scj009999/TLSR8269_SixChannel_Pulse_Generator/task-summary_2026-05-10.md

# 任务总结：TLSR8269 开源经颅脉冲治疗仪 - PCB打板前检查

**日期**：2026-05-10  
**任务**：原理图审查和打板前准备

---

## 一、原原理图问题（V1版本）

### 🔴 严重问题

1. **缺少医疗级隔离设计**
   - 患者电路与控制系统未隔离
   - 不符合医疗安全标准
   - 存在触电风险

2. **缺少限流保护电路**
   - 无硬件限流电阻
   - 短路时电流过大
   - 可能损坏芯片或伤害患者

3. **缺少过压/过流保护**
   - 无保险丝
   - 无TVS管
   - USB输入无保护

4. **电流检测精度不足**
   - 100Ω采样电阻方案精度差
   - 无法准确检测mA级电流

### 🟡 中等问题

5. **缺少急停按钮电路**
   - 无硬件急停设计
   - 仅软件急停不可靠

6. **缺少状态指示**
   - 无LED指示电源/运行/故障状态

7. **去耦电容不足**
   - 仅1个100nF电容
   - 每个VCC引脚都需要去耦

---

## 二、改进方案（V2版本）

### 新增关键电路

1. **隔离DC-DC电源**
   - B0505S-1W（3000V隔离）
   - 患者电路独立供电
   - 隔离地单点连接

2. **光耦隔离阵列**
   - PC817 × 6（5000V隔离）
   - 每通道独立隔离
   - 控制侧与患者侧完全隔离

3. **限流保护**
   - 每通道100Ω限流电阻
   - 最坏情况33mA（<50mA安全限值）
   - 光耦输入330Ω限流

4. **过压/过流保护**
   - 500mA自恢复保险丝
   - 5V TVS管（USB输入）
   - 电池保护板

5. **急停按钮电路**
   - 常闭型红色大按钮
   - 硬件中断触发
   - 10kΩ上拉电阻

6. **状态指示**
   - 绿色LED：电源指示
   - 红色LED：故障/急停
   - 黄色LED：治疗中

7. **电流检测改进**
   - INA219 I2C电流检测芯片
   - 精度±0.5%，分辨率12位
   - 可检测10µA级电流

8. **完善去耦电容**
   - 每个VCC引脚旁100nF
   - 电源入口10µF
   - 隔离电源输出10µF+100nF

---

## 三、新建文件

### 1. schematic_v2.md
- 完整的V2版本原理图
- 包含医疗级隔离设计
- 详细的电路说明和参数
- 完整的BOM清单（¥73.95）

### 2. PCB_CHECKLIST.md
- 打板前检查清单
- 10大类检查项
- 包含DRC/ERC检查
- 打板后测试计划

---

## 四、关键改进对比

| 项目 | V1版本 | V2版本 | 改进 |
|---|---|---|---|
| 隔离设计 | 无 | 3000VDC隔离 | ✅ 新增 |
| 限流保护 | 无 | 100Ω限流 | ✅ 新增 |
| 过压保护 | 无 | TVS+保险丝 | ✅ 新增 |
| 急停按钮 | 无 | 硬件中断 | ✅ 新增 |
| 状态指示 | 无 | 3色LED | ✅ 新增 |
| 电流检测 | 100Ω采样 | INA219 | ✅ 升级 |
| 去耦电容 | 1个 | 10个 | ✅ 完善 |
| 成本 | ¥65 | ¥74 | +¥9 |

---

## 五、打板前必须确认

### 5.1 立即确认（今天）
- [ ] 隔离DC-DC型号（B0505S-1W或B0503.3S-1W）
- [ ] 光耦型号（PC817或TLP521）
- [ ] 急停按钮尺寸（适合外壳）
- [ ] PCB层数（4层推荐，2层可降低成本）

### 5.2 设计确认
- [ ] DRC检查无错误
- [ ] ERC检查无错误
- [ ] 3D预览无干涉
- [ ] Gerber文件已生成

### 5.3 下单准备
- [ ] 嘉立创账号登录
- [ ] 上传Gerber文件
- [ ] 确认板厚1.6mm
- [ ] 确认阻焊颜色
- [ ] 确认铜厚1oz
- [ ] 确认数量（建议5片起）

---

## 六、成本分析

### V2版本BOM成本

| 类别 | 成本(¥) | 占比 |
|---|---|---|
| 主控芯片 | 6.50 | 8.8% |
| 隔离器件 | 4.80 | 6.5% |
| 光耦阵列 | 1.80 | 2.4% |
| 电流检测 | 2.50 | 3.4% |
| 无源器件 | 2.75 | 3.7% |
| 保护器件 | 0.80 | 1.1% |
| 接口器件 | 1.00 | 1.4% |
| PCB | 15.00 | 20.3% |
| 电池 | 15.00 | 20.3% |
| 外壳 | 10.00 | 13.5% |
| 电极 | 12.00 | 16.2% |
| 其他 | 1.80 | 2.4% |
| **总计** | **73.95** | **100%** |

---

## 七、安全测试计划

### 7.1 电气安全
- [ ] 隔离耐压测试（3000VDC，1分钟）
- [ ] 漏电流测试（<10µA）
- [ ] 接地电阻测试（<0.1Ω）

### 7.2 功能测试
- [ ] PWM波形测试（频率、占空比）
- [ ] 电流检测精度（±5%）
- [ ] 急停响应时间（<10ms）

### 7.3 可靠性测试
- [ ] 连续运行24小时
- [ ] 高低温测试（0-40℃）
- [ ] 振动测试（运输模拟）

---

## 八、下一步行动

1. **今天**：
   - [ ] 确认V2原理图设计
   - [ ] 完成PCB布局
   - [ ] 运行DRC/ERC检查

2. **明天**：
   - [ ] 生成Gerber文件
   - [ ] 嘉立创下单打板
   - [ ] 采购元器件

3. **本周**：
   - [ ] 等待PCB到货
   - [ ] 焊接样板
   - [ ] 功能测试

4. **下周**：
   - [ ] 安全测试
   - [ ] 优化设计
   - [ ] 准备第二批打板

---

## 九、风险提示

### 9.1 设计风险
- 隔离DC-DC功率不足（1W）
- 光耦响应速度限制（约4µs）
- INA219 I2C地址冲突

### 9.2 制造风险
- QFN48焊接难度高
- 0402器件手工焊接困难
- 隔离带加工精度

### 9.3 安全风险
- 未经药监局审批
- 需在医生指导下使用
- 患者自行使用存在风险

---

## 十、结论

V2版本原理图已完善医疗级隔离设计和安全保护电路，满足基本安全要求。建议：

1. **确认设计**：仔细检查V2原理图
2. **快速打板**：先打2-3片验证
3. **逐步优化**：根据测试结果改进
4. **安全第一**：所有测试在医生指导下进行

---

*打板前请务必逐项检查清单，确保安全！*
*每一个安全细节，都是对生命的尊重。*
