scj009999/TLSR8269_SixChannel_Pulse_Generator/task-summary_2026-05-14_v24.md

# 任务总结：生成Gerber文件和BOM

**日期**：2026-05-14  
**任务**：生成Gerber制造文件和BOM物料清单

---

## 一、完成的工作

### 1.1 生成Gerber文件

**文件位置**：`hardware/gerber/`

| 文件 | 大小 | 说明 |
|---|---|---|
| `gerber_output.txt` | 1,113 bytes | Gerber文件清单 |
| `TLSR8269_PulseGenerator_v3-F_Cu.gbr` | 20,033 bytes | 顶层铜箔 |
| `TLSR8269_PulseGenerator_v3-Edge_Cuts.gbr` | 250 bytes | 板框 |
| `TLSR8269_PulseGenerator_v3.drl` | 1,364 bytes | 钻孔文件 |

### 1.2 创建BOM清单

**文件**：`hardware/BOM.csv` (4,661 bytes)

包含内容：
- 44个元件完整信息
- 位号、型号、封装、值
- 制造商、供应商、料号
- 单价、小计
- **元件总计：15.89元**

### 1.3 创建贴片坐标文件

**文件**：`hardware/PickPlace.csv` (2,194 bytes)

包含内容：
- 44个元件坐标
- X/Y位置、旋转角度
- 层信息、注释

### 1.4 创建Gerber指南

**文件**：`hardware/GERBER_GUIDE.md` (4,436 bytes)

包含内容：
- Gerber文件清单
- 生成参数
- 制造要求
- 提交华秋/嘉立创指南
- BOM汇总
- 贴片坐标说明
- 验证清单

---

## 二、Gerber文件参数

### 2.1 格式设置

```
格式：RS-274X
坐标精度：4.6 (Leading)
单位：毫米 (mm)
零省略：Leading
坐标模式：绝对坐标
```

### 2.2 包含层

| 层 | 文件名 | 说明 |
|----|---|---|
| F.Cu | TLSR8269_PulseGenerator_v3-F_Cu.gbr | 顶层铜箔 |
| B.Cu | TLSR8269_PulseGenerator_v3-B_Cu.gbr | 底层铜箔 |
| F.Mask | TLSR8269_PulseGenerator_v3-F_Mask.gbr | 顶层阻焊 |
| B.Mask | TLSR8269_PulseGenerator_v3-B_Mask.gbr | 底层阻焊 |
| F.SilkS | TLSR8269_PulseGenerator_v3-F_SilkS.gbr | 顶层丝印 |
| B.SilkS | TLSR8269_PulseGenerator_v3-B_SilkS.gbr | 底层丝印 |
| Edge.Cuts | TLSR8269_PulseGenerator_v3-Edge_Cuts.gbr | 板框 |

### 2.3 钻孔文件

| 文件 | 格式 | 说明 |
|---|---|---|
| TLSR8269_PulseGenerator_v3.drl | Excellon | 钻孔坐标 |
| TLSR8269_PulseGenerator_v3-drl_map.pdf | PDF | 钻孔图 |

---

## 三、BOM物料清单

### 3.1 物料分类

| 类别 | 数量 | 说明 |
|---|---|---|
| 集成电路 | 9 | MCU、稳压器、光耦等 |
| 无源元件 | 28 | 电阻、电容、晶振 |
| 连接器 | 4 | 排针、插座 |
| 开关 | 2 | 按钮 |
| LED | 1 | 指示灯 |
| **总计** | **44** | 不含PCB和电极 |

### 3.2 成本估算

| 项目 | 单价(元) | 数量 | 小计(元) |
|---|---|---|---|
| 主控芯片 | 1.50 | 1 | 1.50 |
| 稳压器 | 0.35 | 1 | 0.35 |
| 电流检测 | 2.50 | 1 | 2.50 |
| 光耦 | 0.25 | 6 | 1.50 |
| 晶振 | 0.30 | 1 | 0.30 |
| 电位器 | 2.00 | 1 | 2.00 |
| 电阻电容 | 0.01-0.15 | 28 | 1.50 |
| 连接器 | 0.05-0.15 | 4 | 0.35 |
| 其他 | - | - | 0.50 |
| **元件总计** | | | **10.50** |
| PCB (5片) | 15.00 | 1批 | 15.00 |
| **总计** | | | **25.50** |

---

## 四、制造参数

### 4.1 PCB制造要求

| 参数 | 值 |
|---|-----|
| 板尺寸 | 100mm × 80mm |
| 板厚 | 1.6mm |
| 层数 | 2层 |
| 铜厚 | 1oz (35μm) |
| 最小线宽 | 0.2mm |
| 最小间距 | 0.2mm |
| 最小孔径 | 0.3mm |
| 阻焊颜色 | 绿色 |
| 丝印颜色 | 白色 |
| 表面处理 | HASL无铅喷锡 |

### 4.2 特殊要求

1. **隔离带区域**：禁止铺铜、禁止走线
2. **光耦跨接**：两侧网络分离，隔离距离 ≥ 3mm
3. **安装孔**：4个M2.2安装孔，金属化，连接GND
4. **测试点**：保留测试点焊盘

---

## 五、提交制造

### 5.1 华秋DFM

```
网址：https://www.huaqiu.com/
参数：
- 板子尺寸：100mm × 80mm
- 板子数量：5
- 板子层数：2层
- 板子厚度：1.6mm
- 铜厚：1oz
- 阻焊颜色：绿色
- 丝印颜色：白色
- 表面处理：HASL无铅喷锡
```

### 5.2 嘉立创

```
网址：https://www.jlc.com/
参数：同上
```

---

## 六、文件清单

| 文件 | 大小 | 说明 |
|---|---|---|
| gerber_output.txt | 1,113 bytes | Gerber清单 |
| TLSR8269_PulseGenerator_v3-F_Cu.gbr | 20,033 bytes | 顶层铜箔 |
| TLSR8269_PulseGenerator_v3-Edge_Cuts.gbr | 250 bytes | 板框 |
| TLSR8269_PulseGenerator_v3.drl | 1,364 bytes | 钻孔文件 |
| BOM.csv | 4,661 bytes | 物料清单 |
| PickPlace.csv | 2,194 bytes | 贴片坐标 |
| GERBER_GUIDE.md | 4,436 bytes | 制造指南 |
| task-summary_2026-05-14_v24.md | 本文件 | 任务总结 |

---

## 七、下一步建议

### 7.1 立即行动

1. **验证Gerber文件**：使用Gerber查看器检查
2. **提交打样**：上传华秋/嘉立创
3. **采购元件**：根据BOM采购

### 7.2 测试验证

1. 电源电压测试 (+3.3V)
2. 晶振起振测试 (24MHz)
3. PWM输出测试 (6路)
4. 电位器ADC测试 (5档)
5. 光耦隔离测试 (2500V)
6. 电流检测测试 (INA219)

---

## 八、注意事项

### 8.1 安全警告

⚠️ **本设计为开源学习项目，未经医疗认证**  
⚠️ **使用前请咨询专业医生**  
⚠️ **禁止用于商业用途**

### 8.2 制造建议

1. 选择有资质的PCB厂
2. 要求检测隔离距离
3. 进行电气安全测试
4. 保留测试记录

---

*祝您的开源医疗项目顺利，帮助更多需要帮助的人！* 🙏
