scj009999/TLSR8269_SixChannel_Pulse_Generator/task-summary_2026-05-23_v28.md

# 任务总结：创建LCD显示和按键驱动模块

**日期**：2026-05-23  
**任务**：创建LCD显示屏驱动、按键驱动、UI管理器，以及驱动开发指南

---

## 一、完成的工作

### 1.1 LCD显示驱动 (`lcd_driver.h/c`)

**文件大小**：3,603 + 12,349 = 15,952 bytes

**功能特性**：
- 支持SSD1306 OLED控制器，128x64分辨率
- I2C接口（400kHz），使用PB0/PB3
- 1KB显存，支持局部刷新
- 6x8和8x16 ASCII字库
- 基础绘图：点、线、矩形、圆形
- 文字显示：字符串、整数、浮点数
- 界面元素：标题栏、菜单项、进度条、通道状态

**API函数**：
| 函数 | 说明 |
|---|---|
| `lcd_init()` | 初始化LCD |
| `lcd_clear()` | 清屏 |
| `lcd_refresh()` | 刷新显示 |
| `lcd_draw_pixel()` | 画点 |
| `lcd_draw_line()` | 画线（Bresenham算法） |
| `lcd_draw_rect()` | 画矩形 |
| `lcd_fill_rect()` | 填充矩形 |
| `lcd_draw_circle()` | 画圆 |
| `lcd_draw_char()` | 显示字符 |
| `lcd_draw_string()` | 显示字符串 |
| `lcd_draw_number()` | 显示整数 |
| `lcd_draw_float()` | 显示浮点数 |
| `lcd_draw_title()` | 绘制标题栏 |
| `lcd_draw_menu_item()` | 绘制菜单项 |
| `lcd_draw_progress_bar()` | 绘制进度条 |
| `lcd_draw_channel_status()` | 绘制通道状态 |

### 1.2 按键驱动 (`button_driver.h/c`)

**文件大小**：3,488 + 11,059 = 14,547 bytes

**功能特性**：
- 支持最多8个按键
- 20ms消抖时间（可配置）
- 1秒长按检测（可配置）
- 300ms双击检测（可配置）
- 10ms扫描周期
- 状态机实现（空闲/消抖/按下/长按/释放）

**按键布局**：
| 按键 | 引脚 | 功能 |
|---|---|---|
| UP | PC0 (Pin 16) | 上 |
| DOWN | PC1 (Pin 17) | 下 |
| LEFT | PC2 (Pin 18) | 左 |
| RIGHT | PC3 (Pin 19) | 右 |
| OK | PC4 (Pin 20) | 确认 |
| CANCEL | PC5 (Pin 21) | 取消 |
| START | PD0 (Pin 24) | 启动 |
| STOP | PD1 (Pin 25) | 停止/急停 |

**事件类型**：
| 事件 | 触发条件 |
|---|---|
| `PRESS` | 消抖确认 |
| `RELEASE` | 按键松开 |
| `SHORT_PRESS` | 按下 < 1秒 |
| `LONG_PRESS` | 按下 > 1秒 |
| `DOUBLE_CLICK` | 300ms内两次按下 |
| `HOLD` | 持续按住，每500ms触发 |

### 1.3 UI管理器 (`ui_manager.h/c`)

**文件大小**：2,630 + 14,261 = 16,891 bytes

**功能特性**：
- 7种界面模式：主界面、菜单、通道编辑、方案选择、运行中、故障、设置
- 自动刷新（10fps限制）
- 按键事件自动分发
- 数据绑定（通道状态自动更新）
- 消息弹窗和警告显示

**界面模式**：
```
UI_MODE_MAIN         - 主界面，显示6通道概览
UI_MODE_MENU         - 主菜单（5个选项）
UI_MODE_CHANNEL_EDIT - 通道参数编辑
UI_MODE_SCHEME_SELECT- 方案选择（6个预设）
UI_MODE_RUNNING      - 治疗中，显示进度和时间
UI_MODE_FAULT        - 故障显示，错误码和提示
UI_MODE_SETTINGS     - 设置界面
```

**界面截图示例**：
```
+--------------------------+
|     Pulse Therapy        |  <- 标题栏
+--------------------------+
| Channels:                |
| CH0:10.0Hz  50% ████     |  <- 通道状态
| CH1:10.0Hz  50% ████     |
| CH2: OFF                 |
| CH3: OFF                 |
| CH4: OFF                 |
| CH5: OFF                 |
| [OK]Menu [Start]Run      |  <- 操作提示
+--------------------------+
```

### 1.4 驱动开发指南 (`DRIVER_GUIDE.md`)

**文件大小**：6,696 bytes

**内容**：
- 驱动模块清单（9个模块，3个已完成）
- LCD驱动详细说明和使用示例
- 按键驱动详细说明和使用示例
- UI管理器详细说明和界面截图
- 待实现驱动接口定义（I2C、PWM、ADC、UART、BLE、定时器）
- 驱动依赖关系图
- 下一步开发计划

---

## 二、文件清单

| 文件 | 大小 | 说明 |
|---|---|---|
| `firmware/lcd_driver.h` | 3,603 bytes | LCD驱动头文件 |
| `firmware/lcd_driver.c` | 12,349 bytes | LCD驱动实现 |
| `firmware/button_driver.h` | 3,488 bytes | 按键驱动头文件 |
| `firmware/button_driver.c` | 11,059 bytes | 按键驱动实现 |
| `firmware/ui_manager.h` | 2,630 bytes | UI管理器头文件 |
| `firmware/ui_manager.c` | 14,261 bytes | UI管理器实现 |
| `firmware/DRIVER_GUIDE.md` | 6,696 bytes | 驱动开发指南 |
| `task-summary_2026-05-23_v28.md` | 4,800 bytes | 本文件 |

---

## 三、待实现驱动模块

### 优先级1（必须）
| 模块 | 说明 | 依赖 |
|---|---|---|
| `i2c_driver` | I2C通信 | LCD、INA219 |
| `pwm_driver` | PWM输出 | 核心治疗功能 |
| `adc_driver` | ADC采样 | 阻抗/电流检测 |

### 优先级2（重要）
| 模块 | 说明 | 依赖 |
|---|---|---|
| `uart_driver` | UART通信 | 调试日志 |
| `timer_driver` | 定时器 | 系统时钟 |

### 优先级3（可选）
| 模块 | 说明 | 依赖 |
|---|---|---|
| `ble_driver` | BLE蓝牙 | 无线通信 |
| `flash_driver` | Flash存储 | 参数保存 |

---

## 四、驱动依赖关系

```
ui_manager.c
    ├── lcd_driver.c
    │       └── i2c_driver.c (待实现)
    ├── button_driver.c
    │       └── timer_driver.c (待实现)
    └── main_master.c
            ├── ble_driver.c (待实现)
            ├── pwm_driver.c (待实现)
            ├── adc_driver.c (待实现)
            └── uart_driver.c (待实现)
```

---

## 五、下一步建议

### 立即行动
1. **实现I2C驱动** — LCD和INA219都需要
2. **实现PWM驱动** — 核心治疗功能
3. **实现ADC驱动** — 安全检测必须

### 测试验证
1. LCD显示测试
2. 按键响应测试
3. UI界面切换测试
4. 菜单导航测试

### 硬件准备
1. SSD1306 OLED模块（128x64，I2C接口）
2. 8个轻触开关（按键）
3. 上拉电阻（10kΩ × 8）

---

*驱动开发需参考TLSR8269官方SDK和Datasheet*
