scj009999/TLSR8269_SixChannel_Pulse_Generator/task-summary_2026-05-24_v31.md

# 任务总结：执行待办列表 - timer/uart/flash驱动 + 编译环境

**日期**：2026-05-24  
**任务**：完成timer_driver、uart_driver、flash_driver，搭建编译环境

---

## 一、完成的工作

### 1.1 timer_driver（定时器驱动）

**文件**：`timer_driver.h` (3,096 bytes) + `timer_driver.c` (11,122 bytes) = **14,218 bytes**

**功能**：
- 系统Tick定时器（1ms中断）
- 微秒/毫秒延时（阻塞和非阻塞）
- 看门狗定时器（可配置超时）
- 通用定时器（Timer1/Timer2）
- 超时检查函数

**关键API**：
```c
timer_init()                    // 初始化
timer_start_tick(callback)      // 启动1ms Tick
timer_get_tick_ms()             // 获取毫秒计数
timer_delay_ms(ms)              // 毫秒延时
timer_watchdog_init(timeout)    // 初始化看门狗
timer_watchdog_feed()           // 喂狗
```

### 1.2 uart_driver（串口驱动）

**文件**：`uart_driver.h` (6,047 bytes) + `uart_driver.c` (20,000 bytes) = **26,047 bytes**

**功能**：
- UART0/UART1双通道
- 可配置波特率（默认115200）
- 发送/接收缓冲区
- printf格式化输出
- 日志系统（5级日志）
- 调试命令系统（help/status/pwm/adc/therapy）

**关键API**：
```c
uart_init_default(UART_0)       // 初始化
uart_send_string(UART_0, "msg") // 发送字符串
uart_printf(UART_0, "fmt", ...) // 格式化输出
log_init(LOG_LEVEL_DEBUG)       // 初始化日志
LOG_I("TAG", "message")         // 信息日志
```

**调试命令**：
```
help              - 显示帮助
status            - 系统状态
pwm 0 10.0 5000   - 设置PWM
adc 2             - 读取ADC
therapy start     - 开始治疗
```

### 1.3 flash_driver（Flash存储驱动）

**文件**：`flash_driver.h` (4,871 bytes) + `flash_driver.c` (11,563 bytes) = **16,434 bytes**

**功能**：
- Flash读写（基于页）
- 扇区擦除
- 配置参数持久化（魔数+CRC校验）
- 治疗日志记录
- 默认配置恢复

**配置结构体**：
```c
typedef struct {
    uint32_t magic;             // 'TPHY'
    float default_freq_hz;      // 默认频率
    uint16_t default_duty;      // 默认占空比
    uint16_t current_limit_ma;  // 电流限制
    uint32_t total_sessions;    // 总治疗次数
    uint16_t crc16;             // CRC校验
} Flash_ConfigTypeDef;
```

### 1.4 编译环境

**文件**：`BUILD_GUIDE.md` (6,480 bytes) + `Makefile` (3,749 bytes)

**内容**：
- Telink SDK安装指南
- 工具链配置
- 编译步骤（make/make clean/make flash）
- 烧录方法（BDT工具）
- 调试方法（UART日志）
- 故障排除

---

## 二、项目状态更新

### 2.1 驱动完成度

| 驱动 | 状态 | 大小 |
|---|---|---|
| timer_driver | ✅ 完成 | 14,218 bytes |
| uart_driver | ✅ 完成 | 26,047 bytes |
| flash_driver | ✅ 完成 | 16,434 bytes |
| i2c_driver | ✅ 完成 | 17,921 bytes |
| pwm_driver | ✅ 完成 | 24,393 bytes |
| adc_driver | ✅ 完成 | 24,451 bytes |
| lcd_driver | ✅ 完成 | ~15,000 bytes |
| button_driver | ✅ 完成 | ~12,000 bytes |
| ui_manager | ✅ 完成 | ~14,000 bytes |
| self_check | ✅ 完成 | ~16,000 bytes |
| **合计** | **10个驱动** | **~180,000 bytes** |

### 2.2 待办列表状态

**高优先级**：
- [x] timer_driver实现
- [x] uart_driver实现
- [x] flash_driver实现
- [x] 看门狗实现
- [ ] 编译验证（需实际环境）
- [ ] PCB打样

**中优先级**：
- [ ] 3D外壳设计
- [ ] 电源保险丝

**低优先级**：
- [ ] BLE通信
- [ ] 手机APP

---

## 三、关键文件清单

### 新增文件

| 文件 | 大小 | 说明 |
|---|---|---|
| `timer_driver.h` | 3,096 bytes | 定时器头文件 |
| `timer_driver.c` | 11,122 bytes | 定时器实现 |
| `uart_driver.h` | 6,047 bytes | UART头文件 |
| `uart_driver.c` | 20,000 bytes | UART实现 |
| `flash_driver.h` | 4,871 bytes | Flash头文件 |
| `flash_driver.c` | 11,563 bytes | Flash实现 |
| `BUILD_GUIDE.md` | 6,480 bytes | 编译指南 |
| `Makefile` | 3,749 bytes | 编译脚本 |

### 更新文件

| 文件 | 修改内容 |
|---|---|
| `INTEGRATION_GUIDE.md` | 更新驱动状态为已完成 |

---

## 四、下一步行动

### 立即行动
1. **搭建编译环境**
   - 下载Telink SDK
   - 安装tc32工具链
   - 验证编译

2. **硬件准备**
   - 采购元器件（OLED、INA219、电位器）
   - PCB打样（嘉立创/华秋）
   - 焊接样板

### 本周目标
3. **基础测试**
   - 上电测试
   - 自检测试
   - PWM/ADC验证

4. **安全测试**
   - 急停响应
   - 过流保护
   - 阻抗检测

---

*所有核心驱动已完成*
*项目进入编译验证和硬件制作阶段*
