scj009999/TLSR8269_SixChannel_Pulse_Generator/task-summary_2026-05-07.md

# 任务总结：TLSR8269 六路脉冲发生器

## 任务目标
为 Mixly 项目设计一个基于 TLSR8269 芯片的六路脉冲发生器，使用6个模拟数字信号端口作为脉冲输出。

## 完成内容

### 1. 核心代码 (main.c)
- 基于 Telink TLSR8269 SDK 的六路PWM脉冲发生器
- 使用 PA0-PA5 作为六路PWM输出通道 (PWM0-PWM5)
- 支持独立配置每路通道的频率、占空比和相位
- 提供使能/禁止控制接口
- 包含演示代码（不同频率、不同占空比、呼吸灯效果）

### 2. 配置文件 (app_config.h)
- 系统时钟配置 (16MHz)
- 禁用BLE和低功耗模式（与PWM冲突）
- PWM默认参数配置
- GPIO引脚复用说明表

### 3. 硬件原理图 (hardware/schematic.md)
- 系统框图
- 芯片引脚定义和连接图
- 电源电路（LDO 3.3V）
- 晶振电路（24MHz）
- 复位电路
- 烧录接口（SWS单线调试）
- 脉冲输出接口定义
- PCB布局建议
- BOM物料清单

### 4. 串口控制示例 (examples/uart_control.c)
- 通过串口命令动态控制六路脉冲
- 支持命令：FREQ, DUTY, PHASE, ENABLE, DISABLE, CONFIG, DEMO1, DEMO2, STOP, START, STATUS
- 波特率：115200
- 实时参数查询功能

### 5. 构建文件 (Makefile)
- 基于 Telink SDK 的编译配置
- 支持 TC32 工具链
- 编译、链接、生成二进制文件规则

### 6. 项目文档 (README.md)
- 项目概述和功能特性
- 引脚定义图
- 软件架构说明
- 使用示例代码
- 编译烧录步骤
- 频率精度对照表

## 技术要点

### TLSR8269 芯片特性
- 32位MCU，最高48MHz主频
- 6通道硬件PWM (PWM0-PWM5)
- 512KB Flash，32KB SRAM
- 丰富的GPIO接口 (PA, PB, PC, PD, PE, PF)
- 支持BLE 5.0 / Zigbee / 2.4G多协议

### PWM配置
- PWM时钟：16MHz（系统时钟）
- 频率范围：1Hz ~ 8MHz
- 占空比精度：0.01%（10000级）
- Cycle值范围：1 ~ 65535（16位）

### 引脚映射
| 通道 | GPIO | PWM功能 |
|---|---|---|
| CH0  | PA0  | PWM0 |
| CH1  | PA1  | PWM1 |
| CH2  | PA2  | PWM2 |
| CH3  | PA3  | PWM3 |
| CH4  | PA4  | PWM4 |
| CH5  | PA5  | PWM5 |

## 使用场景
- 电机控制（多路PWM驱动）
- LED调光（多路独立控制）
- 信号发生器（多路不同频率波形）
- 传感器激励信号
- 教学实验（Mixly图形化编程）

## 注意事项
1. PWM与低功耗模式冲突，使用时必须禁用PM
2. 同一PWM通道不能同时在多个引脚输出
3. 输出驱动能力约8mA/引脚，大功率负载需外接驱动
4. 首次烧录需要Telink专用烧录器（SWS接口）

## 文件清单
```
TLSR8269_SixChannel_Pulse_Generator/
├── main.c                    # 主程序
├── app_config.h              # 应用配置
├── Makefile                  # 构建脚本
├── README.md                 # 项目文档
├── hardware/
│   └── schematic.md          # 硬件原理图
└── examples/
    └── uart_control.c        # 串口控制示例
```

## 后续扩展建议
- 添加ADC采样实现闭环控制
- 实现脉冲计数和触发功能
- 添加蓝牙/WiFi远程控制
- 支持Mixly图形化积木块
