scj009999/TLSR8269_SixChannel_Pulse_Generator/task-summary_2026-05-07_final.md

# 任务总结：TLSR8269 开源经颅脉冲治疗仪

## 项目背景

为帕金森叠加综合症患者设计低成本开源治疗设备。患者自39岁确诊，今年3月北京昌平实验室刘河生教授发表重要论文后，发现市场上出现大量仿制设备（售价1-3万元，医院年费15万+），决定发起开源项目，目标让普通百姓负担得起。

## 完成内容

### 1. 核心硬件代码
- `main.c` - 六路PWM脉冲发生器，基于TLSR8269
- `app_config.h` - 芯片配置和安全参数
- `Makefile` - 编译脚本

### 2. 硬件设计文档
- `hardware/schematic.md` - 完整原理图、BOM、PCB布局建议
- 成本优化至 **¥65元** 物料成本

### 3. 软件生态
- `mixly_blocks/blocks.js` - Mixly图形化积木块定义
- `mixly_blocks/generator.js` - 积木块到C代码的生成器
- 支持非专业人士编程

### 4. 医疗安全设计
- `docs/MEDICAL_SAFETY.md` - 完整安全规范
  - 电气隔离（光耦PC817）
  - 电流限制（最大5mA）
  - 硬件急停
  - 看门狗保护
  - 自检程序

### 5. 开源合规文档
- `docs/OPEN_SOURCE_LETTER.md` - 给国家药监局的信
- `docs/COST_ANALYSIS.md` - 成本分析（开源¥99 vs 商用¥30000）
- `LICENSE` - GPL v3 + CERN OHL v2

### 6. 串口控制示例
- `examples/uart_control.c` - 命令行控制接口

## 关键技术参数

| 参数 | 数值 | 说明 |
|---|---|---|
| 主控芯片 | TLSR8269F512 | 国产，¥6.5 |
| PWM通道 | 6路 | PA0-PA5 |
| 频率范围 | 1Hz-8MHz | 16MHz时钟 |
| 占空比精度 | 0.01% | 10000级 |
| 输出隔离 | 5000V | PC817光耦 |
| 电流限制 | 5mA | 硬件保护 |
| 物料成本 | ¥65 | 全套BOM |
| 目标售价 | ¥99 | 含合理利润 |

## 与商用设备对比

| 项目 | 商用设备 | 开源方案 | 节省 |
|---|---|---|---|
| 设备价格 | ¥15,000-30,000 | ¥99 | **99.7%** |
| 医院年费 | ¥150,000 | ¥0 | **100%** |
| 3年总费用 | ¥450,000+ | ¥250 | **99.94%** |
| 透明度 | 黑盒 | 完全开源 | - |
| 可定制 | 否 | 是 | - |

## 后续行动

1. **技术完善**
   - [ ] PCB Layout设计
   - [ ] 原型机制作测试
   - [ ] 电气安全认证测试

2. **监管合规**
   - [ ] 向药监局提交申请
   - [ ] 准备临床试验数据
   - [ ] 申请创新医疗器械审批

3. **社区建设**
   - [ ] 建立GitHub仓库
   - [ ] 编写完整文档
   - [ ] 组建患者互助群

4. **生产准备**
   - [ ] 寻找代工厂
   - [ ] 建立供应链
   - [ ] 制定质量标准

## 项目意义

这不是一个商业项目，而是一场**医疗公平的革命**。

- 让15万/年的治疗变成99元/台
- 让黑盒设备变成完全透明
- 让患者从被动接受变成主动参与
- 让垄断暴利变成开源共享

**每一个帕金森患者，无论贫富，都应该有权利获得有效的治疗。**

---

*项目完全开源，不收取任何形式的费用*
*采用 GPL v3 + CERN OHL v2 许可证*
