scj009999/TLSR8269_SixChannel_Pulse_Generator/docs/使用手册.md

# 使用手册

**版本：** v1.0  
**日期：** 2026年5月26日  
**注意：** 非医疗设备，仅供研究学习

---

## 一、使用前必读

### ⚠️ 重要警告

1. **本项目不是医疗设备**
   - 未经药监局审批
   - 不能替代正规治疗
   - 不能替代药物使用

2. **使用风险自负**
   - 自行制作设备有风险
   - 自行使用设备有风险
   - 所有后果自行承担

3. **必须就医**
   - 任何健康问题咨询医生
   - 不要自行诊断
   - 不要自行治疗

### 🚨 禁忌症

**以下人群禁止使用：**
- ❌ 心脏起搏器患者
- ❌ 癫痫患者
- ❌ 头部有伤口或感染
- ❌ 孕妇
- ❌ 12岁以下儿童
- ❌ 对电流敏感者

**以下情况禁止使用：**
- ❌ 饮酒后
- ❌ 疲劳时
- ❌ 独自一人在家时
- ❌ 驾驶或操作机械时

---

## 二、设备介绍

### 2.1 设备组成

| 部件 | 说明 |
|---|---|
| 主机 | 包含电路板、电池、蓝牙 |
| 电极 | 连接头皮的导电贴片 |
| 充电线 | USB Type-C充电 |
| APP | 手机控制软件 |

### 2.2 技术参数

| 参数 | 数值 |
|---|---|
| 通道数 | 6路 |
| 频率范围 | 1-200 Hz |
| 电流范围 | 0-2 mA |
| 波形 | 方波/正弦波 |
| 持续时间 | 1-30 分钟 |
| 电池 | 3.7V锂电池 |
| 充电 | USB 5V |

### 2.3 安全保护

| 保护 | 说明 |
|---|---|
| 硬件限流 | 最大输出 < 5mA |
| 光耦隔离 | 5000V电气隔离 |
| 急停按钮 | 立即切断输出 |
| 看门狗 | 异常自动复位 |
| ADC监测 | 实时安全检查 |

---

## 三、使用前准备

### 3.1 环境准备

- [ ] 安静舒适的环境
- [ ] 舒适的座椅或躺椅
- [ ] 手机安装APP
- [ ] 有人陪同（首次使用）

### 3.2 个人准备

- [ ] 清洁头皮（无油脂）
- [ ] 取下金属饰品
- [ ] 穿着舒适
- [ ] 排空膀胱

### 3.3 设备准备

- [ ] 检查电量（>50%）
- [ ] 检查电极完好
- [ ] 检查连接线
- [ ] 测试急停按钮

---

## 四、操作步骤

### 4.1 连接设备

```
1. 打开设备电源
2. 打开手机蓝牙
3. 打开APP
4. 搜索并连接设备
5. 等待连接成功提示
```

### 4.2 放置电极

**根据治疗模式选择位置：**

| 模式 | 位置 | 说明 |
|---|---|---|
| 运动改善 | 运动皮层 | 头顶偏后 |
| 睡眠改善 | 前额叶 | 额头两侧 |
| 认知改善 | 顶叶 | 头顶两侧 |

**放置步骤：**
```
1. 清洁皮肤
2. 撕开电极贴片
3. 贴在指定位置
4. 连接电极线
5. 确认连接牢固
```

### 4.3 设置参数

**首次使用建议参数：**

| 参数 | 建议值 |
|---|---|
| 频率 | 10 Hz |
| 电流 | 0.5 mA |
| 持续时间 | 10 分钟 |
| 波形 | 方波 |

**设置步骤：**
```
1. 选择治疗模式
2. 设置频率
3. 设置电流（从低开始）
4. 设置时间
5. 确认设置
```

### 4.4 开始治疗

```
1. 确认所有设置
2. 点击开始按钮
3. 感受电流刺激（轻微刺痛感）
4. 如不适，立即按急停
5. 治疗结束后，设备自动停止
```

### 4.5 结束治疗

```
1. 等待设备自动停止
2. 断开电极连接
3. 取下电极贴片
4. 清洁皮肤
5. 关闭设备电源
6. 记录使用日志
```

---

## 五、参数调整

### 5.1 频率选择

| 频率 | 效果 | 适用 |
|---|---|---|
| 1-5 Hz | 放松 | 睡眠 |
| 10-20 Hz | 运动改善 | 震颤 |
| 40-60 Hz | 认知改善 | 记忆力 |
| 100-200 Hz | 镇痛 | 疼痛 |

### 5.2 电流调整

**原则：**
- 从低开始（0.5mA）
- 逐步增加
- 感到明显刺激即可
- 不要超过2mA

### 5.3 时间控制

| 情况 | 时间 |
|---|---|
| 首次使用 | 5-10分钟 |
| 适应后 | 15-20分钟 |
| 最大时间 | 30分钟 |
| 每日次数 | 1-2次 |

---

## 六、使用日志

### 6.1 记录内容

| 项目 | 记录 |
|---|---|
| 日期时间 | 每次使用记录 |
| 使用参数 | 频率、电流、时间 |
| 身体感受 | 刺激感、舒适度 |
| 效果评估 | 症状改善情况 |
| 不良反应 | 任何不适 |

### 6.2 记录方式

**APP自动记录：**
- 使用时间
- 使用参数
- 设备状态

**手动记录：**
- 身体感受
- 效果评估
- 不良反应

### 6.3 记录示例

```
日期：2026-05-26
时间：上午10:00
参数：10Hz, 1.0mA, 20分钟
感受：轻微刺痛，可接受
效果：震颤略有减轻
不良反应：无
备注：下次尝试1.5mA
```

---

## 七、注意事项

### 7.1 使用中

- ✅ 保持放松
- ✅ 可以听音乐
- ✅ 可以闭目休息
- ❌ 不要操作机械
- ❌ 不要离开座位
- ❌ 不要调节参数（医生指导除外）

### 7.2 使用后

- ✅ 清洁皮肤
- ✅ 记录日志
- ✅ 观察身体反应
- ❌ 立即剧烈运动
- ❌ 立即洗澡
- ❌ 立即饮酒

### 7.3 长期注意

- ✅ 定期咨询医生
- ✅ 不要停用正规药物
- ✅ 不要替代正规治疗
- ❌ 不要过度使用
- ❌ 不要分享设备
- ❌ 不要自行改装

---

## 八、不良反应

### 8.1 常见反应（正常）

| 反应 | 说明 | 处理 |
|---|---|---|
| 轻微刺痛 | 电流刺激 | 正常，可接受 |
| 皮肤发红 | 电流作用 | 通常自行消退 |
| 轻微头晕 | 电流影响 | 降低电流或停止 |

### 8.2 不良反应（需停止）

| 反应 | 处理 |
|---|---|
| 头痛 | 立即停止，休息 |
| 恶心 | 立即停止，就医 |
| 皮肤过敏 | 停止，清洁皮肤 |
| 心悸 | 立即停止，就医 |
| 视力模糊 | 立即停止，就医 |
| 癫痫发作 | 立即停止，紧急就医 |

### 8.3 紧急情况

**立即停止使用并就医：**
- 严重头痛
- 胸闷气短
- 意识模糊
- 持续不适

---

## 九、维护保养

### 9.1 日常维护

- 清洁设备表面
- 检查电极完好
- 检查连接线
- 保持干燥

### 9.2 定期维护

- 每月检查电池
- 每季度检查电路
- 每年专业检测

### 9.3 存放要求

- 干燥环境
- 避免高温
- 避免潮湿
- 避免挤压

---

## 十、故障排除

### 10.1 设备问题

| 问题 | 可能原因 | 解决 |
|---|---|---|
| 无法开机 | 电池耗尽 | 充电 |
| 无法连接 | 蓝牙问题 | 重启设备 |
| 无输出 | 电极脱落 | 检查连接 |
| 电流不稳 | 接触不良 | 清洁电极 |

### 10.2 APP问题

| 问题 | 可能原因 | 解决 |
|---|---|---|
| 闪退 | 内存不足 | 重启手机 |
| 无法连接 | 蓝牙权限 | 检查权限 |
| 数据丢失 | 未同步 | 手动同步 |

### 10.3 无法解决

- 停止使用
- 联系技术支持
- 不要自行拆解

---

## 十一、法律责任

### 11.1 用户责任

使用本设备，表示您同意：
- 自行承担所有风险
- 不追究项目责任
- 不用于商业目的
- 遵守法律法规

### 11.2 项目声明

本项目：
- 不提供医疗建议
- 不保证任何效果
- 不承担任何责任
- 不收取任何费用

---

## 十二、获取帮助

### 12.1 技术问题

- GitHub Issues
- 技术论坛
- 社区讨论

### 12.2 医疗问题

- 咨询医生
- 不要依赖设备
- 正规治疗优先

### 12.3 紧急情况

- 立即就医
- 拨打急救电话
- 不要延误

---

> **最后提醒：**
> 
> 本手册仅供学习参考。
> 
> 使用设备风险自负。
> 
> 任何健康问题请咨询医生。

---

**版本：** v1.0  
**日期：** 2026年5月26日  
**维护：** 匿名技术志愿者团队
