scj009999/TLSR8269_SixChannel_Pulse_Generator/docs/制作指南.md

# 设备制作指南

**版本：** v1.0  
**日期：** 2026年5月26日  
**难度：** 中级（需基础电子技能）

---

## 一、制作前准备

### 1.1 技能要求

- [ ] 基础电子知识
- [ ] 焊接技能（SMD元件）
- [ ] 使用万用表
- [ ] 基本编程能力（烧录固件）

### 1.2 工具清单

| 工具 | 规格 | 用途 |
|---|---|---|
| 电烙铁 | 可调温，尖头 | 焊接 |
| 焊锡丝 | 0.5mm，无铅 | 焊接 |
| 助焊剂 | 膏状 | 辅助焊接 |
| 万用表 | 数字式 | 测试 |
| 编程器 | Telink专用 | 烧录固件 |
| 镊子 | 防静电 | 夹取元件 |
| 放大镜 | 5-10倍 | 检查焊点 |
| 热风枪 | 可选 | 拆焊 |

### 1.3 安全装备

| 装备 | 用途 |
|---|---|
| 防静电手环 | 防止静电损坏芯片 |
| 防护眼镜 | 保护眼睛 |
| 通风设备 | 排除焊锡烟雾 |
| 绝缘垫 | 防止短路 |

---

## 二、元器件采购

### 2.1 主控芯片

**TLSR8269F512**
- 供应商：Telink官网或授权代理商
- 价格：约15-20元
- 注意：确保正品

### 2.2 电源部分

| 元件 | 型号 | 数量 | 价格(约) |
|---|---|---|---|
| USB接口 | Type-C | 1 | 1元 |
| 稳压芯片 | AMS1117-3.3 | 1 | 0.5元 |
| 电容 | 10uF/16V | 2 | 0.2元 |
| 电容 | 100nF | 5 | 0.5元 |

### 2.3 输出部分（6路）

每路需要：

| 元件 | 型号 | 数量 | 价格(约) |
|---|---|---|---|
| 限流电阻 | 100Ω/0.25W | 1 | 0.1元 |
| 光耦 | PC817 | 1 | 0.5元 |
| 输出电容 | 1uF | 1 | 0.2元 |
| 电极接口 | 2.54mm插座 | 1 | 0.3元 |

6路总计：约15元

### 2.4 其他元件

| 元件 | 型号 | 数量 | 价格(约) |
|---|---|---|---|
| LED指示灯 | 3mm | 3 | 0.3元 |
| 按键 | 轻触开关 | 2 | 0.4元 |
| 晶振 | 24MHz | 1 | 1元 |
| 蓝牙天线 | 陶瓷天线 | 1 | 2元 |

### 2.5 总成本

| 项目 | 成本(约) |
|---|---|
| PCB制板 | 20-50元（5片） |
| 元器件 | 50-80元 |
| 外壳 | 10-20元 |
| **总计** | **80-150元/台** |

---

## 三、PCB制作

### 3.1 获取PCB文件

从项目仓库下载：
- `hardware/pcb_design.zip`
- 包含Gerber文件

### 3.2 制板方式

**方式1：嘉立创（推荐）**
- 网址：www.jlc.com
- 价格：5元/5片（10×10cm以内）
- 周期：3-5天

**方式2：其他厂家**
- 华秋电路
- 捷多邦
- 猎板网

### 3.3 制板参数

| 参数 | 设置 |
|---|---|
| 层数 | 2层 |
| 板厚 | 1.6mm |
| 铜厚 | 1oz |
| 最小线宽 | 6mil |
| 最小孔径 | 0.3mm |
| 表面处理 | 喷锡 |
| 阻焊颜色 | 绿色 |

---

## 四、焊接步骤

### 4.1 焊接顺序

```
1. 电源部分
2. 主控芯片
3. 晶振和复位电路
4. 光耦和输出电路
5. 蓝牙天线
6. 按键和LED
7. 电极接口
```

### 4.2 关键步骤

**步骤1：焊接主控芯片**

```
注意：
- 对齐引脚
- 先焊对角固定
- 逐个引脚焊接
- 检查短路
```

**步骤2：焊接光耦**

```
注意：
- 注意方向（有标记）
- 确保隔离距离
- 检查导通
```

**步骤3：焊接限流电阻**

```
注意：
- 阻值100Ω
- 功率0.25W以上
- 确保可靠连接
```

### 4.3 检查要点

| 检查项 | 方法 | 标准 |
|---|---|---|
| 短路 | 万用表蜂鸣档 | 无短路 |
| 开路 | 万用表电阻档 | 连接正常 |
| 极性 | 目视检查 | 方向正确 |
| 焊点 | 放大镜 | 饱满光亮 |

---

## 五、固件烧录

### 5.1 开发环境

**下载Telink SDK：**
- 网址：http://telink-semi.cn/
- 版本：TLSR8x5x

### 5.2 编译代码

```bash
# 克隆代码
git clone https://github.com/scj009999/TLSR8269_SixChannel_Pulse_Generator.git

# 进入目录
cd firmware

# 编译
make
```

### 5.3 烧录固件

**使用Telink烧录器：**

```
1. 连接烧录器到电脑
2. 连接烧录器到设备（SWD接口）
3. 打开烧录软件
4. 选择编译好的bin文件
5. 点击烧录
6. 等待完成
```

### 5.4 验证

```
1. 上电测试
2. 检查LED指示灯
3. 测试按键功能
4. 连接手机APP
5. 测试输出波形
```

---

## 六、测试步骤

### 6.1 安全测试

| 测试项 | 方法 | 标准 |
|---|---|---|
| 限流功能 | 示波器测量 | ≤5mA |
| 隔离电阻 | 万用表测量 | ≥500MΩ |
| 急停功能 | 按键测试 | 立即切断 |
| 过流保护 | 模拟短路 | 自动保护 |

### 6.2 功能测试

| 测试项 | 方法 | 标准 |
|---|---|---|
| PWM输出 | 示波器测量 | 频率准确 |
| 电流调节 | 万用表测量 | 线性可调 |
| 蓝牙连接 | 手机APP测试 | 稳定连接 |
| 参数保存 | 断电重启测试 | 保存正常 |

### 6.3 老化测试

```
连续运行72小时：
- 监测温度
- 监测电流
- 监测稳定性
- 记录异常情况
```

---

## 七、组装外壳

### 7.1 外壳选择

| 类型 | 优点 | 缺点 |
|---|---|---|
| 3D打印 | 定制化 | 强度一般 |
| 亚克力 | 透明美观 | 易碎 |
| 塑料盒 | 便宜易得 | 不够专业 |
| 金属盒 | 屏蔽性好 | 成本高 |

### 7.2 组装步骤

```
1. 固定PCB
2. 安装电极接口
3. 安装按键和LED
4. 安装电池（如使用）
5. 合上外壳
6. 贴标签
```

### 7.3 标签内容

```
开源经颅脉冲治疗仪
版本：v1.0
注意：非医疗设备，仅供研究
警告：使用风险自负
```

---

## 八、常见问题

### 8.1 焊接问题

| 问题 | 原因 | 解决 |
|---|---|---|
| 虚焊 | 温度不够 | 提高温度，加助焊剂 |
| 短路 | 焊锡过多 | 吸锡带清理 |
| 芯片损坏 | 静电/过热 | 防静电，控制温度 |

### 8.2 烧录问题

| 问题 | 原因 | 解决 |
|---|---|---|
| 无法连接 | 接线错误 | 检查SWD接口 |
| 烧录失败 | 芯片锁定 | 解锁后重试 |
| 程序不跑 | 晶振问题 | 检查晶振焊接 |

### 8.3 功能问题

| 问题 | 原因 | 解决 |
|---|---|---|
| 无输出 | 限流电阻开路 | 检查电阻 |
| 电流不准 | ADC校准问题 | 重新校准 |
| 蓝牙断开 | 天线问题 | 检查天线焊接 |

---

## 九、安全提醒

### ⚠️ 制作安全

```
- 使用防静电设备
- 注意烙铁温度
- 保持通风
- 避免烫伤
```

### ⚠️ 使用安全

```
- 必须在医生指导下使用
- 严格按照参数设置
- 注意皮肤清洁
- 观察身体反应
```

### ⚠️ 法律提醒

```
- 自制的设备不能销售
- 不能提供给他人使用
- 不能声称医疗效果
- 风险自负
```

---

## 十、进阶优化

### 10.1 硬件优化

- 增加显示屏
- 增加存储功能
- 增加多种波形
- 增加无线充电

### 10.2 软件优化

- 优化算法
- 增加模式
- 改善UI
- 增加数据分析

### 10.3 结构优化

- 设计专业外壳
- 优化散热
- 增加便携性
- 提高可靠性

---

## 十一、获取帮助

### 11.1 技术问题

- GitHub Issues
- 技术论坛
- 社区讨论

### 11.2 安全问题

- 立即停止使用
- 咨询专业人士
- 不要自行解决

### 11.3 医疗问题

- 咨询医生
- 不要依赖设备
- 正规治疗优先

---

> **重要提醒：**
> 
> 本指南仅供技术学习参考。
> 
> 制作和使用设备风险自负。
> 
> 任何健康问题请咨询医生。

---

**版本：** v1.0  
**日期：** 2026年5月26日  
**维护：** 匿名技术志愿者团队
