scj009999/TLSR8269_SixChannel_Pulse_Generator/docs/开源说明.md

# 开源经颅脉冲治疗仪 - 项目说明

**项目名称：** Open-Source Transcranial Pulse Stimulator (OS-TPS)  
**版本：** v1.0  
**日期：** 2026年5月26日  
**许可证：** GPL-3.0

---

## 一、项目简介

本项目是一个**纯粹的开源技术项目**，旨在分享经颅脉冲治疗的相关技术知识和设计文档。

**项目目标：**
- 促进医疗知识共享
- 降低技术门槛
- 推动研究交流
- 帮助患者了解治疗原理

**项目性质：**
- ✅ 技术开源
- ✅ 知识分享
- ✅ 研究交流
- ❌ 非商业销售
- ❌ 非医疗服务
- ❌ 非医疗建议

---

## 二、技术背景

本项目基于以下研究成果：

### 2.1 核心论文

**刘河生教授团队研究成果**  
发表于《自然》(Nature)，2026年2月5日

**主要发现：**
- 揭示帕金森病"躯体认知环路"机制
- 针对该网络进行干预，有效率55.5%
- 已获批3项国家医疗器械注册证
- 在全国60余家医院应用

### 2.2 技术原理

**经颅脉冲刺激 (TPS)：**
- 通过头皮电极施加微弱电流
- 调节大脑神经元活动
- 改善帕金森症状

**刺激参数：**
- 频率：1-200 Hz
- 电流：≤ 2 mA
- 波形：方波/正弦波
- 持续时间：1-30 分钟

---

## 三、硬件设计

### 3.1 主控芯片

**Telink TLSR8269F512**
- 32位RISC-V内核
- 512KB Flash
- 48KB SRAM
- 6路PWM输出
- BLE 4.2

### 3.2 电源设计

**输入：** USB 5V 或 锂电池 3.7V  
**输出：** 6路独立刺激通道

### 3.3 安全保护

| 保护措施 | 说明 | 参数 |
|---|---|---|
| 硬件限流 | 100Ω电阻 | 最大输出 < 5mA |
| 光耦隔离 | PC817 | 5000V隔离 |
| 急停按钮 | 硬件中断 | 立即切断输出 |
| 看门狗 | 定时器 | 1秒超时复位 |
| ADC监测 | 实时检测 | 每秒安全检查 |

---

## 四、软件设计

### 4.1 嵌入式软件

**功能：**
- PWM波形生成
- 参数实时监测
- 安全保护逻辑
- 蓝牙通信

**代码：**
- 语言：C
- 框架：Telink SDK
- 开源：完整代码已发布

### 4.2 移动端APP

**功能：**
- 设备连接
- 参数设置
- 状态监测
- 治疗记录

**技术：**
- React Native
- BLE通信
- 本地存储

### 4.3 后端服务

**功能：**
- 数据同步
- 用户管理
- 设备管理
- 日志记录

**技术：**
- Node.js
- PostgreSQL
- REST API

---

## 五、使用指南

### 5.1 制作设备

**所需技能：**
- 基础电子知识
- 焊接技能
- 软件烧录

**所需工具：**
- 电烙铁
- 万用表
- 编程器
- 电脑

**制作步骤：**
1. 采购元器件（见BOM清单）
2. 焊接PCB
3. 烧录固件
4. 测试功能
5. 安全检查

### 5.2 使用设备

**注意事项：**
- 必须在医生指导下使用
- 严格按照参数设置
- 注意皮肤清洁
- 观察身体反应

**禁忌症：**
- 心脏起搏器患者
- 癫痫患者
- 头部伤口
- 孕妇

---

## 六、安全警告

### ⚠️ 重要提醒

1. **本项目不是医疗设备**
   - 未经药监局审批
   - 不能替代正规治疗
   - 不能替代药物使用

2. **使用风险自负**
   - 自行制作设备有风险
   - 自行使用设备有风险
   - 所有后果自行承担

3. **必须就医**
   - 任何健康问题咨询医生
   - 不要自行诊断
   - 不要自行治疗

### 🚨 紧急情况

如出现以下情况，**立即停止使用并就医**：
- 头痛、头晕
- 恶心、呕吐
- 皮肤过敏
- 心悸、胸闷
- 任何不适

---

## 七、文件清单

### 7.1 硬件文档

| 文件 | 说明 |
|---|---|
| schematic.pdf | 原理图 |
| pcb_layout.pdf | PCB布局 |
| bom.xlsx | 元器件清单 |
| assembly_guide.md | 组装指南 |

### 7.2 软件文档

| 文件 | 说明 |
|---|---|
| firmware/ | 嵌入式代码 |
| app/ | 移动端APP |
| backend/ | 后端服务 |
| api_doc.md | API文档 |

### 7.3 技术文档

| 文件 | 说明 |
|---|---|
| safety_design.md | 安全设计 |
| risk_analysis.md | 风险分析 |
| test_report.md | 测试报告 |
| user_manual.md | 用户手册 |

---

## 八、社区交流

### 8.1 交流平台

- **GitHub Issues：** 技术讨论
- **知乎专栏：** 科普文章
- **患者论坛：** 经验交流

### 8.2 交流规则

- 尊重他人
- 保护隐私
- 理性讨论
- 禁止商业推广

### 8.3 贡献指南

欢迎贡献：
- 代码改进
- 文档完善
- 问题反馈
- 经验分享

---

## 九、许可证

本项目采用 **GPL-3.0** 开源许可证。

**您可以：**
- 自由使用
- 自由修改
- 自由分享
- 自由研究

**您必须：**
- 遵守GPL-3.0条款
- 注明来源
- 共享修改
- 不用于商业目的

**完整许可证文本：** 见 LICENSE 文件

---

## 十、联系方式

- **项目主页：** https://github.com/scj009999/TLSR8269_SixChannel_Pulse_Generator
- **技术交流：** GitHub Issues

**注意：**
- 不提供医疗咨询
- 不提供私人联系方式
- 不回应商业合作

---

## 十一、更新日志

### v1.0 (2026-05-26)
- 初始版本发布
- 完整硬件设计
- 完整软件代码
- 完整技术文档

---

## 十二、致谢

感谢以下贡献者：
- 刘河生教授团队（核心研究成果）
- 所有技术志愿者
- 所有患者测试者
- 所有社区贡献者

---

> **最后提醒：**
> 
> 本项目纯粹为技术开源，不构成任何医疗建议。
> 
> 任何健康问题，请务必咨询专业医生。
> 
> 自行使用本项目资料，风险自负。

---

**项目维护者：** 匿名技术志愿者团队  
**最后更新：** 2026年5月26日  
**版本：** v1.0
