scj009999/TLSR8269_SixChannel_Pulse_Generator/docs/TCM_NEURODEGENERATIVE_DISEASES.md

# 中医视角下的神经退行性疾病——理法方药与气功导引

> **作者**：cj（中医世家，开源医疗项目发起人）
> 
> **使命**：能帮一些人就帮一些人
> 
> **日期**：2026年5月

---

## 目录

1. [总论：脑为髓海，神机之主](#一总论)
2. [帕金森病（颤证）](#二帕金森病)
3. [老年痴呆（痴呆证）](#三老年痴呆)
4. [重症肌无力（痿证）](#四重症肌无力)
5. [渐冻人症（肌痿）](#五渐冻人症)
6. [气功导引法](#六气功导引法)
7. [经颅脉冲刺激的中医应用](#七经颅脉冲刺激)
8. [开源设备方案](#八开源设备方案)

---

## 一、总论

### 1.1 中医对脑的认识

《黄帝内经》云：
> **"脑为髓之海"**
> 
> **"头者，精明之府"**

**髓的生成**：
```
肾精 → 骨髓 → 脊髓 → 脑髓
         ↑
    脾胃运化水谷精微
```

**核心观点**：
- 脑髓由肾精所化
- 依赖脾胃运化的水谷精微充养
- 脑主神明，统帅全身

### 1.2 神经退行性疾病的共同病机

```
┌─────────────────────────────────────────┐
│         神经退行性疾病共同病机            │
├─────────────────────────────────────────┤
│                                         │
│   本虚（根本）                           │
│   ├─ 肾精亏虚 → 髓海不足                │
│   ├─ 气血不足 → 脑失所养                │
│   └─ 肝肾阴虚 → 筋脉失濡                │
│                                         │
│   标实（表象）                           │
│   ├─ 肝风内动 → 震颤、抽搐              │
│   ├─ 痰浊阻窍 → 神昏、痴呆              │
│   ├─ 瘀血阻络 → 肢体不用                │
│   └─ 湿热浸淫 → 肌肉痿软                │
│                                         │
│   病位：脑、肾、肝、脾                   │
│   病性：本虚标实，虚实夹杂               │
│                                         │
└─────────────────────────────────────────┘
```

### 1.3 治疗总则

> **"补肾填精、益气养血、化痰通络、平肝熄风"**

---

## 二、帕金森病（颤证）

### 2.1 病机

**《黄帝内经》**：
> **"诸风掉眩，皆属于肝"**
> 
> **"诸寒收引，皆属于肾"**

**《证治准绳》**：
> **"筋脉约束不住而莫能任持，风之象也"**

**病机层次**：
```
肾精亏虚 → 水不涵木 → 肝阳上亢 → 肝风内动 → 震颤
    ↑                                              ↓
脾胃虚损 → 气血不足 → 筋脉失养 ←──────────────────┘
```

### 2.2 辨证分型

| 证型 | 主症 | 治法 | 代表方 |
|---|---|---|---|
| **风阳内动** | 震颤剧烈，头晕耳鸣 | 镇肝熄风 | 镇肝熄风汤 |
| **痰热风动** | 震颤伴胸闷痰多 | 清热化痰 | 黄连温胆汤 |
| **气血亏虚** | 震颤无力，面色萎黄 | 大补气血 | 八珍汤 |
| **髓海不足** | 震颤伴健忘痴呆 | 补肾填精 | 地黄饮子 |
| **阳气虚衰** | 震颤伴畏寒肢冷 | 补肾温阳 | 右归丸 |

### 2.3 经颅脉冲刺激方案

| 频率 | 功效 | 穴位 | 对应症状 |
|---|---|---|---|
| 1-5Hz | 镇静安神 | 百会、神庭 | 焦虑失眠 |
| 10-20Hz | 平肝熄风 | 太阳、率谷 | 震颤 |
| 40-50Hz | 活血通络 | 风池、风府 | 僵直 |

---

## 三、老年痴呆（痴呆证）

### 3.1 病机

**《灵枢》**：
> **"髓海不足，则脑转耳鸣，胫酸眩冒，目无所见，懈怠安卧"**

**病机层次**：
```
肾精亏虚 → 髓海不足 → 脑失所养 → 神机失用 → 痴呆
    ↑                                              ↓
痰浊内生 → 阻蔽清窍 → 神明不清 ←──────────────────┘
```

### 3.2 辨证分型

| 证型 | 主症 | 治法 | 代表方 |
|---|---|---|---|
| **髓海不足** | 健忘痴呆，腰膝酸软 | 补肾填精 | 七福饮 |
| **气血不足** | 痴呆伴面色萎黄 | 益气养血 | 归脾汤 |
| **痰浊阻窍** | 痴呆伴胸闷痰多 | 化痰开窍 | 洗心汤 |
| **瘀血内阻** | 痴呆伴头痛固定 | 活血化瘀 | 通窍活血汤 |
| **肝阳上亢** | 痴呆伴头晕易怒 | 平肝潜阳 | 天麻钩藤饮 |

### 3.3 经颅脉冲刺激方案

| 频率 | 功效 | 穴位 | 对应症状 |
|---|---|---|---|
| 1-5Hz | 镇静安神 | 百会、四神聪 | 躁动不安 |
| 10-20Hz | 醒脑开窍 | 印堂、神庭 | 意识模糊 |
| 40-50Hz | 活血通络 | 风池、完骨 | 记忆力差 |

---

## 四、重症肌无力（痿证）

### 4.1 病机

**《素问》**：
> **"治痿者，独取阳明"**
> 
> **"阳明者，五脏六腑之海，主润宗筋"**

**病机层次**：
```
脾胃虚弱 → 气血生化乏源 → 筋脉失养 → 肌肉痿软
    ↑                                              ↓
肝肾亏虚 → 精血不足 → 筋骨失濡 ←──────────────────┘
```

### 4.2 辨证分型

| 证型 | 主症 | 治法 | 代表方 |
|---|---|---|---|
| **脾胃虚弱** | 眼睑下垂，四肢无力 | 健脾益气 | 补中益气汤 |
| **肝肾阴虚** | 痿软伴腰膝酸软 | 滋补肝肾 | 虎潜丸 |
| **气血两虚** | 痿软伴面色苍白 | 气血双补 | 八珍汤 |
| **湿热浸淫** | 痿软伴肢体困重 | 清热利湿 | 加味二妙散 |

### 4.3 经颅脉冲刺激方案

| 频率 | 功效 | 穴位 | 对应症状 |
|---|---|---|---|
| 10-20Hz | 健脾益气 | 足三里、阳陵泉 | 四肢无力 |
| 40-50Hz | 活血通络 | 合谷、曲池 | 肌肉萎缩 |

---

## 五、渐冻人症（肌痿）

### 5.1 病机

**病机特点**：
- 本病属于"痿证"范畴
- 病位在脑、脊髓、肌肉
- 病机为**脾肾亏虚，精血不足，筋脉失养**

**病机层次**：
```
先天不足 → 肾精亏虚 → 髓海不足 → 神机失用
    ↑                                              ↓
后天失养 → 脾胃虚弱 → 气血乏源 → 肌肉痿缩 ←─────┘
```

### 5.2 辨证分型

| 证型 | 主症 | 治法 | 代表方 |
|---|---|---|---|
| **脾肾两虚** | 肌肉萎缩，吞咽困难 | 健脾补肾 | 还少丹 |
| **肝肾阴虚** | 肌痿伴震颤 | 滋补肝肾 | 左归丸 |
| **气血两虚** | 肌痿伴呼吸困难 | 大补气血 | 十全大补汤 |
| **瘀血阻络** | 肌痿伴疼痛 | 活血化瘀 | 补阳还五汤 |

### 5.3 经颅脉冲刺激方案

| 频率 | 功效 | 穴位 | 对应症状 |
|---|---|---|---|
| 1-5Hz | 镇静安神 | 百会、神庭 | 焦虑抑郁 |
| 10-20Hz | 健脾益气 | 足三里、阳陵泉 | 肌肉无力 |
| 40-50Hz | 活血通络 | 合谷、曲池 | 肌肉萎缩 |

---

## 六、气功导引法

### 6.1 通用功法

#### 6.1.1 八段锦

**推荐动作**：

| 动作 | 功效 | 适用病症 |
|---|---|---|
| **两手托天理三焦** | 调理气机 | 所有脑病 |
| **左右开弓似射雕** | 舒展筋脉 | 帕金森、渐冻人 |
| **调理脾胃须单举** | 健脾益气 | 重症肌无力 |
| **五劳七伤往后瞧** | 舒缓颈肩 | 老年痴呆 |
| **摇头摆尾去心火** | 平肝熄风 | 帕金森 |
| **两手攀足固肾腰** | 补肾填精 | 所有脑病 |
| **攒拳怒目增气力** | 养肝明目 | 重症肌无力 |
| **背后七颠百病消** | 醒脑开窍 | 老年痴呆 |

#### 6.1.2 六字诀

**发音与脏腑对应**：

| 发音 | 脏腑 | 功效 | 适用病症 |
|---|---|---|---|
| **嘘** | 肝 | 平肝熄风 | 帕金森 |
| **呵** | 心 | 清心安神 | 老年痴呆 |
| **呼** | 脾 | 健脾益气 | 重症肌无力 |
| **呬** | 肺 | 补肺益气 | 渐冻人（呼吸肌） |
| **吹** | 肾 | 补肾填精 | 所有脑病 |
| **嘻** | 三焦 | 疏通气机 | 所有脑病 |

#### 6.1.3 太极拳

**功效**：
- 缓慢柔和，适合运动障碍患者
- 意念引导，调神醒脑
- 整体运动，疏通经络
- 呼吸配合，调理气机

### 6.2 专用功法

#### 6.2.1 帕金森病导引法

**步骤**：
1. **站桩**：双脚与肩同宽，膝盖微屈，意守丹田（5分钟）
2. **震颤放松**：自然站立，全身放松，让震颤自然发生（3分钟）
3. **缓慢运动**：缓慢抬手、抬腿，配合呼吸（10分钟）
4. **收功**：双手叠放于丹田，静养（2分钟）

**要点**：
- 动作越慢越好
- 意念跟随动作
- 呼吸自然深长

#### 6.2.2 老年痴呆健脑法

**步骤**：
1. **梳头**：十指梳头，从前额到后脑，36次
2. **鸣天鼓**：双手掩耳，食指弹击后脑，36次
3. **搓耳**：搓揉双耳，从上到下，36次
4. **叩齿**：上下牙齿轻叩，36次
5. **吞津**：舌抵上颚，待唾液满口后吞下，9次

**功效**：
- 醒脑开窍
- 补肾填精
- 延缓痴呆

#### 6.2.3 重症肌无力补气法

**步骤**：
1. **仰卧**：平躺，全身放松
2. **腹式呼吸**：吸气腹部隆起，呼气腹部凹陷（10分钟）
3. **意念引导**：吸气时意想清气入脾，呼气时意想浊气排出
4. **收功**：双手叠放于肚脐，静养（5分钟）

**功效**：
- 健脾益气
- 补益中气
- 增强肌力

#### 6.2.4 渐冻人症养护法

**步骤**：
1. **被动运动**：家属帮助活动四肢关节（10分钟）
2. **按摩**：按揉足三里、阳陵泉、合谷等穴位（10分钟）
3. **呼吸训练**：腹式呼吸，延长呼气时间（10分钟）
4. **心理调适**：静坐冥想，保持心态平和（10分钟）

**功效**：
- 延缓肌肉萎缩
- 改善呼吸功能
- 调节心理状态

---

## 七、经颅脉冲刺激的中医应用

### 7.1 理论基础

**中医外治法的现代延伸**：

| 中医外治法 | 作用 | 经颅脉冲刺激 |
|---|---|---|
| 针灸 | 疏通经络 | 脉冲电流刺激穴位 |
| 艾灸 | 温通经络 | 低频脉冲温热效应 |
| 推拿 | 舒筋活络 | 脉冲振动放松肌肉 |
| 导引 | 调神醒脑 | 调节脑电活动 |

### 7.2 穴位选择

#### 头部穴位

| 穴位 | 定位 | 功效 | 适用病症 |
|---|---|---|---|
| **百会** | 头顶正中 | 醒脑开窍 | 所有脑病 |
| **四神聪** | 百会前后左右各1寸 | 安神定志 | 老年痴呆 |
| **神庭** | 前额正中 | 清心安神 | 焦虑失眠 |
| **印堂** | 两眉中间 | 醒脑明目 | 老年痴呆 |
| **太阳** | 眉梢与外眼角之间 | 平肝熄风 | 帕金森 |
| **风池** | 枕骨下凹陷处 | 祛风散寒 | 所有脑病 |
| **风府** | 后发际正中直上1寸 | 祛风通络 | 帕金森 |
| **完骨** | 耳后乳突后下方 | 醒脑开窍 | 老年痴呆 |

#### 四肢穴位

| 穴位 | 定位 | 功效 | 适用病症 |
|---|---|---|---|
| **合谷** | 手背第1、2掌骨间 | 疏通经络 | 所有脑病 |
| **曲池** | 肘横纹外侧端 | 活血通络 | 渐冻人 |
| **足三里** | 膝下3寸 | 健脾益气 | 重症肌无力 |
| **阳陵泉** | 腓骨小头前下方 | 舒筋活络 | 帕金森 |
| **三阴交** | 内踝尖上3寸 | 滋补肝肾 | 所有脑病 |
| **太冲** | 足背第1、2跖骨间 | 平肝潜阳 | 帕金森 |

### 7.3 频率选择

| 频率 | 中医功效 | 现代机制 | 适用病症 |
|---|---|---|---|
| **1-5Hz** | 镇静安神 | 抑制神经元兴奋性 | 焦虑、失眠、躁动 |
| **10-20Hz** | 平肝熄风 | 调节神经递质平衡 | 震颤、抽搐 |
| **40-50Hz** | 活血通络 | 促进脑部血液循环 | 僵直、迟缓、痴呆 |

### 7.4 治疗方案

#### 帕金森病方案

```
刺激部位：头顶（百会、四神聪）+ 颞部（太阳、率谷）
频率：20Hz（平肝熄风）
时长：20分钟/次
疗程：每日1-2次，4周为一疗程
配合：针刺太冲、合谷 + 中药镇肝熄风汤
```

#### 老年痴呆方案

```
刺激部位：头顶（百会、四神聪）+ 额部（印堂、神庭）
频率：40Hz（活血通络）
时长：30分钟/次
疗程：每日1次，8周为一疗程
配合：针刺足三里、三阴交 + 中药七福饮
```

#### 重症肌无力方案

```
刺激部位：头部（百会）+ 四肢（足三里、阳陵泉）
频率：10Hz（健脾益气）
时长：20分钟/次
疗程：每日1次，12周为一疗程
配合：艾灸足三里 + 中药补中益气汤
```

#### 渐冻人症方案

```
刺激部位：头部（百会、风池）+ 四肢（合谷、曲池）
频率：10Hz（健脾益气）+ 40Hz（活血通络）交替
时长：30分钟/次
疗程：每日1次，长期治疗
配合：按摩 + 被动运动 + 中药还少丹
```

---

## 八、开源设备方案

### 8.1 硬件设计

基于TLSR8269的六路脉冲发生器：

| 参数 | 数值 |
|---|---|
| 主控芯片 | TLSR8269F512 |
| 输出通道 | 6路 |
| 频率范围 | 1Hz - 200Hz |
| 电流强度 | ≤2mA（安全） |
| 供电方式 | 锂电池 |
| 控制方式 | 蓝牙APP |

### 8.2 软件功能

- **预设方案**：帕金森、痴呆、肌无力、渐冻人
- **自定义**：频率、强度、时长可调
- **记录功能**：治疗日志、效果评估
- **安全保护**：过流、超时、脱落检测

### 8.3 成本

| 项目 | 费用 |
|---|---|
| 电子元器件 | ¥59 |
| 电极材料 | ¥116 |
| 外壳 | ¥95 |
| **总计** | **¥270** |
| **批量优化** | **<¥200** |

---

## 九、结语

> **"脑为髓海，神机之主"**
> 
> **"补肾填精、益气养血、化痰通络、平肝熄风"**

神经退行性疾病虽属难治，但中医有其独特优势：
- **整体观念**：调理全身，改善体质
- **辨证论治**：因人而异，精准治疗
- **多种手段**：中药、针灸、导引、脉冲刺激
- **治未病**：预防为主，延缓进展

**开源医疗设备 + 中医理论 + 气功导引 = 低成本、高效益的治疗方案**

---

## 十、参考文献

1. 黄帝内经·素问[M]. 北京：人民卫生出版社，2012.
2. 巢元方. 诸病源候论[M]. 北京：人民卫生出版社，2006.
3. 王肯堂. 证治准绳[M]. 北京：人民卫生出版社，2006.
4. 孙一奎. 赤水玄珠[M]. 北京：中国中医药出版社，2015.
5. 张伯礼，吴勉华. 中医内科学[M]. 第4版. 北京：中国中医药出版社，2017.
6. 王永炎. 中医脑病学[M]. 北京：人民卫生出版社，2007.

---

*本文完全开源，欢迎引用、转载、改进。*
*能帮一些人就帮一些人。*
*救一个人，胜造七级浮屠。*
