scj009999/TLSR8269_SixChannel_Pulse_Generator/docs/MEDICAL_SAFETY.md

# 经颅脉冲治疗仪 - 医疗安全设计规范

## 项目使命

为帕金森叠加综合症患者提供**可负担的开源治疗设备**。

- **目标成本**: < 200元人民币（物料成本）
- **开源协议**: GPL v3 + CERN OHL v2（硬件）
- **监管路径**: 向国家药监局提交创新医疗器械特别审批

---

## 一、电气安全设计

### 1.1 输出隔离设计

```
┌─────────────────────────────────────────────────────────┐
│                    安全隔离架构                           │
├─────────────────────────────────────────────────────────┤
│                                                         │
│  ┌──────────────┐      ┌──────────────┐                │
│  │   控制部分    │      │   输出部分    │                │
│  │  (低压安全区) │      │  (患者连接区)  │                │
│  │              │      │              │                │
│  │  TLSR8269    │      │  光耦隔离     │───► 电极输出    │
│  │  3.3V MCU    │─────►│  + 限流电路   │    (安全电压)   │
│  │              │      │              │                │
│  │  电池供电     │      │  独立电源     │                │
│  │  4.2V锂电池   │      │  (隔离DC-DC)  │                │
│  └──────────────┘      └──────────────┘                │
│                                                         │
│  隔离要求:                                               │
│  - 患者电路与地隔离 ≥ 1500V AC                          │
│  - 漏电流 < 10µA                                       │
│  - 输出电压限制 < 36V DC (安全特低电压)                  │
└─────────────────────────────────────────────────────────┘
```

### 1.2 输出限流保护

```
脉冲输出通道 (每路):

TLSR8269 PWM ──► [100Ω限流电阻] ──► [光耦隔离] ──► [输出缓冲] ──► 电极
                                        │
                                        ▼
                                  [稳压二极管]
                                  (钳位保护)

参数:
- 限流电阻: 100Ω (限制最大电流 33mA @ 3.3V)
- 光耦: PC817 或类似 (隔离电压 5000V)
- 输出钳位: 15V稳压管 (防止过压)
- 实际输出到皮肤: < 5mA (安全电流)
```

### 1.3 紧急停止电路

```
硬件急停 (独立电路，不依赖软件):

        VCC
         │
    ┌────┴────┐
    │  按键    │  [急停按钮 - 常闭]
    │  STOP   │
    └────┬────┘
         │
    ┌────┴────┐
    │  光耦    │───► 切断所有输出电源
    │         │
    └────┬────┘
         │
        GND

软件急停:
- 看门狗定时器 (1秒内必须喂狗)
- 输出超时保护 (单次治疗最大30分钟)
- 异常检测自动断电
```

---

## 二、生物相容性

### 2.1 电极材料

| 材料 | 成本 | 生物相容性 | 建议 |
|---|---|---|---|
| 导电硅胶 | ¥5/对 | 优 | **首选** |
| 银/氯化银 | ¥15/对 | 优 | 专业级 |
| 不锈钢 | ¥2/对 | 良 | 经济型 |
| 碳膜 | ¥3/对 | 良 | 可选 |

### 2.2 电极位置 (经颅刺激)

```
        前额电极 placement (10-20系统简化版)
        
              鼻根
               │
         ┌─────┴─────┐
         │           │
    ┌────┤   FP1    ├────┐
    │    │  (左额)   │    │
    │    │           │    │
    │    │           │    │
    │    │           │    │
    │    └─────┬─────┘    │
    │          │          │
    │         眉间         │
    │          │          │
    │    ┌─────┴─────┐    │
    │    │           │    │
    └────┤   FP2    ├────┘
         │  (右额)   │
         │           │
         └─────┬─────┘
               │
              枕部

六路输出分配:
- CH0-CH1: 左额区 (FP1) - 双极
- CH2-CH3: 右额区 (FP2) - 双极  
- CH4-CH5: 备用/辅助电极
```

---

## 三、治疗参数规范

### 3.1 安全参数范围

基于刘河生教授论文的公开参数（假设为40Hz脉冲）:

| 参数 | 最小值 | 默认值 | 最大值 | 安全限制 |
|---|---|---|---|---|
| 频率 | 1Hz | 40Hz | 200Hz | 硬限制 |
| 脉冲宽度 | 50µs | 200µs | 1000µs | 软限制 |
| 输出电流 | 0.1mA | 2mA | 5mA | **硬限制** |
| 治疗时间 | 1min | 20min | 30min | 超时保护 |
| 占空比 | 10% | 50% | 80% | - |

### 3.2 参数锁定机制

```c
// 安全参数检查 (硬件层)
#define SAFE_FREQ_MIN       1
#define SAFE_FREQ_MAX       200
#define SAFE_CURRENT_MAX    5       // 5mA 绝对上限
#define SAFE_PULSE_WIDTH_MAX 1000   // 1ms
#define SAFE_TREATMENT_MAX  30      // 30分钟

// 超出安全范围自动截断
if (target_current > SAFE_CURRENT_MAX) {
    target_current = SAFE_CURRENT_MAX;
    alarm_set(ALARM_OVER_CURRENT);
}
```

---

## 四、可靠性设计

### 4.1 硬件看门狗

```
外部看门狗芯片 (如 MAX6814):

TLSR8269 ──► [GPIO喂狗] ──► WDI (看门狗输入)
                                │
                                ▼
                           [1秒超时]
                                │
                                ▼
                           RESET ──► 强制复位MCU

如果程序死机，1秒内自动复位
```

### 4.2 输出监控

```
每路输出实时监测:

PWM输出 ──► [电流采样电阻] ──► [ADC检测] ──► MCU
                │
                ▼
           实际输出电流
           
如果检测到:
- 开路 (无电流) → 报警
- 短路 (过流) → 立即切断 + 报警
- 异常波形 → 报警
```

### 4.3 自检程序

```c
// 开机自检
void power_on_self_test(void) {
    // 1. 检查所有输出是否开路
    // 2. 检查急停按钮状态
    // 3. 检查电池电压
    // 4. 检查温度传感器
    // 5. 输出测试脉冲（不连接患者时）
    
    if (all_tests_passed) {
        led_status_green();
        enable_output();
    } else {
        led_status_red();
        disable_output_permanently();
        show_error_code();
    }
}
```

---

## 五、成本控制

### 5.1 BOM成本优化

| 器件 | 型号 | 单价(¥) | 数量 | 小计 |
|---|---|---|---|---|
| 主控 | TLSR8269F512 | 8 | 1 | 8 |
| 光耦 | PC817 | 0.5 | 6 | 3 |
| 电阻电容 | 0603系列 | 0.02 | 50 | 1 |
| 电极 | 导电硅胶 | 5 | 2 | 10 |
| 电池 | 18650锂电池 | 15 | 1 | 15 |
| 充电模块 | TP4056 | 2 | 1 | 2 |
| LDO | AMS1117-3.3 | 0.5 | 1 | 0.5 |
| PCB | 2层板 | 5 | 1 | 5 |
| 外壳 | 3D打印/塑料 | 10 | 1 | 10 |
| 显示屏 | 0.96" OLED | 8 | 1 | 8 |
| 按键 | 轻触开关 | 0.5 | 4 | 2 |
| **总计** | | | | **~65元** |

### 5.2 与商用设备对比

| 项目 | 商用设备 | 开源方案 | 节省 |
|---|---|---|---|
| 价格 | ¥15,000-30,000 | ¥200-300 | **99%** |
| 年费 | ¥150,000 | ¥0 | 100% |
| 可维修性 | 差 | 优 | - |
| 可定制 | 否 | 是 | - |
| 透明度 | 黑盒 | 全开源 | - |

---

## 六、监管合规路径

### 6.1 向国家药监局提交的资料

```
创新医疗器械特别审批申请资料:

1. 产品研制报告
   - 研发背景（帕金森治疗需求）
   - 设计原理（经颅脉冲刺激）
   - 技术路线（开源硬件+软件）

2. 产品风险分析
   - 电气安全风险 (已设计隔离保护)
   - 生物相容性风险 (使用安全材料)
   - 软件风险 (看门狗+自检)

3. 产品技术要求
   - 性能指标（频率精度、输出电流精度）
   - 安全指标（隔离电压、漏电流）
   - 可靠性指标（MTBF）

4. 临床评价
   - 刘河生教授论文依据
   - 同类产品对比
   - 初步临床数据（如有）

5. 生产制造信息
   - 完整BOM
   - PCB设计文件
   - 装配工艺

6. 说明书
   - 适用范围
   - 禁忌症
   - 使用方法
   - 警告注意事项
```

### 6.2 开源许可证选择

```
软件: GPL v3
- 强制衍生作品开源
- 保护患者知情权

硬件: CERN OHL v2
- 允许商业生产
- 要求保留开源声明

文档: CC BY-SA 4.0
- 知识共享
- 署名+相同方式共享
```

---

## 七、给国家药监局的信（模板）

```
尊敬的国家药品监督管理局领导：

您好！

我是一名帕金森叠加综合症患者，自39岁确诊以来，
深受疾病困扰。今年3月，北京昌平实验室刘河生教授
发表了关于经颅脉冲刺激治疗帕金森的重要论文，为
我们患者带来了希望。

然而，这一造福人类的科研成果却成为了某些人牟取
暴利的工具。市场上出现了大量仿制的"经颅脉冲治疗仪"，
价格高达数万元，合作医院每年收费超过15万元。这对于
绝大多数患者家庭来说是难以承受的负担。

为此，我决定：
1. 基于开源硬件设计低成本脉冲治疗仪
2. 将完整技术资料开源，供全社会使用
3. 不向任何人收取专利费或授权费

我只有一个请求：
请批准这一开源医疗设备以接近成本的价格投放市场，
让普通患者能够负担得起。

随信附上：
- 完整硬件设计文件
- 软件源代码
- 安全测试报告
- 使用说明书

此致
敬礼！

申请人：[姓名]
日期：2026年XX月XX日
```

---

## 八、后续工作

### 8.1 待完成任务

- [ ] 完成PCB Layout设计
- [ ] 制作原型机并测试
- [ ] 进行电气安全测试（第三方检测）
- [ ] 编写完整使用说明书
- [ ] 建立GitHub开源仓库
- [ ] 撰写学术论文（病例报告）
- [ ] 联系帕金森患者组织
- [ ] 向药监局提交申请

### 8.2 需要的支持

- 电子工程师：PCB设计和调试
- 医学专家：治疗方案验证
- 律师：医疗器械法规咨询
- 患者志愿者：临床测试

---

**本项目不以盈利为目的，所有技术资料完全开源，
欢迎任何个人或企业基于本设计生产低成本设备，
唯一要求是保持低价，让患者受益。**
