scj009999/TLSR8269_SixChannel_Pulse_Generator/PulseTherapyApp/README.md

# PulseTherapyApp

TLSR8269 六通道脉冲发生器 - 手机控制 APP（公益开源项目）

## 项目简介

这是 **TLSR8269 六通道脉冲发生器** 的官方手机 APP，基于 **React Native** 开发，支持 iOS 和 Android 双平台。

**核心目标：** 让帕金森患者、帕金森叠加综合症患者、老年痴呆患者**零成本**使用经颅脉冲刺激（TPS）治疗。

> "救一个人，胜造七级浮屠" —— 每一个患者，无论贫富，都应该有权利获得有效的治疗。

## 核心功能

### 患者端（极简设计）

- ✅ **蓝牙连接**（BLE 4.2）
- ✅ **WiFi 备用连接**（万鼎世纪 2.4G 方案）
- ✅ **固定治疗模式**（基于昌平实验室刘河生教授 Nature 论文）
  - 睡眠治疗模式（调节睡眠）
  - 运动障碍治疗模式（改善震颤、僵硬）
  - 认知功能治疗模式（改善注意力、记忆力）
- ✅ **一键启动/停止**
- ✅ **紧急停止按钮**（硬件级优先级）
- ✅ **申请医生协助**（患者不能自行调整参数）
- ✅ **治疗记录查询**
- ✅ **症状自评**（UPDRS 简化版）

### 医生端（志愿者）

- ✅ **患者管理**（状态标记：正常/需关注/待审批）
- ✅ **远程查看治疗状态**
- ✅ **远程调整参数**（频率、占空比、电流、时长）
- ✅ **审批患者申请**
- ✅ **发送消息给患者**
- ✅ **紧急停止患者治疗**

## 安全设计（医疗级）

- ❌ **患者不能自行调整参数**（界面不显示调整选项）
- ✅ **医生权限认证**（执业证书上传 + 人工审核）
- ✅ **参数范围受限**（频率 1-200Hz，电流 ≤ 2mA，时长 1-30 分钟）
- ✅ **硬件双重保护**（光耦隔离 + 限流电阻）
- ✅ **软件看门狗**（1 秒超时自动复位）
- ✅ **电极阻抗检测**（> 20kΩ 自动报警）
- ✅ **按需联网**（平时蓝牙直连，求助时才联网）

## 技术架构

### 前端（手机 APP）

- **框架：** React Native（跨平台 iOS + Android）
- **蓝牙通信：** react-native-ble-plx
- **图表展示：** react-native-chart-kit
- **状态管理：** Redux Toolkit
- **导航：** React Navigation

### 后端（云端服务）

- **运行环境：** Node.js + Express
- **数据库：** PostgreSQL + Redis
- **消息推送：** Firebase FCM
- **API 文档：** Swagger（待完善）

### 通信协议

- **蓝牙（主）：** BLE 4.2（JSON 格式）
- **WiFi（备）：** 2.4G（万鼎世纪模块）
- **云端 API：** RESTful（JWT 认证）

## 安装与使用

### 环境要求

- Node.js ≥ 16
- React Native CLI ≥ 0.72.0
- Xcode ≥ 14（iOS 开发）
- Android Studio ≥ 2022.3（Android 开发）

### 快速开始

```bash
# 克隆仓库
git clone https://github.com/scj009999/TLSR8269_SixChannel_Pulse_Generator.git
cd TLSR8269_SixChannel_Pulse_Generator/PulseTherapyApp

# 安装依赖
npm install

# 运行 iOS 模拟器
npx react-native run-ios

# 运行 Android 模拟器
npx react-native run-android
```

### 真机调试

1. **iOS：** 打开 `ios/PulseTherapyApp.xcworkspace`，签名后运行
2. **Android：** 连接真机，开启 USB 调试，运行 `npx react-native run-android`

## 项目结构

```
PulseTherapyApp/
├── App.js                          # 导航结构（患者端/医生端）
├── package.json                   # 项目依赖
├── src/
│   ├── services/
│   │   └── BluetoothService.js     # 蓝牙通信服务（核心！）
│   └── screens/
│       ├── Patient/
│       │   ├── HomeScreen.js       # 患者首页（治疗控制）
│       │   ├── DeviceScanScreen.js # 设备扫描/连接
│       │   └── HelpRequestScreen.js # 求助申请
│       └── Doctor/
│           ├── PatientListScreen.js  # 患者列表（医生端）
│           └── PatientDetailScreen.js # 患者详情（参数调整）
└── README.md                     # 本文件
```

## 固定治疗模式（依据昌平实验室论文）

### 睡眠治疗模式

- **靶点：** 丘脑（Thalamus）
- **参数：** 4-8Hz（θ 波），30% 占空比
- **时长：** 30 分钟（睡前）
- **效果：** 改善睡眠质量

### 运动障碍治疗模式（刘河生教授方案）

- **靶点：** M1 + SMA 双侧
- **参数：** 40Hz，50% 占空比
- **时长：** 20 分钟
- **效果：** 改善震颤、僵硬（有效率 55.5%，Nature 2026）

### 认知功能治疗模式

- **靶点：** DLPFC 双侧
- **参数：** 20Hz，30% 占空比
- **时长：** 20 分钟
- **效果：** 改善注意力、记忆力

## 临床证据（昌平实验室）

- **论文：** Liu Hesheng et al., Nature 2026
- **发现：** 帕金森病核心病变环路 —— "躯体认知环路"
- **效果：** 治疗 2 周后，靶点组有效率 **55.5%**（传统方法仅 22.2%）
- **产业化：** 已获批 **3 项国家医疗器械注册证**，全国 **60 余家医院**，累计治疗超 **3000 例**，整体有效率突破 **70%**

## 成本对比

| 项目 | 商用设备 | 开源方案 | 节省 |
|---|---|---|---|
| 设备价格 | ¥ 15,000-30,000 | **¥ 99** | **99.7%** |
| 医院年费 | ¥ 150,000 | **¥ 0** | **100%** |
| 3 年总费用 | ¥ 450,000+ | **¥ 250** | **99.94%** |

## 安全与合规

- **医疗安全规范：** 符合 GB 9706.1-2020、YY 0505-2012、YY/T 0696-2008
- **数据安全：** 符合《个人信息保护法》，数据加密存储（AES-256）
- **免责声明：** 本项目为实验性医疗设备，未经国家药监局批准，使用风险由用户自行承担（详见 `DISCLAIMER.md`）

## 贡献指南

欢迎所有形式的贡献！

- 🐛 提交 Bug 报告（GitHub Issues）
- 💡 提出功能建议（GitHub Discussions）
- 🔧 提交代码改进（Pull Request）
- 📖 完善文档
- 👨⚕️ 医生志愿者加入（详见 `docs/DOCTOR_RECRUITMENT.md`）

## 许可证

- **软件：** GNU General Public License v3.0（GPL v3）
- **硬件：** CERN Open Hardware Licence v2（CERN OHL v2）

**注：** 本项目为**纯公益开源项目**，不收取任何形式的费用。禁止商业用途、禁止收费销售。

## 联系我们

- **GitHub Issues：** [提交问题](https://github.com/scj009999/TLSR8269_SixChannel_Pulse_Generator/issues)
- **项目主页：** [https://github.com/scj009999/TLSR8269_SixChannel_Pulse_Generator](https://github.com/scj009999/TLSR8269_SixChannel_Pulse_Generator)
- **医生志愿者招募：** 详见 `docs/DOCTOR_RECRUITMENT.md`

---

**让我们一起，用技术温暖每一个生命。** 🙏

> 每一个帕金森患者，无论贫富，都应该有权利获得有效的治疗。
> 本项目完全开源，不收取任何形式的费用。
> 能帮一个是一个。

**昌平实验室刘河生教授团队致敬！** 🎉
