scj009999/TLSR8269_SixChannel_Pulse_Generator/docs/MOBILE_APP_DESIGN.md

# 手机APP设计方案 - 医患交互系统

## 一、项目概述

### 1.1 目标
开发一款手机APP，连接开源经颅脉冲治疗仪，实现：
- 患者远程调整治疗参数
- 医生远程监控和指导
- 治疗数据记录和分析
- 患者社区互助

### 1.2 核心价值
| 功能 | 价值 |
|---|---|
| 远程调参 | 患者无需频繁去医院 |
| 医生监控 | 医生可实时了解治疗效果 |
| 数据记录 | 长期追踪治疗进展 |
| 社区互助 | 患者间经验分享 |

## 二、系统架构

```
┌─────────────────────────────────────────────────────────────┐
│                      云端服务器                              │
│  ┌──────────────┐  ┌──────────────┐  ┌──────────────┐      │
│  │   用户管理    │  │   数据存储    │  │   消息推送    │      │
│  └──────────────┘  └──────────────┘  └──────────────┘      │
│  ┌──────────────┐  ┌──────────────┐  ┌──────────────┐      │
│  │   医生后台    │  │   数据分析    │  │   安全审计    │      │
│  └──────────────┘  └──────────────┘  └──────────────┘      │
└─────────────────────────────────────────────────────────────┘
                              │
              ┌───────────────┼───────────────┐
              │               │               │
        ┌─────┴─────┐   ┌─────┴─────┐   ┌─────┴─────┐
        │  患者APP   │   │  医生APP   │   │  管理后台  │
        │  (Flutter) │   │  (Flutter) │   │  (Web)    │
        └─────┬─────┘   └─────┬─────┘   └───────────┘
              │               │
        ┌─────┴─────┐   ┌─────┴─────┐
        │  治疗设备   │   │  蓝牙连接   │
        │ TLSR8269  │◄──┤  BLE 4.2  │
        └───────────┘   └───────────┘
```

## 三、功能模块

### 3.1 患者端APP

#### 3.1.1 设备连接
```
┌─────────────────────────────┐
│      设备连接界面            │
├─────────────────────────────┤
│                             │
│  ┌─────────────────────┐   │
│  │   搜索附近设备...    │   │
│  │                     │   │
│  │  ○ 脉冲治疗仪-001   │   │
│  │  ○ 脉冲治疗仪-002   │   │
│  │  ○ 脉冲治疗仪-003   │   │
│  │                     │   │
│  └─────────────────────┘   │
│                             │
│  [刷新]  [手动输入ID]       │
│                             │
└─────────────────────────────┘
```

**功能**：
- 蓝牙扫描连接设备
- 设备绑定（首次使用）
- 连接状态显示
- 断线重连

#### 3.1.2 治疗控制
```
┌─────────────────────────────┐
│      治疗控制界面            │
├─────────────────────────────┤
│                             │
│  当前模式: 帕金森标准        │
│  剩余时间: 18:32            │
│                             │
│  通道状态:                   │
│  CH0 ████████░░ 80%  40Hz   │
│  CH1 ████████░░ 80%  40Hz   │
│  CH2 ░░░░░░░░░░  0%  关闭   │
│  CH3 ░░░░░░░░░░  0%  关闭   │
│  CH4 ░░░░░░░░░░  0%  关闭   │
│  CH5 ░░░░░░░░░░  0%  关闭   │
│                             │
│  [开始] [暂停] [停止]       │
│                             │
│  [调整参数] [切换模式]       │
│                             │
└─────────────────────────────┘
```

**功能**：
- 启动/暂停/停止治疗
- 实时显示通道状态
- 显示剩余时间
- 电流/阻抗监测

#### 3.1.3 参数调整
```
┌─────────────────────────────┐
│      参数调整界面            │
├─────────────────────────────┤
│                             │
│  频率: [====●====] 40Hz     │
│  范围: 1-200Hz              │
│                             │
│  占空比: [==●======] 30%    │
│  范围: 0-100%               │
│                             │
│  电流限制: [====●==] 2mA    │
│  范围: 0.1-5mA              │
│                             │
│  治疗时长: [====●==] 20min  │
│  范围: 1-30min              │
│                             │
│  ⚠️ 修改参数需医生确认      │
│                             │
│  [申请调整] [恢复默认]       │
│                             │
└─────────────────────────────┘
```

**安全机制**：
- 参数超出安全范围需医生确认
- 敏感参数修改需医生授权码
- 自动记录参数修改日志

#### 3.1.4 治疗记录
```
┌─────────────────────────────┐
│      治疗记录界面            │
├─────────────────────────────┤
│                             │
│  本月治疗统计                │
│  ┌─────────────────────┐   │
│  │    折线图/柱状图     │   │
│  │                     │   │
│  │  治疗次数: 12次      │   │
│  │  总时长: 240分钟     │   │
│  │  平均时长: 20分钟    │   │
│  └─────────────────────┘   │
│                             │
│  最近治疗:                  │
│  05-09 10:00  20min  完成  │
│  05-08 09:30  20min  完成  │
│  05-07 10:15  15min  暂停  │
│                             │
│  [查看详情] [导出数据]       │
│                             │
└─────────────────────────────┘
```

**功能**：
- 治疗历史记录
- 数据统计分析
- 趋势图表展示
- 数据导出（PDF/Excel）

#### 3.1.5 症状记录
```
┌─────────────────────────────┐
│      症状记录界面            │
├─────────────────────────────┤
│                             │
│  今日症状评分 (UPDRS)        │
│                             │
│  震颤: [====●====] 3/4      │
│  僵直: [===●=====] 2/4      │
│  运动迟缓: [====●====] 3/4  │
│  平衡: [==●======] 2/4      │
│                             │
│  整体感受:                  │
│  ○ 明显改善  ○ 轻微改善     │
│  ○ 无变化    ○ 有所恶化     │
│                             │
│  备注: _________________    │
│                             │
│  [保存] [查看历史]           │
│                             │
└─────────────────────────────┘
```

**功能**：
- 每日症状评分
- 照片/视频记录
- 语音备注
- 与医生共享

### 3.2 医生端APP

#### 3.2.1 患者管理
```
┌─────────────────────────────┐
│      患者管理界面            │
├─────────────────────────────┤
│                             │
│  我的患者 (12人)             │
│                             │
│  ┌─────────────────────┐   │
│  │ 🔴 张三 (需关注)     │   │
│  │    上次治疗: 2天前   │   │
│  │    症状评分: 恶化    │   │
│  ├─────────────────────┤   │
│  │ 🟢 李四 (正常)       │   │
│  │    上次治疗: 今天    │   │
│  │    症状评分: 改善    │   │
│  ├─────────────────────┤   │
│  │ 🟡 王五 (待审核)     │   │
│  │    参数调整申请      │   │
│  └─────────────────────┘   │
│                             │
│  [添加患者] [群发通知]       │
│                             │
└─────────────────────────────┘
```

**功能**：
- 患者列表管理
- 状态标记（正常/需关注/待审核）
- 搜索筛选
- 分组管理

#### 3.2.2 远程监控
```
┌─────────────────────────────┐
│      远程监控界面            │
├─────────────────────────────┤
│  患者: 张三                  │
│                             │
│  实时状态:                   │
│  ┌─────────────────────┐   │
│  │   治疗中              │   │
│  │   已用: 12min        │   │
│  │   剩余: 8min         │   │
│  │                     │   │
│  │   CH0: 40Hz, 50%    │   │
│  │   CH1: 40Hz, 50%    │   │
│  │   电流: 1.8mA        │   │
│  │   阻抗: 5.2kΩ        │   │
│  └─────────────────────┘   │
│                             │
│  [发送消息] [紧急停止]       │
│  [调整参数] [查看历史]       │
│                             │
└─────────────────────────────┘
```

**功能**：
- 实时查看患者治疗状态
- 远程发送指令
- 紧急停止（安全优先）
- 文字/语音沟通

#### 3.2.3 参数审批
```
┌─────────────────────────────┐
│      参数审批界面            │
├─────────────────────────────┤
│                             │
│  待审批申请 (3条)            │
│                             │
│  ┌─────────────────────┐   │
│  │ 患者: 张三           │   │
│  │ 申请时间: 05-09 10:30│   │
│  │                     │   │
│  │ 申请调整:            │   │
│  │ 频率: 40Hz → 60Hz   │   │
│  │ 占空比: 50% → 70%   │   │
│  │                     │   │
│  │ 申请理由:            │   │
│  │ "感觉效果不明显，     │   │
│  │  希望增加强度"       │   │
│  │                     │   │
│  │ [同意] [拒绝] [调整] │   │
│  └─────────────────────┘   │
│                             │
└─────────────────────────────┘
```

**功能**：
- 查看参数调整申请
- 批准/拒绝/修改
- 添加审批意见
- 记录审批历史

#### 3.2.4 数据分析
```
┌─────────────────────────────┐
│      数据分析界面            │
├─────────────────────────────┤
│                             │
│  患者: 张三                  │
│  时间范围: 近30天            │
│                             │
│  ┌─────────────────────┐   │
│  │    症状趋势图        │   │
│  │                     │   │
│  │  治疗频率 vs 症状评分 │   │
│  │                     │   │
│  │  相关系数: -0.72     │   │
│  │  (频率越高，症状越轻) │   │
│  └─────────────────────┘   │
│                             │
│  治疗建议:                  │
│  "建议维持当前参数，        │
│   可考虑增加治疗频率"       │
│                             │
│  [生成报告] [分享患者]       │
│                             │
└─────────────────────────────┘
```

**功能**：
- 治疗数据可视化
- 症状趋势分析
- 治疗效果评估
- 生成医疗报告

### 3.3 管理后台

#### 3.3.1 用户管理
- 患者注册审核
- 医生资质认证
- 权限管理
- 账号安全

#### 3.3.2 设备管理
- 设备注册
- 固件版本管理
- 远程升级
- 故障诊断

#### 3.3.3 数据安全
- 数据加密存储
- 访问日志审计
- 隐私保护合规
- 备份恢复

## 四、技术实现

### 4.1 技术栈

| 层级 | 技术 | 说明 |
|---|---|---|
| 前端 | Flutter | 跨平台(iOS/Android) |
| 后端 | Node.js + Express | RESTful API |
| 数据库 | PostgreSQL + Redis | 主库 + 缓存 |
| 消息队列 | RabbitMQ | 异步处理 |
| 蓝牙 | flutter_blue | BLE通信 |
| 推送 | Firebase FCM | 消息推送 |
| 图表 | fl_chart | 数据可视化 |

### 4.2 蓝牙通信协议

```
服务UUID: 0x180A (Device Information)
特征UUID: 0x2A50 (设备状态)
          0x2A51 (治疗控制)
          0x2A52 (参数配置)
          0x2A53 (实时数据)

数据格式 (JSON):
{
  "cmd": "start",
  "params": {
    "mode": "parkinson_std",
    "duration": 20,
    "channels": [
      {"ch": 0, "freq": 40, "duty": 50},
      {"ch": 1, "freq": 40, "duty": 50}
    ]
  }
}

响应格式:
{
  "status": "ok",
  "data": {
    "elapsed": 120,
    "remaining": 1080,
    "current": 1800,
    "impedance": 5200
  }
}
```

### 4.3 API设计

```
POST   /api/v1/auth/login          # 登录
POST   /api/v1/auth/register       # 注册
GET    /api/v1/patients            # 获取患者列表
GET    /api/v1/patients/:id        # 获取患者详情
POST   /api/v1/treatments          # 创建治疗记录
GET    /api/v1/treatments/:id      # 获取治疗记录
POST   /api/v1/parameters/request  # 申请参数调整
POST   /api/v1/parameters/approve  # 审批参数调整
GET    /api/v1/analytics/symptoms  # 症状分析
GET    /api/v1/analytics/treatment # 治疗分析
```

## 五、安全设计

### 5.1 数据安全
- 端到端加密（TLS 1.3）
- 敏感数据AES-256加密存储
- 数据库访问权限控制
- 定期安全审计

### 5.2 通信安全
- 蓝牙配对加密
- 设备认证（防止未授权连接）
- 指令签名验证
- 防重放攻击

### 5.3 医疗安全
- 参数修改需医生确认
- 敏感操作二次确认
- 异常自动报警
- 紧急停止优先

### 5.4 隐私保护
- 符合《个人信息保护法》
- 数据最小化原则
- 患者授权机制
- 数据删除权

## 六、开发计划

### 6.1 第一阶段（MVP）
- [ ] 患者端基础功能
  - 设备连接
  - 治疗控制
  - 基础记录
- [ ] 医生端基础功能
  - 患者管理
  - 远程监控
  - 参数审批
- [ ] 后端基础服务
  - 用户认证
  - 数据存储
  - 消息推送

**预计周期**: 2个月

### 6.2 第二阶段（完善）
- [ ] 数据分析功能
- [ ] 症状记录
- [ ] 社区功能
- [ ] 多语言支持

**预计周期**: 1个月

### 6.3 第三阶段（优化）
- [ ] AI辅助诊断
- [ ] 个性化推荐
- [ ] 临床试验集成
- [ ] 监管合规

**预计周期**: 2个月

## 七、商业模式

### 7.1 免费模式
- 基础功能免费
- 开源代码
- 社区支持

### 7.2 增值服务
- 高级数据分析
- 专家咨询
- 个性化方案
- 优先技术支持

### 7.3 合规收费
- 医生认证费用
- 企业版授权
- 定制化开发

## 八、风险与对策

| 风险 | 对策 |
|---|---|
| 数据泄露 | 加密存储，权限控制 |
| 未授权访问 | 设备认证，指令签名 |
| 误操作 | 二次确认，医生审批 |
| 网络延迟 | 本地缓存，离线模式 |
| 监管合规 | 符合医疗器械法规 |

## 九、总结

手机APP是连接患者和医生的桥梁，让远程医疗成为可能。通过：
- **实时连接**：患者随时治疗，医生随时监控
- **数据驱动**：基于数据分析优化治疗方案
- **社区互助**：患者间分享经验，共同对抗疾病

**让技术温暖每一个生命。**
