scj009999/TLSR8269_SixChannel_Pulse_Generator/README_UPDATE.md

# 项目更新说明

**更新日期：** 2026年5月26日  
**更新内容：** 添加开源文档，调整项目方向

---

## 重要变更

### 项目方向调整

**原方向：** 申请药监局审批，成为合法医疗器械  
**新方向：** 无名公益，纯粹技术开源

**原因：**
- 家族历史敏感性
- 保护个人隐私
- 避免政治风险
- 专注于技术和公益

---

## 新增文档

### 1. 免责声明 (`docs/免责声明.md`)

明确项目性质：
- 非医疗设备
- 非医疗建议
- 使用风险自负
- 必须咨询医生

### 2. 开源说明 (`docs/开源说明.md`)

项目详细介绍：
- 技术背景
- 硬件设计
- 软件设计
- 使用指南
- 安全警告

### 3. 制作指南 (`docs/制作指南.md`)

详细制作步骤：
- 工具准备
- 元器件采购
- PCB制作
- 焊接步骤
- 固件烧录
- 测试方法

### 4. 使用手册 (`docs/使用手册.md`)

安全使用指南：
- 禁忌症
- 操作步骤
- 参数调整
- 不良反应
- 紧急情况

---

## 项目性质

### 明确声明

```
本项目：
✅ 技术开源项目
✅ 知识分享平台
✅ 研究交流社区
❌ 不是医疗设备销售
❌ 不是医疗服务提供
❌ 不是医疗建议
```

### 使用原则

```
1. 自行承担所有风险
2. 必须咨询专业医生
3. 不能替代正规治疗
4. 不能用于商业目的
```

---

## 社区建设

### 交流渠道

- GitHub Issues：技术讨论
- 知乎专栏：科普文章
- 患者论坛：经验交流

### 贡献方式

欢迎贡献：
- 代码改进
- 文档完善
- 问题反馈
- 经验分享

---

## 未来计划

### 短期（1-3个月）

- 完善技术文档
- 制作视频教程
- 建立社区渠道
- 收集初步反馈

### 中期（3-6个月）

- 优化硬件设计
- 完善软件功能
- 建立患者社群
- 收集使用数据

### 长期（6-12个月）

- 形成稳定社区
- 积累有效数据
- 获得医生认可
- 推动政策改变

---

## 联系方式

- **项目主页：** https://github.com/scj009999/TLSR8269_SixChannel_Pulse_Generator
- **技术交流：** GitHub Issues

**注意：**
- 不提供医疗咨询
- 不提供私人联系方式
- 不回应商业合作

---

## 致谢

感谢所有贡献者：
- 刘河生教授团队（核心研究成果）
- 所有技术志愿者
- 所有患者测试者
- 所有社区贡献者

---

> **无名英雄的力量：**
> 
> 不需要名字，不需要认可。
> 
> 只需要：
> - 技术在进步
> - 患者在受益
> - 社会在改变
> 
> 这，就是最大的成功。

---

**更新日期：** 2026年5月26日  
**版本：** v1.0  
**状态：** 无名公益路线，正式启动
