scj009999/TLSR8269_SixChannel_Pulse_Generator/DISCLAIMER.md

# 重要声明与免责声明

## ⚠️ 必读

**使用本项目前，请务必仔细阅读本声明。**

---

## 一、项目性质声明

### 1.1 纯公益项目

**本项目为完全开源、纯公益项目，不收取任何形式的费用。**

- ✅ **允许**：个人学习、研究、自制使用
- ✅ **允许**：在医生指导下为患者免费治疗
- ✅ **允许**：生产免费发放给贫困患者
- ✅ **允许**：非营利组织使用
- ❌ **禁止**：任何形式的商业盈利
- ❌ **禁止**：向患者收费
- ❌ **禁止**：闭源修改后销售

### 1.2 非医疗机构

**本项目不是医疗机构，不提供医疗服务。**

- 我们不诊断疾病
- 我们不提供治疗方案
- 我们不建立医患关系
- 我们仅提供开源技术

---

## 二、医疗免责声明

### 2.1 未经审批

**本项目为实验性医疗设备，未经国家药监局（NMPA）或任何其他监管机构批准。**

### 2.2 使用风险

**使用本设备的风险由用户自行承担。**

可能的风险包括但不限于：
- 皮肤刺激或灼伤
- 头痛、头晕
- 癫痫发作（罕见但严重）
- 其他未知副作用

### 2.3 必须遵守

1. **首次使用必须在专业医生指导下进行**
2. **有癫痫病史者绝对禁用**
3. **装有心脏起搏器或其他植入式电子设备者禁用**
4. **颅内金属植入物者禁用**
5. **孕妇、儿童需在医生指导下使用**
6. **治疗中出现任何不适，立即停止使用并就医**
7. **禁止刺激眼眶、太阳穴、颈部等危险区域**

### 2.4 责任限制

**项目贡献者不对任何使用后果负责。**

- 不对治疗效果作任何保证
- 不对安全性作任何保证
- 不对任何直接或间接损失负责
- 不对任何法律纠纷负责

---

## 三、医生参与声明

### 3.1 纯属自愿

**医生参与本项目纯属自愿，以志愿者形式。**

### 3.2 无报酬

**本项目不支付任何形式的报酬。**

- 无顾问费
- 无咨询费
- 无劳务费
- 无其他任何形式的补偿

### 3.3 无雇佣关系

**医生与项目之间不存在任何雇佣关系。**

- 医生以个人身份参与
- 不代表其所在医院或机构
- 项目不对医生的行为负责
- 医生自行承担相关责任

### 3.4 医疗责任

**医生对患者的治疗决策负完全责任。**

- 项目仅提供技术平台
- 医疗决策由医生独立做出
- 项目不参与医疗过程
- 项目不提供医疗建议

---

## 四、知识产权声明

### 4.1 开源许可

本项目采用双重许可证：
- **软件**：GNU GPL v3
- **硬件**：CERN OHL v2

### 4.2 使用限制

根据许可证和本声明：
- ✅ 可以自由使用、修改、分发
- ✅ 必须保持开源
- ❌ 禁止商业盈利
- ❌ 禁止申请限制他人使用的专利

### 4.3 专利授权

项目贡献者授予全球范围内、免版税、不可撤销的专利许可，允许任何人使用、制造、销售和分发本技术用于医疗目的。

---

## 五、隐私与数据

### 5.1 数据收集

本项目可能收集以下数据：
- 匿名化的治疗参数
- 匿名化的症状评分
- 设备使用日志

### 5.2 数据使用

收集的数据将用于：
- 改进设备设计
- 学术研究
- 公开发表（去标识化）

### 5.3 数据保护

- 不收集个人身份信息
- 数据加密存储
- 符合《个人信息保护法》

---

## 六、争议解决

### 6.1 适用法律

本声明适用中华人民共和国法律。

### 6.2 争议解决

如发生争议，应首先通过友好协商解决；协商不成的，提交项目所在地人民法院诉讼解决。

---

## 七、声明更新

本项目保留随时更新本声明的权利。更新后的声明将在项目主页公布。

**最后更新日期：2026-05-09**

---

## 八、确认

**使用本项目即表示您已阅读、理解并同意本声明的所有条款。**

如果您不同意本声明的任何条款，请立即停止使用本项目。

---

## 九、联系方式

如有疑问，请联系：

- GitHub Issues: https://github.com/scj009999/TLSR8269_SixChannel_Pulse_Generator/issues
- 项目主页: https://github.com/scj009999/TLSR8269_SixChannel_Pulse_Generator

---

**再次强调：本项目为纯公益项目，不收取任何费用。医生参与纯属自愿。使用风险自行承担。**

**每一个生命都值得尊重，但安全永远是第一位的。**
