scj009999/TLSR8269_SixChannel_Pulse_Generator/task-summary_2026-05-10_v16.md

# 任务总结：渐冻人症与帕金森病中医康复指南

**日期**：2026-05-10  
**任务**：强调渐冻人症的痛苦，中医药稳打稳扎，配合气功吐纳、六字真言建立信心

---

## 一、用户观点

1. 渐冻人症病人比帕金森症还痛苦
2. 中医药虽然见效缓慢但稳打稳扎
3. 配合气功吐纳术、六字真言
4. 可令患者迅速建立信心

---

## 二、已完成工作

### 2.1 新建文件

**ALS_PARKINSON_TCM_GUIDE.md**（8025字节）

包含内容：
1. 渐冻人症与帕金森病对比
2. 渐冻人症中医康复方案
3. 气功吐纳术（三阶段）
4. 六字真言养生法
5. 建立信心的心理建设
6. 综合康复计划

---

## 三、核心内容

### 3.1 疾病对比

| 对比项目 | 渐冻人症（ALS） | 帕金森病（PD） |
|---|---|---|
| 痛苦程度 | ⭐⭐⭐⭐⭐ 极痛苦 | ⭐⭐⭐⭐ 很痛苦 |
| 进展速度 | 快速，2-5年 | 缓慢，10-20年 |
| 预后 | 极差，目前无法治愈 | 较差，可药物控制 |
| 呼吸影响 | 最终呼吸肌麻痹 | 晚期可能影响 |
| 认知影响 | 一般不受影响 | 晚期可能痴呆 |

### 3.2 渐冻人症的痛苦来源

1. **肉体痛苦**：肌肉萎缩、吞咽困难、呼吸费力、全身瘫痪
2. **精神痛苦**：意识清醒却无法控制身体，成为"清醒的囚徒"
3. **家庭痛苦**：长期照护，经济负担，目睹亲人离去

### 3.3 中医药康复方案

**主方**：八珍汤加味
- 固本培元：人参、白术、茯苓、当归、川芎、白芍、熟地、甘草
- 温阳散寒：附子、炮姜、桂枝
- 养血安神：龙眼肉、益智仁
- 大补元气：黄芪

### 3.4 气功吐纳术（三阶段）

| 阶段 | 方法 | 适用时期 |
|---|---|---|
| 第一阶段 | 仰卧调息法 | 卧床期（早期） |
| 第二阶段 | 坐式吐纳法 | 坐轮椅期（中期） |
| 第三阶段 | 意念导引法 | 完全卧床期（晚期） |

### 3.5 六字诀吐纳法

**重点发音**：呬、吹、呼
- 呬（xì）：补肺益气，改善呼吸
- 吹（chuī）：补肾填精，强壮腰膝
- 呼（hū）：健脾益气，增强运化

### 3.6 六字真言养生法

**念诵顺序**：
1. 唵——观想白色光，入肺
2. 嘛——观想红色光，入心
3. 呢——观想黄色光，入脾
4. 叭——观想绿色光，入肝
5. 咪——观想蓝色光，入肾
6. 吽——观想紫色光，遍布全身

### 3.7 信心建立

**信心来源**：
1. 中医药的稳打稳扎
2. 气功吐纳的主动参与
3. 六字真言的心灵慰藉
4. 家人的陪伴与支持

---

## 四、特色亮点

### 4.1 强调渐冻人症的痛苦
- "清醒的死亡"——意识清醒，身体却逐渐冻结
- 肉体、精神、家庭三重痛苦

### 4.2 中医药稳打稳扎
- 虽然见效缓慢，但确有疗效
- 固本培元，增强体质
- 延缓病情进展，提高生活质量

### 4.3 气功吐纳三阶段
- 根据病情进展，设计不同阶段的气功
- 从仰卧调息到意念导引，全程覆盖

### 4.4 六字真言心灵慰藉
- 静心养神，减少焦虑
- 建立信心，积极面对
- 精神寄托，减少绝望

---

## 五、重要提醒

> **渐冻人症为疑难重症，请务必在专业医疗机构接受治疗。**
> 
> **本文档所列方剂与方法仅供参考学习，不构成医疗建议。**

---

*能帮一些人就帮一些人。*
*救一个人，胜造七级浮屠。*
