scj009999/TLSR8269_SixChannel_Pulse_Generator/task-summary_2026-05-13_v20.md

# 任务总结：多平台文章撰写

**日期**：2026-05-13  
**任务**：为知乎、FCA、eBook、小红书、WhatsApp等平台撰写文章

---

## 一、已完成工作

### 1.1 新建文件

| 文件 | 大小 | 平台 | 特点 |
|---|---|---|---|
| **ZHihu_ARTICLE.md** | 8,598字节 | 知乎 | 深度长文，理性分析 |
| **XIAOHONGSHU_POST.md** | 3,371字节 | 小红书 | 图文并茂，情感共鸣 |
| **FCA_EBOOK.md** | 24,191字节 | FCA/eBook | 完整手册，系统全面 |
| **WHATSAPP_MESSAGE.md** | 7,857字节 | WhatsApp/微信 | 多版本，适合转发 |

---

## 二、各平台文章特点

### 2.1 知乎文章

**风格**：深度、理性、专业

**结构**：
1. 引人入胜的开头（真实案例）
2. 四种治疗方案对比表
3. 每种方案详细分析
4. 患者常见问题解答
5. 开源项目介绍
6. 给家属的建议

**亮点**：
- 客观陈述，不攻击
- 数据对比清晰
- 引用研究证据
- 强调知情选择

### 2.2 小红书文章

**风格**：轻松、直观、情感化

**结构**：
1. 情感故事引入
2. 简洁对比表
3. 什么是经颅电刺激
4. 手术不是唯一选择
5. 决定前要问的问题
6. 项目介绍

**亮点**：
- 表情符号丰富
- 表格简洁明了
- 语言亲切
- 适合女性用户

### 2.3 FCA/eBook手册

**风格**：系统、全面、专业

**结构**：
1. 13个章节，完整覆盖
2. 从疾病介绍到治疗选择
3. 患者故事和家属指南
4. 资源推荐和附录

**亮点**：
- 系统全面
- 可作为电子书发布
- 包含决策工具
- 适合深度阅读

### 2.4 WhatsApp/微信消息

**风格**：简洁、直接、易转发

**版本**：
1. 简短版（快速分享）
2. 详细版（转发）
3. 情感版（朋友圈）
4. 问答版（群聊）
5. 极简版（短信）

**亮点**：
- 多版本适配不同场景
- 易复制粘贴
- 适合移动端阅读
- 便于传播

---

## 三、核心信息一致性

所有平台文章均包含：

### 3.1 核心事实

- 帕金森病目前无法治愈
- 多种治疗方案各有优缺点
- DBS手术有效但有风险
- 患者有权了解全部信息

### 3.2 关键数据

| 方案 | 侵入性 | 费用 | 可逆性 |
|---|---|---|---|
| 药物 | 无 | 中等 | 可逆 |
| DBS | 有 | 20-40万 | 部分 |
| 经颅电刺激 | 无 | 较低 | 完全 |
| 中医 | 无 | 低 | 可逆 |

### 3.3 重要提示

> "手术决策需充分评估，选择有经验的医疗团队。"

### 3.4 项目介绍

- 开源、非商业、公益
- 非侵入性、低成本
- 6路输出、安全可靠

---

## 四、非攻击性原则

所有文章遵循：

✅ 客观陈述事实
✅ 不点名批评
✅ 不煽动情绪
✅ 理性分析利弊
✅ 尊重患者选择
✅ 强调知情同意

---

## 五、使用建议

### 5.1 发布策略

| 平台 | 文章 | 发布方式 |
|---|---|---|
| 知乎 | ZHIHU_ARTICLE.md | 专栏文章 |
| 小红书 | XIAOHONGSHU_POST.md | 图文笔记 |
| 公众号 | FCA_EBOOK.md | 连载或电子书 |
| 微信群 | WHATSAPP_MESSAGE.md | 转发分享 |
| 朋友圈 | WHATSAPP_MESSAGE.md | 情感版 |

### 5.2 传播策略

1. **先发知乎**：建立专业形象
2. **再发小红书**：扩大受众
3. **公众号连载**：深度用户
4. **微信群转发**：精准触达
5. **朋友圈扩散**：社交传播

---

## 六、重要提醒

### 6.1 法律合规

- 所有文档含免责声明
- 不构成医疗建议
- 强调咨询专业医生
- 遵循CC BY-SA 4.0协议

### 6.2 伦理原则

- 尊重逝者，不消费悲剧
- 帮助生者，提供有用信息
- 推动改变，改善医疗环境

---

## 七、文件清单

| 文件 | 大小 | 说明 |
|---|---|---|
| ZHIHU_ARTICLE.md | 8,598字节 | 知乎文章 |
| XIAOHONGSHU_POST.md | 3,371字节 | 小红书文章 |
| FCA_EBOOK.md | 24,191字节 | 电子书手册 |
| WHATSAPP_MESSAGE.md | 7,857字节 | 微信/WhatsApp消息 |
| task-summary_2026-05-13_v20.md | 本文件 | 任务总结 |

---

## 八、下一步建议

1. **制作配图**：为小红书制作对比图表
2. **发布文章**：按平台特点发布
3. **收集反馈**：根据反馈优化
4. **持续更新**：根据新研究更新内容
5. **建立社区**：按照SAFE_COMMUNITY_GUIDE.md建立安全社区

---

> **"知情选择是患者的权利，信息透明是医疗的底线。"**

> **"能帮一些人就帮一些人。"**
> 
> **"救一个人，胜造七级浮屠。"**

---

*本文遵循开放、透明、非商业原则。*
*欢迎转载，请注明出处。*
