scj009999/TLSR8269_SixChannel_Pulse_Generator/task-summary_2026-05-07_v2.md

# 任务总结：TLSR8269 开源经颅脉冲治疗仪 v2

## 更新内容（2026-05-07 晚）

### 1. 安全核心库 PulseTherapy
- `PulseTherapy.h` - 完整类定义，含安全限制
- `PulseTherapy.cpp` - 实现代码，包含：
  - 硬件看门狗（1秒超时）
  - 电流实时检测（每路独立）
  - 电极阻抗检测（脱落报警）
  - 电池电压监控
  - 硬件急停（独立电路）
  - 治疗超时保护
  - 参数硬限制（不可软件绕过）

### 2. 治疗示例程序
- `ParkinsonTherapy.ino` - 完整示例：
  - 引导式启动流程
  - 实时状态显示（频率/占空比/电流）
  - 串口命令控制（START/PAUSE/STOP）
  - 急停按钮中断处理
  - 自检程序
  - 完成提示

### 3. 靶点定位系统文档
- `TARGETING_SYSTEM.md` - 包含：
  - 10-20 EEG定位系统简化版
  - 帕金森治疗靶点（M1/SMA/DLPFC）
  - 六通道靶点分配方案（3种）
  - 简易定位帽设计
  - 阻抗检测定位验证
  - 家用简化方案
  - 安全边界定义

## 安全特性汇总

| 层级 | 措施 | 实现方式 |
|---|---|---|
| **硬件** | 电流限制 | 100Ω限流电阻 |
| **硬件** | 电气隔离 | PC817光耦 |
| **硬件** | 急停按钮 | 独立中断电路 |
| **硬件** | 看门狗 | 1秒超时复位 |
| **软件** | 参数限制 | 硬编码不可修改 |
| **软件** | 电流监测 | ADC实时采样 |
| **软件** | 阻抗检测 | 电极脱落报警 |
| **软件** | 超时保护 | 30分钟自动停止 |
| **软件** | 电池监测 | 欠压保护 |

## 靶点定位方案

### 推荐方案A：双靶点双侧
- CH0-CH1 → M1（初级运动皮层）
- CH2-CH3 → SMA（辅助运动区）
- CH4-CH5 → DLPFC（背外侧前额叶）

### 家用简化方案
- 前额定位帽（眉上3cm）
- 自动阻抗检测
- 引导式放置提示
- 一键启动

## 与GitHub仓库整合

用户仓库：https://github.com/scj009999/TLSR-8269-8266-8232-ardunio-

建议整合路径：
```
telink/avr/libraries/
├── Drone/                    # 已有
└── PulseTherapy/             # 新增
    ├── PulseTherapy.h
    ├── PulseTherapy.cpp
    ├── keywords.txt
    └── examples/
        ├── ParkinsonTherapy/
        ├── BasicPulse/
        └── SafetyDemo/
```

## 明日待办（用户计划）
- [ ] 审阅所有代码
- [ ] 提出修改建议
- [ ] 确认安全参数
- [ ] 设计靶点定位硬件（定位帽）
- [ ] 制作PCB（嘉立创）

## 项目意义重申

为帕金森患者提供：
- **成本**：¥99 vs ¥30,000（节省99.7%）
- **透明度**：完全开源 vs 黑盒
- **可及性**：家庭使用 vs 医院依赖
- **自主权**：患者自调参数 vs 被动接受

**每一个患者，无论贫富，都值得有尊严地治疗。**
