scj009999/TLSR8269_SixChannel_Pulse_Generator/docs/抖音发布指南.md

# 抖音发布指南

**日期：** 2026年5月26日  
**目的：** 安全、合规地进行技术分享宣传  
**核心原则：** 保护隐私，不承诺疗效，强调医生指导

---

## 一、账号设置

### 1.1 账号信息

| 项目 | 建议 | 说明 |
|---|---|---|
| 昵称 | 帕金森技术分享 | 中性，不个人化 |
| 头像 | 技术相关图标 | 避免真人照片 |
| 简介 | 开源技术分享，非医疗建议 | 明确性质 |
| 背景 | 简洁技术风 | 专业感 |

### 1.2 隐私设置

- ❌ 不绑定个人手机号（可用备用号）
- ❌ 不开启位置显示
- ❌ 不展示个人联系方式
- ✅ 允许评论和私信（用于技术交流）

---

## 二、内容规范

### 2.1 必须包含的内容

**每个视频必须：**

1. **口播免责声明**
   ```
   "本项目仅供技术交流，不构成医疗建议。
   请在专业医生指导下进行任何治疗。"
   ```

2. **字幕免责声明**
   ```
   画面底部固定显示：
   "技术分享 | 非医疗建议 | 请咨询医生"
   ```

3. **结尾信息**
   ```
   - 项目主页：GitHub链接
   - 许可证：GPL-3.0
   - 声明：使用风险自负
   ```

### 2.2 禁止内容

| 类型 | 示例 | 后果 |
|---|---|---|
| 疗效承诺 | "治愈帕金森" | 违规，可能封号 |
| 医疗建议 | "你应该这样做" | 非法行医嫌疑 |
| 商业推广 | "购买我的设备" | 违规，封号 |
| 攻击他人 | "医院都是骗人的" | 违规，封号 |
| 暴露隐私 | 展示患者面部 | 侵犯隐私 |
| 诱导捐赠 | "请捐款支持" | 违规 |

### 2.3 敏感词规避

**避免使用：**
- ❌ "治愈"
- ❌ "根治"
- ❌ "特效"
- ❌ "神医"
- ❌ "秘方"
- ❌ "包治"
- ❌ "100%有效"

**建议使用：**
- ✅ "辅助改善"
- ✅ "缓解症状"
- ✅ "技术分享"
- ✅ "个人经验"
- ✅ "仅供参考"
- ✅ "因人而异"

---

## 三、视频制作规范

### 3.1 画面要求

| 项目 | 要求 |
|---|---|
| 分辨率 | 1080×1920（竖屏） |
| 时长 | 15-60秒 |
| 帧率 | 30fps |
| 光线 | 明亮清晰 |

### 3.2 声音要求

| 项目 | 要求 |
|---|---|
| 音质 | 清晰无杂音 |
| 音量 | 适中，不刺耳 |
| 背景音乐 | 轻柔，不喧宾夺主 |

### 3.3 字幕要求

| 项目 | 要求 |
|---|---|
| 字体 | 清晰易读 |
| 颜色 | 白色+黑色描边 |
| 位置 | 底部，不遮挡画面 |
| 大小 | 适中，手机可看清 |

---

## 四、发布流程

### 4.1 发布前检查清单

- [ ] 视频包含免责声明（口播+字幕）
- [ ] 没有疗效承诺
- [ ] 没有医疗建议
- [ ] 没有商业推广
- [ ] 没有暴露隐私
- [ ] 标签合适
- [ ] 封面吸引人

### 4.2 发布设置

| 设置 | 建议 |
|---|---|
| 公开范围 | 公开 |
| 允许下载 | 关闭（保护内容） |
| 允许合拍 | 关闭 |
| 位置信息 | 不显示 |
| 谁可以评论 | 所有人 |

### 4.3 发布时间

| 日期 | 时间 | 视频 |
|---|---|---|
| 第1天 | 20:00 | 视频1：开篇 |
| 第3天 | 12:00 | 视频2：科普 |
| 第5天 | 20:00 | 视频3：制作 |
| 第7天 | 12:00 | 视频4：安全 |
| 第10天 | 20:00 | 视频5：效果 |
| 第12天 | 12:00 | 视频6：社区 |
| 第15天 | 20:00 | 视频7：结尾 |

---

## 五、评论管理

### 5.1 积极回复

**技术问题：**
```
问：这个芯片哪里买？
答：可以在Telink官网或淘宝购买，
    注意选择正品。详细清单在项目主页。
```

**使用问题：**
```
问：电流设置多少合适？
答：建议从0.5mA开始，逐步增加。
    但请务必在医生指导下调整参数。
```

**鼓励支持：**
```
评论：加油！
回复：谢谢！希望技术能帮助更多人。
    但请记住，医生才是治疗的主体。
```

### 5.2 谨慎回复

**疗效询问：**
```
问：用了有效果吗？
答：个体差异很大，效果因人而异。
    本项目仅分享技术，不承诺疗效。
    请咨询您的医生。
```

**购买询问：**
```
问：哪里可以买到？
答：本项目不销售设备，只分享技术资料。
    您可以自行制作，但需具备电子制作能力。
    制作和使用风险自负。
```

**医疗建议：**
```
问：我应该怎么治疗？
答：抱歉，我们无法提供医疗建议。
    请咨询您的主治医生，
    或前往正规医院就诊。
```

### 5.3 删除评论

**以下评论应删除：**
- 广告推销
- 医疗骗局
- 人身攻击
- 泄露隐私
- 违法信息

---

## 六、风险应对

### 6.1 被质疑时的应对

**质疑1："你这是非法行医！"**

应对：
```
我们明确声明：
1. 本项目不是医疗服务
2. 不提供医疗建议
3. 不销售医疗设备
4. 仅分享技术资料

所有内容都包含免责声明，
强调必须在医生指导下使用。
```

**质疑2："你这是在骗钱！"**

应对：
```
本项目：
- 完全免费开源
- 不收取任何费用
- 不销售任何产品
- 不接受任何捐赠

所有资料在GitHub免费下载，
遵循GPL-3.0开源许可证。
```

**质疑3："出事了谁负责？"**

应对：
```
我们明确声明：
1. 使用风险自负
2. 必须在医生指导下使用
3. 项目不承担任何责任
4. 所有资料包含完整免责声明

请仔细阅读免责声明后再决定是否使用。
```

### 6.2 被举报时的应对

**步骤1：自查**
- 检查视频内容是否违规
- 检查是否包含疗效承诺
- 检查是否包含医疗建议

**步骤2：申诉**
- 如果内容合规，提交申诉
- 说明项目性质（技术分享）
- 提供免责声明证据

**步骤3：调整**
- 如果确实违规，立即删除
- 调整内容后重新发布
- 加强免责声明

---

## 七、数据监控

### 7.1 关注指标

| 指标 | 说明 |
|---|---|
| 播放量 | 视频曝光度 |
| 点赞量 | 内容认可度 |
| 评论量 | 互动程度 |
| 分享量 | 传播效果 |
| 粉丝增长 | 社区规模 |

### 7.2 风险指标

| 指标 | 说明 | 应对 |
|---|---|---|
| 负面评论增多 | 可能内容有问题 | 自查，调整 |
| 被举报次数 | 可能违规 | 立即处理 |
| 官方警告 | 严重违规 | 停止发布，整改 |
| 账号限流 | 内容问题 | 优化内容 |

---

## 八、长期维护

### 8.1 内容更新

- 定期发布新内容（每周1-2个）
- 回复评论和私信
- 更新项目进展
- 分享用户经验（经授权）

### 8.2 社区建设

- 引导用户到GitHub交流
- 建立技术讨论群
- 组织线上分享会
- 收集用户反馈

### 8.3 风险监控

- 定期检查评论
- 监控负面信息
- 及时应对危机
- 记录处理过程

---

## 九、紧急情况处理

### 9.1 账号被封

**立即行动：**
1. 检查违规原因
2. 提交申诉
3. 准备备用账号
4. 通知社区

### 9.2 负面舆情

**应对步骤：**
1. 评估影响范围
2. 准备回应声明
3. 联系平台处理
4. 必要时暂停发布

### 9.3 法律风险

**应对措施：**
1. 立即停止相关活动
2. 咨询法律专业人士
3. 保留所有证据
4. 配合调查

---

## 十、成功标准

### 10.1 短期（1个月）

- [ ] 发布7个视频
- [ ] 获得1000粉丝
- [ ] 视频总播放10万
- [ ] 0违规记录

### 10.2 中期（3个月）

- [ ] 粉丝5000
- [ ] 建立稳定社区
- [ ] 获得医生关注
- [ ] 收集有效反馈

### 10.3 长期（1年）

- [ ] 粉丝1万+
- [ ] 形成技术生态
- [ ] 推动政策关注
- [ ] 帮助100+患者

---

> **最后提醒：**
> 
> 我们分享的是技术和希望，不是医疗方案。
> 
> 保护隐私，遵守规则，帮助他人。
> 
> 技术属于每一个人，但安全永远是第一位的。

---

**制定日期：** 2026年5月26日  
**版本：** v1.0  
**状态：** 待执行
