scj009999/TLSR8269_SixChannel_Pulse_Generator/docs/抖音视频脚本_系列.md

# 抖音视频脚本系列

**项目：** 开源经颅脉冲治疗仪  
**平台：** 抖音  
**风格：** 科普、温情、真实  
**目的：** 技术分享，帮助患者了解治疗原理  
**注意：** 不销售设备，不提供医疗建议，仅做知识分享

---

## 视频1：开篇 - 一个患者的故事

**时长：** 60秒  
**风格：** 真人出镜，温情叙述

### 脚本

**【画面：清晨，阳光透过窗户】**

**旁白（温和男声）：**
"2023年，我被确诊为帕金森病。"

**【画面：颤抖的手，药瓶】**

"医生告诉我，这个病无法治愈，只能控制。"

**【画面：医院账单，15万的数字】**

"每年的治疗费用，超过15万。"

**【画面：深夜，独自坐在窗前】**

"那一刻，我觉得天塌了。"

**【画面：转折，电脑屏幕，研究论文】**

"但我没有放弃。我开始研究，开始学习。"

**【画面：电路板，焊接，代码】**

"我是一名工程师，我相信技术可以改变生活。"

**【画面：简单的设备原型】**

"这是我自己做的设备，成本不到100块。"

**【画面：使用设备，平静的表情】**

"它不能治愈帕金森，但它让我的生活好了一些。"

**【画面：夕阳，微笑】**

"我想把这个技术分享出来，帮助更多的人。"

**【字幕：开源项目，免费分享，技术交流】**

**【结尾：项目主页，免责声明】**

"本项目仅供技术交流，不构成医疗建议。请在医生指导下治疗。"

---

## 视频2：科普 - 什么是经颅电刺激

**时长：** 45秒  
**风格：** 动画科普，简单易懂

### 脚本

**【画面：大脑动画】**

**旁白（清晰女声）：**
"你知道吗？你的大脑里有860亿个神经元。"

**【画面：神经元连接动画】**

"它们通过电信号交流。"

**【画面：帕金森病动画，神经元死亡】**

"帕金森病，是这些神经元在慢慢死亡。"

**【画面：经颅电刺激动画】**

"经颅电刺激，就是通过头皮施加微弱电流，"

**【画面：电流刺激神经元】**

"帮助剩余的神经元更好地工作。"

**【画面：参数显示：1-2毫安，比手机充电还弱】**

"电流只有1-2毫安，比手机充电还弱。"

**【画面：安全提示】**

"但请记住，这不是玩具，需要在医生指导下使用。"

**【字幕：技术分享，非医疗建议】**

---

## 视频3：制作 - 100元能做啥

**时长：** 60秒  
**风格：** 快节奏，展示过程

### 脚本

**【画面：元器件摆满桌面】**

**旁白（轻快节奏）：**
"100元，能做什么？"

**【画面：一顿火锅？一件衣服？】**

"一顿火锅？一件衣服？"

**【画面：电路板、芯片、电阻】**

"还是...一个希望？"

**【快速剪辑：焊接、组装、测试】**

"主控芯片：15元"
"电阻电容：5元"
"电路板：20元"
"外壳：10元"

**【画面：完成的小型设备】**

"总计：不到100元。"

**【画面：设备连接手机APP】**

"6通道输出，蓝牙连接，手机控制。"

**【画面：安全保护电路】**

"多重安全保护，限流、隔离、急停。"

**【字幕：开源设计，免费下载，自行制作】**

**【结尾：免责声明】**

"本项目仅供技术学习，不构成医疗建议。"

---

## 视频4：安全 - 安全第一

**时长：** 30秒  
**风格：** 严肃、警示

### 脚本

**【画面：红色警告标志】**

**旁白（严肃男声）：**
"在开始之前，你必须知道这些。"

**【画面：禁止标志】**

"心脏起搏器患者，禁用。"
"癫痫患者，禁用。"
"孕妇，禁用。"
"头部伤口，禁用。"

**【画面：医生形象】**

"必须在医生指导下使用。"

**【画面：设备参数】**

"电流不超过2毫安。"
"时间不超过30分钟。"

**【画面：急停按钮】**

"感到不适，立即按下急停。"

**【字幕：安全第一，风险自负，咨询医生】**

---

## 视频5：效果 - 真实记录

**时长：** 45秒  
**风格：** 真实、记录

### 脚本

**【画面：日期显示，治疗第一天】**

**旁白（平静声音）：**
"这是我使用的第一天。"

**【画面：手部的轻微颤抖】**

"手还在抖，但心里有了希望。"

**【画面：日期显示，治疗第一周】**

"第一周，睡眠好了一些。"

**【画面：日期显示，治疗第一个月】**

"第一个月，走路稳了一些。"

**【画面：日期显示，治疗第三个月】**

"第三个月，我可以自己写字了。"

**【画面：对比视频，治疗前后】**

"这不是奇迹，这是科学。"

**【字幕：个体差异，效果因人而异，需医生指导】**

**【结尾：免责声明】**

"本记录仅供参考，不构成疗效承诺。"

---

## 视频6：社区 - 我们一起

**时长：** 30秒  
**风格：** 温暖、团结

### 脚本

**【画面：多个患者的手，叠在一起】**

**旁白（温暖女声）：**
"一个人，走得快。"

**【画面：一群人，围坐在一起】**

"一群人，走得远。"

**【画面：电脑屏幕，代码，讨论】**

"我们有工程师，有医生，有患者，有家属。"

**【画面：项目主页，GitHub】**

"开源，免费，共享。"

**【画面：笑脸，希望】**

"因为我们相信，技术应该属于每一个人。"

**【字幕：开源社区，欢迎加入，技术交流】**

---

## 视频7：结尾 - 为什么选择开源

**时长：** 60秒  
**风格：** 深情、哲理

### 脚本

**【画面：老人和孩子，夕阳】**

**旁白（深沉男声）：**
"有人问我，为什么要开源？"

**【画面：医院，昂贵的设备】**

"因为15万的治疗费，太多人付不起。"

**【画面：贫困患者，无助的眼神】**

"因为有人正在放弃治疗。"

**【画面：孩子，未来】**

"因为我想让我的孩子知道，"

**【画面：技术图纸，代码】**

"技术不是赚钱的工具，"

**【画面：患者笑容】**

"而是帮助他人的力量。"

**【画面：星空，浩瀚】**

"我们都很渺小，"

**【画面：烛光，温暖】**

"但我们可以成为彼此的光。"

**【字幕：开源项目，免费分享，技术属于每一个人】**

**【结尾：项目主页，免责声明】**

"本项目仅供技术交流，不构成医疗建议。请在医生指导下治疗。"

---

## 发布注意事项

### 必须包含

1. **免责声明**
   - "本项目仅供技术交流"
   - "不构成医疗建议"
   - "请在医生指导下治疗"

2. **风险提示**
   - "使用风险自负"
   - "禁忌症说明"
   - "紧急情况处理"

3. **项目信息**
   - 项目主页
   - 开源许可证
   - 社区交流方式

### 避免内容

- ❌ 承诺疗效
- ❌ 对比商业产品
- ❌ 批评医疗体系
- ❌ 展示患者痛苦
- ❌ 诱导购买或捐赠

### 标签建议

```
#帕金森 #开源 #技术分享 #医疗设备 #DIY #科普 #健康生活 #工程师 #公益 #希望
```

---

## 发布计划

| 视频 | 发布日 | 时间 |
|---|---|---|
| 视频1：开篇 | 第1天 | 晚上8点 |
| 视频2：科普 | 第3天 | 中午12点 |
| 视频3：制作 | 第5天 | 晚上8点 |
| 视频4：安全 | 第7天 | 中午12点 |
| 视频5：效果 | 第10天 | 晚上8点 |
| 视频6：社区 | 第12天 | 中午12点 |
| 视频7：结尾 | 第15天 | 晚上8点 |

---

## 互动管理

### 回复评论原则

- ✅ 回答技术问题
- ✅ 分享使用经验
- ✅ 鼓励患者坚持治疗
- ❌ 不提供医疗建议
- ❌ 不承诺疗效
- ❌ 不私下联系

### 标准回复模板

**问：这个能治愈帕金森吗？**
答：不能治愈，但可以辅助改善症状。请在医生指导下使用。

**问：哪里可以买到？**
答：本项目不开源销售设备，只分享技术资料。您可以自行制作，但需具备电子制作能力。

**问：安全吗？**
答：设计有多重安全保护，但任何电子设备都有风险。请在医生指导下使用，严格遵守操作规范。

---

> **最后提醒：**
> 
> 我们分享的是技术和希望，不是医疗方案。
> 
> 每一个生命都值得尊重，每一个患者都值得帮助。
> 
> 但请记住，医生才是治疗的主体。

---

**制作日期：** 2026年5月26日  
**版本：** v1.0  
**状态：** 待拍摄发布
