scj009999/TLSR8269_SixChannel_Pulse_Generator/docs/无名公益方案_已执行.md

# 无名公益方案 - 执行记录

**执行日期：** 2026年5月26日  
**执行人：** 束长江  
**状态：** 已完成初始文档准备和上传

---

## 一、已完成的文档

### 1.1 免责声明 (`docs/免责声明.md`)

**内容：**
- 明确项目性质（非医疗设备、非医疗建议）
- 使用风险自负声明
- 必须就医提醒
- 法律合规说明
- 知识产权声明
- 隐私保护说明

**关键条款：**
```
本项目：
- ❌ 不是医疗器械销售
- ❌ 不是医疗服务提供
- ❌ 不是医疗建议
- ❌ 不收取任何费用
```

### 1.2 开源说明 (`docs/开源说明.md`)

**内容：**
- 项目简介和目标
- 技术背景（刘河生教授研究）
- 硬件设计概述
- 软件设计概述
- 使用指南
- 安全警告
- 文件清单
- 社区交流规则

**关键说明：**
```
项目性质：
- ✅ 技术开源
- ✅ 知识分享
- ✅ 研究交流
- ❌ 非商业销售
- ❌ 非医疗服务
- ❌ 非医疗建议
```

### 1.3 制作指南 (`docs/制作指南.md`)

**内容：**
- 制作前准备（技能、工具、安全装备）
- 元器件采购清单和成本
- PCB制作步骤
- 详细焊接步骤
- 固件烧录方法
- 测试步骤
- 组装外壳
- 常见问题解决

**成本估算：**
```
PCB制板：20-50元（5片）
元器件：50-80元
外壳：10-20元
总计：80-150元/台
```

### 1.4 使用手册 (`docs/使用手册.md`)

**内容：**
- 使用前必读（警告、禁忌症）
- 设备介绍
- 使用前准备
- 详细操作步骤
- 参数调整指南
- 使用日志记录
- 注意事项
- 不良反应处理
- 维护保养
- 故障排除

**安全强调：**
```
⚠️ 重要警告：
1. 本项目不是医疗设备
2. 使用风险自负
3. 必须咨询医生
```

---

## 二、已上传GitHub

### 2.1 提交记录

```
提交：26d374f
消息：添加开源文档：免责声明、开源说明、制作指南、使用手册
日期：2026-05-26
文件：4个新增
```

### 2.2 文件位置

```
docs/
├── 免责声明.md
├── 开源说明.md
├── 制作指南.md
└── 使用手册.md
```

### 2.3 仓库地址

```
https://github.com/scj009999/TLSR8269_SixChannel_Pulse_Generator
```

---

## 三、文档特点

### 3.1 保护隐私

- 不透露个人身份
- 不透露家族背景
- 使用"匿名技术志愿者团队"
- 不提供私人联系方式

### 3.2 强调安全

- 多处免责声明
- 明确禁忌症
- 紧急情况处理
- 必须就医提醒

### 3.3 技术完整

- 详细的制作步骤
- 完整的元器件清单
- 清晰的测试方法
- 常见问题解决

### 3.4 法律合规

- GPL-3.0许可证
- 明确非商业性质
- 风险自负声明
- 知识产权说明

---

## 四、下一步计划

### 4.1 短期（1-2周）

- [ ] 完善技术文档
- [ ] 制作视频教程
- [ ] 建立社区交流渠道
- [ ] 收集初步反馈

### 4.2 中期（1-3个月）

- [ ] 完善硬件设计
- [ ] 优化软件功能
- [ ] 建立患者交流群
- [ ] 收集使用数据

### 4.3 长期（3-12个月）

- [ ] 形成稳定社区
- [ ] 积累有效数据
- [ ] 获得医生认可
- [ ] 推动政策改变

---

## 五、风险监控

### 5.1 法律风险

| 风险 | 应对措施 |
|---|---|
| 被误认为销售设备 | 明确标注"非卖品" |
| 被误认为医疗行为 | 明确标注"非医疗建议" |
| 患者使用后出问题 | 完善免责声明 |

### 5.2 技术风险

| 风险 | 应对措施 |
|---|---|
| 设备制作不合格 | 提供详细指南 |
| 使用不当导致伤害 | 强调安全操作 |
| 效果不佳导致延误 | 强调辅助性质 |

---

## 六、成功指标

### 6.1 短期目标

- [ ] 100人了解项目
- [ ] 10人尝试制作
- [ ] 5人持续使用
- [ ] 0起安全事故

### 6.2 中期目标

- [ ] 1000人了解项目
- [ ] 100人尝试制作
- [ ] 50人持续使用
- [ ] 积累有效数据

### 6.3 长期目标

- [ ] 形成稳定社区
- [ ] 产生显著效果
- [ ] 获得医生认可
- [ ] 推动政策改变

---

## 七、总结

### 7.1 决策正确性

选择无名公益路线：
- ✅ 保护家族隐私
- ✅ 避免政治风险
- ✅ 项目可以继续
- ✅ 仍能 helping患者

### 7.2 价值不变

无论是否审批：
- ✅ 技术在进步
- ✅ 知识在传播
- ✅ 患者在受益
- ✅ 社会在改变

### 7.3 未来可能

也许有一天：
- 技术成熟，数据充分
- 环境友好，政策开放
- 那时再申请，更易成功

---

**执行人：** 束长江  
**日期：** 2026年5月26日  
**状态：** 已完成初始准备

---

> **无名英雄的力量：**
> 
> 不需要名字，不需要认可。
> 
> 只需要：
> - 技术在进步
> - 患者在受益
> - 社会在改变
> 
> 这，就是最大的成功。
