scj009999/TLSR8269_SixChannel_Pulse_Generator/docs/免责声明.md

# 免责声明

**最后更新：** 2026年5月26日  
**版本：** v1.0

---

## 一、重要声明

本项目为**纯粹的技术开源项目**，旨在促进医疗知识共享和技术交流。

**本项目：**
- ❌ 不是医疗器械销售
- ❌ 不是医疗服务提供
- ❌ 不是医疗建议
- ❌ 不收取任何费用

---

## 二、使用风险

### 2.1 自行承担风险

任何基于本项目资料的行为，包括但不限于：
- 自行制作或使用设备
- 调整治疗方案
- 改变用药习惯
- 停止正规治疗

**均由行为人自行承担全部责任和风险。**

### 2.2 无质量保证

本项目提供的：
- 设计图纸
- 软件代码
- 技术文档
- 使用说明

**均按"原样"提供，不提供任何明示或暗示的保证。**

包括但不限于：
- 适销性保证
- 特定用途适用性保证
- 不侵权保证
- 安全性保证

---

## 三、医疗建议

### 3.1 必须就医

**任何健康问题，请务必咨询专业医生。**

本项目：
- 不能替代医生诊断
- 不能替代正规治疗
- 不能替代药物使用
- 不能替代专业护理

### 3.2 紧急情况

如出现以下情况，请**立即停止使用并就医**：
- 头痛、头晕、恶心
- 皮肤过敏、红肿、烧伤
- 心悸、胸闷、呼吸困难
- 癫痫发作
- 任何不适症状

---

## 四、法律合规

### 4.1 遵守法规

使用本项目资料时，请确保：
- 遵守当地法律法规
- 遵守医疗器械管理规定
- 不用于商业目的
- 不提供给第三方用于商业目的

### 4.2 责任限制

在法律允许的最大范围内：
- 项目贡献者不承担任何责任
- 不对任何损失负责
- 不对任何伤害负责
- 不对任何后果负责

---

## 五、知识产权

### 5.1 开源许可

本项目采用 **GPL-3.0 开源许可证**。

您可以：
- ✅ 自由使用
- ✅ 自由修改
- ✅ 自由分享
- ✅ 自由研究

但必须：
- 📌 遵守GPL-3.0条款
- 📌 注明来源
- 📌 共享修改
- 📌 不用于商业目的

### 5.2 引用来源

本项目基于：
- 刘河生教授团队研究成果（Nature, 2026）
- 公开医学文献
- 开源技术文档

引用时请尊重原作者权益。

---

## 六、隐私保护

### 6.1 不收集信息

本项目：
- 不收集个人信息
- 不追踪用户行为
- 不存储使用数据
- 不共享任何信息

### 6.2 社区交流

在社区交流中：
- 请保护个人隐私
- 不要透露真实身份
- 不要分享敏感信息
- 谨慎对待陌生人

---

## 七、更新与通知

### 7.1 文档更新

本免责声明可能随时更新，请定期查看最新版本。

### 7.2 重大变更

如有重大变更，将在项目主页公告。

---

## 八、联系方式

如有疑问，请通过以下方式联系：

- 项目主页：https://github.com/scj009999/TLSR8269_SixChannel_Pulse_Generator
- 技术交流：请在GitHub Issues中讨论

**注意：不提供医疗咨询，不提供私人联系方式。**

---

## 九、最终确认

### 使用本项目前，请确认：

- [ ] 我已阅读并理解本免责声明
- [ ] 我知道本项目不是医疗设备销售
- [ ] 我知道本项目不提供医疗建议
- [ ] 我会咨询医生后再做任何决定
- [ ] 我会自行承担所有风险
- [ ] 我不会将本项目用于商业目的

---

## 十、附则

### 10.1 适用法律

本免责声明适用中华人民共和国法律。

### 10.2 争议解决

如有争议，应友好协商解决；协商不成，提交项目所在地法院诉讼解决。

### 10.3 完整性

本免责声明构成完整协议，取代之前所有口头或书面协议。

---

**最后更新：** 2026年5月26日  
**版本：** v1.0  
**状态：** 生效中

---

> **再次提醒：**
> 
> 本项目纯粹为技术开源，不构成任何医疗建议。
> 
> 任何健康问题，请务必咨询专业医生。
> 
> 自行使用本项目资料，风险自负。
