scj009999/TLSR8269_SixChannel_Pulse_Generator/docs/DOCTOR_RECRUITMENT.md

# 医生招募令 - 开源经颅脉冲治疗仪项目

> ⚠️ **重要声明：本项目为纯公益项目，不收取任何费用。医生参与纯属自愿，以志愿者形式，无任何报酬要求。**

## 我们是谁

我们是一群帕金森患者、家属和技术开发者，正在发起一个**完全开源、纯公益**的经颅脉冲治疗仪项目。目标是打破医疗暴利，让治疗成本从15万/年降至99元/台。

**项目主页**：https://github.com/scj009999/TLSR8269_SixChannel_Pulse_Generator

**本项目性质**：
- ✅ 完全开源，代码和设计免费公开
- ✅ 纯公益，不收取任何形式的费用
- ❌ 禁止商业用途
- ❌ 禁止向患者收费
- ❌ 不是医疗机构，不提供医疗服务

---

## 为什么需要您

### 患者的困境
- 商用设备售价1-3万元，医院治疗年费15万+
- 普通百姓难以承受，只能放弃治疗
- 设备黑盒设计，患者无法了解原理
- 参数固定，无法个性化调整

### 您的价值
- **医学指导**：确保治疗方案安全有效
- **临床验证**：开展临床试验，收集数据
- **患者教育**：指导患者正确使用
- **学术贡献**：发表论文，推动领域发展

---

## 项目优势

| 对比项 | 商用设备 | 开源方案 |
|---|---|---|
| 设备价格 | ¥15,000-30,000 | **¥99** |
| 治疗年费 | ¥150,000 | **¥0** |
| 透明度 | 黑盒 | **完全开源** |
| 可定制 | 否 | **是** |
| 数据归属 | 厂商 | **患者** |

---

## 我们需要这样的您

### 专业要求
- **神经内科医生**：帕金森病诊疗经验
- **康复科医生**：神经康复专业背景
- **精神科医生**：认知功能评估经验
- **研究人员**：临床试验设计经验

### 时间承诺
- **顾问角色**：每月2-4小时，远程参与
- **临床研究者**：根据试验安排，可协商
- **技术评审**：按需参与，灵活安排

### 工作地点
- 远程为主，线上会议
- 临床试验在合作医院进行
- 年度线下交流（自愿参加）

---

## 您将获得

### 学术回报
- **论文署名**：临床试验论文共同作者
- **学术声誉**：开源医疗领域的先驱
- **数据共享**：获取去标识化治疗数据
- **合作网络**：连接患者、开发者、研究者

### 社会价值
- **帮助患者**：让治疗触手可及
- **推动公平**：消除经济门槛
- **医疗创新**：探索开源医疗模式
- **历史意义**：参与改变医疗格局

### 实际收益
- **设备赠送**：免费获得治疗仪原型（用于研究）
- **培训支持**：技术培训、学术会议（自费或项目赞助）
- **荣誉认证**：项目贡献者证书
- **社会价值**：帮助千万患者，推动医疗公平

> ⚠️ **注意：本项目为纯公益项目，不支付任何形式的报酬。医生参与纯属自愿，以志愿者形式。**

---

## 参与方式

### 第一步：了解项目
- 访问GitHub仓库，阅读项目文档
- 查看硬件设计、软件代码、安全规范
- 了解项目背景、目标、进展

### 第二步：填写申请
发送邮件至：[项目邮箱]

邮件内容：
```
主题：【医生招募】姓名-医院-科室

1. 基本信息
   - 姓名：
   - 医院：
   - 科室：
   - 职称：
   - 从业年限：

2. 专业背景
   - 帕金森病诊疗经验（年）：
   - 经颅刺激治疗经验：
   - 临床试验经验：
   - 发表相关论文（篇）：

3. 参与意向
   - 希望参与的角色：
     □ 医学顾问
     □ 临床研究者
     □ 技术评审
     □ 患者教育
   - 可投入时间（小时/月）：
   - 希望获得的回报：

4. 意见建议
   - 对项目的建议：
   - 对安全性的看法：
   - 其他想法：
```

### 第三步：面试沟通
- 线上视频会议（30分钟）
- 项目团队介绍
- 解答疑问
- 确定合作方式

### 第四步：正式加入
- 签署保密协议（保护患者隐私）
- 签署贡献者协议（明确知识产权）
- 加入项目群组
- 开始参与工作

---

## 当前进展

### 已完成
- ✅ 硬件设计（TLSR8269六路脉冲发生器）
- ✅ 软件代码（含安全机制）
- ✅ 靶点定位系统
- ✅ 成本分析（¥99目标）
- ✅ 开源许可证（GPL v3 + CERN OHL v2）

### 进行中
- 🔄 药监局审批申请
- 🔄 PCB原型制作
- 🔄 手机APP开发
- 🔄 医生招募（就是现在！）

### 待启动
- ⏳ 临床试验设计
- ⏳ 伦理审查申请
- ⏳ 患者招募
- ⏳ 数据分析

---

## 常见问题

### Q1：项目是否合法？
A：我们正在申请国家药监局创新医疗器械审批。在获批前，项目处于研究阶段，所有使用需签署知情同意书。

### Q2：安全性如何保障？
A：多重安全机制：硬件限流（<5mA）、光耦隔离（5000V）、急停按钮、看门狗、实时监测。参数硬编码限制，不可软件绕过。

### Q3：我的时间投入会得到回报吗？
A：我们承诺：论文署名、数据共享、顾问费（象征性）、设备赠送。更重要的是，您将帮助千万患者。

### Q4：如果项目失败怎么办？
A：即使项目未能商业化，开源代码和设计仍将保留，供后人参考改进。您的贡献不会被浪费。

### Q5：如何保护我的声誉？
A：项目完全透明，所有决策公开。您可以随时退出，我们会尊重您的选择并删除相关信息。

---

## 联系我们

- **GitHub**：https://github.com/scj009999/TLSR8269_SixChannel_Pulse_Generator
- **Issues**：提交问题或建议
- **Discussions**：参与讨论
- **邮件**：[项目邮箱]

---

## 致敬

**每一位参与这个项目的医生，都是在用专业知识守护生命尊严。**

您不仅是在参与一个开源项目，更是在参与一场医疗公平的革命。

**让我们携手，让治疗触手可及。**

---

*本项目完全开源，不收取任何形式的费用*
*采用 GPL v3 + CERN OHL v2 许可证*
