scj009999/TLSR8269_SixChannel_Pulse_Generator/docs/FCA_EBOOK.md

# 帕金森病治疗知情选择手册

## 一本给患者和家属的实用指南

---

**作者**：开源医疗项目团队  
**版本**：V1.0  
**日期**：2026-05-13  
**协议**：CC BY-SA 4.0（知识共享署名-相同方式共享）

---

## 目录

1. 写在前面
2. 了解帕金森病
3. 治疗方案概览
4. 药物治疗详解
5. 手术治疗（DBS）详解
6. 非侵入性刺激治疗
7. 中医综合调理
8. 开源设备介绍
9. 如何做出知情选择
10. 患者故事
11. 家属支持指南
12. 资源推荐
13. 结语

---

## 第一章：写在前面

### 1.1 为什么写这本书

前几天，一位帕友告诉我一个令人心痛的消息：

一位37岁的年轻病友，在接受脑深部电刺激手术（DBS）不到两年后，离开了我们。

更让人心寒的是，当有人在患者群里提醒大家关注手术风险时，被管理员踢出了群。

这让我意识到：**信息透明，有时候比治疗本身更重要。**

这本书的目的，就是帮助患者和家属：
- 了解全部治疗选择
- 做出知情决策
- 不再被信息封锁所害

### 1.2 我们的理念

> **"能帮一些人就帮一些人。"**
> 
> **"救一个人，胜造七级浮屠。"**

我们坚信：
- 患者有权了解全部真相
- 信息应该自由流动
- 医疗应该透明开放

### 1.3 免责声明

本书仅供信息参考，不构成医疗建议。

任何治疗决策请咨询专业医生。

使用任何设备需自行承担风险。

---

## 第二章：了解帕金森病

### 2.1 什么是帕金森病

帕金森病是一种常见的神经退行性疾病，主要影响运动系统。

**主要症状**：
- 静止性震颤
- 肌肉僵直
- 运动迟缓
- 姿势平衡障碍

**非运动症状**：
- 抑郁、焦虑
- 睡眠障碍
- 认知功能下降
- 自主神经功能障碍

### 2.2 疾病进展

| 阶段 | 特点 |
|---|---|
| **早期** | 单侧症状，轻微影响生活 |
| **中期** | 双侧症状，药物效果波动 |
| **晚期** | 严重残疾，药物效果减退 |

### 2.3 目前无法治愈

重要的事实：
- 目前没有治愈帕金森病的方法
- 各种治疗的目标是改善症状
- 提高生活质量是核心目标

---

## 第三章：治疗方案概览

### 3.1 四种主要方案

| 方案 | 原理 | 侵入性 | 费用 | 可逆性 |
|---|---|---|---|---|
| **药物治疗** | 补充多巴胺 | 无 | 中等 | 可逆 |
| **DBS手术** | 植入电极刺激脑核团 | 有 | 20-40万 | 部分 |
| **经颅电刺激** | 头皮电极微弱电流 | 无 | 较低 | 完全 |
| **中医调理** | 整体调理 | 无 | 低 | 可逆 |

### 3.2 选择原则

1. **知情同意**：了解全部信息
2. **个体化**：根据具体情况
3. **阶梯治疗**：从低风险开始
4. **联合应用**：多种方法结合
5. **专业指导**：在医生指导下进行

---

## 第四章：药物治疗详解

### 4.1 常用药物

| 药物类型 | 代表药物 | 作用 |
|---|---|---|
| 左旋多巴 | 美多芭、息宁 | 补充多巴胺 |
| 多巴胺受体激动剂 | 普拉克索、罗匹尼罗 | 模拟多巴胺 |
| MAO-B抑制剂 | 司来吉兰、雷沙吉兰 | 减少多巴胺分解 |
| COMT抑制剂 | 恩他卡朋 | 延长左旋多巴作用 |

### 4.2 药物治疗的优缺点

**优点**：
- 历史悠久，方案成熟
- 起效较快
- 便于调整剂量

**局限**：
- 长期使用可能出现运动并发症
- 不能阻止病情进展
- 部分患者效果逐渐减退

### 4.3 运动并发症

长期使用左旋多巴可能出现：
- 剂末现象
- 开关现象
- 异动症

---

## 第五章：手术治疗（DBS）详解

### 5.1 什么是DBS

脑深部电刺激（Deep Brain Stimulation）：
- 通过手术在大脑特定核团植入电极
- 电极连接植入胸部的脉冲发生器
- 通过电刺激调节异常神经活动

### 5.2 手术过程

1. **术前评估**：确定是否适合手术
2. **安装头架**：固定头部
3. **定位靶点**：通过影像确定电极位置
4. **植入电极**：测试效果
5. **植入脉冲发生器**：连接电极
6. **术后调试**：调整参数

### 5.3 需要考虑的因素

**优点**：
- 对部分患者效果显著
- 可减少药物剂量
- 技术不断进步

**需要考虑的因素**：
- 需要开颅手术
- 存在手术风险
- 术后需长期随访调试
- 费用较高
- 并非适合所有患者

### 5.4 手术风险

| 风险 | 发生率 | 说明 |
|---|---|---|
| 感染 | 1-5% | 可能需要取出设备 |
| 出血 | 1-3% | 可能危及生命 |
| 硬件故障 | 5-10% | 需更换设备 |
| 效果不佳 | 10-20% | 需调整或放弃 |

> **重要提示**：手术决策需充分评估，选择有经验的医疗团队。

### 5.5 适合人群

- 药物效果减退
- 出现严重运动并发症
- 年龄一般不超过75岁
- 无严重认知障碍
- 身体状况可耐受手术

### 5.6 不适合人群

- 有严重认知障碍
- 有严重抑郁或精神症状
- 有出血倾向
- 有严重心肺疾病
- 无法配合术后随访

---

## 第六章：非侵入性刺激治疗

### 6.1 什么是经颅电刺激

**经颅直流电刺激（tDCS）**：
- 通过头皮电极施加微弱直流电
- 调节大脑皮层兴奋性

**经颅交流电刺激（tACS）**：
- 通过头皮电极施加交流电
- 调节大脑振荡活动

### 6.2 治疗原理

- 微弱电流改变神经元膜电位
- 调节神经可塑性
- 改善神经网络功能

### 6.3 优缺点

**优点**：
- 非侵入性，安全性高
- 可居家使用
- 费用相对较低
- 可与其他治疗联合
- 完全可逆

**局限**：
- 效果个体差异大
- 需长期坚持
- 最佳参数仍在研究中

### 6.4 安全性

多项研究显示：
- 安全性良好
- 副作用轻微（皮肤刺痛、发红）
- 无严重不良事件报告

### 6.5 研究进展

- 多项研究显示对运动症状有改善
- 居家使用方案逐渐成熟
- 最佳刺激参数仍在探索

---

## 第七章：中医综合调理

### 7.1 中医理论

帕金森病在中医属于"颤证"、"痉证"范畴：
- 肝肾阴虚，筋脉失养
- 气血不足，脑髓失充
- 痰瘀阻络，筋脉拘急

### 7.2 治疗方法

**中药治疗**：
- 滋补肝肾
- 益气养血
- 化痰通络
- 活血化瘀

**针灸治疗**：
- 百会、四神聪
- 风池、曲池
- 合谷、太冲
- 阳陵泉、足三里

**推拿按摩**：
- 放松肌肉
- 改善循环
- 缓解僵直

**气功导引**：
- 太极拳
- 八段锦
- 五禽戏

### 7.3 优缺点

**优点**：
- 整体调理
- 副作用较少
- 可改善整体状态
- 可与其他治疗联合

**局限**：
- 效果较慢
- 需找到有经验的中医师
- 个体化程度高

---

## 第八章：开源设备介绍

### 8.1 项目背景

我们是一个开源医疗项目团队，正在开发一种低成本、非侵入性的神经调控设备。

### 8.2 设计目标

| 目标 | 说明 |
|---|---|
| **可及性** | 让低收入患者也能获得治疗 |
| **透明性** | 硬件软件完全开源 |
| **安全性** | 多重保护机制 |
| **教育性** | 帮助患者了解治疗 |

### 8.3 技术参数

| 参数 | 规格 |
|---|---|
| 输出通道 | 6路 |
| 频率范围 | 1Hz - 8MHz |
| 占空比精度 | 0.01% |
| 电流限制 | ≤2mA |
| 电压限制 | ≤24V |
| 通信接口 | UART/I2C |
| 供电 | 3.3V |

### 8.4 安全设计

| 保护机制 | 说明 |
|---|---|
| 电流限制 | 硬件+软件双重限制 |
| 阻抗检测 | 自动检测接触阻抗 |
| 急停按钮 | 一键切断输出 |
| 超时保护 | 自动关闭 |
| 隔离设计 | 医疗级光耦隔离 |

### 8.5 使用前提

1. 已确诊帕金森病
2. 已与医生讨论
3. 了解设备局限性
4. 愿意承担使用风险
5. 能正确使用设备

### 8.6 项目定位

- 是**研究性**的辅助工具
- 是**补充性**的治疗选择
- **不替代**正规医疗
- 需要**专业指导**下使用

---

## 第九章：如何做出知情选择

### 9.1 决策前需了解的问题

#### 关于疾病
- [ ] 我的病情处于哪个阶段？
- [ ] 主要症状是什么？
- [ ] 预期病程如何？

#### 关于治疗方案
- [ ] 有哪些可选方案？
- [ ] 每种方案的原理是什么？
- [ ] 预期效果如何？
- [ ] 可能的风险和副作用？
- [ ] 费用多少？医保覆盖吗？
- [ ] 需要多长时间？
- [ ] 是否可逆？

#### 关于自身情况
- [ ] 我的年龄和整体健康状况？
- [ ] 我的经济状况？
- [ ] 我的家庭支持系统？
- [ ] 我对风险的接受程度？
- [ ] 我的治疗目标是什么？

### 9.2 需要问医生的问题

#### 关于手术
1. 我是否适合手术？
2. 手术团队的经验如何？
3. 可能的并发症有哪些？发生率多少？
4. 术后需要多少次调试？
5. 硬件寿命多长？更换费用？
6. 如果效果不佳怎么办？

#### 关于非侵入性治疗
1. 这种治疗适合我的病情吗？
2. 在哪里可以接受正规治疗？
3. 居家使用的安全性如何？
4. 需要多长时间看到效果？

### 9.3 决策矩阵

| 考虑因素 | 权重 | 方案A | 方案B | 方案C |
|---|---|---|---|---|
| 安全性 | 高 | ⭐⭐⭐ | ⭐⭐ | ⭐⭐⭐⭐ |
| 有效性 | 高 | ⭐⭐⭐ | ⭐⭐⭐⭐ | ⭐⭐ |
| 费用 | 中 | ⭐⭐⭐⭐ | ⭐⭐ | ⭐⭐⭐⭐⭐ |
| 便利性 | 中 | ⭐⭐⭐ | ⭐⭐ | ⭐⭐⭐⭐ |
| 可逆性 | 高 | ⭐⭐⭐⭐⭐ | ⭐⭐ | ⭐⭐⭐⭐⭐ |
| **综合评分** | | | | |

---

## 第十章：患者故事

### 10.1 案例一：早期选择

> **背景**：52岁确诊，早期症状轻微
> 
> **选择**：药物 + 生活方式调整 + 非侵入性刺激
> 
> **理由**：
> - 希望延缓进展
> - 避免过早侵入性治疗
> - 经济负担可控
> 
> **结果**：症状稳定，生活质量良好

### 10.2 案例二：中期调整

> **背景**：65岁，药物效果减退
> 
> **选择**：优化药物 + 考虑手术评估
> 
> **过程**：
> - 咨询多位专家
> - 充分了解手术风险
> - 评估自身条件
> 
> **结果**：选择继续药物调整，暂缓手术

### 10.3 案例三：综合方案

> **背景**：70岁，多种症状
> 
> **选择**：药物 + 中医调理 + 康复训练
> 
> **理由**：
> - 整体调理
> - 减少药物剂量
> - 改善整体状态
> 
> **结果**：症状改善，精神状态好转

---

## 第十一章：家属支持指南

### 11.1 如何帮助患者决策

1. **收集信息**：帮助整理各种方案资料
2. **陪同就诊**：记录医生建议
3. **情感支持**：尊重患者选择
4. **经济规划**：评估长期费用
5. **日常照护**：协助治疗执行

### 11.2 需要注意的误区

| 误区 | 正确做法 |
|---|---|
| 替患者做决定 | 帮助患者了解信息，尊重选择 |
| 盲目追求最新技术 | 选择适合患者的方案 |
| 忽视心理因素 | 关注患者的情绪和意愿 |
| 过度保护 | 鼓励患者参与决策 |

### 11.3 自我照顾

照顾患者的同时，家属也要注意：
- 保持自己的身心健康
- 寻求社会支持
- 适当休息放松
- 不要独自承担所有压力

---

## 第十二章：资源推荐

### 12.1 权威组织

- 国际帕金森与运动障碍协会（MDS）
- 中国帕金森病联盟
- 各地三甲医院神经内科

### 12.2 信息平台

- 国家卫健委官网
- 中华医学会神经病学分会
- 正规医学期刊

### 12.3 患者社区

- 寻找开放、包容的讨论环境
- 关注信息共享而非商业推广
- 保护个人隐私

### 12.4 本项目

- GitHub: https://github.com/scj009999/TLSR8269_SixChannel_Pulse_Generator
- 特点：开源、非商业、公益

---

## 第十三章：结语

> **"知情选择是患者的权利，信息透明是医疗的底线。"**

每一位患者都值得：
- 了解全部真相
- 获得平等信息
- 做出自主决策
- 得到尊重和支持

无论选择哪种方案，希望每一位患者都能找到适合自己的道路。

---

## 附录

### 附录A：术语表

| 术语 | 解释 |
|---|---|
| DBS | 脑深部电刺激 |
| tDCS | 经颅直流电刺激 |
| tACS | 经颅交流电刺激 |
| 异动症 | 不自主运动 |
| 剂末现象 | 药效消退前症状加重 |

### 附录B：参考资料

- 国际帕金森与运动障碍协会指南
- 中国帕金森病治疗指南
- 经颅电刺激安全性研究

### 附录C：决策工作表

（见第九章9.1和9.2）

---

**免责声明**：本书仅供信息参考，不构成医疗建议。任何治疗决策请咨询专业医生。使用任何设备需自行承担风险。

---

*本书遵循开放、透明、非商业原则。*
*欢迎转载，请注明出处。*
