scj009999/TLSR8269_SixChannel_Pulse_Generator/docs/NMPA_EMAIL_DRAFT.md

# 致国家药品监督管理局邮件草稿

## 邮件信息

**收件人**：nmpa@nmpa.gov.cn（请以官网最新邮箱为准）
**抄送**：
- 各省药监局邮箱
- 卫健委相关邮箱
- 中国帕金森联盟

**主题**：【创新医疗器械申请】开源经颅脉冲治疗仪项目 - 为帕金森患者提供可负担的治疗方案

---

## 邮件正文

尊敬的国家药品监督管理局领导：

您好！

我是一名帕金森病患者，自[患病年份]年确诊以来，经历了从震惊、绝望到接受、抗争的心路历程。在求医过程中，我深刻体会到了治疗费用的沉重负担——商用经颅脉冲治疗设备售价1-3万元，医院治疗年费超过15万元，这对于普通工薪家庭来说是难以承受之重。

更让我痛心的是，近期市场上出现了大量仿制设备，利用患者的绝望心理谋取暴利。这些设备往往缺乏有效的安全监管，给患者带来了巨大的健康风险。

### 为什么发起这个项目？

2026年2月5日，昌平实验室刘河生教授团队的突破性研究成果发表于全球顶级期刊《自然》(Nature)，世界首次揭示了帕金森病的底层功能网络机制——"躯体认知环路"，并针对这一网络进行直接干预，在临床研究中取得良好成效（治疗2周后有效率55.5%，而传统方法仅22.2%）。

该成果已获批3项国家医疗器械注册证，在全国60余家医院规模化应用，累计治疗患者超3000例，整体有效率突破70%，被新华社、央视等多家央媒报道。

这一研究成果给了我希望，也让我意识到：如果能把这项技术开源，让每一个患者都能以可负担的成本获得治疗，将是一件多么有意义的事情。

于是，我发起了**开源经颅脉冲治疗仪项目**，目标是将治疗成本从15万/年降至99元/台。

### 项目技术方案

**硬件设计**：
- 主控芯片：Telink TLSR8269F512（国产，成本¥6.5）
- 6路独立PWM输出，频率1-200Hz，电流≤2mA
- 多重安全保护：硬件限流、光耦隔离、急停按钮、看门狗

**软件设计**：
- 完整开源代码，GPL v3许可证
- 实时安全监测：电流、阻抗、温度
- 参数硬编码限制，不可软件绕过

**安全机制**：
- 100Ω限流电阻，最大输出<5mA
- PC817光耦，5000V电气隔离
- 独立急停按钮，硬件中断
- 看门狗定时器，1秒超时复位
- ADC实时监测，每秒安全检查

### 项目现状

**已完成**：
- ✅ 硬件原理图和PCB设计
- ✅ 嵌入式软件代码
- ✅ 安全设计文档
- ✅ 靶点定位系统
- ✅ 成本分析（物料成本¥65）
- ✅ 开源许可证（GPL v3 + CERN OHL v2）

**进行中**：
- 🔄 药监局审批申请（就是这封邮件）
- 🔄 PCB原型制作
- 🔄 医生团队组建
- 🔄 临床试验方案设计

**项目主页**：https://github.com/scj009999/TLSR8269_SixChannel_Pulse_Generator

### 我们的请求

1. **审批指导**：希望药监局能指导我们完成创新医疗器械审批流程
2. **临床试验**：协调医院资源，支持我们开展临床试验
3. **标准制定**：参与制定经颅电刺激设备行业标准
4. **政策支持**：考虑将本项目纳入创新医疗器械特别审批程序

### 我们的承诺

1. **安全第一**：所有设计以安全为最高优先级
2. **完全开源**：硬件设计、软件代码、测试数据全部公开
3. **非营利性**：不以营利为目的，优先服务贫困患者
4. **透明运营**：所有决策公开，接受社会监督

### 附件

1. 项目详细技术文档
2. 硬件原理图和BOM清单
3. 安全设计规范
4. 刘河生教授Nature论文摘要及新闻报道
5. tACS/tDCS安全性临床研究摘要
6. 成本分析报告
7. 证据收集汇总（EVIDENCE_COLLECTION.md）

### 结语

**我们不是在申请一个产品的上市许可，而是在申请一个希望的通行证。**

每一个帕金森患者，无论贫富，都应该有权利获得有效的治疗。当前的天价治疗费用，让无数患者望而却步，让无数家庭陷入困境。

开源，是打破垄断的利器；
透明，是建立信任的基石；
共享，是技术普惠的桥梁。

恳请药监局支持这一创新尝试，让99元的开源治疗方案，能够合法、安全地服务于千万患者。

**这不仅是一个医疗器械的审批，更是一场医疗公平的实践。**

此致

敬礼！

开源经颅脉冲治疗仪项目发起人
束长江
[您的手机号]
scj009999@qq.com
2026年5月9日

---

## 发送建议

### 发送时间
- 工作日上午9:00-11:00
- 避开节假日

### 跟进方式
- 1周后未回复，可电话跟进
- 准备补充材料，随时响应要求

### 注意事项
- 保持礼貌，表达诚意
- 突出社会价值，而非技术细节
- 强调安全性和开源优势
- 准备好回答质疑

---

## 附件清单

发送邮件时，请将以下文件转为PDF作为附件：

1. `docs/OPEN_SOURCE_LETTER.md` → PDF
2. `hardware/schematic.md` → PDF
3. `docs/MEDICAL_SAFETY.md` → PDF
4. `docs/COST_ANALYSIS.md` → PDF
5. 刘河生教授论文（如有）

---

*祝您早日康复，项目顺利！*
