scj009999/TLSR8269_SixChannel_Pulse_Generator/docs/TCM_CHRONIC_DISEASE_PRESCRIPTIONS.md

# 慢性病固本培元方剂汇编

> **⚠️ 重要声明**
> 
> **本文档所列方剂仅供参考学习，不构成医疗建议。**
> 
> **有病不能乱投医！任何治疗方案必须在专业中医师指导下使用。**
> 
> **使用前请务必咨询医生，根据个人体质辨证施治。**
> 
> **孕妇、儿童、老年人及有特殊疾病者，更需谨慎。**

---

## 目录

1. [固本培元总则](#一固本培元总则)
2. [八珍汤系列](#二八珍汤系列)
3. [慢性病加减法](#三慢性病加减法)
4. [具体病症应用](#四具体病症应用)
5. [食疗与养生](#五食疗与养生)
6. [外治法](#六外治法)

---

## 一、固本培元总则

### 1.1 慢性病特点

慢性病患者长期身体消耗，常见：
- **气血亏虚**：面色萎黄，神疲乏力
- **阴阳失调**：畏寒肢冷或五心烦热
- **脏腑虚弱**：脾肾亏虚，精血不足
- **痰瘀互结**：久病入络，瘀血阻络

### 1.2 治疗原则

> **"急则治其标，缓则治其本"**
> 
> **"久病必虚，虚则补之"**

**固本培元四步法**：
```
第一步：补气养血 → 恢复元气
    ↓
第二步：健脾益肾 → 培补后天
    ↓
第三步：温阳散寒 → 祛除阴邪
    ↓
第四步：活血通络 → 防止瘀滞
```

### 1.3 首选方剂

**八珍汤**为固本培元首选：
- 气血双补，平和无偏
- 脾胃虚弱者亦可服用
- 加减灵活，适应面广

---

## 二、八珍汤系列

### 2.1 基础方：八珍汤

**来源**：《正体类要》

**组成**：
| 药物 | 剂量 | 功效 |
|---|---|---|
| 人参 | 6g | 大补元气 |
| 白术 | 9g | 健脾益气 |
| 白茯苓 | 9g | 健脾利湿 |
| 当归 | 9g | 补血活血 |
| 川芎 | 6g | 活血行气 |
| 白芍药 | 9g | 养血柔肝 |
| 熟地黄 | 12g | 滋阴补血 |
| 炙甘草 | 3g | 调和诸药 |
| 生姜 | 3片 | 温中散寒 |
| 大枣 | 3枚 | 补中益气 |

**功效**：益气补血

**主治**：气血两虚。症见面色苍白，气短懒言，四肢倦怠，心悸怔忡。

**用法**：水煎服，每日1剂，分2次温服。

---

### 2.2 八珍汤变化方

#### 变化一：十全大补汤

**组成**：八珍汤 + 黄芪12g + 肉桂3g

**功效**：温补气血

**主治**：气血不足，虚劳咳嗽，畏寒肢冷。

**变化要点**：
- + 黄芪：增强补气升阳
- + 肉桂：温阳散寒，鼓舞气血

---

#### 变化二：人参养荣汤

**组成**：八珍汤去川芎 + 黄芪12g + 肉桂3g + 五味子6g + 远志6g + 陈皮6g

**功效**：益气补血，养心安神

**主治**：心脾气血两虚，惊悸健忘，失眠多梦。

**变化要点**：
- - 川芎：去其辛散，防耗气
- + 黄芪、肉桂：温补气血
- + 五味子：收敛心气
- + 远志：安神益智
- + 陈皮：理气化痰

---

#### 变化三：泰山磐石散

**组成**：八珍汤去茯苓 + 黄芪15g + 续断9g + 黄芩6g + 砂仁3g + 糯米9g

**功效**：益气健脾，养血安胎

**主治**：气血虚弱，胎动不安。

**变化要点**：
- - 茯苓：去其渗利
- + 黄芪：补气安胎
- + 续断：补肾安胎
- + 黄芩：清热安胎
- + 砂仁：理气安胎
- + 糯米：补脾养胃

---

#### 变化四：八珍益母丸

**组成**：八珍汤 + 益母草15g

**功效**：益气养血，活血调经

**主治**：气血两虚，月经不调，痛经。

**变化要点**：
- + 益母草：活血调经，祛瘀生新

---

## 三、慢性病加减法

### 3.1 通用加减

#### 气虚明显

| 加法 | 剂量 | 功效 |
|---|---|---|
| 黄芪 | 15-30g | 补气升阳 |
| 党参 | 15g | 补中益气 |
| 山药 | 15g | 健脾益肾 |

#### 血虚明显

| 加法 | 剂量 | 功效 |
|---|---|---|
| 阿胶 | 9g（烊化） | 滋阴补血 |
| 枸杞 | 12g | 滋补肝肾 |
| 龙眼肉 | 12g | 补益心脾 |

#### 阴虚明显

| 加法 | 剂量 | 功效 |
|---|---|---|
| 麦冬 | 12g | 养阴润燥 |
| 生地 | 12g | 滋阴凉血 |
| 玉竹 | 12g | 养阴润燥 |

#### 阳虚明显

| 加法 | 剂量 | 功效 |
|---|---|---|
| 附子 | 6g（先煎） | 回阳救逆 |
| 肉桂 | 3g | 温阳散寒 |
| 干姜 | 6g | 温中散寒 |

#### 痰湿明显

| 加法 | 剂量 | 功效 |
|---|---|---|
| 陈皮 | 9g | 理气化痰 |
| 半夏 | 9g | 燥湿化痰 |
| 茯苓 | 加至15g | 健脾利湿 |

#### 瘀血明显

| 加法 | 剂量 | 功效 |
|---|---|---|
| 桃仁 | 9g | 活血祛瘀 |
| 红花 | 6g | 活血通经 |
| 丹参 | 15g | 活血祛瘀 |

---

### 3.2 特殊加减

#### 脑梗塞加味

**用户经验**：八珍汤 + 冰片0.1g

**分析**：
- 冰片：开窍醒神，芳香走窜
- 0.1g：微量使用，防耗气

**完整加味**：
| 加法 | 剂量 | 功效 |
|---|---|---|
| 冰片 | 0.1g（冲服） | 开窍醒神 |
| 杭菊花 | 9g | 平肝明目 |
| 龙骨 | 15g（先煎） | 平肝潜阳 |
| 牡蛎 | 15g（先煎） | 软坚散结 |
| 天麻 | 9g | 平肝熄风 |
| 钩藤 | 12g（后下） | 清热平肝 |

**功效**：益气养血，平肝熄风，开窍醒神

**主治**：气血两虚，肝阳上亢，脑梗塞恢复期。

---

#### 渐冻人症加味

**用户经验**：加附子、炮姜、桂枝、龙眼肉、益智仁

**分析**：
- 附子、炮姜、桂枝：温阳散寒，回阳救逆
- 龙眼肉：补益心脾，养血安神
- 益智仁：温肾固精，缩尿止遗

**完整加味**：
| 加法 | 剂量 | 功效 |
|---|---|---|
| 附子 | 6g（先煎） | 回阳救逆 |
| 炮姜 | 6g | 温中散寒 |
| 桂枝 | 9g | 温阳通脉 |
| 龙眼肉 | 12g | 补益心脾 |
| 益智仁 | 9g | 温肾固精 |
| 鹿角胶 | 9g（烊化） | 温补肝肾 |
| 龟板胶 | 9g（烊化） | 滋阴潜阳 |
| 黄芪 | 30g | 补气升阳 |
| 当归 | 12g | 补血活血 |

**功效**：温补气血，益肾填精，通络起痿

**主治**：脾肾两虚，气血不足，肌肉萎缩。

---

## 四、具体病症应用

### 4.1 脑梗塞恢复期

#### 基础方：八珍汤加味

**组成**：
| 药物 | 剂量 | 功效 |
|---|---|---|
| 人参 | 6g | 大补元气 |
| 白术 | 9g | 健脾益气 |
| 茯苓 | 9g | 健脾利湿 |
| 当归 | 9g | 补血活血 |
| 川芎 | 6g | 活血行气 |
| 白芍 | 9g | 养血柔肝 |
| 熟地 | 12g | 滋阴补血 |
| 甘草 | 3g | 调和诸药 |
| 冰片 | 0.1g（冲服） | 开窍醒神 |
| 杭菊花 | 9g | 平肝明目 |
| 龙骨 | 15g（先煎） | 平肝潜阳 |
| 牡蛎 | 15g（先煎） | 软坚散结 |
| 天麻 | 9g | 平肝熄风 |
| 钩藤 | 12g（后下） | 清热平肝 |

**功效**：益气养血，平肝熄风，开窍醒神

**主治**：脑梗塞恢复期，气血两虚，肝阳上亢。

**用法**：水煎服，每日1剂，分2次温服。

**注意**：
- 冰片用量宜小，0.1g即可
- 附子、龙骨、牡蛎先煎30分钟
- 钩藤后下，煎煮5-10分钟

---

### 4.2 渐冻人症（肌痿）

#### 基础方：八珍汤加味

**组成**：
| 药物 | 剂量 | 功效 |
|---|---|---|
| 人参 | 6g | 大补元气 |
| 白术 | 9g | 健脾益气 |
| 茯苓 | 9g | 健脾利湿 |
| 当归 | 12g | 补血活血 |
| 川芎 | 6g | 活血行气 |
| 白芍 | 9g | 养血柔肝 |
| 熟地 | 12g | 滋阴补血 |
| 甘草 | 3g | 调和诸药 |
| 附子 | 6g（先煎） | 回阳救逆 |
| 炮姜 | 6g | 温中散寒 |
| 桂枝 | 9g | 温阳通脉 |
| 龙眼肉 | 12g | 补益心脾 |
| 益智仁 | 9g | 温肾固精 |
| 鹿角胶 | 9g（烊化） | 温补肝肾 |
| 龟板胶 | 9g（烊化） | 滋阴潜阳 |
| 黄芪 | 30g | 补气升阳 |

**功效**：温补气血，益肾填精，通络起痿

**主治**：渐冻人症，脾肾两虚，气血不足，肌肉萎缩。

**用法**：水煎服，每日1剂，分2次温服。

**注意**：
- 附子先煎30-60分钟，至口尝无麻感
- 鹿角胶、龟板胶烊化冲服
- 黄芪用量宜大，30-60g

---

### 4.3 帕金森病（颤证）

#### 基础方：八珍汤加味

**组成**：
| 药物 | 剂量 | 功效 |
|---|---|---|
| 人参 | 6g | 大补元气 |
| 白术 | 9g | 健脾益气 |
| 茯苓 | 9g | 健脾利湿 |
| 当归 | 9g | 补血活血 |
| 川芎 | 6g | 活血行气 |
| 白芍 | 15g | 养血柔肝 |
| 熟地 | 12g | 滋阴补血 |
| 甘草 | 3g | 调和诸药 |
| 天麻 | 9g | 平肝熄风 |
| 钩藤 | 12g（后下） | 清热平肝 |
| 全蝎 | 3g（研末冲服） | 搜风止痉 |
| 蜈蚣 | 1条（研末冲服） | 通络止痉 |
| 黄芪 | 15g | 补气升阳 |

**功效**：益气养血，平肝熄风，通络止痉

**主治**：帕金森病，气血两虚，肝风内动。

**用法**：水煎服，每日1剂，分2次温服。

**注意**：
- 全蝎、蜈蚣有毒，用量宜小
- 研末冲服，效果更佳
- 肝肾功能不全者慎用

---

### 4.4 老年痴呆（痴呆证）

#### 基础方：八珍汤加味

**组成**：
| 药物 | 剂量 | 功效 |
|---|---|---|
| 人参 | 6g | 大补元气 |
| 白术 | 9g | 健脾益气 |
| 茯苓 | 9g | 健脾利湿 |
| 当归 | 9g | 补血活血 |
| 川芎 | 6g | 活血行气 |
| 白芍 | 9g | 养血柔肝 |
| 熟地 | 12g | 滋阴补血 |
| 甘草 | 3g | 调和诸药 |
| 菖蒲 | 9g | 开窍化痰 |
| 远志 | 6g | 安神益智 |
| 郁金 | 9g | 行气解郁 |
| 丹参 | 15g | 活血祛瘀 |
| 枸杞 | 12g | 滋补肝肾 |

**功效**：益气养血，开窍化痰，安神益智

**主治**：老年痴呆，气血两虚，痰浊阻窍。

**用法**：水煎服，每日1剂，分2次温服。

**注意**：
- 郁金与丁香相畏，不宜同用
- 远志用量不宜过大，防致呕

---

### 4.5 重症肌无力（痿证）

#### 基础方：八珍汤加味

**组成**：
| 药物 | 剂量 | 功效 |
|---|---|---|
| 人参 | 6g | 大补元气 |
| 白术 | 9g | 健脾益气 |
| 茯苓 | 9g | 健脾利湿 |
| 当归 | 9g | 补血活血 |
| 川芎 | 6g | 活血行气 |
| 白芍 | 9g | 养血柔肝 |
| 熟地 | 12g | 滋阴补血 |
| 甘草 | 3g | 调和诸药 |
| 黄芪 | 30g | 补气升阳 |
| 升麻 | 6g | 升阳举陷 |
| 柴胡 | 6g | 疏肝升阳 |
| 陈皮 | 6g | 理气化痰 |
| 山药 | 15g | 健脾益肾 |

**功效**：益气养血，升阳举陷，健脾补肾

**主治**：重症肌无力，脾胃气虚，中气下陷。

**用法**：水煎服，每日1剂，分2次温服。

**注意**：
- 黄芪用量宜大，30-60g
- 升麻、柴胡用量宜小，3-6g

---

## 五、食疗与养生

### 5.1 八珍汤食疗方

#### 八珍炖鸡

**材料**：
- 老母鸡1只（约1000g）
- 人参6g（或党参15g）
- 白术9g
- 茯苓9g
- 当归9g
- 川芎6g
- 白芍9g
- 熟地12g
- 甘草3g
- 生姜3片
- 大枣5枚
- 料酒适量
- 盐适量

**做法**：
1. 老母鸡宰杀，去毛内脏，洗净
2. 药材洗净，装入纱布袋
3. 将鸡、药袋、生姜、大枣放入炖盅
4. 加清水适量，隔水炖3小时
5. 加盐调味即可

**功效**：益气养血，补虚强身

**适用**：气血两虚，久病体虚。

**注意**：感冒发热者暂停。

---

#### 八珍粥

**材料**：
- 人参3g（或党参10g）
- 白术6g
- 茯苓6g
- 当归6g
- 川芎3g
- 白芍6g
- 熟地9g
- 甘草2g
- 粳米100g
- 冰糖适量

**做法**：
1. 药材洗净，加水煎煮30分钟，去渣取汁
2. 粳米洗净，加入药汁煮粥
3. 粥成后加冰糖调味

**功效**：益气养血，健脾养胃

**适用**：气血两虚，脾胃虚弱。

**注意**：糖尿病患者去冰糖。

---

### 5.2 慢性病养生茶

#### 益气养血茶

**材料**：
- 黄芪10g
- 当归5g
- 枸杞10g
- 红枣3枚
- 龙眼肉10g

**做法**：
1. 材料洗净
2. 加水煮沸15分钟
3. 代茶饮用

**功效**：益气养血，安神定志

**适用**：气血两虚，失眠多梦。

---

#### 温阳散寒茶

**材料**：
- 附子3g（先煎）
- 干姜3g
- 桂枝5g
- 红枣3枚
- 甘草3g

**做法**：
1. 附子先煎30分钟
2. 加入其他材料，煮沸15分钟
3. 代茶饮用

**功效**：温阳散寒，回阳救逆

**适用**：阳虚畏寒，四肢不温。

**注意**：阴虚火旺者禁用。

---

## 六、外治法

### 6.1 艾灸法

#### 常用穴位

| 穴位 | 定位 | 功效 | 适用病症 |
|---|---|---|---|
| 百会 | 头顶正中 | 醒脑开窍 | 所有脑病 |
| 足三里 | 膝下3寸 | 健脾益气 | 重症肌无力 |
| 关元 | 脐下3寸 | 补肾固本 | 渐冻人症 |
| 气海 | 脐下1.5寸 | 益气培元 | 所有虚证 |
| 肾俞 | 第2腰椎棘突下 | 补肾壮阳 | 所有脑病 |
| 脾俞 | 第11胸椎棘突下 | 健脾益气 | 脾胃虚弱 |
| 肝俞 | 第9胸椎棘突下 | 疏肝理气 | 肝郁气滞 |

#### 操作方法

1. **温和灸**：点燃艾条，对准穴位，距离皮肤2-3cm，熏烤10-15分钟
2. **雀啄灸**：艾条上下移动，如鸟啄食，每穴5-10分钟
3. **回旋灸**：艾条左右回旋，扩大受热面积，每穴10-15分钟

**注意**：
- 防止烫伤
- 阴虚火旺者慎用
- 孕妇禁用腰腹部穴位

---

### 6.2 足浴法

#### 温肾壮阳方

**材料**：
- 艾叶30g
- 红花15g
- 生姜30g
- 花椒10g
- 附子10g（先煎）
- 桂枝15g

**做法**：
1. 将药物加水煮沸30分钟
2. 倒入足浴盆，加温水调至40-45℃
3. 浸泡双足20-30分钟
4. 每日1次

**功效**：温肾壮阳，活血通络

**适用**：阳虚畏寒，四肢不温。

**注意**：
- 水温不宜过高
- 时间不宜过长
- 糖尿病足患者慎用

---

### 6.3 按摩法

#### 头部按摩

**方法**：
1. **开天门**：两拇指从眉心交替推至发际，36次
2. **推坎宫**：两拇指从眉心分推至太阳穴，36次
3. **揉太阳**：按揉太阳穴，顺时针、逆时针各36次
4. **梳头**：十指从前额梳至后脑，36次

**功效**：醒脑开窍，安神定志

---

#### 腹部按摩

**方法**：
1. **摩腹**：手掌顺时针摩腹，36次
2. **揉中脘**：按揉中脘穴，顺时针、逆时针各36次
3. **揉神阙**：按揉肚脐，顺时针、逆时针各36次
4. **揉关元**：按揉关元穴，顺时针、逆时针各36次

**功效**：健脾益气，补肾固本

---

## 七、重要提示

### 7.1 用药原则

1. **辨证施治**：根据证型选择方剂
2. **个体化**：根据体质调整剂量
3. **循序渐进**：从小剂量开始，逐步调整
4. **长期坚持**：慢性病需长期治疗
5. **定期复查**：监测肝肾功能

### 7.2 禁忌事项

| 情况 | 注意 |
|---|---|
| 感冒发热 | 暂停补益药 |
| 腹泻 | 慎用滋腻药 |
| 失眠 | 晚上少服兴奋药 |
| 高血压 | 慎用升阳药 |
| 糖尿病 | 去冰糖、蜂蜜 |
| 阴虚火旺 | 慎用温阳药 |
| 痰湿内盛 | 慎用滋腻药 |

### 7.3 就医建议

**出现以下情况，请立即就医**：
- 症状加重或出现新症状
- 服药后出现不适
- 出现过敏反应
- 病情急剧变化

---

## 八、结语

> **"久病必虚，虚则补之"**
> 
> **"固本培元，正气存内，邪不可干"**

慢性病患者长期身体消耗，治疗当以**固本培元**为主：
- **八珍汤**为首选，气血双补，平和无偏
- **加减灵活**，根据病症调整
- **食疗辅助**，增强体质
- **外治配合**，疏通经络

**但请记住：有病不能乱投医！**

**任何治疗方案必须在专业中医师指导下使用。**

**本文档仅供学习参考，不构成医疗建议。**

---

*能帮一些人就帮一些人。*
*救一个人，胜造七级浮屠。*
