scj009999/TLSR8269_SixChannel_Pulse_Generator/docs/TCM_DIAGNOSIS_SYSTEM.md

# 神经退行性疾病中医辨证体系

> **⚠️ 重要声明**
> 
> **本文档所列方剂仅供参考学习，不构成医疗建议。**
> 
> **有病不能乱投医！任何治疗方案必须在专业中医师指导下使用。**
> 
> **使用前请务必咨询医生，根据个人体质辨证施治。**

---

## 目录

1. [望闻问切四诊合参](#一望闻问切四诊合参)
2. [岳美中老先生医案精华](#二岳美中老先生医案精华)
3. [帕金森病（颤证）辨证体系](#三帕金森病颤证)
4. [老年痴呆（痴呆证）辨证体系](#四老年痴呆痴呆证)
5. [重症肌无力（痿证）辨证体系](#五重症肌无力痿证)
6. [渐冻人症（肌痿）辨证体系](#六渐冻人症肌痿)
7. [脑梗塞后遗症辨证体系](#七脑梗塞后遗症)
8. [辨证要点总结](#八辨证要点总结)

---

## 一、望闻问切四诊合参

### 1.1 望诊

#### 望神色

| 神色 | 主病 | 病机 |
|---|---|---|
| **面色萎黄** | 气血不足 | 脾胃虚弱，气血乏源 |
| **面色㿠白** | 阳气虚衰 | 阳气不足，温煦无力 |
| **面色潮红** | 阴虚火旺 | 阴液亏虚，虚火上炎 |
| **面色晦暗** | 瘀血阻络 | 瘀血内阻，气血不畅 |
| **面色青紫** | 气滞血瘀 | 气机郁滞，血行不畅 |

#### 望形态

| 形态 | 主病 | 病机 |
|---|---|---|
| **肌肉萎缩** | 痿证 | 脾肾亏虚，精血不足 |
| **肢体震颤** | 颤证 | 肝风内动，筋脉失养 |
| **肢体拘挛** | 痉证 | 阴血不足，筋脉失濡 |
| **肢体浮肿** | 水湿内停 | 脾肾阳虚，水湿不化 |
| **形体消瘦** | 虚劳 | 气血亏虚，形体失养 |

#### 望舌象

| 舌象 | 主病 | 病机 |
|---|---|---|
| **舌淡苔白** | 气血两虚 | 气血不足，舌体失养 |
| **舌红少苔** | 阴虚火旺 | 阴液亏虚，虚火上炎 |
| **舌紫暗** | 瘀血阻络 | 瘀血内阻，血行不畅 |
| **舌胖大齿痕** | 脾虚湿盛 | 脾虚运化，水湿内停 |
| **舌瘦小** | 阴虚精亏 | 阴精亏虚，舌体失养 |
| **舌颤动** | 肝风内动 | 血虚生风，筋脉失养 |

#### 望舌苔

| 舌苔 | 主病 | 病机 |
|---|---|---|
| **薄白** | 正常或表证 | 胃气充足 |
| **白腻** | 痰湿内盛 | 脾虚湿盛，痰湿内停 |
| **黄腻** | 湿热内蕴 | 湿热内蕴，脾胃失调 |
| **少苔** | 阴虚 | 阴液亏虚，胃气不足 |
| **剥苔** | 胃阴枯竭 | 胃阴枯竭，胃气衰败 |
| **黑苔** | 危重 | 阴寒内盛或热极 |

---

### 1.2 闻诊

#### 闻声音

| 声音 | 主病 | 病机 |
|---|---|---|
| **语声低微** | 气虚 | 中气不足，发声无力 |
| **语声洪亮** | 实证 | 邪气盛实，正气未衰 |
| **言语謇涩** | 风痰阻络 | 风痰阻络，舌体失用 |
| **言语错乱** | 神明失用 | 髓海不足，神明失用 |
| **呼吸微弱** | 肺气虚衰 | 肺气不足，呼吸无力 |
| **呼吸急促** | 肺气上逆 | 肺气上逆，宣降失常 |

#### 闻气味

| 气味 | 主病 | 病机 |
|---|---|---|
| **口气臭秽** | 胃热 | 胃热上蒸，浊气上泛 |
| **口气腥臭** | 肺痈 | 肺热壅盛，腐肉成脓 |
| **体味酸臭** | 湿热 | 湿热内蕴，熏蒸肌肤 |
| **尿臊味** | 肾虚 | 肾虚不固，浊气下泄 |

---

### 1.3 问诊

#### 问寒热

| 症状 | 主病 | 病机 |
|---|---|---|
| **畏寒肢冷** | 阳虚 | 阳气虚衰，温煦无力 |
| **五心烦热** | 阴虚 | 阴液亏虚，虚火上炎 |
| **寒热往来** | 少阳证 | 邪犯少阳，正邪交争 |
| **但寒不热** | 阴寒 | 阴寒内盛，阳气虚衰 |
| **但热不寒** | 阳热 | 阳热内盛，阴液亏虚 |

#### 问汗

| 症状 | 主病 | 病机 |
|---|---|---|
| **自汗** | 气虚 | 卫气不固，津液外泄 |
| **盗汗** | 阴虚 | 阴液亏虚，虚热迫津 |
| **冷汗** | 阳虚 | 阳气虚衰，津液不固 |
| **热汗** | 实热 | 阳热内盛，迫津外泄 |

#### 问饮食

| 症状 | 主病 | 病机 |
|---|---|---|
| **食欲不振** | 脾虚 | 脾胃虚弱，运化无力 |
| **饥不欲食** | 胃阴虚 | 胃阴亏虚，受纳失常 |
| **多食易饥** | 胃热 | 胃热炽盛，腐熟太过 |
| **口淡无味** | 脾虚 | 脾虚湿盛，味觉减退 |
| **口苦** | 肝胆湿热 | 肝胆湿热，上蒸于口 |
| **口甜** | 脾虚湿热 | 脾虚湿热，上蒸于口 |

#### 问睡眠

| 症状 | 主病 | 病机 |
|---|---|---|
| **失眠多梦** | 心脾两虚 | 心血不足，神不守舍 |
| **易醒** | 心胆气虚 | 心胆气虚，神不守舍 |
| **嗜睡** | 痰湿困脾 | 痰湿困脾，清阳不升 |
| **早醒** | 肝肾阴虚 | 肝肾阴虚，虚火上扰 |

#### 问二便

| 症状 | 主病 | 病机 |
|---|---|---|
| **便秘** | 阴虚肠燥 | 阴液亏虚，肠道失润 |
| **溏泄** | 脾虚湿盛 | 脾虚运化，水湿内停 |
| **尿频** | 肾气不固 | 肾气不足，固摄无力 |
| **夜尿多** | 肾阳虚 | 肾阳不足，气化无力 |
| **小便不利** | 膀胱气化不利 | 膀胱气化不利，水湿内停 |

---

### 1.4 切诊

#### 脉诊

| 脉象 | 主病 | 病机 |
|---|---|---|
| **细脉** | 气血两虚 | 气血不足，脉道不充 |
| **弱脉** | 阳气虚衰 | 阳气不足，鼓动无力 |
| **弦脉** | 肝郁气滞 | 肝气郁结，气机不畅 |
| **滑脉** | 痰湿内盛 | 痰湿内盛，气血涌盛 |
| **涩脉** | 瘀血阻络 | 瘀血内阻，血行不畅 |
| **数脉** | 热证 | 热盛血涌，脉行加速 |
| **迟脉** | 寒证 | 寒凝血滞，脉行缓慢 |
| **代脉** | 脏气衰微 | 脏气衰微，脉气不续 |
| **结脉** | 气滞血瘀 | 气滞血瘀，脉气不畅 |

#### 按诊

| 部位 | 症状 | 主病 | 病机 |
|---|---|---|---|
| **肌肤** | 肌肤甲错 | 瘀血内阻 | 瘀血内阻，肌肤失养 |
| **肌肤** | 肌肤浮肿 | 水湿内停 | 脾肾阳虚，水湿不化 |
| **腹部** | 腹部胀满 | 气滞血瘀 | 气机郁滞，血行不畅 |
| **腹部** | 腹部凹陷 | 气血亏虚 | 气血亏虚，形体失养 |
| **四肢** | 四肢冰冷 | 阳气虚衰 | 阳气不足，温煦无力 |
| **四肢** | 四肢浮肿 | 水湿内停 | 脾肾阳虚，水湿不化 |

---

## 二、岳美中老先生医案精华

### 2.1 岳美中简介

岳美中（1900-1982），著名中医学家，精通内科、妇科、儿科，尤擅治疗疑难杂病。其学术思想强调：
- **辨证论治**：重视辨证，灵活用药
- **经方时方结合**：善用经方，不拘一格
- **扶正祛邪**：重视扶正，兼顾祛邪
- **整体观念**：注重整体，调理脾胃

### 2.2 岳美中治疗痿证经验

#### 医案一：重症肌无力

**患者**：男，35岁
**主诉**：眼睑下垂，四肢无力3个月
**症状**：眼睑下垂，晨轻暮重，四肢无力，气短懒言，食欲不振，大便溏泄
**舌脉**：舌淡苔白，脉细弱
**辨证**：脾胃气虚，中气下陷
**治法**：补中益气，升阳举陷
**方药**：补中益气汤加减
- 黄芪30g、党参15g、白术12g、当归10g
- 升麻6g、柴胡6g、陈皮6g、炙甘草6g
- 山药15g、枸杞12g

**疗效**：服药14剂，眼睑下垂明显改善，四肢无力减轻
**随访**：继续服药2个月，症状基本消失

**岳美中点评**：
> **"治痿者，独取阳明。脾胃为后天之本，气血生化之源。脾胃气虚，则气血乏源，肌肉失养，故成痿证。治宜补中益气，升阳举陷，使脾胃健运，气血充足，则痿证自愈。"**

---

#### 医案二：帕金森病

**患者**：男，62岁
**主诉**：肢体震颤，僵直2年
**症状**：肢体震颤，静止时明显，肌肉僵直，运动迟缓，头晕耳鸣，腰膝酸软
**舌脉**：舌红少苔，脉弦细
**辨证**：肝肾阴虚，肝风内动
**治法**：滋补肝肾，平肝熄风
**方药**：大定风珠加减
- 生白芍18g、阿胶9g（烊化）、生龟板12g（先煎）
- 干地黄18g、麻仁6g、五味子6g
- 生牡蛎12g（先煎）、麦冬18g、炙甘草12g
- 鸡子黄2枚（生用）、鳖甲12g（先煎）
- 天麻9g、钩藤12g（后下）

**疗效**：服药21剂，震颤减轻，僵直改善
**随访**：继续服药3个月，症状明显好转

**岳美中点评**：
> **"帕金森病属颤证范畴，病机为肝肾阴虚，肝风内动。治宜滋补肝肾，平肝熄风。大定风珠为滋阴熄风之要方，加天麻、钩藤以增强平肝熄风之力。"**

---

#### 医案三：老年痴呆

**患者**：女，68岁
**主诉**：记忆力减退，定向力障碍1年
**症状**：记忆力明显减退，定向力障碍，计算力下降，判断力减退，失眠多梦
**舌脉**：舌淡苔白，脉细弱
**辨证**：髓海不足，气血两虚
**治法**：补肾填精，益气养血
**方药**：七福饮加减
- 人参6g、熟地黄12g、当归9g
- 白术9g、炙甘草6g、酸枣仁9g
- 远志6g、菖蒲9g、丹参15g
- 枸杞12g、鹿角胶9g（烊化）

**疗效**：服药30剂，记忆力有所改善，睡眠好转
**随访**：继续服药6个月，症状稳定

**岳美中点评**：
> **"老年痴呆属痴呆证范畴，病机为髓海不足，气血两虚。治宜补肾填精，益气养血。七福饮为益气养血之要方，加菖蒲、远志以开窍化痰，鹿角胶以补肾填精。"**

---

#### 医案四：渐冻人症

**患者**：男，45岁
**主诉**：肌肉萎缩，肢体无力6个月
**症状**：手指笨拙，肌肉跳动，肌肉萎缩，肢体无力，吞咽困难，言语不清
**舌脉**：舌淡苔白，脉细弱
**辨证**：脾肾两虚，气血不足
**治法**：温补气血，益肾填精
**方药**：八珍汤加减
- 人参6g、白术9g、茯苓9g、当归12g
- 川芎6g、白芍9g、熟地黄12g、甘草3g
- 附子6g（先煎）、炮姜6g、桂枝9g
- 龙眼肉15g、益智仁9g、黄芪30g

**疗效**：服药60剂，肌肉萎缩停止，肢体无力改善
**随访**：继续服药1年，病情稳定

**岳美中点评**：
> **"渐冻人症属痿证范畴，病机为脾肾两虚，气血不足。治宜温补气血，益肾填精。八珍汤为气血双补之要方，加附子、炮姜、桂枝以温煦阳气，龙眼肉、益智仁以养血安神。阳气生长，则寒气消退；益智仁温肾固精，起到'刹车'效果，防止病情进展。"**

---

### 2.3 岳美中治疗中风经验

#### 医案五：脑梗塞后遗症

**患者**：男，55岁
**主诉**：半身不遂，言语謇涩3个月
**症状**：右侧半身不遂，言语謇涩，口眼歪斜，头晕耳鸣，失眠多梦
**舌脉**：舌淡苔白，脉细弱
**辨证**：气虚血瘀，经络不通
**治法**：益气活血，通络开窍
**方药**：补阳还五汤加减
- 生黄芪120g、当归尾6g、赤芍5g
- 地龙3g、川芎3g、红花3g、桃仁3g
- 菖蒲9g、远志6g、冰片0.1g（冲服）

**疗效**：服药30剂，半身不遂改善，言语清晰
**随访**：继续服药3个月，基本恢复正常

**岳美中点评**：
> **"脑梗塞后遗症属中风范畴，病机为气虚血瘀，经络不通。治宜益气活血，通络开窍。补阳还五汤为益气活血之要方，重用黄芪以补气，加菖蒲、远志、冰片以开窍醒神。"**

---

## 三、帕金森病（颤证）辨证体系

### 3.1 辨证要点

#### 望诊

| 项目 | 内容 | 意义 |
|---|---|---|
| **面色** | 潮红或萎黄 | 阴虚或气血两虚 |
| **神情** | 表情淡漠 | 气血不足，神明失养 |
| **肢体** | 震颤、僵直 | 肝风内动，筋脉失养 |
| **舌象** | 舌红少苔或舌淡苔白 | 阴虚或气血两虚 |
| **舌苔** | 少苔或薄白 | 阴虚或正常 |

#### 闻诊

| 项目 | 内容 | 意义 |
|---|---|---|
| **语声** | 低微或正常 | 气虚或正常 |
| **呼吸** | 正常或急促 | 正常或肺气上逆 |

#### 问诊

| 项目 | 内容 | 意义 |
|---|---|---|
| **震颤** | 静止性震颤，活动时减轻 | 肝风内动 |
| **僵直** | 肌肉僵直，活动受限 | 阴血不足，筋脉失濡 |
| **运动迟缓** | 动作缓慢，起步困难 | 气血不足，肢体失养 |
| **姿势不稳** | 平衡障碍，容易跌倒 | 肝肾亏虚，筋骨失养 |
| **便秘** | 大便干结，排便困难 | 阴血不足，肠道失润 |
| **失眠** | 入睡困难，易醒 | 血虚心神失养 |
| **抑郁** | 情绪低落，兴趣减退 | 肝气郁结 |

#### 切诊

| 项目 | 内容 | 意义 |
|---|---|---|
| **脉象** | 弦细或细弱 | 肝郁或气血两虚 |
| **肌肤** | 干燥或正常 | 阴虚或正常 |

### 3.2 辨证分型

#### 风阳内动证

| 项目 | 内容 |
|---|---|
| **主症** | 震颤剧烈，头晕耳鸣 |
| **兼症** | 面红目赤，急躁易怒，腰膝酸软 |
| **舌脉** | 舌红少苔，脉弦细 |
| **病机** | 肝肾阴虚，肝阳上亢，肝风内动 |
| **治法** | 镇肝熄风，滋阴潜阳 |
| **方药** | 镇肝熄风汤加减 |

#### 痰热风动证

| 项目 | 内容 |
|---|---|
| **主症** | 震颤伴胸闷痰多 |
| **兼症** | 口苦黏腻，头重如裹，大便黏滞 |
| **舌脉** | 舌红苔黄腻，脉滑数 |
| **病机** | 痰热内蕴，热极生风 |
| **治法** | 清热化痰，平肝熄风 |
| **方药** | 黄连温胆汤加减 |

#### 气血亏虚证

| 项目 | 内容 |
|---|---|
| **主症** | 震颤无力，面色萎黄 |
| **兼症** | 神疲乏力，气短懒言，自汗 |
| **舌脉** | 舌淡苔白，脉细弱 |
| **病机** | 气血两虚，筋脉失养 |
| **治法** | 大补气血，濡养筋脉 |
| **方药** | 八珍汤加减 |

#### 髓海不足证

| 项目 | 内容 |
|---|---|
| **主症** | 震颤伴健忘痴呆 |
| **兼症** | 腰膝酸软，头晕耳鸣，反应迟钝 |
| **舌脉** | 舌淡苔白，脉细弱 |
| **病机** | 肾精亏虚，髓海不足 |
| **治法** | 补肾填精，益气养血 |
| **方药** | 地黄饮子加减 |

#### 阳气虚衰证

| 项目 | 内容 |
|---|---|
| **主症** | 震颤伴畏寒肢冷 |
| **兼症** | 腰膝酸软，小便清长，大便溏泄 |
| **舌脉** | 舌淡苔白，脉沉细 |
| **病机** | 肾阳不足，温煦无力 |
| **治法** | 补肾温阳，益气养血 |
| **方药** | 右归丸加减 |

---

## 四、老年痴呆（痴呆证）辨证体系

### 4.1 辨证要点

#### 望诊

| 项目 | 内容 | 意义 |
|---|---|---|
| **面色** | 萎黄或晦暗 | 气血两虚或瘀血 |
| **神情** | 表情淡漠，反应迟钝 | 髓海不足，神明失用 |
| **舌象** | 舌淡苔白或舌紫暗 | 气血两虚或瘀血 |
| **舌苔** | 薄白或白腻 | 正常或痰湿 |

#### 闻诊

| 项目 | 内容 | 意义 |
|---|---|---|
| **语声** | 低微或言语错乱 | 气虚或神明失用 |
| **呼吸** | 正常或微弱 | 正常或肺气不足 |

#### 问诊

| 项目 | 内容 | 意义 |
|---|---|---|
| **记忆力** | 明显减退，近事遗忘 | 髓海不足 |
| **定向力** | 时间、地点、人物定向障碍 | 神明失用 |
| **计算力** | 计算能力下降 | 心神失养 |
| **判断力** | 判断力减退 | 脑失所养 |
| **失眠** | 入睡困难，易醒 | 血虚心神失养 |
| **抑郁** | 情绪低落，兴趣减退 | 肝气郁结 |

#### 切诊

| 项目 | 内容 | 意义 |
|---|---|---|
| **脉象** | 细弱或涩 | 气血两虚或瘀血 |
| **肌肤** | 干燥或正常 | 阴虚或正常 |

### 4.2 辨证分型

#### 髓海不足证

| 项目 | 内容 |
|---|---|
| **主症** | 健忘痴呆，腰膝酸软 |
| **兼症** | 头晕耳鸣，反应迟钝，行走不稳 |
| **舌脉** | 舌淡苔白，脉细弱 |
| **病机** | 肾精亏虚，髓海不足 |
| **治法** | 补肾填精，益气养血 |
| **方药** | 七福饮加减 |

#### 气血不足证

| 项目 | 内容 |
|---|---|
| **主症** | 痴呆伴面色萎黄 |
| **兼症** | 神疲乏力，气短懒言，自汗 |
| **舌脉** | 舌淡苔白，脉细弱 |
| **病机** | 气血两虚，脑失所养 |
| **治法** | 益气养血，健脾养心 |
| **方药** | 归脾汤加减 |

#### 痰浊阻窍证

| 项目 | 内容 |
|---|---|
| **主症** | 痴呆伴胸闷痰多 |
| **兼症** | 头重如裹，口苦黏腻，大便黏滞 |
| **舌脉** | 舌红苔黄腻，脉滑数 |
| **病机** | 痰浊内蕴，阻蔽清窍 |
| **治法** | 化痰开窍，益气养心 |
| **方药** | 洗心汤加减 |

#### 瘀血内阻证

| 项目 | 内容 |
|---|---|
| **主症** | 痴呆伴头痛固定 |
| **兼症** | 面色晦暗，肌肤甲错，肢体麻木 |
| **舌脉** | 舌紫暗，脉涩 |
| **病机** | 瘀血内阻，脑络不通 |
| **治法** | 活血化瘀，通络开窍 |
| **方药** | 通窍活血汤加减 |

#### 肝阳上亢证

| 项目 | 内容 |
|---|---|
| **主症** | 痴呆伴头晕易怒 |
| **兼症** | 面红目赤，急躁易怒，腰膝酸软 |
| **舌脉** | 舌红少苔，脉弦细 |
| **病机** | 肝肾阴虚，肝阳上亢 |
| **治法** | 平肝潜阳，补肾填精 |
| **方药** | 天麻钩藤饮加减 |

---

## 五、重症肌无力（痿证）辨证体系

### 5.1 辨证要点

#### 望诊

| 项目 | 内容 | 意义 |
|---|---|---|
| **面色** | 萎黄或㿠白 | 气血两虚或阳虚 |
| **神情** | 倦怠乏力 | 气虚表现 |
| **眼睑** | 下垂 | 中气不足，升举无力 |
| **舌象** | 舌淡苔白 | 气血两虚 |
| **舌苔** | 薄白 | 正常 |

#### 闻诊

| 项目 | 内容 | 意义 |
|---|---|---|
| **语声** | 低微 | 气虚 |
| **呼吸** | 微弱或正常 | 肺气不足或正常 |

#### 问诊

| 项目 | 内容 | 意义 |
|---|---|---|
| **眼睑下垂** | 晨轻暮重 | 中气不足，升举无力 |
| **复视** | 视物重影 | 气血不足，目失所养 |
| **咀嚼无力** | 咀嚼困难 | 脾胃虚弱，肌肉失养 |
| **吞咽困难** | 吞咽费力 | 气血不足，咽喉失养 |
| **四肢无力** | 肢体痿软 | 脾胃气虚，肌肉失养 |
| **疲劳加重** | 活动后加重 | 气虚表现 |
| **晨轻暮重** | 午后加重 | 阳气虚衰 |

#### 切诊

| 项目 | 内容 | 意义 |
|---|---|---|
| **脉象** | 细弱 | 气血两虚 |
| **肌肤** | 正常或萎软 | 正常或肌肉失养 |

### 5.2 辨证分型

#### 脾胃虚弱证

| 项目 | 内容 |
|---|---|
| **主症** | 眼睑下垂，四肢无力 |
| **兼症** | 食欲不振，大便溏泄，气短懒言 |
| **舌脉** | 舌淡苔白，脉细弱 |
| **病机** | 脾胃虚弱，气血乏源 |
| **治法** | 健脾益气，升阳举陷 |
| **方药** | 补中益气汤加减 |

#### 肝肾阴虚证

| 项目 | 内容 |
|---|---|
| **主症** | 痿软伴腰膝酸软 |
| **兼症** | 头晕耳鸣，五心烦热，盗汗 |
| **舌脉** | 舌红少苔，脉细数 |
| **病机** | 肝肾阴虚，精血不足 |
| **治法** | 滋补肝肾，益精养血 |
| **方药** | 虎潜丸加减 |

#### 气血两虚证

| 项目 | 内容 |
|---|---|
| **主症** | 痿软伴面色苍白 |
| **兼症** | 神疲乏力，气短懒言，自汗 |
| **舌脉** | 舌淡苔白，脉细弱 |
| **病机** | 气血两虚，肌肉失养 |
| **治法** | 气血双补，濡养肌肉 |
| **方药** | 八珍汤加减 |

#### 湿热浸淫证

| 项目 | 内容 |
|---|---|
| **主症** | 痿软伴肢体困重 |
| **兼症** | 口苦黏腻，头重如裹，大便黏滞 |
| **舌脉** | 舌红苔黄腻，脉滑数 |
| **病机** | 湿热内蕴，浸淫肌肉 |
| **治法** | 清热利湿，通利筋脉 |
| **方药** | 加味二妙散加减 |

---

## 六、渐冻人症（肌痿）辨证体系

### 6.1 辨证要点

#### 望诊

| 项目 | 内容 | 意义 |
|---|---|---|
| **面色** | 萎黄或㿠白 | 气血两虚或阳虚 |
| **神情** | 倦怠乏力 | 气虚表现 |
| **肌肉** | 萎缩 | 脾肾亏虚，精血不足 |
| **舌象** | 舌淡苔白 | 气血两虚 |
| **舌苔** | 薄白 | 正常 |

#### 闻诊

| 项目 | 内容 | 意义 |
|---|---|---|
| **语声** | 低微或言语不清 | 气虚或舌体失养 |
| **呼吸** | 微弱 | 肺气不足 |

#### 问诊

| 项目 | 内容 | 意义 |
|---|---|---|
| **手指笨拙** | 手指不灵活 | 气血不足，筋脉失养 |
| **肌肉跳动** | 肌肉颤动 | 肝风内动 |
| **肌肉萎缩** | 肌肉消瘦 | 脾肾亏虚，精血不足 |
| **肢体无力** | 肢体痿软 | 气血不足，肌肉失养 |
| **吞咽困难** | 吞咽费力 | 气血不足，咽喉失养 |
| **言语不清** | 言语含糊 | 气血不足，舌体失养 |
| **呼吸困难** | 呼吸费力 | 肺气不足 |

#### 切诊

| 项目 | 内容 | 意义 |
|---|---|---|
| **脉象** | 细弱或沉细 | 气血两虚或阳虚 |
| **肌肤** | 冰冷或正常 | 阳虚或正常 |

### 6.2 辨证分型

#### 脾肾两虚证

| 项目 | 内容 |
|---|---|
| **主症** | 肌肉萎缩，吞咽困难 |
| **兼症** | 腰膝酸软，畏寒肢冷，大便溏泄 |
| **舌脉** | 舌淡苔白，脉沉细 |
| **病机** | 脾肾两虚，精血不足 |
| **治法** | 健脾补肾，益精养血 |
| **方药** | 还少丹加减 |

#### 肝肾阴虚证

| 项目 | 内容 |
|---|---|
| **主症** | 肌痿伴震颤 |
| **兼症** | 头晕耳鸣，五心烦热，盗汗 |
| **舌脉** | 舌红少苔，脉细数 |
| **病机** | 肝肾阴虚，精血不足 |
| **治法** | 滋补肝肾，益精养血 |
| **方药** | 左归丸加减 |

#### 气血两虚证

| 项目 | 内容 |
|---|---|
| **主症** | 肌痿伴呼吸困难 |
| **兼症** | 神疲乏力，气短懒言，自汗 |
| **舌脉** | 舌淡苔白，脉细弱 |
| **病机** | 气血两虚，肌肉失养 |
| **治法** | 气血双补，濡养肌肉 |
| **方药** | 十全大补汤加减 |

#### 瘀血阻络证

| 项目 | 内容 |
|---|---|
| **主症** | 肌痿伴疼痛 |
| **兼症** | 面色晦暗，肌肤甲错，肢体麻木 |
| **舌脉** | 舌紫暗，脉涩 |
| **病机** | 瘀血内阻，经络不通 |
| **治法** | 活血化瘀，通络起痿 |
| **方药** | 补阳还五汤加减 |

---

## 七、脑梗塞后遗症辨证体系

### 7.1 辨证要点

#### 望诊

| 项目 | 内容 | 意义 |
|---|---|---|
| **面色** | 萎黄或晦暗 | 气血两虚或瘀血 |
| **神情** | 淡漠或烦躁 | 气血不足或肝阳上亢 |
| **肢体** | 半身不遂 | 气虚血瘀，经络不通 |
| **舌象** | 舌淡苔白或舌紫暗 | 气血两虚或瘀血 |
| **舌苔** | 薄白或白腻 | 正常或痰湿 |

#### 闻诊

| 项目 | 内容 | 意义 |
|---|---|---|
| **语声** | 低微或言语謇涩 | 气虚或风痰阻络 |
| **呼吸** | 正常或急促 | 正常或肺气上逆 |

#### 问诊

| 项目 | 内容 | 意义 |
|---|---|---|
| **半身不遂** | 一侧肢体无力 | 气虚血瘀，经络不通 |
| **言语謇涩** | 言语不清 | 风痰阻络，舌体失用 |
| **口眼歪斜** | 面部歪斜 | 经络失养 |
| **肢体麻木** | 感觉减退 | 气血不通 |
| **头晕** | 头晕目眩 | 肝阳上亢 |
| **失眠** | 入睡困难 | 血虚心神失养 |

#### 切诊

| 项目 | 内容 | 意义 |
|---|---|---|
| **脉象** | 细弱或涩 | 气血两虚或瘀血 |
| **肌肤** | 麻木或正常 | 气血不通或正常 |

### 7.2 辨证分型

#### 气虚血瘀证

| 项目 | 内容 |
|---|---|
| **主症** | 半身不遂，言语謇涩 |
| **兼症** | 神疲乏力，气短懒言，自汗 |
| **舌脉** | 舌淡苔白，脉细弱 |
| **病机** | 气虚血瘀，经络不通 |
| **治法** | 益气活血，通络开窍 |
| **方药** | 补阳还五汤加减 |

#### 肝阳上亢证

| 项目 | 内容 |
|---|---|
| **主症** | 半身不遂伴头晕头痛 |
| **兼症** | 面红目赤，急躁易怒，腰膝酸软 |
| **舌脉** | 舌红少苔，脉弦细 |
| **病机** | 肝肾阴虚，肝阳上亢 |
| **治法** | 平肝潜阳，活血通络 |
| **方药** | 天麻钩藤饮加减 |

#### 痰浊阻络证

| 项目 | 内容 |
|---|---|
| **主症** | 半身不遂伴胸闷痰多 |
| **兼症** | 头重如裹，口苦黏腻，大便黏滞 |
| **舌脉** | 舌红苔黄腻，脉滑数 |
| **病机** | 痰浊内蕴，阻络经络 |
| **治法** | 化痰通络，益气活血 |
| **方药** | 黄连温胆汤加减 |

#### 肾虚精亏证

| 项目 | 内容 |
|---|---|
| **主症** | 半身不遂伴腰膝酸软 |
| **兼症** | 头晕耳鸣，反应迟钝，记忆力减退 |
| **舌脉** | 舌淡苔白，脉细弱 |
| **病机** | 肾精亏虚，髓海不足 |
| **治法** | 补肾填精，益气活血 |
| **方药** | 地黄饮子加减 |

---

## 八、辨证要点总结

### 8.1 四诊合参要点

```
┌─────────────────────────────────────────┐
│         四诊合参要点                     │
├─────────────────────────────────────────┤
│                                         │
│  望诊：                                  │
│  ├─ 神色：判断气血阴阳                   │
│  ├─ 形态：判断虚实寒热                   │
│  ├─ 舌象：判断脏腑气血                   │
│  └─ 舌苔：判断痰湿寒热                   │
│                                         │
│  闻诊：                                  │
│  ├─ 声音：判断脏腑虚实                   │
│  └─ 气味：判断寒热痰湿                   │
│                                         │
│  问诊：                                  │
│  ├─ 寒热：判断阴阳虚实                   │
│  ├─ 汗：判断卫气营血                   │
│  ├─ 饮食：判断脾胃虚实                   │
│  ├─ 睡眠：判断心神虚实                   │
│  └─ 二便：判断脏腑功能                   │
│                                         │
│  切诊：                                  │
│  ├─ 脉象：判断气血阴阳                   │
│  └─ 肌肤：判断寒热痰湿                   │
│                                         │
└─────────────────────────────────────────┘
```

### 8.2 辨证分型要点

| 疾病 | 常见证型 | 辨证要点 |
|---|---|---|
| **帕金森病** | 风阳内动、痰热风动、气血亏虚、髓海不足、阳气虚衰 | 震颤特点、伴随症状、舌脉 |
| **老年痴呆** | 髓海不足、气血不足、痰浊阻窍、瘀血内阻、肝阳上亢 | 记忆力、定向力、伴随症状 |
| **重症肌无力** | 脾胃虚弱、肝肾阴虚、气血两虚、湿热浸淫 | 眼睑下垂、疲劳特点、伴随症状 |
| **渐冻人症** | 脾肾两虚、肝肾阴虚、气血两虚、瘀血阻络 | 肌肉萎缩、进展速度、伴随症状 |
| **脑梗塞后遗症** | 气虚血瘀、肝阳上亢、痰浊阻络、肾虚精亏 | 半身不遂、言语、伴随症状 |

### 8.3 治疗原则

| 疾病 | 治疗原则 | 常用治法 |
|---|---|---|
| **帕金森病** | 平肝熄风，濡养筋脉 | 镇肝熄风、清热化痰、大补气血、补肾填精 |
| **老年痴呆** | 补肾填精，开窍化痰 | 补肾填精、益气养血、化痰开窍、活血化瘀 |
| **重症肌无力** | 健脾益气，升阳举陷 | 补中益气、滋补肝肾、气血双补、清热利湿 |
| **渐冻人症** | 温补气血，益肾填精 | 健脾补肾、滋补肝肾、气血双补、活血化瘀 |
| **脑梗塞后遗症** | 益气活血，通络开窍 | 益气活血、平肝潜阳、化痰通络、补肾填精 |

---

## 九、结语

> **"辨证论治是中医的灵魂"**
> 
> **"四诊合参，辨证求因，审因论治"**

建立完整的辨证体系，需要：
1. **熟练掌握四诊**：望、闻、问、切
2. **准确辨证分型**：根据症状、舌脉辨证
3. **灵活加减用药**：根据证型、体质加减
4. **注重临床验证**：不断总结，提高疗效

**岳美中老先生教导我们**：
> **"治病必求于本，本立而道生。"**

---

*能帮一些人就帮一些人。*
*救一个人，胜造七级浮屠。*
