scj009999/TLSR8269_SixChannel_Pulse_Generator/docs/TCM_PRESCRIPTIONS.md

# 神经退行性疾病常用方剂汇编

> **⚠️ 重要声明**
> 
> **本文档所列方剂仅供参考学习，不构成医疗建议。**
> 
> **有病不能乱投医！任何治疗方案必须在专业中医师指导下使用。**
> 
> **使用前请务必咨询医生，根据个人体质辨证施治。**
> 
> **孕妇、儿童、老年人及有特殊疾病者，更需谨慎。**

---

## 目录

1. [帕金森病（颤证）方剂](#一帕金森病颤证)
2. [老年痴呆（痴呆证）方剂](#二老年痴呆痴呆证)
3. [重症肌无力（痿证）方剂](#三重症肌无力痿证)
4. [渐冻人症（肌痿）方剂](#四渐冻人症肌痿)
5. [通用调理方剂](#五通用调理方剂)
6. [食疗方](#六食疗方)
7. [外治法](#七外治法)

---

## 一、帕金森病（颤证）

### 1.1 镇肝熄风汤

**来源**：张锡纯《医学衷中参西录》

**组成**：
| 药物 | 剂量 | 功效 |
|---|---|---|
| 怀牛膝 | 30g | 引血下行 |
| 生赭石 | 30g（先煎） | 镇肝降逆 |
| 生龙骨 | 15g（先煎） | 平肝潜阳 |
| 生牡蛎 | 15g（先煎） | 软坚散结 |
| 生龟板 | 15g（先煎） | 滋阴潜阳 |
| 生杭芍 | 15g | 养血柔肝 |
| 玄参 | 15g | 滋阴清热 |
| 天冬 | 15g | 养阴润燥 |
| 川楝子 | 6g | 疏肝理气 |
| 生麦芽 | 6g | 疏肝和胃 |
| 茵陈 | 6g | 清利湿热 |
| 甘草 | 4.5g | 调和诸药 |

**功效**：镇肝熄风，滋阴潜阳

**主治**：肝阳上亢，肝风内动。症见头晕目眩，耳鸣耳聋，肢体震颤，或半身不遂。

**用法**：水煎服，每日1剂，分2次温服。

**注意**：脾胃虚寒者慎用。

---

### 1.2 天麻钩藤饮

**来源**：《中医内科杂病证治新义》

**组成**：
| 药物 | 剂量 | 功效 |
|---|---|---|
| 天麻 | 9g | 平肝熄风 |
| 钩藤 | 12g（后下） | 清热平肝 |
| 石决明 | 18g（先煎） | 平肝潜阳 |
| 山栀 | 9g | 清热泻火 |
| 黄芩 | 9g | 清热燥湿 |
| 川牛膝 | 12g | 引血下行 |
| 杜仲 | 9g | 补肝肾 |
| 益母草 | 9g | 活血利水 |
| 桑寄生 | 9g | 补肝肾 |
| 夜交藤 | 9g | 养心安神 |
| 朱茯神 | 9g | 宁心安神 |

**功效**：平肝熄风，清热活血，补益肝肾

**主治**：肝阳偏亢，肝风上扰。症见头痛，眩晕，失眠，震颤。

**用法**：水煎服，每日1剂，分2次温服。

**注意**：阴虚明显者加生地、麦冬。

---

### 1.3 大定风珠

**来源**：吴鞠通《温病条辨》

**组成**：
| 药物 | 剂量 | 功效 |
|---|---|---|
| 生白芍 | 18g | 养血柔肝 |
| 阿胶 | 9g（烊化） | 滋阴补血 |
| 生龟板 | 12g（先煎） | 滋阴潜阳 |
| 干地黄 | 18g | 滋阴养血 |
| 麻仁 | 6g | 润肠通便 |
| 五味子 | 6g | 收敛固涩 |
| 生牡蛎 | 12g（先煎） | 软坚散结 |
| 麦冬 | 18g | 养阴润燥 |
| 炙甘草 | 12g | 调和诸药 |
| 鸡子黄 | 2枚（生用） | 滋阴养血 |
| 鳖甲 | 12g（先煎） | 滋阴潜阳 |

**功效**：滋阴熄风

**主治**：真阴大亏，虚风内动。症见神倦瘈疭，脉气虚弱，舌绛苔少。

**用法**：水煎服，每日1剂，分2次温服。

**注意**：脾胃虚弱者慎用。

---

### 1.4 地黄饮子

**来源**：刘完素《黄帝素问宣明论方》

**组成**：
| 药物 | 剂量 | 功效 |
|---|---|---|
| 熟地黄 | 12g | 滋阴补肾 |
| 巴戟天 | 9g | 补肾阳 |
| 山茱萸 | 9g | 补肝肾 |
| 石斛 | 9g | 滋阴清热 |
| 肉苁蓉 | 9g | 补肾阳 |
| 附子 | 6g（先煎） | 回阳救逆 |
| 五味子 | 6g | 收敛固涩 |
| 官桂 | 6g | 温阳散寒 |
| 白茯苓 | 9g | 健脾利湿 |
| 麦门冬 | 9g | 养阴润燥 |
| 石菖蒲 | 9g | 开窍化痰 |
| 远志 | 9g | 安神益智 |
| 生姜 | 3片 | 温中散寒 |
| 大枣 | 3枚 | 补中益气 |
| 薄荷 | 3g | 疏散风热 |

**功效**：滋肾阴，补肾阳，开窍化痰

**主治**：喑痱。症见舌强不能言，足废不能用，口干不欲饮。

**用法**：水煎服，每日1剂，分2次温服。

**注意**：阴虚火旺者慎用。

---

## 二、老年痴呆（痴呆证）

### 2.1 七福饮

**来源**：《景岳全书》

**组成**：
| 药物 | 剂量 | 功效 |
|---|---|---|
| 人参 | 6g | 大补元气 |
| 熟地黄 | 12g | 滋阴补血 |
| 当归 | 9g | 补血活血 |
| 白术 | 9g | 健脾益气 |
| 炙甘草 | 6g | 调和诸药 |
| 酸枣仁 | 9g | 养心安神 |
| 远志 | 6g | 安神益智 |

**功效**：益气养血，安神定志

**主治**：气血亏虚，心神失养。症见健忘失眠，心悸怔忡。

**用法**：水煎服，每日1剂，分2次温服。

**注意**：痰湿内盛者慎用。

---

### 2.2 归脾汤

**来源**：薛己《正体类要》

**组成**：
| 药物 | 剂量 | 功效 |
|---|---|---|
| 白术 | 9g | 健脾益气 |
| 茯神 | 9g | 宁心安神 |
| 黄芪 | 12g | 补气升阳 |
| 龙眼肉 | 12g | 补益心脾 |
| 酸枣仁 | 12g | 养心安神 |
| 人参 | 6g | 大补元气 |
| 木香 | 6g | 行气止痛 |
| 炙甘草 | 3g | 调和诸药 |
| 当归 | 9g | 补血活血 |
| 远志 | 6g | 安神益智 |
| 生姜 | 3片 | 温中散寒 |
| 大枣 | 3枚 | 补中益气 |

**功效**：益气补血，健脾养心

**主治**：心脾气血两虚。症见心悸怔忡，健忘失眠，面色萎黄。

**用法**：水煎服，每日1剂，分2次温服。

**注意**：阴虚火旺者慎用。

---

### 2.3 洗心汤

**来源**：陈士铎《辨证录》

**组成**：
| 药物 | 剂量 | 功效 |
|---|---|---|
| 人参 | 6g | 大补元气 |
| 茯神 | 9g | 宁心安神 |
| 半夏 | 9g | 燥湿化痰 |
| 陈皮 | 6g | 理气化痰 |
| 神曲 | 9g | 消食和胃 |
| 甘草 | 3g | 调和诸药 |
| 附子 | 3g（先煎） | 回阳救逆 |
| 菖蒲 | 6g | 开窍化痰 |
| 生枣仁 | 9g | 养心安神 |

**功效**：化痰开窍，益气养心

**主治**：痰浊阻窍。症见痴呆，神思恍惚，言语颠倒。

**用法**：水煎服，每日1剂，分2次温服。

**注意**：阴虚火旺者慎用。

---

### 2.4 通窍活血汤

**来源**：王清任《医林改错》

**组成**：
| 药物 | 剂量 | 功效 |
|---|---|---|
| 赤芍 | 3g | 活血祛瘀 |
| 川芎 | 3g | 活血行气 |
| 桃仁 | 9g | 活血祛瘀 |
| 红花 | 9g | 活血通经 |
| 老葱 | 3根 | 通阳开窍 |
| 鲜姜 | 9g | 温中散寒 |
| 红枣 | 7枚 | 补中益气 |
| 麝香 | 0.15g（冲服） | 开窍醒神 |
| 黄酒 | 250g | 活血通络 |

**功效**：活血通窍

**主治**：瘀阻头面。症见头痛昏晕，耳聋，脱发，面色青紫。

**用法**：水煎服，每日1剂，分2次温服。

**注意**：孕妇禁用。麝香可用冰片代替。

---

## 三、重症肌无力（痿证）

### 3.1 补中益气汤

**来源**：李东垣《脾胃论》

**组成**：
| 药物 | 剂量 | 功效 |
|---|---|---|
| 黄芪 | 15g | 补气升阳 |
| 人参 | 10g | 大补元气 |
| 白术 | 10g | 健脾益气 |
| 炙甘草 | 5g | 调和诸药 |
| 当归 | 10g | 补血活血 |
| 陈皮 | 6g | 理气化痰 |
| 升麻 | 3g | 升阳举陷 |
| 柴胡 | 3g | 疏肝升阳 |
| 生姜 | 3片 | 温中散寒 |
| 大枣 | 5枚 | 补中益气 |

**功效**：补中益气，升阳举陷

**主治**：脾胃气虚。症见体倦乏力，食少便溏，内脏下垂。

**用法**：水煎服，每日1剂，分2次温服。

**注意**：阴虚火旺者慎用。

---

### 3.2 虎潜丸

**来源**：朱丹溪《丹溪心法》

**组成**：
| 药物 | 剂量 | 功效 |
|---|---|---|
| 黄柏 | 150g | 清热燥湿 |
| 龟板 | 120g | 滋阴潜阳 |
| 知母 | 60g | 清热泻火 |
| 熟地黄 | 60g | 滋阴补血 |
| 陈皮 | 60g | 理气化痰 |
| 白芍 | 60g | 养血柔肝 |
| 锁阳 | 45g | 补肾阳 |
| 虎骨 | 30g | 强筋健骨 |
| 干姜 | 15g | 温中散寒 |

**功效**：滋阴降火，强壮筋骨

**主治**：肝肾不足，阴虚内热。症见腰膝酸软，筋骨痿软。

**用法**：研末，炼蜜为丸，每丸9g，每日2次，每次1丸。

**注意**：虎骨可用牛骨代替。脾胃虚寒者慎用。

---

### 3.3 八珍汤

**来源**：薛己《正体类要》

**组成**：
| 药物 | 剂量 | 功效 |
|---|---|---|
| 人参 | 6g | 大补元气 |
| 白术 | 9g | 健脾益气 |
| 白茯苓 | 9g | 健脾利湿 |
| 当归 | 9g | 补血活血 |
| 川芎 | 6g | 活血行气 |
| 白芍药 | 9g | 养血柔肝 |
| 熟地黄 | 12g | 滋阴补血 |
| 炙甘草 | 3g | 调和诸药 |
| 生姜 | 3片 | 温中散寒 |
| 大枣 | 3枚 | 补中益气 |

**功效**：益气补血

**主治**：气血两虚。症见面色苍白，气短懒言，四肢倦怠。

**用法**：水煎服，每日1剂，分2次温服。

**注意**：感冒发热者暂停。

---

## 四、渐冻人症（肌痿）

### 4.1 还少丹

**来源**：杨倓《杨氏家藏方》

**组成**：
| 药物 | 剂量 | 功效 |
|---|---|---|
| 熟地黄 | 12g | 滋阴补血 |
| 山药 | 12g | 健脾益肾 |
| 牛膝 | 9g | 补肝肾 |
| 枸杞子 | 9g | 滋补肝肾 |
| 山茱萸 | 9g | 补肝肾 |
| 茯苓 | 9g | 健脾利湿 |
| 杜仲 | 9g | 补肝肾 |
| 远志 | 6g | 安神益智 |
| 五味子 | 6g | 收敛固涩 |
| 楮实子 | 9g | 补肾清肝 |
| 小茴香 | 6g | 温肾散寒 |
| 巴戟天 | 9g | 补肾阳 |
| 肉苁蓉 | 9g | 补肾阳 |
| 石菖蒲 | 6g | 开窍化痰 |

**功效**：补肾健脾，益精血

**主治**：脾肾两虚。症见腰膝酸软，神疲乏力，肌肉萎缩。

**用法**：水煎服，每日1剂，分2次温服。

**注意**：阴虚火旺者慎用。

---

### 4.2 左归丸

**来源**：张景岳《景岳全书》

**组成**：
| 药物 | 剂量 | 功效 |
|---|---|---|
| 熟地黄 | 240g | 滋阴补血 |
| 山药 | 120g | 健脾益肾 |
| 枸杞子 | 120g | 滋补肝肾 |
| 山茱萸 | 120g | 补肝肾 |
| 川牛膝 | 90g | 补肝肾 |
| 菟丝子 | 120g | 补肾益精 |
| 鹿角胶 | 120g | 温补肝肾 |
| 龟板胶 | 120g | 滋阴潜阳 |

**功效**：滋阴补肾，填精益髓

**主治**：真阴不足。症见头晕目眩，腰膝酸软，遗精滑泄。

**用法**：研末，炼蜜为丸，每丸9g，每日2次，每次1丸。

**注意**：脾虚便溏者慎用。

---

### 4.3 十全大补汤

**来源**：《太平惠民和剂局方》

**组成**：
| 药物 | 剂量 | 功效 |
|---|---|---|
| 人参 | 6g | 大补元气 |
| 肉桂 | 3g | 温阳散寒 |
| 川芎 | 6g | 活血行气 |
| 熟地黄 | 12g | 滋阴补血 |
| 茯苓 | 9g | 健脾利湿 |
| 白术 | 9g | 健脾益气 |
| 甘草 | 3g | 调和诸药 |
| 黄芪 | 12g | 补气升阳 |
| 当归 | 9g | 补血活血 |
| 白芍药 | 9g | 养血柔肝 |
| 生姜 | 3片 | 温中散寒 |
| 大枣 | 3枚 | 补中益气 |

**功效**：温补气血

**主治**：气血不足，虚劳咳嗽。症见面色萎黄，倦怠食少。

**用法**：水煎服，每日1剂，分2次温服。

**注意**：阴虚火旺者慎用。

---

### 4.4 补阳还五汤

**来源**：王清任《医林改错》

**组成**：
| 药物 | 剂量 | 功效 |
|---|---|---|
| 生黄芪 | 120g | 补气升阳 |
| 当归尾 | 6g | 活血祛瘀 |
| 赤芍 | 5g | 活血祛瘀 |
| 地龙 | 3g | 通络平喘 |
| 川芎 | 3g | 活血行气 |
| 红花 | 3g | 活血通经 |
| 桃仁 | 3g | 活血祛瘀 |

**功效**：补气活血通络

**主治**：气虚血瘀。症见半身不遂，口眼歪斜，语言謇涩。

**用法**：水煎服，每日1剂，分2次温服。

**注意**：阴虚阳亢者慎用。

---

## 五、通用调理方剂

### 5.1 六味地黄丸

**来源**：钱乙《小儿药证直诀》

**组成**：
| 药物 | 剂量 | 功效 |
|---|---|---|
| 熟地黄 | 24g | 滋阴补血 |
| 山茱萸 | 12g | 补肝肾 |
| 山药 | 12g | 健脾益肾 |
| 泽泻 | 9g | 利水渗湿 |
| 牡丹皮 | 9g | 清热凉血 |
| 茯苓 | 9g | 健脾利湿 |

**功效**：滋阴补肾

**主治**：肾阴亏损。症见头晕耳鸣，腰膝酸软，骨蒸潮热。

**用法**：研末，炼蜜为丸，每丸9g，每日2次，每次1丸。

**注意**：脾胃虚寒者慎用。

---

### 5.2 金匮肾气丸

**来源**：张仲景《金匮要略》

**组成**：
| 药物 | 剂量 | 功效 |
|---|---|---|
| 干地黄 | 24g | 滋阴补血 |
| 山药 | 12g | 健脾益肾 |
| 山茱萸 | 12g | 补肝肾 |
| 泽泻 | 9g | 利水渗湿 |
| 茯苓 | 9g | 健脾利湿 |
| 牡丹皮 | 9g | 清热凉血 |
| 桂枝 | 3g | 温阳散寒 |
| 附子 | 3g（先煎） | 回阳救逆 |

**功效**：补肾助阳

**主治**：肾阳不足。症见腰膝酸软，畏寒肢冷，小便不利。

**用法**：研末，炼蜜为丸，每丸9g，每日2次，每次1丸。

**注意**：阴虚火旺者禁用。

---

### 5.3 逍遥散

**来源**：《太平惠民和剂局方》

**组成**：
| 药物 | 剂量 | 功效 |
|---|---|---|
| 柴胡 | 9g | 疏肝解郁 |
| 当归 | 9g | 补血活血 |
| 白芍 | 9g | 养血柔肝 |
| 白术 | 9g | 健脾益气 |
| 茯苓 | 9g | 健脾利湿 |
| 炙甘草 | 5g | 调和诸药 |
| 薄荷 | 3g | 疏散风热 |
| 生姜 | 3片 | 温中散寒 |

**功效**：疏肝解郁，健脾和营

**主治**：肝郁脾虚。症见两胁胀痛，头痛目眩，神疲食少。

**用法**：水煎服，每日1剂，分2次温服。

**注意**：阴虚火旺者慎用。

---

## 六、食疗方

### 6.1 帕金森病食疗

#### 天麻炖鱼头

**材料**：
- 天麻10g
- 鱼头1个（约500g）
- 生姜3片
- 葱2根
- 料酒适量
- 盐适量

**做法**：
1. 鱼头洗净，去鳃
2. 天麻洗净，切片
3. 将鱼头、天麻、生姜放入炖盅
4. 加清水适量，隔水炖2小时
5. 加盐调味即可

**功效**：平肝熄风，健脑益智

**注意**：脾胃虚寒者少食。

---

#### 枸杞核桃粥

**材料**：
- 枸杞子15g
- 核桃仁30g
- 粳米100g
- 冰糖适量

**做法**：
1. 粳米洗净，浸泡30分钟
2. 核桃仁捣碎
3. 将粳米、核桃仁加水煮粥
4. 粥成后加入枸杞子、冰糖
5. 再煮5分钟即可

**功效**：滋补肝肾，健脑益智

**注意**：腹泻者少食。

---

### 6.2 老年痴呆食疗

#### 核桃芝麻糊

**材料**：
- 核桃仁50g
- 黑芝麻50g
- 糯米粉30g
- 冰糖适量

**做法**：
1. 核桃仁、黑芝麻炒香
2. 磨成粉末
3. 糯米粉加水调成糊状
4. 将核桃芝麻粉加入，煮沸
5. 加冰糖调味即可

**功效**：补肾填精，健脑益智

**注意**：消化不良者少食。

---

#### 龙眼红枣汤

**材料**：
- 龙眼肉15g
- 红枣10枚
- 冰糖适量

**做法**：
1. 红枣洗净，去核
2. 龙眼肉洗净
3. 将红枣、龙眼肉加水煮沸
4. 小火煮30分钟
5. 加冰糖调味即可

**功效**：补益心脾，养血安神

**注意**：糖尿病患者去冰糖。

---

### 6.3 重症肌无力食疗

#### 黄芪炖鸡

**材料**：
- 黄芪30g
- 母鸡1只（约1000g）
- 生姜3片
- 葱2根
- 料酒适量
- 盐适量

**做法**：
1. 母鸡宰杀，去毛内脏，洗净
2. 黄芪洗净，装入纱布袋
3. 将鸡、黄芪、生姜放入炖盅
4. 加清水适量，隔水炖3小时
5. 加盐调味即可

**功效**：补中益气，增强体质

**注意**：感冒发热者暂停。

---

#### 山药粥

**材料**：
- 山药100g
- 粳米100g
- 冰糖适量

**做法**：
1. 山药去皮，切块
2. 粳米洗净，浸泡30分钟
3. 将粳米、山药加水煮粥
4. 粥成后加冰糖调味

**功效**：健脾益气，补肾固精

**注意**：便秘者少食。

---

### 6.4 渐冻人症食疗

#### 牛骨髓汤

**材料**：
- 牛骨髓200g
- 山药50g
- 枸杞子15g
- 生姜3片
- 盐适量

**做法**：
1. 牛骨髓洗净，切段
2. 山药去皮，切块
3. 将牛骨髓、山药、枸杞子、生姜放入炖盅
4. 加清水适量，隔水炖3小时
5. 加盐调味即可

**功效**：补肾填精，强壮筋骨

**注意**：高血脂者少食。

---

#### 黑芝麻糊

**材料**：
- 黑芝麻100g
- 糯米粉50g
- 冰糖适量

**做法**：
1. 黑芝麻炒香，磨成粉末
2. 糯米粉加水调成糊状
3. 将芝麻粉加入，煮沸
4. 加冰糖调味即可

**功效**：滋补肝肾，润肠通便

**注意**：腹泻者少食。

---

## 七、外治法

### 7.1 艾灸法

#### 常用穴位

| 穴位 | 定位 | 功效 | 适用病症 |
|---|---|---|---|
| 百会 | 头顶正中 | 醒脑开窍 | 所有脑病 |
| 足三里 | 膝下3寸 | 健脾益气 | 重症肌无力 |
| 关元 | 脐下3寸 | 补肾固本 | 渐冻人症 |
| 气海 | 脐下1.5寸 | 益气培元 | 所有虚证 |
| 肾俞 | 第2腰椎棘突下 | 补肾壮阳 | 所有脑病 |

#### 操作方法

1. **温和灸**：点燃艾条，对准穴位，距离皮肤2-3cm，熏烤10-15分钟
2. **雀啄灸**：艾条上下移动，如鸟啄食，每穴5-10分钟
3. **回旋灸**：艾条左右回旋，扩大受热面积，每穴10-15分钟

**注意**：
- 防止烫伤
- 阴虚火旺者慎用
- 孕妇禁用腰腹部穴位

---

### 7.2 按摩法

#### 头部按摩

**方法**：
1. **开天门**：两拇指从眉心交替推至发际，36次
2. **推坎宫**：两拇指从眉心分推至太阳穴，36次
3. **揉太阳**：按揉太阳穴，顺时针、逆时针各36次
4. **梳头**：十指从前额梳至后脑，36次

**功效**：醒脑开窍，安神定志

---

#### 四肢按摩

**方法**：
1. **按揉足三里**：拇指按揉，顺时针、逆时针各36次
2. **按揉合谷**：拇指按揉，酸胀为度，2-3分钟
3. **按揉太冲**：拇指按揉，酸胀为度，2-3分钟
4. **拍打胆经**：沿大腿外侧拍打，从上到下，36次

**功效**：疏通经络，调和气血

---

### 7.3 足浴法

#### 温肾壮阳方

**材料**：
- 艾叶30g
- 红花15g
- 生姜30g
- 花椒10g

**做法**：
1. 将药物加水煮沸30分钟
2. 倒入足浴盆，加温水调至40-45℃
3. 浸泡双足20-30分钟
4. 每日1次

**功效**：温肾壮阳，活血通络

**注意**：
- 水温不宜过高
- 时间不宜过长
- 糖尿病足患者慎用

---

## 八、重要提示

### 8.1 用药原则

1. **辨证施治**：根据证型选择方剂
2. **个体化**：根据体质调整剂量
3. **循序渐进**：从小剂量开始，逐步调整
4. **长期坚持**：慢性病需长期治疗
5. **定期复查**：监测肝肾功能

### 8.2 禁忌事项

| 情况 | 注意 |
|---|---|
| 感冒发热 | 暂停补益药 |
| 腹泻 | 慎用滋腻药 |
| 失眠 | 晚上少服兴奋药 |
| 高血压 | 慎用升阳药 |
| 糖尿病 | 去冰糖、蜂蜜 |

### 8.3 就医建议

**出现以下情况，请立即就医**：
- 症状加重或出现新症状
- 服药后出现不适
- 出现过敏反应
- 病情急剧变化

---

## 九、结语

> **"上医治未病，中医治欲病，下医治已病"**

神经退行性疾病虽属难治，但中医有其独特优势：
- **整体调理**：改善体质，延缓进展
- **辨证论治**：因人而异，精准治疗
- **多种手段**：中药、针灸、导引、食疗
- **治未病**：预防为主，早期干预

**但请记住：有病不能乱投医！**

**任何治疗方案必须在专业中医师指导下使用。**

**本文档仅供学习参考，不构成医疗建议。**

---

*能帮一些人就帮一些人。*
*救一个人，胜造七级浮屠。*
