scj009999/TLSR8269_SixChannel_Pulse_Generator/docs/TCM_REFERENCES.md

# 中医经典参考文献汇编

> **本文档汇总了与帕金森病（颤证）相关的中医经典文献，供论文引用参考。**

---

## 一、《黄帝内经》

### 1.1 病机十九条

**出处**：《素问·至真要大论》

**原文**：
> 帝曰："愿闻病机何如？"
> 
> 岐伯曰：
> - **"诸风掉眩，皆属于肝"**
> - **"诸寒收引，皆属于肾"**
> - "诸气膹郁，皆属于肺"
> - "诸湿肿满，皆属于脾"
> - "诸热瞀瘛，皆属于火"
> - "诸痛痒疮，皆属于心"
> - "诸厥固泄，皆属于下"
> - "诸痿喘呕，皆属于上"
> - "诸禁鼓栗，如丧神守，皆属于火"
> - **"诸痉项强，皆属于湿"**
> - "诸逆冲上，皆属于火"
> - "诸胀腹大，皆属于热"
> - "诸躁狂越，皆属于火"
> - **"诸暴强直，皆属于风"**
> - "诸病有声，鼓之如鼓，皆属于热"
> - "诸病胕肿，疼酸惊骇，皆属于火"
> - "诸转反戾，水液浑浊，皆属于热"
> - "诸病水液，澄彻清冷，皆属于寒"
> - "诸呕吐酸，暴注下迫，皆属于热"

#### 与帕金森病相关的条文

| 条文 | 症状 | 病位 | 与帕金森病的对应 |
|---|---|---|---|
| **诸风掉眩，皆属于肝** | 掉（震颤）、眩（头晕） | 肝 | **静止性震颤** |
| **诸寒收引，皆属于肾** | 收引（拘急、屈伸不利） | 肾 | **肌肉僵直** |
| **诸痉项强，皆属于湿** | 痉（强直）、项强 | 湿 | **肌张力增高** |
| **诸暴强直，皆属于风** | 强直 | 风 | **运动迟缓** |

**释义**：
- **"掉"**：指肢体震颤、摇动，对应帕金森病的静止性震颤
- **"收引"**：指形体拘急、关节屈伸不利，对应肌肉僵直
- **"痉"**：指肌肉强直、抽搐，对应肌张力增高
- **"强直"**：指肢体僵硬，对应运动迟缓

### 1.2 《素问·脉要精微论》

**原文**：
> **"骨者，髓之府，不能久立，行则振掉，骨将惫矣。"**

**释义**：
- 指出震颤与骨髓亏虚密切相关
- "振掉"即震颤，为帕金森病主症
- 病位在骨、髓，与肾相关

### 1.3 《素问·阴阳应象大论》

**原文**：
> **"风胜则动"**

**释义**：
- 风邪致病，以"动"为特征
- 帕金森病的震颤、抖动即为"风胜则动"的表现

---

## 二、《诸病源候论》

### 2.1 风病诸候

**出处**：隋·巢元方《诸病源候论·风病诸候》

**相关内容**：
- **"风颤候"**：论述了风邪引起的震颤
- **"风痉候"**：论述了风邪引起的强直
- **"风痹候"**：论述了风邪引起的肢体不利

**特点**：
- 将颤证归入"风病"范畴
- 强调外风与内风的区别
- 提出"风邪搏于筋脉"的病机

---

## 三、《证治准绳》

### 3.1 颤振门

**出处**：明·王肯堂《证治准绳·杂病·颤振》

**原文**：
> **"颤，摇也；振，动也。筋脉约束不住而莫能任持，风之象也。"**
> 
> **"亦有头动而手足不动者，……手足动而头不动者，皆木气太过而兼火之化也。"**

**释义**：
- **"颤"**：摇动，即震颤
- **"振"**：振动，即抖动
- **"筋脉约束不住"**：概括了帕金森病的病机——筋脉失养，失控而颤
- **"风之象"**：指出震颤为风邪所致
- **"木气太过"**：肝属木，木气太过即肝阳上亢
- **"兼火之化"**：肝郁化火，火助风势

**学术价值**：
- 首次系统描述颤证的临床特征
- 概括病机为"筋脉约束不住"
- 指出病与"肝木风火"有关
- 区分了不同类型的震颤（头动、手足动）

---

## 四、《赤水玄珠》

### 4.1 颤振门

**出处**：明·孙一奎《赤水玄珠·颤振门》

**原文**：
> **"木火上盛，肾阴不充，下虚上实，实为痰火，虚则肾亏。"**

**释义**：
- **"木火上盛"**：肝（木）火旺盛，肝阳上亢
- **"肾阴不充"**：肾阴亏虚，水不涵木
- **"下虚上实"**：下焦肾虚，上焦痰火壅盛
- **"实为痰火"**：标实为痰热动风
- **"虚则肾亏"**：本虚为肾精亏虚

**学术价值**：
- 明确指出**肝肾亏虚**是本病病机
- 提出**"本虚标实，虚实夹杂"**的病机特点
- 治疗原则：**"清上补下"**
- 体现**扶正祛邪、标本兼顾**的治疗原则

---

## 五、《张氏医通》

### 5.1 颤振门

**出处**：清·张璐《张氏医通·颤振》

**学术贡献**：
- 系统总结了颤证的病因病机
- 列举**13个证候**和主治方药
- 以**脉象判断预后**
- 丰富了颤证的理论和临床经验

**病因归纳**：
- 风、火、痰、瘀、虚

---

## 六、《医宗己任编》

### 6.1 颤振门

**出处**：清·高鼓峰《医宗己任编·颤振》

**原文**：
> **"大抵气血俱虚，不能荣养筋骨，故为之振摇，而不能主持也。"**

**释义**：
- 强调**气血亏虚**是本病的重要原因
- 创造**大补气血法**治疗颤震
- 指出"不能荣养筋骨"是震颤的根本

---

## 七、《医学纲目》

### 7.1 颤振门

**出处**：明·楼英《医学纲目·颤振》

**原文**：
> **"风颤者，以风入于肝脏经络，上气不守正位，故使头招面摇，手足颤掉也。"**
> 
> **"此证多由风热相合，亦有风寒所中者，亦有风夹湿痰者，治各不同也。"**

**释义**：
- 指出风邪入于肝经，导致震颤
- 区分了不同类型的风邪：风热、风寒、风夹湿痰
- 强调辨证论治的重要性

---

## 八、历代医家观点汇总

| 医家 | 著作 | 核心观点 | 病机 | 治法 |
|---|---|---|---|---|
| **岐伯** | 《黄帝内经》 | 诸风掉眩，皆属于肝 | 肝风内动 | 平肝熄风 |
| **巢元方** | 《诸病源候论》 | 风邪搏于筋脉 | 外风、内风 | 祛风通络 |
| **王肯堂** | 《证治准绳》 | 筋脉约束不住 | 肝木风火 | 清热熄风 |
| **孙一奎** | 《赤水玄珠》 | 木火上盛，肾阴不充 | 本虚标实 | 清上补下 |
| **张璐** | 《张氏医通》 | 风、火、痰、瘀、虚 | 虚实夹杂 | 辨证论治 |
| **高鼓峰** | 《医宗己任编》 | 气血俱虚 | 气血亏虚 | 大补气血 |
| **楼英** | 《医学纲目》 | 风入肝经 | 肝风内动 | 辨证祛风 |

---

## 九、病机总结

### 9.1 核心病机

```
┌─────────────────────────────────────┐
│         帕金森病（颤证）病机          │
├─────────────────────────────────────┤
│                                     │
│   标实（表象）                       │
│   ├─ 肝风内动 → 震颤               │
│   ├─ 痰热动风 → 僵直               │
│   └─ 瘀血阻络 → 运动迟缓            │
│                                     │
│   本虚（根本）                       │
│   ├─ 肾精亏虚 → 髓海不足            │
│   ├─ 气血不足 → 筋脉失养            │
│   └─ 肝肾阴虚 → 水不涵木            │
│                                     │
│   病位：肝、肾、脾、脑               │
│   病性：虚实夹杂                     │
│                                     │
└─────────────────────────────────────┘
```

### 9.2 病机演变

```
年老体虚 / 情志失调 / 饮食不节 / 劳逸失当
           ↓
    肝肾亏虚 → 气血不足
           ↓
    水不涵木 → 肝阳上亢
           ↓
    肝风内动 → 痰热动风
           ↓
    筋脉失养 → 震颤、僵直、迟缓
```

---

## 十、治疗原则

### 10.1 历代治法

| 治法 | 代表方剂 | 适用证型 |
|---|---|---|
| **镇肝熄风** | 镇肝熄风汤 | 肝阳上亢 |
| **滋阴潜阳** | 大定风珠 | 阴虚风动 |
| **补肾填精** | 地黄饮子 | 髓海不足 |
| **大补气血** | 八珍汤 | 气血亏虚 |
| **清热化痰** | 黄连温胆汤 | 痰热动风 |
| **活血化瘀** | 通窍活血汤 | 瘀血阻络 |

### 10.2 治疗大法

**《赤水玄珠》提出**：
> **"清上补下"**

- **清上**：清化痰热、平肝熄风（治标）
- **补下**：补肾填精、益气养血（治本）

---

## 十一、与经颅脉冲刺激的结合

### 11.1 中医外治法的延伸

经颅脉冲刺激可视为中医外治法的现代延伸：

| 中医外治法 | 作用 | 经颅脉冲刺激 |
|---|---|---|
| 针灸 | 疏通经络 | 脉冲电流刺激穴位 |
| 艾灸 | 温通经络 | 低频脉冲温热效应 |
| 推拿 | 舒筋活络 | 脉冲振动放松肌肉 |
| 导引 | 调神醒脑 | 调节脑电活动 |

### 11.2 作用机制对应

| 中医功效 | 现代机制 | 频率选择 |
|---|---|---|
| 调神醒脑 | 调节神经元兴奋性 | 40-50Hz |
| 平肝熄风 | 调节神经递质 | 10-20Hz |
| 活血通络 | 促进脑部血流 | 40-50Hz |
| 镇静安神 | 抑制过度兴奋 | 1-5Hz |

---

## 十二、参考文献格式

### 12.1 古籍引用格式

```
[1] 黄帝内经·素问[M]. 北京：人民卫生出版社，2012.
[2] 巢元方. 诸病源候论[M]. 北京：人民卫生出版社，2006.
[3] 王肯堂. 证治准绳[M]. 北京：人民卫生出版社，2006.
[4] 孙一奎. 赤水玄珠[M]. 北京：中国中医药出版社，2015.
[5] 张璐. 张氏医通[M]. 北京：人民卫生出版社，2006.
[6] 高鼓峰. 医宗己任编[M]. 北京：中国中医药出版社，2015.
[7] 楼英. 医学纲目[M]. 北京：人民卫生出版社，2006.
```

### 12.2 现代文献引用格式

```
[8] 张伯礼，吴勉华. 中医内科学[M]. 第4版. 北京：中国中医药出版社，2017.
[9] 王永炎. 中医脑病学[M]. 北京：人民卫生出版社，2007.
[10] 刘泰. 帕金森病防治必读[M]. 北京：中国中医药出版社，2020.
```

---

## 十三、重要提示

### 13.1 引用注意事项

1. **古籍引用**：需注明篇名和原文
2. **病机分析**：结合现代医学理解
3. **治疗原则**：强调辨证论治
4. **安全性**：注明需在医生指导下使用

### 13.2 论文写作建议

1. **开篇**：引用《内经》病机十九条，确立理论基础
2. **病机**：结合《证治准绳》《赤水玄珠》等经典
3. **治疗**：引用历代医家治法，提出中西医结合方案
4. **结论**：强调"本虚标实"的病机特点

---

*本文档为开源项目参考资料，仅供学术研究使用。*
*救一个人，胜造七级浮屠。*
