scj009999/TLSR8269_SixChannel_Pulse_Generator/docs/TCM_SYMPTOM_ANALYSIS.md

# 慢性病症状分析与方剂原理

> **⚠️ 重要声明**
> 
> **本文档所列方剂仅供参考学习，不构成医疗建议。**
> 
> **有病不能乱投医！任何治疗方案必须在专业中医师指导下使用。**
> 
> **使用前请务必咨询医生，根据个人体质辨证施治。**

---

## 目录

1. [渐冻人症（肌痿）症状分析](#一渐冻人症肌痿)
2. [帕金森病（颤证）症状分析](#二帕金森病颤证)
3. [脑梗塞恢复期症状分析](#三脑梗塞恢复期)
4. [老年痴呆（痴呆证）症状分析](#四老年痴呆痴呆证)
5. [重症肌无力（痿证）症状分析](#五重症肌无力痿证)
6. [方剂原理深度解析](#六方剂原理深度解析)

---

## 一、渐冻人症（肌痿）

### 1.1 症状分析

#### 早期症状

| 症状 | 中医认识 | 病机 |
|---|---|---|
| **手指笨拙** | 筋脉失养 | 气血不足，筋脉失濡 |
| **肌肉跳动** | 肝风内动 | 血虚生风，筋脉失养 |
| **容易疲劳** | 气虚表现 | 中气不足，运化无力 |
| **肉跳感** | 风动之象 | 血虚风动，筋脉不宁 |

#### 中期症状

| 症状 | 中医认识 | 病机 |
|---|---|---|
| **肌肉萎缩** | 痿证表现 | 脾肾亏虚，精血不足 |
| **肢体无力** | 痿弱不用 | 气血两虚，筋脉失养 |
| **吞咽困难** | 咽喉失养 | 脾肾亏虚，咽喉失濡 |
| **言语不清** | 舌体失养 | 气血不足，舌体失濡 |

#### 晚期症状

| 症状 | 中医认识 | 病机 |
|---|---|---|
| **呼吸肌麻痹** | 肺气衰败 | 肺肾两虚，呼吸无力 |
| **完全瘫痪** | 痿废不用 | 精血枯竭，筋脉失养 |
| **吞咽不能** | 脾胃衰败 | 脾胃虚极，运化停止 |

### 1.2 病机层次

```
┌─────────────────────────────────────────┐
│         渐冻人症病机层次                 │
├─────────────────────────────────────────┤
│                                         │
│  先天不足 → 肾精亏虚                     │
│       ↓                                 │
│  髓海不足 → 脑失所养                     │
│       ↓                                 │
│  脾胃虚损 → 气血乏源                     │
│       ↓                                 │
│  筋脉失养 → 肌肉萎缩                     │
│       ↓                                 │
│  阳气衰微 → 病情加重                     │
│                                         │
│  核心病机：脾肾两虚，气血不足             │
│  病性：本虚标实，虚实夹杂                 │
│                                         │
└─────────────────────────────────────────┘
```

### 1.3 治疗原则

> **"治痿者，独取阳明"**
> 
> **"肾主骨，生髓，通于脑"**

**治疗三步法**：
```
第一步：固本培元 → 八珍汤为主
    ├─ 补气养血，恢复元气
    └─ 健脾益肾，培补后天

第二步：温煦阳气 → 加附子、炮姜、桂枝
    ├─ 附子：回阳救逆，温补脾肾
    ├─ 炮姜：温中散寒，温煦中焦
    └─ 桂枝：温阳通脉，通达四肢

第三步：养血安神 → 加龙眼肉、益智仁
    ├─ 龙眼肉：养血补气，安神定志
    └─ 益智仁：温肾固精，防止病情进展
```

### 1.4 方剂详解

#### 主方：八珍汤加味

**组成**：
| 药物 | 剂量 | 功效 | 原理 |
|---|---|---|---|
| 人参 | 6g | 大补元气 | 补气生血，恢复元气 |
| 白术 | 9g | 健脾益气 | 健脾助运，生化气血 |
| 茯苓 | 9g | 健脾利湿 | 健脾渗湿，防止滋腻 |
| 当归 | 12g | 补血活血 | 补血和血，滋养筋脉 |
| 川芎 | 6g | 活血行气 | 行气活血，防止瘀滞 |
| 白芍 | 9g | 养血柔肝 | 养血柔筋，缓急止痛 |
| 熟地 | 12g | 滋阴补血 | 滋阴填精，补肾养血 |
| 甘草 | 3g | 调和诸药 | 调和诸药，补中益气 |
| **附子** | **6g（先煎）** | **回阳救逆** | **温补脾肾，回阳救逆** |
| **炮姜** | **6g** | **温中散寒** | **温煦中焦，散寒止痛** |
| **桂枝** | **9g** | **温阳通脉** | **温阳通脉，通达四肢** |
| **龙眼肉** | **15g** | **养血安神** | **大补心血，安神定志** |
| **益智仁** | **9g** | **温肾固精** | **温肾固精，防止病情进展** |
| 黄芪 | 30g | 补气升阳 | 大补元气，升阳举陷 |

**功效**：温补气血，益肾填精，通络起痿，防止病情进展

**主治**：渐冻人症，脾肾两虚，气血不足，肌肉萎缩

**用法**：水煎服，每日1剂，分2次温服

---

#### 方剂原理深度解析

**1. 八珍汤固本培元**

```
四君子汤（补气） + 四物汤（补血） = 八珍汤（气血双补）

功效：
├─ 补气：人参、白术、茯苓、甘草
├─ 补血：当归、川芎、白芍、熟地
└─ 气血双补：气能生血，血能载气

原理：
├─ 气为血之帅：气能生血、行血、摄血
├─ 血为气之母：血能载气、养气
└─ 气血互生：补气以生血，养血以益气
```

**2. 附子温煦阳气**

```
附子：回阳救逆，温补脾肾

功效：
├─ 回阳救逆：挽救衰微之阳气
├─ 温补脾肾：温煦脾肾之阳
├─ 散寒止痛：祛除阴寒之邪
└─ 温通经脉：温通四肢经脉

原理：
├─ 附子大辛大热，为回阳救逆第一品
├─ 温补脾肾之阳，使阳气生发
├─ 阳气生长，则寒气消退
└─ 先煎30-60分钟，降低毒性
```

**3. 炮姜温中散寒**

```
炮姜：温中散寒，温经止血

功效：
├─ 温中散寒：温煦中焦，散寒止痛
├─ 温经止血：温经止血，防止出血
└─ 温脾止泻：温脾止泻，防止泄泻

原理：
├─ 炮姜为干姜炮制品，性味辛热
├─ 温中焦脾胃之阳
├─ 与附子配伍，增强温阳之力
└─ 温而不燥，守而不走
```

**4. 桂枝通达阳气**

```
桂枝：发汗解肌，温通经脉，助阳化气

功效：
├─ 温阳通脉：温通经脉，通达四肢
├─ 助阳化气：助阳气化气行水
├─ 平冲降逆：平冲降逆，防止气逆
└─ 通利九窍：通达九窍，开窍醒神

原理：
├─ 桂枝辛甘温，入心、肺、膀胱经
├─ 温通经脉，使阳气通达四肢九窍
├─ 与附子配伍，增强温阳通脉之力
└─ 通达四肢，改善肢体冰冷
```

**5. 龙眼肉养血安神**

```
龙眼肉：补益心脾，养血安神

功效：
├─ 补益心脾：大补心脾之气血
├─ 养血安神：养血安神，改善睡眠
├─ 益智健脑：益智健脑，改善记忆
└─ 补气养血：补气养血，增强体质

原理：
├─ 龙眼肉甘温，入心、脾经
├─ 大补心血，安神定志
├─ 用量宜大，15-30g
├─ 与八珍汤配伍，增强养血之力
└─ 改善失眠、健忘、心悸
```

**6. 益智仁防止病情进展**

```
益智仁：温肾固精，缩尿止遗，温脾止泻

功效：
├─ 温肾固精：温肾固精，防止精气外泄
├─ 缩尿止遗：缩尿止遗，防止尿频
├─ 温脾止泻：温脾止泻，防止泄泻
└─ 防止病情进展：温肾固精，防止病情恶化

原理：
├─ 益智仁辛温，入脾、肾经
├─ 温肾固精，防止精气外泄
├─ 起到"刹车"效果，防止病情进展
├─ 与附子配伍，增强温肾之力
└─ 温脾止泻，防止脾胃虚寒
```

---

### 1.5 方剂配伍精义

```
┌─────────────────────────────────────────┐
│         渐冻人症方剂配伍精义             │
├─────────────────────────────────────────┤
│                                         │
│  第一层：固本培元（八珍汤）              │
│  ├─ 补气：人参、白术、茯苓、甘草         │
│  ├─ 补血：当归、川芎、白芍、熟地         │
│  └─ 气血双补，恢复元气                   │
│                                         │
│  第二层：温煦阳气（附子、炮姜、桂枝）     │
│  ├─ 附子：回阳救逆，温补脾肾             │
│  ├─ 炮姜：温中散寒，温煦中焦             │
│  └─ 桂枝：温阳通脉，通达四肢             │
│                                         │
│  第三层：养血安神（龙眼肉、益智仁）       │
│  ├─ 龙眼肉：养血补气，安神定志           │
│  └─ 益智仁：温肾固精，防止病情进展       │
│                                         │
│  第四层：大补元气（黄芪）                │
│  └─ 黄芪：补气升阳，增强体质             │
│                                         │
│  配伍特点：                              │
│  ├─ 气血双补，阴阳并调                   │
│  ├─ 温阳散寒，通达四肢                   │
│  ├─ 养血安神，防止病情进展               │
│  └─ 大补元气，增强体质                   │
│                                         │
└─────────────────────────────────────────┘
```

---

## 二、帕金森病（颤证）

### 2.1 症状分析

#### 主要症状

| 症状 | 中医认识 | 病机 |
|---|---|---|
| **静止性震颤** | 肝风内动 | 血虚生风，筋脉失养 |
| **肌肉僵直** | 筋脉拘急 | 阴血不足，筋脉失濡 |
| **运动迟缓** | 气血两虚 | 气血不足，肢体失养 |
| **姿势不稳** | 肝肾亏虚 | 肝肾不足，筋骨失养 |

#### 伴随症状

| 症状 | 中医认识 | 病机 |
|---|---|---|
| **便秘** | 肠道失润 | 阴血不足，肠道失润 |
| **失眠** | 心神失养 | 血虚心神失养 |
| **抑郁** | 肝气郁结 | 肝失疏泄，气机郁滞 |
| **嗅觉减退** | 鼻窍失养 | 气血不足，鼻窍失养 |

### 2.2 病机层次

```
┌─────────────────────────────────────────┐
│         帕金森病病机层次                 │
├─────────────────────────────────────────┤
│                                         │
│  肾精亏虚 → 水不涵木                     │
│       ↓                                 │
│  肝阳上亢 → 肝风内动                     │
│       ↓                                 │
│  筋脉失养 → 震颤、僵直                   │
│       ↓                                 │
│  气血不足 → 运动迟缓                     │
│                                         │
│  核心病机：肝肾阴虚，肝风内动             │
│  病性：本虚标实，虚实夹杂                 │
│                                         │
└─────────────────────────────────────────┘
```

### 2.3 治疗原则

> **"诸风掉眩，皆属于肝"**
> 
> **"治风先治血，血行风自灭"**

**治疗三步法**：
```
第一步：养血柔肝 → 四物汤为主
    ├─ 当归、白芍：养血柔肝
    └─ 熟地、川芎：滋阴养血

第二步：平肝熄风 → 加天麻、钩藤
    ├─ 天麻：平肝熄风
    └─ 钩藤：清热平肝

第三步：通络止痉 → 加全蝎、蜈蚣
    ├─ 全蝎：搜风止痉
    └─ 蜈蚣：通络止痉
```

### 2.4 方剂详解

#### 主方：八珍汤加味

**组成**：
| 药物 | 剂量 | 功效 | 原理 |
|---|---|---|---|
| 人参 | 6g | 大补元气 | 补气生血，恢复元气 |
| 白术 | 9g | 健脾益气 | 健脾助运，生化气血 |
| 茯苓 | 9g | 健脾利湿 | 健脾渗湿，防止滋腻 |
| 当归 | 9g | 补血活血 | 补血和血，滋养筋脉 |
| 川芎 | 6g | 活血行气 | 行气活血，防止瘀滞 |
| 白芍 | 15g | 养血柔肝 | 养血柔筋，缓急止颤 |
| 熟地 | 12g | 滋阴补血 | 滋阴填精，补肾养血 |
| 甘草 | 3g | 调和诸药 | 调和诸药，补中益气 |
| 天麻 | 9g | 平肝熄风 | 平肝熄风，止颤定惊 |
| 钩藤 | 12g（后下） | 清热平肝 | 清热平肝，熄风止痉 |
| 全蝎 | 3g（研末冲服） | 搜风止痉 | 搜风止痉，通络止颤 |
| 蜈蚣 | 1条（研末冲服） | 通络止痉 | 通络止痉，祛风止颤 |
| 黄芪 | 15g | 补气升阳 | 大补元气，增强体质 |

**功效**：益气养血，平肝熄风，通络止痉

**主治**：帕金森病，气血两虚，肝风内动

**用法**：水煎服，每日1剂，分2次温服

---

## 三、脑梗塞恢复期

### 3.1 症状分析

#### 恢复期症状

| 症状 | 中医认识 | 病机 |
|---|---|---|
| **半身不遂** | 中风后遗症 | 气虚血瘀，经络不通 |
| **言语謇涩** | 舌体失养 | 气血不足，舌体失濡 |
| **口眼歪斜** | 经络失养 | 气血不足，经络失养 |
| **肢体麻木** | 气血不通 | 气虚血瘀，经络不通 |

#### 伴随症状

| 症状 | 中医认识 | 病机 |
|---|---|---|
| **头晕** | 肝阳上亢 | 气血不足，肝阳上亢 |
| **失眠** | 心神失养 | 血虚心神失养 |
| **便秘** | 肠道失润 | 阴血不足，肠道失润 |
| **情绪不稳** | 肝气郁结 | 肝失疏泄，气机郁滞 |

### 3.2 病机层次

```
┌─────────────────────────────────────────┐
│         脑梗塞恢复期病机层次             │
├─────────────────────────────────────────┤
│                                         │
│  气血不足 → 脑失所养                     │
│       ↓                                 │
│  气虚血瘀 → 经络不通                     │
│       ↓                                 │
│  肝阳上亢 → 头晕头痛                     │
│       ↓                                 │
│  痰浊阻窍 → 言语不清                     │
│                                         │
│  核心病机：气虚血瘀，经络不通             │
│  病性：本虚标实，虚实夹杂                 │
│                                         │
└─────────────────────────────────────────┘
```

### 3.3 治疗原则

> **"治风先治血，血行风自灭"**
> 
> **"气虚则血瘀，血瘀则经络不通"**

**治疗三步法**：
```
第一步：补气养血 → 八珍汤为主
    ├─ 补气：人参、白术、茯苓、甘草
    └─ 补血：当归、川芎、白芍、熟地

第二步：活血通络 → 加桃仁、红花、丹参
    ├─ 桃仁、红花：活血化瘀
    └─ 丹参：活血祛瘀，通经止痛

第三步：开窍醒神 → 加冰片、菖蒲
    ├─ 冰片：开窍醒神，芳香走窜
    └─ 菖蒲：开窍化痰，醒神益智
```

### 3.4 方剂详解

#### 主方：八珍汤加味

**组成**：
| 药物 | 剂量 | 功效 | 原理 |
|---|---|---|---|
| 人参 | 6g | 大补元气 | 补气生血，恢复元气 |
| 白术 | 9g | 健脾益气 | 健脾助运，生化气血 |
| 茯苓 | 9g | 健脾利湿 | 健脾渗湿，防止滋腻 |
| 当归 | 9g | 补血活血 | 补血和血，滋养筋脉 |
| 川芎 | 6g | 活血行气 | 行气活血，防止瘀滞 |
| 白芍 | 9g | 养血柔肝 | 养血柔筋，缓急止痛 |
| 熟地 | 12g | 滋阴补血 | 滋阴填精，补肾养血 |
| 甘草 | 3g | 调和诸药 | 调和诸药，补中益气 |
| **冰片** | **0.1g（冲服）** | **开窍醒神** | **芳香走窜，开窍醒神** |
| 杭菊花 | 9g | 平肝明目 | 平肝明目，清利头目 |
| 龙骨 | 15g（先煎） | 平肝潜阳 | 重镇安神，平肝潜阳 |
| 牡蛎 | 15g（先煎） | 软坚散结 | 软坚散结，平肝潜阳 |
| 天麻 | 9g | 平肝熄风 | 平肝熄风，止颤定惊 |
| 钩藤 | 12g（后下） | 清热平肝 | 清热平肝，熄风止痉 |
| 丹参 | 15g | 活血祛瘀 | 活血祛瘀，通经止痛 |
| 黄芪 | 30g | 补气升阳 | 大补元气，促进恢复 |

**功效**：益气养血，平肝熄风，开窍醒神，活血通络

**主治**：脑梗塞恢复期，气血两虚，肝阳上亢，经络不通

**用法**：水煎服，每日1剂，分2次温服

---

## 四、老年痴呆（痴呆证）

### 4.1 症状分析

#### 主要症状

| 症状 | 中医认识 | 病机 |
|---|---|---|
| **记忆力减退** | 髓海不足 | 肾精亏虚，髓海不足 |
| **定向力障碍** | 神明失用 | 气血不足，神明失养 |
| **计算力下降** | 心神失养 | 心血不足，心神失养 |
| **判断力下降** | 脑失所养 | 气血不足，脑失所养 |

#### 伴随症状

| 症状 | 中医认识 | 病机 |
|---|---|---|
| **失眠** | 心神失养 | 血虚心神失养 |
| **抑郁** | 肝气郁结 | 肝失疏泄，气机郁滞 |
| **焦虑** | 心神不宁 | 心血不足，心神不宁 |
| **人格改变** | 神明失用 | 髓海不足，神明失用 |

### 4.2 病机层次

```
┌─────────────────────────────────────────┐
│         老年痴呆病机层次                 │
├─────────────────────────────────────────┤
│                                         │
│  肾精亏虚 → 髓海不足                     │
│       ↓                                 │
│  脑失所养 → 神明失用                     │
│       ↓                                 │
│  气血不足 → 心神失养                     │
│       ↓                                 │
│  痰浊阻窍 → 神志不清                     │
│                                         │
│  核心病机：髓海不足，神明失用             │
│  病性：本虚标实，虚实夹杂                 │
│                                         │
└─────────────────────────────────────────┘
```

### 4.3 治疗原则

> **"脑为髓之海"**
> 
> **"肾主骨，生髓，通于脑"**

**治疗三步法**：
```
第一步：补肾填精 → 加鹿角胶、龟板胶
    ├─ 鹿角胶：温补肝肾，益精养血
    └─ 龟板胶：滋阴潜阳，益肾健骨

第二步：开窍化痰 → 加菖蒲、远志
    ├─ 菖蒲：开窍化痰，醒神益智
    └─ 远志：安神益智，交通心肾

第三步：活血通络 → 加丹参、川芎
    ├─ 丹参：活血祛瘀，通经止痛
    └─ 川芎：活血行气，祛风止痛
```

### 4.4 方剂详解

#### 主方：八珍汤加味

**组成**：
| 药物 | 剂量 | 功效 | 原理 |
|---|---|---|---|
| 人参 | 6g | 大补元气 | 补气生血，恢复元气 |
| 白术 | 9g | 健脾益气 | 健脾助运，生化气血 |
| 茯苓 | 9g | 健脾利湿 | 健脾渗湿，防止滋腻 |
| 当归 | 9g | 补血活血 | 补血和血，滋养筋脉 |
| 川芎 | 6g | 活血行气 | 行气活血，防止瘀滞 |
| 白芍 | 9g | 养血柔肝 | 养血柔筋，缓急止痛 |
| 熟地 | 12g | 滋阴补血 | 滋阴填精，补肾养血 |
| 甘草 | 3g | 调和诸药 | 调和诸药，补中益气 |
| 菖蒲 | 9g | 开窍化痰 | 开窍化痰，醒神益智 |
| 远志 | 6g | 安神益智 | 安神益智，交通心肾 |
| 郁金 | 9g | 行气解郁 | 行气解郁，清心开窍 |
| 丹参 | 15g | 活血祛瘀 | 活血祛瘀，通经止痛 |
| 枸杞 | 12g | 滋补肝肾 | 滋补肝肾，益精明目 |
| 鹿角胶 | 9g（烊化） | 温补肝肾 | 温补肝肾，益精养血 |
| 龟板胶 | 9g（烊化） | 滋阴潜阳 | 滋阴潜阳，益肾健骨 |

**功效**：益气养血，开窍化痰，安神益智，补肾填精

**主治**：老年痴呆，髓海不足，神明失用

**用法**：水煎服，每日1剂，分2次温服

---

## 五、重症肌无力（痿证）

### 5.1 症状分析

#### 主要症状

| 症状 | 中医认识 | 病机 |
|---|---|---|
| **眼睑下垂** | 中气不足 | 脾胃气虚，中气下陷 |
| **复视** | 气血不足 | 气血不足，目失所养 |
| **咀嚼无力** | 脾胃虚弱 | 脾胃虚弱，肌肉失养 |
| **吞咽困难** | 咽喉失养 | 气血不足，咽喉失养 |
| **四肢无力** | 痿证表现 | 脾胃气虚，肌肉失养 |

#### 伴随症状

| 症状 | 中医认识 | 病机 |
|---|---|---|
| **疲劳加重** | 气虚表现 | 中气不足，运化无力 |
| **晨轻暮重** | 阳气虚衰 | 阳气不足，午后加重 |
| **气短懒言** | 肺脾气虚 | 肺脾气虚，呼吸无力 |
| **自汗** | 卫气不固 | 卫气不固，津液外泄 |

### 5.2 病机层次

```
┌─────────────────────────────────────────┐
│         重症肌无力病机层次               │
├─────────────────────────────────────────┤
│                                         │
│  脾胃虚弱 → 气血生化乏源                 │
│       ↓                                 │
│  中气下陷 → 升举无力                     │
│       ↓                                 │
│  肌肉失养 → 痿弱不用                     │
│       ↓                                 │
│  阳气虚衰 → 病情加重                     │
│                                         │
│  核心病机：脾胃气虚，中气下陷             │
│  病性：本虚标实，虚实夹杂                 │
│                                         │
└─────────────────────────────────────────┘
```

### 5.3 治疗原则

> **"治痿者，独取阳明"**
> 
> **"脾胃为后天之本，气血生化之源"**

**治疗三步法**：
```
第一步：补中益气 → 八珍汤为主
    ├─ 补气：人参、白术、茯苓、甘草
    └─ 补血：当归、川芎、白芍、熟地

第二步：升阳举陷 → 加黄芪、升麻、柴胡
    ├─ 黄芪：大补元气，升阳举陷
    ├─ 升麻：升阳举陷，清热解毒
    └─ 柴胡：疏肝升阳，和解少阳

第三步：健脾补肾 → 加山药、枸杞
    ├─ 山药：健脾益肾，补肾固精
    └─ 枸杞：滋补肝肾，益精明目
```

### 5.4 方剂详解

#### 主方：八珍汤加味

**组成**：
| 药物 | 剂量 | 功效 | 原理 |
|---|---|---|---|
| 人参 | 6g | 大补元气 | 补气生血，恢复元气 |
| 白术 | 9g | 健脾益气 | 健脾助运，生化气血 |
| 茯苓 | 9g | 健脾利湿 | 健脾渗湿，防止滋腻 |
| 当归 | 9g | 补血活血 | 补血和血，滋养筋脉 |
| 川芎 | 6g | 活血行气 | 行气活血，防止瘀滞 |
| 白芍 | 9g | 养血柔肝 | 养血柔筋，缓急止痛 |
| 熟地 | 12g | 滋阴补血 | 滋阴填精，补肾养血 |
| 甘草 | 3g | 调和诸药 | 调和诸药，补中益气 |
| 黄芪 | 30g | 补气升阳 | 大补元气，升阳举陷 |
| 升麻 | 6g | 升阳举陷 | 升阳举陷，清热解毒 |
| 柴胡 | 6g | 疏肝升阳 | 疏肝升阳，和解少阳 |
| 陈皮 | 6g | 理气化痰 | 理气化痰，防止滋腻 |
| 山药 | 15g | 健脾益肾 | 健脾益肾，补肾固精 |
| 枸杞 | 12g | 滋补肝肾 | 滋补肝肾，益精明目 |

**功效**：益气养血，升阳举陷，健脾补肾

**主治**：重症肌无力，脾胃气虚，中气下陷

**用法**：水煎服，每日1剂，分2次温服

---

## 六、方剂原理深度解析

### 6.1 八珍汤的配伍原理

```
┌─────────────────────────────────────────┐
│         八珍汤配伍原理                   │
├─────────────────────────────────────────┤
│                                         │
│  四君子汤（补气）                        │
│  ├─ 人参：大补元气，为君药               │
│  ├─ 白术：健脾益气，为臣药               │
│  ├─ 茯苓：健脾利湿，为佐药               │
│  └─ 甘草：调和诸药，为使药               │
│                                         │
│  四物汤（补血）                          │
│  ├─ 熟地：滋阴补血，为君药               │
│  ├─ 当归：补血活血，为臣药               │
│  ├─ 白芍：养血柔肝，为佐药               │
│  └─ 川芎：活血行气，为使药               │
│                                         │
│  配伍特点：                              │
│  ├─ 气血双补，阴阳并调                   │
│  ├─ 补而不滞，滋而不腻                   │
│  ├─ 气能生血，血能载气                   │
│  └─ 气血互生，相辅相成                   │
│                                         │
└─────────────────────────────────────────┘
```

### 6.2 附子的应用原理

```
┌─────────────────────────────────────────┐
│         附子的应用原理                   │
├─────────────────────────────────────────┤
│                                         │
│  性味：辛、甘，大热；有毒                 │
│  归经：心、肾、脾经                       │
│                                         │
│  功效：                                  │
│  ├─ 回阳救逆：挽救衰微之阳气             │
│  ├─ 补火助阳：温补脾肾之阳               │
│  ├─ 散寒止痛：祛除阴寒之邪               │
│  └─ 温通经脉：温通四肢经脉               │
│                                         │
│  应用要点：                              │
│  ├─ 先煎30-60分钟，降低毒性              │
│  ├─ 至口尝无麻感为度                     │
│  ├─ 与干姜配伍，增强温阳之力             │
│  └─ 用量宜小，6-9g为宜                   │
│                                         │
│  配伍禁忌：                              │
│  ├─ 不宜与半夏、瓜蒌、贝母同用           │
│  ├─ 阴虚火旺者禁用                       │
│  └─ 孕妇慎用                             │
│                                         │
└─────────────────────────────────────────┘
```

### 6.3 桂枝的应用原理

```
┌─────────────────────────────────────────┐
│         桂枝的应用原理                   │
├─────────────────────────────────────────┤
│                                         │
│  性味：辛、甘，温                         │
│  归经：心、肺、膀胱经                     │
│                                         │
│  功效：                                  │
│  ├─ 发汗解肌：解表散寒                   │
│  ├─ 温通经脉：温通经脉，通达四肢         │
│  ├─ 助阳化气：助阳气化气行水             │
│  └─ 平冲降逆：平冲降逆，防止气逆         │
│                                         │
│  应用要点：                              │
│  ├─ 温阳通脉，使阳气通达四肢九窍         │
│  ├─ 与附子配伍，增强温阳通脉之力         │
│  ├─ 通达四肢，改善肢体冰冷               │
│  └─ 用量9-15g为宜                        │
│                                         │
│  配伍特点：                              │
│  ├─ 与附子配伍：增强温阳之力             │
│  ├─ 与白芍配伍：调和营卫                 │
│  └─ 与甘草配伍：辛甘化阳                 │
│                                         │
└─────────────────────────────────────────┘
```

### 6.4 龙眼肉的应用原理

```
┌─────────────────────────────────────────┐
│         龙眼肉的应用原理                 │
├─────────────────────────────────────────┤
│                                         │
│  性味：甘，温                             │
│  归经：心、脾经                           │
│                                         │
│  功效：                                  │
│  ├─ 补益心脾：大补心脾之气血             │
│  ├─ 养血安神：养血安神，改善睡眠         │
│  ├─ 益智健脑：益智健脑，改善记忆         │
│  └─ 补气养血：补气养血，增强体质         │
│                                         │
│  应用要点：                              │
│  ├─ 大补心血，安神定志                   │
│  ├─ 用量宜大，15-30g                     │
│  ├─ 与八珍汤配伍，增强养血之力           │
│  └─ 改善失眠、健忘、心悸                 │
│                                         │
│  配伍特点：                              │
│  ├─ 与黄芪配伍：气血双补                 │
│  ├─ 与当归配伍：养血安神                 │
│  └─ 与酸枣仁配伍：养心安神               │
│                                         │
└─────────────────────────────────────────┘
```

### 6.5 益智仁的应用原理

```
┌─────────────────────────────────────────┐
│         益智仁的应用原理                 │
├─────────────────────────────────────────┤
│                                         │
│  性味：辛，温                             │
│  归经：脾、肾经                           │
│                                         │
│  功效：                                  │
│  ├─ 温肾固精：温肾固精，防止精气外泄     │
│  ├─ 缩尿止遗：缩尿止遗，防止尿频         │
│  ├─ 温脾止泻：温脾止泻，防止泄泻         │
│  └─ 防止病情进展：温肾固精，防止病情恶化 │
│                                         │
│  应用要点：                              │
│  ├─ 温肾固精，防止精气外泄               │
│  ├─ 起到"刹车"效果，防止病情进展         │
│  ├─ 与附子配伍，增强温肾之力             │
│  └─ 用量9-15g为宜                        │
│                                         │
│  配伍特点：                              │
│  ├─ 与附子配伍：增强温肾之力             │
│  ├─ 与山药配伍：健脾益肾                 │
│  └─ 与乌药配伍：温肾缩尿                 │
│                                         │
└─────────────────────────────────────────┘
```

---

## 七、结语

> **"方者，法也；法者，理也"**
> 
> **"知其然，更要知其所以然"**

慢性病的治疗，不仅要给出方剂，更要讲清道理：

### 渐冻人症的治疗原理

```
八珍汤（固本培元）
    ├─ 气血双补，恢复元气
    └─ 健脾益肾，培补后天

+ 附子、炮姜、桂枝（温煦阳气）
    ├─ 附子：回阳救逆，温补脾肾
    ├─ 炮姜：温中散寒，温煦中焦
    └─ 桂枝：温阳通脉，通达四肢

+ 龙眼肉、益智仁（养血安神）
    ├─ 龙眼肉：养血补气，安神定志
    └─ 益智仁：温肾固精，防止病情进展

= 温补气血，益肾填精，通络起痿，防止病情进展
```

**核心原理**：
- **阳气生长，则寒气消退**
- **桂枝通达阳气，使阳气通达四肢九窍**
- **龙眼肉用量大，养血补气安神**
- **益智仁起到"刹车"效果，防止病情加重**

---

*能帮一些人就帮一些人。*
*救一个人，胜造七级浮屠。*
