scj009999/TLSR8269_SixChannel_Pulse_Generator/docs/WHATSAPP_MESSAGE.md

# WhatsApp/微信分享文案

---

## 版本一：简短版（适合快速分享）

📢 帕友和家属们，请看过来！

最近听说一个令人心痛的事：一位年轻帕友（37岁）做了DBS手术，不到两年...😢

更让人心寒的是，当有人在群里提醒大家关注手术风险，**被踢出群了**。

🔍 其实帕金森病治疗不止手术一种选择：

✅ 药物治疗（历史悠久）
✅ 经颅电刺激（非侵入，可居家）
✅ 中医调理（整体调理）
⚠️ DBS手术（有效但有风险）

💡 关键是：**患者有权了解全部选择，做出知情决策！**

我们正在开发开源设备：
- 非侵入性
- 成本<200元
- 6路输出
- 安全可靠

📖 详细对比分析：
https://github.com/scj009999/TLSR8269_SixChannel_Pulse_Generator

⚠️ 免责声明：本文仅供信息参考，不构成医疗建议。

#帕金森 #DBS #治疗选择 #开源医疗 #信息透明

---

## 版本二：详细版（适合转发）

📢 致所有帕金森病患者和家属

【一个令人心痛的消息】

前几天听说，一位37岁的年轻帕友，在接受DBS手术（脑起搏器）不到两年后，离开了我们。

更让人愤怒的是，当有人在患者群里提醒大家关注手术风险时，**被管理员踢出了群**。

【为什么信息透明这么重要？】

很多患者和家属不知道：
❌ DBS手术需要开颅
❌ 存在感染、出血风险
❌ 术后需要长期调试
❌ 费用20-40万
❌ 并非适合所有人

但这些信息，很多群里不让说。

【帕金森病治疗的真相】

没有"最好"的方案，只有"最适合"的方案。

目前主要选择：

1️⃣ 药物治疗
- 历史悠久，方案成熟
- 但长期使用可能出现运动并发症

2️⃣ DBS手术
- 对部分患者效果显著
- 但需要开颅，有风险
- 费用高

3️⃣ 经颅电刺激（tDCS/tACS）
- 非侵入性，安全
- 可居家使用
- 费用较低
- 效果因人而异

4️⃣ 中医调理
- 整体调理
- 副作用少
- 效果较慢

【患者有权知道】

✅ 全部治疗方案
✅ 各自的风险和副作用
✅ 费用和长期负担
✅ 替代方案的存在

【我们在做的事】

开发开源经颅脉冲治疗仪：
- 非侵入性
- 物料成本<200元
- 6路独立输出
- 多重安全保护
- 完全开源透明

初衷：
> "能帮一些人就帮一些人。"
> "救一个人，胜造七级浮屠。"

【给家属的话】

不要让信息封锁害了家人。

在决定任何治疗前，请多问医生：
1. 有哪些选择？
2. 各自的风险？
3. 还有其他方案吗？

【重要提醒】

⚠️ 本文仅供信息参考，不构成医疗建议。
⚠️ 任何治疗请咨询专业医生。

【关于我们】

开源医疗项目
GitHub：scj009999/TLSR8269_SixChannel_Pulse_Generator

【欢迎】
- 转发分享
- 提出意见
- 参与项目

#帕金森 #DBS手术 #治疗选择 #患者权益 #信息透明 #开源医疗

---

## 版本三：情感版（适合朋友圈）

💔 今天想说点心里话

作为一个关注帕金森病的人，前几天听到一个消息，心情久久不能平静。

一位37岁的年轻帕友，走了。

他做过DBS手术。

更让人难受的是，当有人在群里提醒大家关注手术风险时，被踢了。

🤔 我在想：

如果他能知道更多信息...
如果他能了解其他选择...
如果他能做出更知情的决策...

结果会不会不一样？

📚 帕金森病治疗不止一种选择：

药物、手术、非侵入性刺激、中医调理...

每种都有优缺点。

关键是：**患者有权了解全部真相，做出自己的选择。**

🔧 我们在开发一个开源设备：
- 非侵入性
- 低成本
- 安全可靠
- 完全透明

不是为了替代现有治疗，
而是为了多一个选择，
为了让更多人用得起。

🙏 希望每一位帕友都能：
- 了解全部信息
- 做出知情选择
- 得到尊重和支持

> "能帮一些人就帮一些人。"

如果你认同，请转发。

⚠️ 免责声明：本文仅供信息参考，不构成医疗建议。

#帕金森 #患者权益 #信息透明 #开源医疗

---

## 版本四：问答版（适合群聊）

📢 帕友常见问题解答

Q1：药物效果不好就必须手术吗？
A：不一定。还有非侵入性刺激、中医调理等选择。

Q2：DBS手术安全吗？
A：有效，但需要开颅，存在风险。不是所有人都适合。

Q3：什么是经颅电刺激？
A：头皮电极通微弱电流，非侵入，可居家使用。

Q4：开源设备可靠吗？
A：研究性项目，多重安全保护，但不替代正规医疗。

Q5：为什么群里不让讨论手术风险？
A：这恰恰说明信息透明的重要性。患者有权了解全部真相。

📖 详细资料：
https://github.com/scj009999/TLSR8269_SixChannel_Pulse_Generator

⚠️ 免责声明：本文仅供信息参考，不构成医疗建议。

---

## 版本五：极简版（适合短信）

帕友注意：DBS手术有风险，不是唯一选择。还有药物、经颅电刺激、中医等方案。患者有权了解全部信息。我们在开发低成本开源设备，非侵入性，安全可靠。详情：github.com/scj009999/TLSR8269_SixChannel_Pulse_Generator

---

*所有版本均遵循非攻击性原则，客观陈述事实。*
*欢迎转发，请注明出处。*
