scj009999/TLSR8269_SixChannel_Pulse_Generator/docs/XIAOHONGSHU_POST.md

# 帕金森病家属必看！除了手术和吃药，还有这些选择💡

## 😢 一个让人心痛的故事

前几天听说一个事：
一个37岁的年轻帕友
做了DBS手术（脑起搏器）
不到两年...离开了😭

更让人心寒的是
当有人在群里提醒大家关注手术风险
**被踢出群了！**

## 🤔 为什么信息透明这么难？

很多患者和家属不知道：
- 手术有风险（感染、出血、硬件故障）
- 不是所有人都适合手术
- 术后需要长期调试
- 费用20-40万

但这些信息，很多群里不让说🚫

## 📊 四种治疗方案对比

| 方案 | 侵入性 | 费用 | 可居家 |
|---|---|---|---|
| 药物治疗 | ❌无 | 💰中等 | ✅ |
| DBS手术 | ⚠️开颅 | 💰💰💰20-40万 | ❌ |
| 经颅电刺激 | ❌无 | 💰较低 | ✅ |
| 中医调理 | ❌无 | 💰低 | ✅ |

## 💡 什么是经颅电刺激？

**简单说**：
- 在头皮上贴电极
- 通微弱电流
- 刺激大脑特定区域

**优点**：
✅ 不用开刀
✅ 可以在家做
✅ 费用低
✅ 安全

**缺点**：
⚠️ 效果因人而异
⚠️ 需要坚持

## 🏥 手术不是唯一选择

很多家属以为：
"药物效果不好就必须手术"

其实不是！

还有：
- 优化药物方案
- 非侵入性刺激
- 中医调理
- 康复训练

## ❓ 决定手术前一定要问

1. 我适合手术吗？
2. 手术风险有哪些？
3. 术后需要调试多少次？
4. 如果效果不佳怎么办？
5. 还有其他选择吗？

## 💪 我们在做的事

开发开源设备：
- 非侵入性
- 成本<200元
- 6路输出
- 安全可靠

**初衷**：
> 能帮一些人就帮一些人
> 救一个人，胜造七级浮屠

## 🙏 给家属的话

**患者有权知道**：
- 全部治疗方案
- 各自的风险
- 替代选择

**不要让信息封锁害了家人**

## 📌 重要提醒

本文仅供信息参考
不构成医疗建议
任何治疗请咨询专业医生

---

**关于我们**：
开源医疗项目
GitHub：scj009999/TLSR8269_SixChannel_Pulse_Generator

#帕金森 #DBS手术 #帕金森治疗 #患者家属 #医疗信息透明 #开源医疗
