scj009999/TLSR8269_SixChannel_Pulse_Generator/docs/ZHihu_ARTICLE.md

# 帕金森病治疗，除了手术和吃药，还有什么选择？

> **作者**：开源医疗项目团队  
> **声明**：本文仅供信息参考，不构成医疗建议。请与专业医生讨论具体方案。  
> **协议**：CC BY-SA 4.0

---

## 一、一个让人心痛的消息

前几天，一位帕友告诉我，一个患者群里的年轻病友（37岁）在接受脑深部电刺激手术（DBS）不到两年后，离开了我们。

更让人心寒的是，当有人在群里提醒大家关注手术风险时，被管理员踢出了群。

这让我意识到：**信息透明，有时候比治疗本身更重要。**

---

## 二、帕金森病治疗的真相

### 2.1 没有"最好"的方案，只有"最适合"的方案

很多病友和家属在确诊后，第一反应是："哪种方法效果最好？"

但真相是：**帕金森病目前无法治愈，各种治疗都是为了改善症状、提高生活质量。**

### 2.2 四种主流方案对比

| 方案 | 原理 | 侵入性 | 费用 | 可逆性 | 居家使用 |
|---|---|---|---|---|---|
| **药物治疗** | 补充多巴胺 | 无 | 中等 | 可逆 | ✅ |
| **DBS手术** | 植入电极刺激脑核团 | 有（开颅） | 20-40万 | 部分 | ❌需调试 |
| **经颅电刺激** | 头皮电极微弱电流 | 无 | 数千-数万 | 完全 | ✅ |
| **中医调理** | 整体调理，标本兼治 | 无 | 较低 | 可逆 | ✅ |

### 2.3 每种方案都需要了解什么

#### 药物治疗
- ✅ 历史悠久，方案成熟
- ⚠️ 长期使用可能出现运动并发症
- ⚠️ 不能阻止病情进展

#### DBS手术
- ✅ 对部分患者效果显著
- ⚠️ **需要开颅手术，存在风险**
- ⚠️ 术后需长期随访调试
- ⚠️ 费用较高
- ⚠️ 并非适合所有患者

> **重要提示**：手术决策需充分评估，选择有经验的医疗团队。

#### 经颅电刺激（tDCS/tACS）
- ✅ 非侵入性，安全性高
- ✅ 可居家使用
- ✅ 费用相对较低
- ⚠️ 效果个体差异大
- ⚠️ 需长期坚持

#### 中医调理
- ✅ 整体观念，副作用较少
- ✅ 可改善整体状态
- ⚠️ 效果较慢
- ⚠️ 需找到有经验的中医师

---

## 三、患者和家属最常问的问题

### Q1：手术是不是比保守治疗好？

**不一定。**

手术有其适用人群，但不是所有人都适合。需要考虑：
- 年龄和整体健康状况
- 病情阶段
- 对手术风险的接受程度
- 经济承受能力
- 术后随访的便利性

### Q2：非侵入性治疗是不是没效果？

**不是。**

多项研究显示，经颅电刺激对帕金森病的运动症状有改善作用，且安全性良好。虽然效果可能不如手术显著，但风险也低得多。

### Q3：可以多种方法一起用吗？

**可以，但需在医生指导下进行。**

很多病友采用"药物+非侵入性刺激+中医调理"的综合方案，取得了不错的效果。

### Q4：为什么群里不让讨论手术风险？

**这恰恰说明信息透明的重要性。**

患者有权了解：
- 治疗的全部风险
- 可能的并发症
- 替代方案的存在
- 真实的成功率

任何试图封锁信息的行为，都是对患者权利的侵犯。

---

## 四、我们正在做的事

### 4.1 开源经颅脉冲治疗仪

我们是一个开源医疗项目团队，正在开发一种**低成本、非侵入性**的神经调控设备：

| 特点 | 说明 |
|---|---|
| **非侵入性** | 头皮表面刺激，无需手术 |
| **低成本** | 物料成本<200元 |
| **开源** | 硬件设计、软件代码完全开放 |
| **可定制** | 频率、强度、时间可调 |
| **多通道** | 6路独立输出 |
| **安全保护** | 多重电流限制、阻抗检测 |

### 4.2 项目初衷

> **"能帮一些人就帮一些人。"**
> 
> **"救一个人，胜造七级浮屠。"**

我们希望通过技术手段：
- 让低收入患者也能获得治疗
- 让信息透明，不再被封锁
- 让患者有知情选择的权利

---

## 五、给病友和家属的建议

### 5.1 做知情选择

**患者有权了解**：
- ✅ 疾病的真实情况
- ✅ 各种治疗方案的利弊
- ✅ 可能的风险和副作用
- ✅ 费用和长期负担
- ✅ 替代方案的存在

### 5.2 多问几个问题

在决定任何治疗方案前，建议问医生：
1. 这个方案的原理是什么？
2. 预期效果如何？
3. 可能的风险和副作用？
4. 费用多少？医保覆盖吗？
5. 如果效果不佳怎么办？
6. 还有其他选择吗？

### 5.3 寻找可靠信息

| 可靠来源 | 注意事项 |
|---|---|
| 学术期刊 | 注意研究质量和样本量 |
| 医生建议 | 多咨询几位专家 |
| 官方指南 | 注意更新日期 |
| 患者组织 | 注意个体差异 |

**警惕**：
- ❌ "包治百病"
- ❌ "100%有效"
- ❌ "无副作用"
- ❌ "最新突破"

---

## 六、写在最后

37岁的离世，是一个悲剧。

但比悲剧更可怕的，是**真相被掩盖，患者被蒙在鼓里**。

我们希望通过这篇文章，让更多病友和家属：
- 了解全部选择
- 做出知情决策
- 不再被信息封锁所害

**每一位患者，都值得被诚实对待。**

---

## 七、关于我们

- **项目仓库**：https://github.com/scj009999/TLSR8269_SixChannel_Pulse_Generator
- **项目特点**：开源、非商业、公益
- **参与方式**：使用、反馈、贡献代码、传播理念

---

**免责声明**：本文仅供信息参考，不构成医疗建议。任何治疗决策请咨询专业医生。使用任何设备需自行承担风险。

---

*本文遵循开放、透明、非商业原则。*
*欢迎转载，请注明出处。*
