scj009999/TLSR8269_SixChannel_Pulse_Generator/hardware/schematic.md

# TLSR8269 六路脉冲发生器 - 硬件原理图

## 系统框图

```
┌─────────────────────────────────────────────────────────┐
│                    电源输入 (3.3V)                        │
│                         │                               │
│                    ┌────┴────┐                          │
│                    │  LDO    │                          │
│                    │ 3.3V    │                          │
│                    └────┬────┘                          │
│                         │                               │
│    ┌────────────────────┼────────────────────┐         │
│    │                    │                    │         │
│    ▼                    ▼                    ▼         │
│ ┌──────┐           ┌────────┐           ┌────────┐    │
│ │ 去耦  │           │TLSR8269│           │ 晶振   │    │
│ │电容   │           │        │           │24MHz   │    │
│ │100nF │           │        │           │        │    │
│ └──────┘           │        │           └────────┘    │
│                    │        │                          │
│                    │  PA0 ──┼──► CH0 (PWM0)           │
│                    │  PA1 ──┼──► CH1 (PWM1)           │
│                    │  PA2 ──┼──► CH2 (PWM2)           │
│                    │  PA3 ──┼──► CH3 (PWM3)           │
│                    │  PA4 ──┼──► CH4 (PWM4)           │
│                    │  PA5 ──┼──► CH5 (PWM5)           │
│                    │        │                          │
│                    │  PB1 ──┼──► UART_TX (调试)       │
│                    │  PB2 ──┼──◄ UART_RX (调试)       │
│                    │        │                          │
│                    │  SWS  ─┼──► 烧录接口             │
│                    │  RESET─┼──► 复位按钮             │
│                    └────────┘                          │
│                                                        │
└─────────────────────────────────────────────────────────┘
```

## 原理图

### 1. 主控芯片 TLSR8269F512 (QFN48)

```
                    VCC (3.3V)
                      │
                      ├─[100nF]─ GND  (去耦电容)
                      │
         ┌────────────┴────────────┐
         │                         │
    ┌────┴────┐               ┌────┴────┐
    │  TLSR   │               │  TLSR   │
    │ 8269    │               │ 8269    │
    │         │               │         │
    │  VCC    │───3.3V        │  GND    │───GND
    │  (47)   │               │  (46)   │
    │         │               │         │
    │  PA0(1) │───CH0         │  PA5(6) │───CH5
    │  PA1(2) │───CH1         │  PB0(7) │───NC
    │  PA2(3) │───CH2         │  PB1(8) │───UART_TX
    │  PA3(4) │───CH3         │  PB2(9) │───UART_RX
    │  PA4(5) │───CH4         │  PB3(10)│───NC
    │         │               │         │
    │  PC0(15)│───NC          │  PC7(22)│───NC
    │  PC1(16)│───NC          │  PD0(23)│───NC
    │  PC2(17)│───NC          │  PD1(24)│───NC
    │  PC3(18)│───NC          │  PD2(25)│───NC
    │         │               │         │
    │  XTAL(  │               │  XTAL(  │
    │  27,28) │───24MHz晶振   │  29,30) │
    │         │               │         │
    │  SWS    │───烧录接口    │  RESET  │───复位
    │  (31)   │               │  (32)   │
    └─────────┘               └─────────┘
```

### 2. 电源电路

```
    VIN (5V或3.3V)
      │
      ├─[10µF]──┬─── GND
      │         │
      │    ┌────┴────┐
      │    │   LDO   │
      └────┤ 3.3V    ├──── VCC (3.3V)
           │  AMS1117│
           └────┬────┘
                │
                ├─[100nF]── GND (芯片近端)
                │
                ├─[10µF]─── GND
                │
                └─────── VCC_3V3
```

### 3. 晶振电路

```
           24MHz晶振
         ┌─────┬─────┐
         │     │     │
    XTAL─┤     │     ├─XTAL
    (27) │     │     │ (28)
         │     │     │
         └──┬──┴──┬──┘
            │     │
           [22pF][22pF]
            │     │
           GND   GND
```

### 4. 复位电路

```
              VCC (3.3V)
                │
                ├─[10kΩ]────┬─── RESET (Pin 32)
                │            │
                │       ┌────┴────┐
                │       │  按键   │
                │       │  RESET  │
                │       └────┬────┘
                │            │
               GND          GND
```

### 5. 烧录接口 (SWS)

```
    烧录器接口:
    
    ┌─────────┐
    │  VCC    │─── 3.3V
    │  GND    │─── GND
    │  SWS    │─── SWS (Pin 31)
    │  RESET  │─── RESET
    └─────────┘
    
    注意：Telink烧录器使用单线调试(SWS)
```

### 6. 脉冲输出接口

```
    输出端子 (6路PWM输出):
    
    ┌─────────────────────────┐
    │  CH0  │  PA0  │  PWM0   │
    │  CH1  │  PA1  │  PWM1   │
    │  CH2  │  PA2  │  PWM2   │
    │  CH3  │  PA3  │  PWM3   │
    │  CH4  │  PA4  │  PWM4   │
    │  CH5  │  PA5  │  PWM5   │
    │  GND  │       │  地线   │
    │  VCC  │       │  3.3V   │
    └─────────────────────────┘
    
    输出特性：
    - 高电平：3.3V
    - 低电平：0V
    - 驱动能力：约8mA/引脚
    - 建议外接驱动电路用于大功率负载
```

### 7. 调试串口

```
    UART接口 (可选):
    
    ┌─────────┐
    │  TX     │─── PB1 (Pin 8)  → 连接到USB转TTL的RX
    │  RX     │─── PB2 (Pin 9)  ← 连接到USB转TTL的TX
    │  GND    │─── GND
    └─────────┘
    
    波特率：115200
    数据位：8
    停止位：1
    校验位：无
```

## PCB布局建议

### 顶层布局

```
┌────────────────────────────────────────┐
│  ┌──────────────┐                      │
│  │   TLSR8269   │    ┌─────────────┐  │
│  │              │    │   晶振      │  │
│  │  PA0-PA5     │    │   24MHz     │  │
│  │  (左侧输出)   │    └─────────────┘  │
│  │              │                      │
│  │  PB1-PB2     │    ┌─────────────┐  │
│  │  (右侧调试)   │    │   LDO       │  │
│  │              │    │   3.3V      │  │
│  └──────────────┘    └─────────────┘  │
│                                        │
│  [CH0] [CH1] [CH2] [CH3] [CH4] [CH5]  │
│   ○    ○    ○    ○    ○    ○         │
│                                        │
│  [GND] [VCC] [TX]  [RX]  [SWS] [RST] │
│   ○    ○    ○    ○    ○    ○         │
└────────────────────────────────────────┘
```

### 布局要点

1. **去耦电容**: 尽量靠近芯片VCC引脚放置
2. **晶振**: 靠近XTAL引脚，走线尽量短
3. **PWM输出**: 等长走线，减少信号 skew
4. **地线**: 大面积铺地，减少EMI
5. **电源**: 星型拓扑，避免压降

## BOM清单

| 序号 | 器件 | 型号/参数 | 数量 | 备注 |
|---|---|---|---|---|
| 1 | 主控芯片 | TLSR8269F512ET48 | 1 | QFN48封装 |
| 2 | 晶振 | 24MHz无源晶振 | 1 | 负载电容22pF |
| 3 | LDO | AMS1117-3.3 | 1 | SOT-223 |
| 4 | 电容 | 100nF/0603 | 5 | 去耦 |
| 5 | 电容 | 10µF/0805 | 2 | 电源滤波 |
| 6 | 电容 | 22pF/0603 | 2 | 晶振负载 |
| 7 | 电阻 | 10kΩ/0603 | 1 | 上拉 |
| 8 | 按键 | 轻触开关 | 1 | 复位 |
| 9 | 排针 | 2.54mm间距 | 若干 | 接口 |

## 注意事项

1. **防静电**: TLSR8269为CMOS器件，注意ESD防护
2. **电源顺序**: 确保3.3V稳定后再启动芯片
3. **烧录**: 首次烧录需要Telink专用烧录器
4. **散热**: 正常工作电流约40mA，一般不需额外散热
