scj009999/TLSR8269_SixChannel_Pulse_Generator/task-summary_2026-05-09_v3.md

# 任务总结：TLSR8269 开源经颅脉冲治疗仪 v3

## 更新内容（2026-05-09 凌晨）

### 1. 完善GitHub仓库文件
已准备以下文件供上传至 https://github.com/scj009999/TLSR8269_SixChannel_Pulse_Generator

#### 核心文档
| 文件 | 路径 | 说明 |
|---|---|---|
| README.md | / | 完整项目说明（含成本对比、安全警告） |
| LICENSE | / | 双重许可证：GPL v3 + CERN OHL v2 + 医疗附加条款 |

#### Arduino库
| 文件 | 路径 | 说明 |
|---|---|---|
| PulseTherapy.h | /PulseTherapy/ | 安全库头文件 |
| PulseTherapy.cpp | /PulseTherapy/ | 安全库实现 |
| keywords.txt | /PulseTherapy/ | Arduino IDE语法高亮 |
| ParkinsonTherapy.ino | /PulseTherapy/examples/ParkinsonTherapy/ | 完整治疗示例 |

#### 文档
| 文件 | 路径 | 说明 |
|---|---|---|
| MEDICAL_SAFETY.md | /docs/ | 医疗安全设计规范 |
| TARGETING_SYSTEM.md | /docs/ | 靶点定位系统 |
| OPEN_SOURCE_LETTER.md | /docs/ | 致国家药监局信（可直接使用） |
| COST_ANALYSIS.md | /docs/ | 成本分析（开源¥99 vs 商用¥30000） |

### 2. 关键特性

#### 安全设计
- 硬件看门狗（1秒超时）
- 电流实时监测（每路独立ADC）
- 电极阻抗检测（脱落报警）
- 电池电压监控
- 硬件急停（独立中断）
- 参数硬限制（不可软件绕过）

#### 治疗模式
- MODE_PARKINSON_STD: 40Hz, 50%, 20min
- MODE_PARKINSON_INTENSE: 40Hz, 70%, 30min
- MODE_PARKINSON_CONSERVATIVE: 20Hz, 30%, 15min
- MODE_SLEEP: 10Hz, 30%, 60min
- MODE_PAIN_RELIEF: 100Hz, 50%, 20min

#### 靶点定位
- 10-20 EEG简化定位法
- 六通道分配方案（3种）
- 家用简易定位帽设计
- 阻抗检测验证接触质量

### 3. 成本分析

| 项目 | 商用设备 | 开源方案 | 节省 |
|---|---|---|---|
| 设备价格 | ¥15,000-30,000 | ¥99 | 99.7% |
| 医院年费 | ¥150,000 | ¥0 | 100% |
| 3年总费用 | ¥525,000 | ¥1,299 | 99.8% |

物料成本：¥65
建议售价：¥99

### 4. 开源许可

- 软件：GPL v3
- 硬件：CERN OHL v2
- 附加：医疗安全条款、专利授权、非歧视条款

### 5. 待办事项

- [ ] 上传所有文件到GitHub
- [ ] 制作PCB（嘉立创）
- [ ] 申请创新医疗器械审批
- [ ] 开展临床试验
- [ ] 建立患者社区

## 项目意义

为帕金森患者提供：
- 成本降低99.7%
- 完全透明开源
- 家庭自主治疗
- 个性化参数调节

**每一个患者，无论贫富，都值得有尊严地治疗。**
