scj009999/TLSR8269_SixChannel_Pulse_Generator/task-summary_2026-05-10_v3.md

# 任务总结：医疗仪器电源设计规范

**日期**：2026-05-10  
**任务**：整理医疗级电源设计国家标准和实施方案

---

## 一、用户问题

**询问**：外围电源供电电路，医疗仪器有什么特别要求？芯片要求3.3V/50mA，尽量贴近国家标准。

---

## 二、医疗电源核心要求

### 2.1 国家标准依据
- **GB 9706.1-2020**《医用电气设备 第1部分：基本安全和基本性能的通用要求》
- **YY 0505-2012**《医用电气设备 电磁兼容》

### 2.2 关键参数

| 参数 | 要求 | 说明 |
|---|---|---|
| **隔离耐压** | ≥3000V AC / 4242V DC | 患者电路与地之间 |
| **漏电流** | <100µA (正常) / <500µA (故障) | BF型设备要求 |
| **接地电阻** | <0.1Ω | 保护接地 |
| **绝缘电阻** | >50MΩ | 患者电路与地之间 |

### 2.3 安全分类
本项目属于**BF型**（与患者头部皮肤接触，需电气隔离）

---

## 三、推荐电源架构

```
输入电源 (5V USB 或 3.7V锂电池)
    │
    ├─[保险丝 500mA]─────────────┐
    ├─[TVS管 5V]─────────────────┤ 输入保护
    ├─[共模电感]─────────────────┤ EMI滤波
    │                            │
    ▼                            ▼
┌─────────────┐          ┌─────────────┐
│ 控制电源     │          │ 隔离DC-DC    │
│ AMS1117     │          │ B0505S-1W   │
│ 3.3V/1A    │          │ 3000V隔离    │
│             │          │             │
│ → 蓝牙MCU   │          │ → 脉冲输出   │
│ → LED指示   │          │ → 电极驱动   │
│ → 急停电路   │          │ → 电流检测   │
└─────────────┘          └─────────────┘
     GND                      ISOGND
   (系统地)                  (隔离地)
                                 │
                            单点连接
```

---

## 四、详细电路设计

### 4.1 输入保护
- 保险丝：500mA自恢复（过流保护）
- TVS管：SMBJ5.0A（过压保护）
- 压敏电阻：5D470K（浪涌保护）
- 共模电感：ACM2012-900-2P（EMI滤波）

### 4.2 控制电源（非隔离）
- LDO：AMS1117-3.3（3.3V/1A，低噪声）
- 输入滤波：10µF电容
- 输出滤波：10µF + 100nF电容

### 4.3 隔离电源（患者电路）
- 隔离DC-DC：B0505S-1W（5V→5V，3000V隔离）
- 或 B0503.3S-1W（直接输出3.3V，省去LDO）
- 输入输出滤波：10µF + 100nF电容

### 4.4 电池供电（可选）
- 充电管理：TP4056（1A线性充电）
- 升压DC-DC：MT3608（3.7V→5V）
- 电池保护：DW01+FS8205A（过充/过放/短路）

---

## 五、关键设计要点

### 5.1 隔离设计
- 患者电路与控制系统完全隔离
- 隔离电压 ≥ 3000V AC
- 爬电距离 ≥ 4mm
- 电气间隙 ≥ 2.5mm

### 5.2 漏电流控制
- 使用隔离DC-DC
- 光耦隔离所有患者侧信号
- 减少患者侧对地电容

### 5.3 EMI/EMC设计
- 输入滤波：共模电感 + X/Y电容
- 屏蔽：患者电路区域铺铜接地
- 去耦：每个芯片电源引脚旁100nF电容

---

## 六、电源成本

### USB供电方案（推荐）
| 部分 | 成本(¥) |
|---|---|
| 输入保护 | 2.50 |
| 控制电源 | 0.90 |
| 隔离电源 | 3.45 |
| 反接保护 | 0.30 |
| **总计** | **7.15** |

### 电池供电方案
| 部分 | 成本(¥) |
|---|---|
| USB供电部分 | 7.15 |
| 充电管理 | 1.55 |
| 升压DC-DC | 2.60 |
| 电池保护 | 0.80 |
| 18650电池 | 15.00 |
| **总计** | **27.10** |

---

## 七、测试验证

### 7.1 电气安全测试
- 耐压测试：3000V AC，1分钟，漏电流<1mA
- 绝缘电阻：>50MΩ（500V DC）
- 接地电阻：<0.1Ω
- 漏电流：<100µA（正常），<500µA（故障）

### 7.2 功能测试
- 输出电压：3.3V±5%
- 负载调整率：<±1%
- 纹波噪声：<50mVpp
- 效率：>80%

### 7.3 可靠性测试
- 高温工作：+40℃，4小时
- 低温工作：+5℃，4小时
- 湿热试验：+40℃，93%RH，48小时

---

## 八、新建文件

### 1. MEDICAL_POWER_DESIGN.md
- **内容**：完整医疗电源设计规范
- **包含**：
  - 国家标准依据
  - 电源架构设计
  - 详细电路图
  - 保护电路设计
  - 测试验证方法

### 2. POWER_BOM.md
- **内容**：电源部分BOM清单
- **包含**：
  - 输入保护电路BOM
  - 控制电源BOM
  - 隔离电源BOM
  - 电池供电BOM
  - 成本汇总

---

## 九、关键建议

### 9.1 设计建议
1. **务必使用隔离DC-DC**（B0505S-1W或B0503.3S-1W）
2. **隔离电压≥3000VDC**
3. **漏电流<100µA**
4. **单点接地**，避免地环路

### 9.2 采购建议
1. 隔离DC-DC推荐金升阳品牌
2. LDO可用AMS1117或XC6206
3. 电容建议X7R或C0G材质

### 9.3 测试建议
1. 100%耐压测试
2. 漏电流测试
3. 绝缘电阻测试

---

## 十、下一步行动

1. **确认供电方式**：USB供电 or 电池供电
2. **选择隔离DC-DC型号**：B0505S-1W or B0503.3S-1W
3. **完善KiCad原理图**：添加电源部分
4. **准备测试设备**：耐压测试仪、漏电流测试仪

---

*医疗电源设计安全第一，务必严格按照国家标准执行！*
