scj009999/TLSR8269_SixChannel_Pulse_Generator/task-summary_2026-05-10_v4.md

# 任务总结：国产AI辅助PCB设计软件搜索

**日期**：2026-05-10  
**任务**：搜索国产AI辅助PCB设计软件，帮助用户找到合适的工具

---

## 一、用户需求

用户回忆曾用过一款CAD软件，有AI辅助功能，能够：
- 自动生成符合国家标准的外围电路
- 自动布线
- 记得是国产软件

---

## 二、搜索结果

### 搜索关键词
1. "国产AI辅助PCB设计软件 自动生成电路 自动布线"
2. "国产PCB设计软件 AI智能 自动布局 立创EDA 华秋DFM"
3. "Quilter AI PCB 国产 自动布线 自动生成电路"

### 找到的相关软件

#### 1. 华秋DFM + 华秋小助手（KiCad Copilot）⭐ 最可能
- **公司**：深圳华秋电子
- **特点**：
  - 纯国产，永久免费
  - AI电路识别（拍照识别）
  - DFM可制造性分析
  - 一键输出Gerber/BOM/坐标
  - 2026年3月推出AI EDA工具"华秋小助手"
- **官网**：https://dfm.elecfans.com/

#### 2. 立创EDA
- **公司**：嘉立创
- **特点**：
  - 国产免费PCB设计软件
  - 自动布线功能
  - 3D预览
  - 与嘉立创生产无缝衔接
- **官网**：https://lceda.cn/

#### 3. Quilter AI（国外）
- **特点**：
  - AI自动布线
  - 支持KiCad/Altium/Cadence
  - 需要先有原理图
- **注意**：国外软件，非国产

---

## 三、用户确认

用户确认：**华秋DFM用过，非常好，能够避免很多错误**

用户决定：**学习使用华秋小助手AI功能**

---

## 四、新建文件

### HUAQIU_AI_GUIDE.md
- **内容**：华秋小助手（KiCad Copilot）使用指南
- **包含**：
  - 软件下载与安装
  - AI功能介绍
  - 医疗电路设计应用
  - 针对本项目的使用流程
  - 实用技巧（快速查询、成本优化、标准查询）
  - 常见问题解答
  - 学习资源

---

## 五、华秋小助手使用流程（本项目）

### 步骤1：导入设计
1. 在KiCad中完成原理图
2. 导出网表
3. 在KiCad PCB Editor中布局
4. 保存为.kicad_pcb
5. 在华秋DFM中打开

### 步骤2：AI分析
- 使用自然语言与AI对话
- 检查医疗安全隐患
- 检查GB 9706.1-2020合规性
- 获取优化建议

### 步骤3：优化设计
- 调整元件位置
- 修改走线
- 添加测试点
- 完善丝印

### 步骤4：DFM检查
- 一键分析设计隐患
- 根据建议修改
- 重新分析直到通过

### 步骤5：输出生产文件
- 一键输出Gerber
- 生成BOM清单
- 生成坐标文件
- 嘉立创下单

---

## 六、关键功能示例

### AI检查医疗安全
```
用户：请检查这个医疗电路的安全隐患
AI：发现隔离距离不足、电流检测电阻功率不足等问题...
```

### 符合国家标准检查
```
用户：请检查是否符合GB 9706.1-2020
AI：隔离耐压、漏电流、接地检查...
```

### 成本优化
```
用户：如何降低成本？
AI：统一封装、批量采购、拼板设计...
```

---

## 七、下一步行动

1. **下载华秋DFM**
   - 访问 https://dfm.elecfans.com/
   - 下载安装（约150MB）

2. **学习使用**
   - 注册登录
   - 导入KiCad设计
   - 尝试AI对话功能

3. **应用到本项目**
   - 导入TLSR8269原理图
   - 使用AI检查医疗安全
   - 优化设计

4. **输出生产文件**
   - 生成Gerber
   - 嘉立创下单

---

## 八、参考资源

- 华秋DFM官网：https://dfm.elecfans.com/
- 立创EDA：https://lceda.cn/
- 华秋论坛：https://bbs.elecfans.com/

---

*华秋DFM是国产PCB分析软件的佼佼者，AI功能可以大大提高医疗电路设计的效率和安全性。*
