scj009999/TLSR8269_SixChannel_Pulse_Generator/task-summary_2026-05-10_v5.md

# 任务总结：华秋一站式生产与3D外壳设计

**日期**：2026-05-10  
**任务**：整理华秋打板流程和3D外壳设计准备

---

## 一、用户确认

用户已有华秋账号，计划：
1. **华秋打样**：5片起，焊接一步到位
2. **收到样品**：验证后设计3D外壳
3. **外壳生产**：华秋3D打印或开模

---

## 二、华秋服务范围

| 服务 | 说明 | 费用 |
|---|---|---|
| **DFM分析** | 设计可制造性检查 | 免费 |
| **PCB打样** | 5片起，多层板 | ¥50-200/5片 |
| **SMT贴片** | 元器件采购+焊接 | 按点数计费 |
| **3D打印** | 外壳原型制作 | 按克计费 |
| **CNC加工** | 金属/塑料外壳 | 按工艺计费 |

---

## 三、生产流程

### 第一步：DFM分析
- 使用华秋DFM软件
- 一键分析设计隐患
- 根据建议修改

### 第二步：PCB打样
- 上传Gerber
- 选择参数（4层板、1.6mm、沉金）
- 预计费用：¥100-150/5片
- 预计时间：5-7天

### 第三步：SMT贴片（可选）
- 准备BOM和坐标文件
- 华秋代采购+焊接
- 预计费用：¥50-100
- 预计时间：5-8天

### 第四步：3D外壳
- 测量PCB实际尺寸
- 设计3D模型（Fusion 360）
- 华秋3D打印
- 预计费用：¥50-100
- 预计时间：3-5天

---

## 四、时间规划

```
Week 1: 完成KiCad设计 + DFM分析
Week 2: PCB打样（5-7天）
Week 3: 收到PCB，手工焊接测试
Week 4: SMT贴片（可选，5-8天）
Week 5: 3D外壳设计 + 打印
Week 6: 组装整机 + 功能测试

总计：约6周完成原型
```

---

## 五、成本估算

### 单台原型（5片）
| 项目 | 费用(¥) |
|---|---|
| PCB打样 | 120 |
| 元器件 | 80 |
| SMT贴片 | 80 |
| 3D外壳 | 80 |
| **小计** | **360** |
| **每片成本** | **72** |

### 小批量（100台）
| 项目 | 费用(¥) |
|---|---|
| PCB | 1500 |
| 元器件 | 6000 |
| SMT贴片 | 4000 |
| 外壳（开模） | 3000 |
| **总计** | **14500** |
| **单台成本** | **145** |

**目标<¥200，完全可以实现！**

---

## 六、新建文件

### 1. HUAQIU_PRODUCTION_GUIDE.md
- **内容**：华秋一站式生产指南
- **包含**：
  - 华秋服务介绍
  - PCB打样流程
  - SMT贴片流程
  - 3D打印流程
  - 时间规划
  - 成本估算
  - 质量控制

### 2. SHELL_DESIGN_GUIDE.md
- **内容**：3D外壳设计指南
- **包含**：
  - 外壳设计要求
  - 接口布局
  - 材料选择
  - 3D建模步骤（Fusion 360）
  - 华秋3D打印下单
  - 装配验证
  - 开模准备

---

## 七、关键参数

### PCB参数
- 层数：4层
- 板厚：1.6mm
- 铜厚：1oz
- 表面处理：沉金(ENIG)
- 阻焊：绿色
- 丝印：白色

### 外壳参数
- 材料：ABS
- 壁厚：2mm
- 颜色：白色
- 防护等级：IP54

---

## 八、下一步行动

1. **本周**：完成KiCad设计 + 华秋DFM分析
2. **下周**：华秋下单PCB打样
3. **第3周**：收到PCB，验证测试
4. **第4周**：准备BOM，下单SMT
5. **第5周**：设计3D外壳，3D打印
6. **第6周**：组装整机，功能测试

---

## 九、参考资源

- 华秋PCB：https://www.hqpcb.com/
- 华秋SMT：https://smt.hqpcb.com/
- 华秋3D：https://3d.hqpcb.com/
- Fusion 360：https://www.autodesk.com/products/fusion-360

---

*华秋一站式服务可以大大简化生产流程，建议先打样5片验证，确认无误后再批量生产。*
