scj009999/TLSR8269_SixChannel_Pulse_Generator/task-summary_2026-05-10_v6.md

# 任务总结：头戴式电极设计与功率调节方案

**日期**：2026-05-10  
**任务**：设计头戴式电极连接方案和功率调节方式

---

## 一、用户需求

1. **头戴式电极**：6路输出，头戴式，自制电极和硅胶导线
2. **功率调节**：软件实现 vs 外接电位器

---

## 二、头戴式电极设计

### 2.1 电极布局（国际10-20系统）

| 通道 | 位置 | 脑区 | 功能 |
|---|---|---|---|
| CH1 | F3-F4 | 背外侧前额叶 | 运动计划 |
| CH2 | C3-C4 | 初级运动皮层 | 运动控制 |
| CH3 | P3-P4 | 顶叶联合区 | 感觉整合 |
| CH4 | F7-F8 | 前额叶外侧 | 语言执行 |
| CH5 | T3-T4 | 颞叶 | 听觉记忆 |
| CH6 | O1-O2 | 枕叶 | 视觉处理 |

### 2.2 自制电极材料

| 材料 | 规格 | 数量 | 来源 |
|---|---|---|---|
| 碳橡胶片 | 20mm直径 | 12片 | 淘宝/京东 |
| 导电凝胶 | 医用级 | 1瓶 | 医疗器械店 |
| 硅胶导线 | 2芯屏蔽线1.5m | 6条 | 电子市场 |
| 香蕉插头 | 4mm | 12个 | 电子市场 |
| 魔术贴头带 | 可调节 | 1条 | 运动用品店 |

### 2.3 电极成本

- 材料总计：约¥116
- 制作时间：2-3天

---

## 三、功率调节方案对比

### 3.1 三种方案

| 方案 | 精度 | 易用性 | 成本 | 功能 |
|---|---|---|---|---|
| **纯软件** | ⭐⭐⭐⭐⭐ | ⭐⭐⭐ | ¥26 | 丰富 |
| **纯硬件** | ⭐⭐ | ⭐⭐⭐⭐⭐ | ¥38 | 简单 |
| **混合（推荐）** | ⭐⭐⭐⭐ | ⭐⭐⭐⭐⭐ | ¥38 | 最全 |

### 3.2 推荐方案：混合调节

**设计**：
- 1个总强度电位器（粗调）
- 手机APP软件细调
- OLED显示当前强度
- 急停按钮

**优点**：
- 老人可用旋钮快速调节
- 年轻人可用APP精确控制
- OLED显示直观
- 多重安全保护

**成本**：仅比纯软件多¥12

---

## 四、电路设计

### 4.1 恒流源电路

```
PWM输入 → 运放(LM358) → 采样电阻 → 电极输出
                ↑
           电流检测(ADC)
```

### 4.2 六路输出

- 6路独立PWM输出
- 每路独立电流检测
- 每路最大5mA（硬件限流）
- 软件限流2mA（安全保护）

### 4.3 安全保护

1. 硬件限流：5mA
2. 软件限流：2mA
3. 过流保护：>2mA自动切断
4. 开路检测：电极脱落报警
5. 急停按钮：物理切断
6. 超时保护：30分钟自动停止

---

## 五、强度分级

| 级别 | 电流 | 适用人群 |
|---|---|---|
| 1级 | 0.1-0.3mA | 初次使用 |
| 2级 | 0.3-0.5mA | 敏感人群 |
| 3级 | 0.5-1.0mA | 标准治疗 |
| 4级 | 1.0-1.5mA | 耐受人群 |
| 5级 | 1.5-2.0mA | 医生指导 |

**警告**：超过2mA需医生指导！

---

## 六、刺激模式

| 模式 | 频率 | 占空比 | 适用症状 |
|---|---|---|---|
| 舒缓模式 | 1Hz | 30% | 焦虑失眠 |
| 标准模式 | 10Hz | 50% | 运动障碍 |
| 强化模式 | 20Hz | 70% | 肌肉僵硬 |
| 自定义 | 1-100Hz | 10-90% | 医生设定 |

---

## 七、新建文件

### 1. ELECTRODE_DESIGN.md
- **内容**：头戴式电极完整设计
- **包含**：
  - 电极布局（10-20系统）
  - 自制电极材料清单
  - 制作步骤
  - 恒流源电路
  - 六路输出设计
  - 软件实现
  - 手机APP界面
  - 安全规范
  - 成本估算（¥270）

### 2. POWER_CONTROL_COMPARISON.md
- **内容**：功率调节方案对比
- **包含**：
  - 三种方案详细对比
  - 成本分析
  - 安全性对比
  - 用户体验对比
  - 推荐方案（混合调节）
  - 实现电路
  - 使用流程

---

## 八、关键决策

### 功率调节方式
**推荐：混合调节**
- 电位器粗调 + 软件细调 + OLED显示
- 兼顾老人易用性和精确控制
- 成本仅增加¥12

### 电极类型
**推荐：碳橡胶电极**
- 柔软舒适，适合家用
- 可重复使用
- 成本适中

### 连接方式
**推荐：香蕉插头**
- 连接可靠
- 易于插拔
- 标准化接口

---

## 九、下一步行动

1. **采购材料**
   - 电子元器件（¥59）
   - 电极材料（¥116）
   - 外壳材料（¥95）

2. **制作电极**
   - 裁剪碳橡胶片
   - 连接导线和插头
   - 安装到头带

3. **焊接电路**
   - 主控板
   - 六路恒流源
   - 电流检测

4. **软件开发**
   - PWM控制
   - 电流闭环
   - 蓝牙通信
   - 手机APP

5. **测试验证**
   - 电气测试
   - 功能测试
   - 安全测试

---

## 十、成本汇总

| 项目 | 费用(¥) |
|---|---|
| 电子元器件 | 59 |
| 电极材料 | 116 |
| 外壳材料 | 95 |
| **总计** | **270** |
| **目标** | **<200** |

**优化方向**：批量采购可降低30-40%

---

*本设计遵循医疗电气安全标准，建议在医生指导下使用。*
