scj009999/TLSR8269_SixChannel_Pulse_Generator/task-summary_2026-05-13_v17.md

# 任务总结：CR8269F512E132TKM1815 芯片模块文档

**日期**：2026-05-13  
**任务**：为用户收购的CR8269F512E132TKM1815芯片生成引脚定义和模块使用指南

---

## 一、采购信息

| 项目 | 信息 |
|---|---|
| **采购平台** | 闲鱼 |
| **芯片型号** | CR8269F512E132TKM1815 |
| **对应型号** | TLSR8269F512ET32 |
| **采购数量** | 1000片 |
| **单价** | 1.5元/片 |
| **总价** | 1500元 |
| **模块状态** | 已做成模块，开机可反复擦洗 |
| **Flash容量** | 512KB |
| **封装类型** | QFN32 |

---

## 二、已完成工作

### 2.1 新建文件

**CR8269F512E132TKM1815_Pinout.md**（7149字节）
- 芯片基本信息
- QFN32引脚分配表（32个引脚）
- 功能分组详解（PWM、ADC、I2C、UART、控制信号、时钟、烧录）
- 电源设计建议
- PCB布局建议（晶振、光耦隔离）
- 模块使用说明
- 本项目引脚分配总结
- 焊接、调试、医疗级注意事项

**CR8269F512E132TKM1815_Module_Guide.md**（7108字节）
- 模块外观识别（4种常见形式）
- 模块测试步骤（上电前检查、首次上电、烧录测试）
- 烧录方法详解（Telink BDT、USB转串口）
- 模块引脚扩展（飞线、转接板、重新焊接）
- 模块测试程序（最小测试、PWM测试、ADC测试）
- 常见问题排查（无法上电、无法烧录、程序不运行、PWM无输出）
- 模块改造建议（增加排针、测试点、标识）
- 批量测试方案（测试夹具、测试流程、测试记录）
- 防静电、防短路、防过压注意事项

---

## 三、核心内容

### 3.1 引脚分配

| 功能 | 引脚 | 数量 |
|---|---|---|
| PWM输出 | PA0-PA5 | 6路 |
| I2C接口 | PB0, PB3 | 2路 |
| UART调试 | PB1, PB2 | 2路 |
| ADC输入 | PC0-PC5 | 6路 |
| 控制信号 | PD0, PD1 | 2路 |
| 时钟 | XTAL (19,20) | 1路 |
| 烧录 | SWS, RESET | 2路 |
| 电源 | VCC, GND | 多路 |

### 3.2 关键参数

- **主频**：48MHz
- **Flash**：512KB
- **SRAM**：32KB
- **PWM**：6路，1Hz-8MHz
- **ADC**：6路，12位
- **蓝牙**：BLE 5.0
- **工作电压**：1.8-3.6V（典型3.3V）

### 3.3 烧录方法

**Telink BDT烧录**：
1. 连接SWS、RESET、VCC、GND
2. 打开Telink BDT软件
3. 选择芯片型号TLSR8269
4. 加载固件文件（.bin）
5. 点击Download按钮

**USB转串口烧录（备用）**：
1. 连接TX、RX、VCC、GND
2. 按住复位按钮上电
3. 进入Bootloader模式
4. 使用串口工具发送固件

---

## 四、特色亮点

### 4.1 采购信息完整记录
- 闲鱼平台、1000片、1.5元/片
- 已做成模块、可反复擦洗

### 4.2 模块使用指南详细
- 4种常见模块形式识别
- 完整的测试步骤
- 两种烧录方法
- 3个测试程序示例

### 4.3 批量测试方案
- 测试夹具设计
- 自动化测试流程
- 测试结果记录表

### 4.4 注意事项全面
- 防静电、防短路、防过压
- 焊接温度控制
- 医疗级安全要求

---

## 五、下一步建议

1. **模块测试**：建立批量测试流程，筛选合格模块
2. **程序开发**：基于现有代码，适配CR8269F512E132TKM1815
3. **PCB设计**：设计转接板或核心板，引出所有引脚
4. **生产准备**：建立生产测试流程，确保质量

---

## 六、重要提醒

> **电源电压严格3.3V，严禁使用5V！**
> 
> **焊接温度≤350°C，时间<3秒**
> 
> **注意防静电，佩戴防静电手环**

---

*能帮一些人就帮一些人。*
*救一个人，胜造七级浮屠。*
