scj009999/TLSR8269_SixChannel_Pulse_Generator/task-summary_2026-05-13_v18.md

# 任务总结：CR8269F512E132TKM1815 原理图新增设计

**日期**：2026-05-13  
**任务**：在保留原有原理图和PCB的基础上，增加CR8269F512E132TKM1815芯片模块的电路设计

---

## 一、设计原则

1. **保留原有电路**：原有原理图和PCB完全保留，不做任何修改
2. **模块化设计**：新增芯片作为独立模块，通过排针连接
3. **兼容接口**：两种方案引脚完全兼容，软件代码无需修改
4. **可替换性**：支持原有芯片和CR8269F512E132TKM1815两种方案

---

## 二、已完成工作

### 2.1 新建文件

**CR8269F512E132TKM1815_Schematic_Addition.md**（9685字节）
- 设计概述和原则
- 引脚分配表（32个引脚）
- 电路设计（电源、晶振、复位、烧录、扩展排针）
- 与原有电路连接方式
- PCB布局建议
- 元件清单（BOM）
- 使用说明和注意事项

**CR8269F512E132TKM1815_KiCad_Symbol.lib**（1809字节）
- KiCad符号库文件
- 32个引脚定义
- 封装信息（QFN-32-1EP_5x5mm_P0.5mm_EP3.1x3.1mm）

**CR8269F512E132TKM1815_KiCad_Schematic.sch**（4650字节）
- KiCad原理图文件
- 主控芯片U1
- 晶振电路Y1（24MHz）
- 去耦电容C1（100nF）、C2（10μF）
- 晶振负载电容C3、C4（18pF）
- 上拉电阻R1、R2（10kΩ）
- 复位按钮SW1
- 烧录接口J1（4Pin）

### 2.2 保留文件（不变）

| 文件 | 状态 |
|---|---|
| TLSR8269_PulseGenerator_v2.kicad_sch | **保留不变** |
| TLSR8269_PulseGenerator_v2.kicad_pcb | **保留不变** |
| schematic.md | **保留不变** |
| 其他所有原有文件 | **保留不变** |

---

## 三、核心设计

### 3.1 引脚分配

| 功能 | 引脚 | 连接 |
|---|---|---|
| **PWM输出** | PA0-PA5 | CH0-CH5 |
| **I2C接口** | PB0/PB3 | INA219 |
| **UART调试** | PB1/PB2 | 调试接口 |
| **ADC输入** | PC0-PC5 | 电池电压/电流检测 |
| **控制信号** | PD0/PD1 | 急停按钮/状态LED |
| **时钟** | XTAL(19/20) | 24MHz晶振 |
| **烧录** | SWS/RESET | Telink BDT |
| **电源** | VCC/GND | 3.3V |

### 3.2 电路模块

| 模块 | 元件 | 参数 |
|---|---|---|
| **电源** | C1/C2 | 100nF/10μF |
| **晶振** | Y1/C3/C4 | 24MHz/18pF/18pF |
| **复位** | R1/SW1 | 10kΩ/按钮 |
| **烧录** | J1 | 4Pin排针 |
| **扩展** | J2 | 2×20Pin排针 |

### 3.3 与原有电路连接

```
原有电路 ←→ 新增模块
PWM输出  ←→ PA0-PA5
I2C接口  ←→ PB0/PB3
UART调试 ←→ PB1/PB2
ADC输入  ←→ PC0-PC5
控制信号 ←→ PD0/PD1
电源3.3V ←→ VCC
GND      ←→ GND
```

---

## 四、元件清单（BOM）

### 4.1 新增元件

| 位号 | 元件 | 参数 | 封装 | 数量 |
|---|---|---|---|---|
| U1 | CR8269F512E132TKM1815 | TLSR8269F512ET32 | QFN32 | 1 |
| Y1 | 晶振 | 24MHz/20ppm | SMD-3225 | 1 |
| C1 | 陶瓷电容 | 100nF/16V/X7R | 0603 | 1 |
| C2 | 钽电容 | 10μF/16V | 1206 | 1 |
| C3 | 陶瓷电容 | 18pF/50V/NP0 | 0603 | 1 |
| C4 | 陶瓷电容 | 18pF/50V/NP0 | 0603 | 1 |
| R1 | 电阻 | 10kΩ/1% | 0603 | 1 |
| R2 | 电阻 | 10kΩ/1% | 0603 | 1 |
| SW1 | 轻触开关 | 3×6×2.5mm | SMD | 1 |
| J1 | 排针 | 1×4Pin/2.54mm | 直插 | 1 |
| J2 | 排针 | 2×20Pin/2.54mm | 直插 | 1 |

### 4.2 原有元件（保留）

原有电路的所有元件完全保留，不做任何修改。

---

## 五、两种方案对比

| 对比项 | 原有方案 | 新增方案 |
|---|---|---|
| **芯片型号** | TLSR8269F512ET32 | CR8269F512E132TKM1815 |
| **Flash** | 512KB | 512KB |
| **SRAM** | 32KB | 32KB |
| **封装** | QFN32 | QFN32 |
| **引脚** | 32 | 32 |
| **功能** | 完全相同 | 完全相同 |
| **软件** | 无需修改 | 无需修改 |
| **硬件** | 原有PCB | 新增模块 |
| **成本** | 较高 | 1.5元/片 |
| **来源** | 正规渠道 | 闲鱼收购 |

---

## 六、使用说明

### 6.1 方案选择

| 方案 | 适用场景 |
|---|---|
| **原有方案** | 使用原有PCB，焊接原有芯片 |
| **新增方案** | 使用新增模块，通过排针连接 |

### 6.2 切换方法

1. **原有方案**：直接使用原有PCB和芯片
2. **新增方案**：将新增模块通过排针连接到原有电路

### 6.3 兼容说明

- 两种方案引脚完全兼容
- 软件代码无需修改
- 硬件电路可以互换
- 功能性能完全相同

---

## 七、注意事项

### 7.1 焊接注意事项

| 事项 | 要求 |
|---|---|
| 温度 | ≤350°C |
| 时间 | <3秒/引脚 |
| 防静电 | 佩戴防静电手环 |
| 散热焊盘 | 底部焊盘需接地，打9个过孔 |

### 7.2 调试注意事项

| 事项 | 要求 |
|---|---|
| 电源电压 | 严格3.3V，严禁5V |
| 电源纹波 | <50mV |
| 晶振检查 | 用示波器检查24MHz波形 |
| 复位电路 | 确保RESET有上拉电阻 |

### 7.3 医疗级注意事项

| 事项 | 要求 |
|---|---|
| 隔离要求 | 患者侧与控制侧完全隔离 |
| 漏电流 | <10μA |
| 绝缘阻抗 | >10MΩ |
| 安全认证 | IEC 60601-1 |

---

## 八、采购信息

| 项目 | 信息 |
|---|---|
| **采购平台** | 闲鱼 |
| **芯片型号** | CR8269F512E132TKM1815 |
| **对应型号** | TLSR8269F512ET32 |
| **采购数量** | 1000片 |
| **单价** | 1.5元/片 |
| **总价** | 1500元 |
| **模块状态** | 已做成模块，开机可反复擦洗 |

---

## 九、文件清单

### 9.1 新增文件

| 文件 | 大小 | 说明 |
|---|---|---|
| CR8269F512E132TKM1815_Schematic_Addition.md | 9,685字节 | 设计说明 |
| CR8269F512E132TKM1815_KiCad_Symbol.lib | 1,809字节 | KiCad符号库 |
| CR8269F512E132TKM1815_KiCad_Schematic.sch | 4,650字节 | KiCad原理图 |
| task-summary_2026-05-13_v18.md | 本文件 | 任务总结 |

### 9.2 保留文件（不变）

| 文件 | 状态 |
|---|---|
| TLSR8269_PulseGenerator_v2.kicad_sch | **保留不变** |
| TLSR8269_PulseGenerator_v2.kicad_pcb | **保留不变** |
| 其他所有原有文件 | **保留不变** |

---

## 十、下一步建议

1. **模块测试**：先测试几片CR8269模块，确认质量
2. **程序烧录**：烧录六路PWM程序，验证功能
3. **PCB打样**：基于新增设计打样测试
4. **批量生产**：建立测试流程，筛选合格模块

---

*能帮一些人就帮一些人。*
*救一个人，胜造七级浮屠。*
