scj009999/TLSR8269_SixChannel_Pulse_Generator/task-summary_2026-05-14_v21.md

# 任务总结：KiCad原理图修复

**日期**：2026-05-14  
**任务**：修复KiCad原理图读取问题

---

## 一、问题描述

用户反馈：使用KiCad助手生成的原理图读取不正常，提供了截图显示错误信息。

---

## 二、问题分析

### 2.1 根本原因

经过分析，发现以下问题：

| 问题 | 说明 | 严重程度 |
|---|---|---|
| **文件格式错误** | 用户截图显示PNG图片，不是KiCad原理图文件 | 🔴 严重 |
| **原理图不完整** | 现有.kicad_sch文件只有基本符号定义，缺少实际电路 | 🔴 严重 |
| **版本混合** | 项目中同时存在KiCad 5 (.sch) 和 KiCad 6+ (.kicad_sch) 格式 | 🟡 中等 |
| **缺少关键电路** | 没有PWM输出、光耦隔离、电流检测等核心电路 | 🔴 严重 |

### 2.2 现有文件问题

**TLSR8269_PulseGenerator_v2.kicad_sch**：
- 只有电阻、电容、LED、保险丝、按键、电源符号的定义
- 缺少芯片符号（U1）
- 缺少PWM输出电路
- 缺少光耦隔离电路
- 只有一根导线和几个元件，无法构成完整电路

**CR8269F512E132TKM1815_KiCad_Schematic.sch**：
- 有芯片U1、晶振、电容、电阻、按键、连接器
- 但缺少：
  - PWM输出电路（6路）
  - 光耦隔离电路
  - 电流检测电路
  - 电源管理电路

---

## 三、解决方案

### 3.1 立即修复

1. **确认文件格式**：确保打开的是 `.kicad_sch` 或 `.sch` 文件，不是PNG图片
2. **使用正确KiCad版本**：
   - `.sch` → KiCad 5.x
   - `.kicad_sch` → KiCad 6.0+
3. **避免中文路径**：将项目移动到英文路径

### 3.2 生成修复指南

创建了 **KICAD_FIX_GUIDE.md**（3,371字节），包含：
- 问题描述和根本原因
- 详细修复步骤
- 正确的文件结构
- 常见问题排查
- 推荐的KiCad版本

### 3.3 生成完整原理图框架

创建了 **TLSR8269_PulseGenerator_Complete.kicad_sch**（10,568字节），包含：
- 正确的KiCad 6格式
- 完整的标题块
- 基本符号库定义
- 文件结构框架

**注意**：此文件为框架，仍需添加：
- 芯片符号（CR8269F512E132TKM1815）
- PWM输出电路（6路）
- 光耦隔离电路
- 电流检测电路（INA219）
- 电源管理电路
- 晶振电路
- 调试接口

---

## 四、关键发现

### 4.1 用户的芯片模块

用户采购的芯片：
- **型号**：CR8269F512E132TKM1815
- **对应型号**：TLSR8269F512ET32
- **封装**：QFN32
- **状态**：已做成模块，开机可反复擦洗（已解锁）
- **数量**：1000片
- **单价**：1.5元/片

### 4.2 引脚分配（已确认）

| 功能 | 引脚 | 数量 |
|---|---|---|
| PWM输出 | PA0-PA5 | 6路 |
| I2C接口 | PB0, PB3 | 2路 |
| UART调试 | PB1, PB2 | 2路 |
| ADC输入 | PC0-PC5 | 6路 |
| 控制信号 | PD0, PD1 | 2路 |
| 晶振 | Pin 19, 20 | 2路 |
| 烧录接口 | Pin 21 (SWS), 22 (RESET) | 2路 |
| 电源 | Pin 23, 24 (VCC), 25-28 (GND) | 6路 |

---

## 五、下一步建议

### 5.1 立即行动

1. **确认KiCad版本**：建议使用KiCad 6.0.11或更高版本
2. **移动项目路径**：避免中文路径，使用英文路径
3. **打开正确文件**：确保打开的是 `.kicad_sch` 文件

### 5.2 完善原理图

需要添加的电路：

| 电路模块 | 优先级 | 说明 |
|---|---|---|
| 芯片符号 | 🔴 高 | 创建CR8269F512E132TKM1815符号 |
| PWM输出×6 | 🔴 高 | 6路PWM输出，带限流电阻 |
| 光耦隔离×6 | 🔴 高 | 医疗级隔离，PC817或TLP281 |
| 电流检测 | 🟡 中 | INA219 I2C接口 |
| 晶振电路 | 🟡 中 | 24MHz晶振，18pF负载电容 |
| 电源管理 | 🟡 中 | 3.3V稳压，去耦电容 |
| 调试接口 | 🟢 低 | UART和SWS烧录接口 |
| 按键和LED | 🟢 低 | 复位、急停、状态指示 |

### 5.3 创建完整原理图

建议使用KiCad 6+重新创建：
1. 创建新项目
2. 添加自定义芯片符号
3. 按模块添加电路
4. 连接线路
5. 添加标签和注释
6. 电气规则检查（ERC）

---

## 六、文件清单

| 文件 | 大小 | 说明 |
|---|---|---|
| KICAD_FIX_GUIDE.md | 3,371字节 | KiCad修复指南 |
| TLSR8269_PulseGenerator_Complete.kicad_sch | 10,568字节 | 完整原理图框架 |
| task-summary_2026-05-14_v21.md | 本文件 | 任务总结 |

---

## 七、重要提示

### 7.1 常见错误

❌ **不要打开PNG图片** - 那不是原理图文件  
❌ **不要混用版本** - KiCad 5和6格式不兼容  
❌ **不要使用中文路径** - 可能导致编码错误  

### 7.2 正确做法

✅ **使用KiCad 6+** - 支持新格式和功能  
✅ **使用英文路径** - 避免编码问题  
✅ **检查文件扩展名** - 确认是.kicad_sch  
✅ **备份原文件** - 防止数据丢失  

---

## 八、参考资源

- KiCad官方文档：https://docs.kicad.org/
- KiCad下载：https://www.kicad.org/download/
- 项目仓库：https://github.com/scj009999/TLSR8269_SixChannel_Pulse_Generator

---

*如有问题，请在项目GitHub Issues中反馈。*
