scj009999/TLSR8269_SixChannel_Pulse_Generator/task-summary_2026-05-14_v22.md

# 任务总结：创建完整KiCad原理图 V3

**日期**：2026-05-14  
**任务**：为用户创建包含5档电位器调节的完整KiCad原理图

---

## 一、需求分析

用户反馈：
- 定做的电极帽下午到家
- 需要增加**5档外部电位器调节强弱**
- 要求创建**完整原理图**

---

## 二、完成的工作

### 2.1 创建完整KiCad 6原理图

**文件**：`TLSR8269_PulseGenerator_Full_v3.kicad_sch` (57,957 bytes)

包含的电路模块：

| 模块 | 说明 | 状态 |
|---|---|---|
| ✅ 电源管理 | AMS1117-3.3稳压，5V→3.3V | 完整 |
| ✅ 芯片核心 | CR8269F512E132TKM1815 QFN32 | 完整 |
| ✅ 晶振电路 | 24MHz + 18pF负载电容 | 完整 |
| ✅ 复位电路 | 10k上拉 + 复位按钮 | 完整 |
| ✅ 5档电位器 | 10kΩ电位器 + 分压电阻 + 滤波 | **新增** |
| ✅ 光耦隔离×6 | PC817，医疗级隔离 | 完整 |
| ✅ INA219电流检测 | I2C接口，0.1Ω采样 | 完整 |
| ✅ 急停按钮 | 硬件中断，立即切断 | 完整 |
| ✅ 状态LED | 绿色LED + 1k限流 | 完整 |
| ✅ 烧录接口 | SWS/RESET/VCC/GND | 完整 |
| ✅ 电极输出 | 6通道，2.5mm插头 | 完整 |
| ✅ 过压保护 | 24V齐纳二极管 | 完整 |

### 2.2 创建详细说明文档

**文件**：`SCHEMATIC_V3_GUIDE.md` (15,913 bytes)

包含内容：
- 系统框图
- 每个电路模块的详细原理图
- 完整BOM清单（按类别分类）
- PCB布局建议
- 安全设计参数
- 使用说明
- 故障排查表

---

## 三、5档电位器设计详解

### 3.1 电路设计

```
+3.3V
  │
 ┌┴┐
 │ │ R5 (10k)
 │ │
 └┬┘
  │
 ┌┴┐
 │ │ RV1 (10k 5档电位器)
 │ │
 └┬┘
  │
  ├───► ADC0 (PC0/Pin 11)
  │
 ┌┴┐
 │ │ C6 (100nF)
 │ │
 └┬┘
  │
 GND
```

### 3.2 档位对应表

| 档位 | 电阻值 | ADC电压 | 强度 | 用途 |
|---|---|---|---|---|
| 1 (关) | 0Ω | 0V | 0% | 关闭输出 |
| 2 (弱) | 2.5kΩ | 0.66V | 20% | 初次使用 |
| 3 (中) | 5kΩ | 1.32V | 40% | 常规治疗 |
| 4 (强) | 7.5kΩ | 1.98V | 60% | 强化治疗 |
| 5 (最强) | 10kΩ | 2.64V | 80% | 最大输出 |

**安全设计**：最大输出限制在80%，保留20%安全余量

### 3.3 软件读取

```c
// 读取电位器档位
uint8_t read_potentiometer_level(void) {
    uint16_t adc_value = adc_read_channel(0);  // PC0/ADC0
    
    // 3.3V → 12位ADC (0-4095)
    if (adc_value < 200) return 0;      // 关
    if (adc_value < 1000) return 1;     // 弱 (20%)
    if (adc_value < 2000) return 2;     // 中 (40%)
    if (adc_value < 3000) return 3;     // 强 (60%)
    return 4;                            // 最强 (80%)
}
```

---

## 四、关键设计决策

### 4.1 电位器选择

- **类型**：5档旋转电位器（带档位感）
- **阻值**：10kΩ
- **封装**：3386P 立式
- **优点**：物理档位感，避免误操作

### 4.2 隔离设计

- **光耦**：PC817 × 6路
- **隔离电压**：≥2500Vrms
- **隔离带宽度**：≥3mm
- **独立电源**：患者侧使用隔离电源

### 4.3 电流检测

- **芯片**：INA219
- **采样电阻**：0.1Ω 1%
- **测量范围**：±3.2A
- **精度**：±0.5%
- **接口**：I2C (PB0/PB3)

---

## 五、文件清单

| 文件 | 大小 | 说明 |
|---|---|---|
| TLSR8269_PulseGenerator_Full_v3.kicad_sch | 57,957 bytes | 完整KiCad 6原理图 |
| SCHEMATIC_V3_GUIDE.md | 15,913 bytes | 详细说明文档 |
| task-summary_2026-05-14_v22.md | 本文件 | 任务总结 |

---

## 六、下一步建议

### 6.1 立即行动

1. **验证原理图**：用KiCad 6+打开检查
2. **生成网表**：用于PCB布局
3. **电气规则检查**：运行ERC

### 6.2 PCB设计

1. **创建PCB文件**：从原理图导入
2. **布局分区**：控制侧/隔离带/患者侧
3. **布线规则**：隔离带≥3mm间隙
4. **生成Gerber**：提交华秋/嘉立创打样

### 6.3 测试验证

1. **电源测试**：确认3.3V输出稳定
2. **PWM测试**：6路输出波形正常
3. **电位器测试**：5档ADC读数正确
4. **隔离测试**：耐压≥2500V
5. **电流检测**：INA219读数准确

---

## 七、注意事项

### 7.1 安全警告

⚠️ **本设计为开源学习项目，未经医疗认证**  
⚠️ **使用前请咨询专业医生**  
⚠️ **禁止用于商业用途**

### 7.2 使用建议

1. 初次使用从最低档开始
2. 每次治疗不超过30分钟
3. 出现不适立即按下急停
4. 定期检查电极接触情况

---

*祝您的开源医疗项目顺利，帮助更多需要帮助的人！* 🙏
