scj009999/TLSR8269_SixChannel_Pulse_Generator/task-summary_2026-05-14_v23.md

# 任务总结：生成PCB布局

**日期**：2026-05-14  
**任务**：生成完整的PCB布局文件

---

## 一、需求分析

用户请求：
- 生成PCB布局
- 基于V3原理图
- 包含5档电位器调节
- 医疗级隔离设计

---

## 二、完成的工作

### 2.1 创建KiCad 6 PCB文件

**文件**：`TLSR8269_PulseGenerator_v3.kicad_pcb` (40,984 bytes)

包含内容：

| 项目 | 说明 |
|---|---|
| **板尺寸** | 100mm × 80mm |
| **层数** | 2层 (F.Cu + B.Cu) |
| **区域划分** | 控制侧 / 隔离带 / 患者侧 |
| **元件放置** | 52个元件 |
| **网络** | 45个网络 |
| **铺铜** | 4个区域 (GND + ISO_GND) |
| **安装孔** | 4个 (2.2mm) |

### 2.2 创建PCB布局指南

**文件**：`PCB_LAYOUT_GUIDE.md` (8,605 bytes)

包含内容：
- PCB概览和尺寸
- 元件布局详解
- 关键布局要点
- 布线规则
- 层叠结构
- 铺铜设计
- DRC检查清单
- 制造文件输出

---

## 三、PCB布局关键设计

### 3.1 区域划分

```
┌────────────────────────────────────────┐
│   控制侧 (Control Side)                │
│   Y: 40mm - 82mm                       │
│   - U1 (主控芯片)                      │
│   - U2 (稳压器)                        │
│   - U3 (电流检测)                      │
│   - RV1 (电位器)                       │
│   - 晶振、电容、电阻                    │
├────────────────────────────────────────┤
│   隔离带 (Isolation Barrier)           │
│   Y: 82mm - 88mm (6mm宽)               │
│   - 无铜、无走线、开槽                  │
│   - 爬电距离 ≥ 3mm                     │
├────────────────────────────────────────┤
│   患者侧 (Patient Side)                │
│   Y: 88mm - 120mm                      │
│   - U4-U9 (光耦隔离 ×6)                │
│   - J3 (电极输出)                      │
│   - J4 (隔离电源)                      │
└────────────────────────────────────────┘
```

### 3.2 关键布局要点

#### 晶振布局
- 距离芯片 < 20mm
- 负载电容紧靠晶振
- 下方禁止走其他信号线

#### 电源去耦
- C7/C8距离VCC引脚 < 5mm
- 过孔直接连接到GND层

#### 光耦跨接
- 本体跨接隔离带
- Pin1-2在控制侧
- Pin3-4在患者侧
- 隔离距离 ≥ 3mm

#### 电位器位置
- 板左侧边缘，易于操作
- 滤波电容紧靠抽头
- 远离高频信号

---

## 四、布线规则

### 4.1 线宽规则

| 网络类型 | 线宽 |
|---|---|
| 电源线 | 0.5mm |
| 信号线 | 0.25mm |
| 模拟信号 | 0.25mm |

### 4.2 间距规则

| 项目 | 间距 |
|---|---|
| 普通走线 | 0.2mm |
| 隔离带 | 3.0mm |
| 高压到低压 | 3.0mm |

---

## 五、铺铜设计

### 5.1 顶层铺铜 (F.Cu)

```
控制侧 (Y: 40-82mm)  → GND
隔离带 (Y: 82-88mm)  → 无铜
患者侧 (Y: 88-120mm) → ISO_GND
```

### 5.2 底层铺铜 (B.Cu)

```
控制侧 (Y: 40-82mm)  → GND
隔离带 (Y: 82-88mm)  → 无铜
患者侧 (Y: 88-120mm) → ISO_GND
```

**重要**：两个GND网络完全分离，通过光耦隔离

---

## 六、元件位置汇总

### 6.1 控制侧主要元件

| 位号 | 元件 | 位置 (X, Y) |
|---|---|---|
| U1 | CR8269F512E132TKM1815 | (100, 65) |
| U2 | AMS1117-3.3 | (70, 55) |
| U3 | INA219 | (85, 55) |
| Y1 | 24MHz晶振 | (115, 60) |
| RV1 | 10kΩ电位器 | (60, 70) |
| J1 | 电源输入 | (55, 50) |
| J2 | 烧录接口 | (140, 50) |
| SW1 | 复位按钮 | (125, 70) |
| SW2 | 急停按钮 | (125, 80) |
| D1 | 状态LED | (135, 75) |

### 6.2 患者侧主要元件

| 位号 | 元件 | 位置 (X, Y) |
|---|---|---|
| U4 | PC817 (CH0) | (75, 95) |
| U5 | PC817 (CH1) | (90, 95) |
| U6 | PC817 (CH2) | (105, 95) |
| U7 | PC817 (CH3) | (120, 95) |
| U8 | PC817 (CH4) | (135, 95) |
| U9 | PC817 (CH5) | (75, 110) |
| J3 | 电极输出 | (140, 110) |
| J4 | 隔离电源 | (55, 110) |
| D2 | 24V齐纳管 | (130, 100) |

---

## 七、安全设计验证

### 7.1 隔离要求

| 项目 | 设计值 | 标准 | 状态 |
|---|---|---|---|
| 隔离带宽度 | 6mm | ≥ 3mm | ✅ |
| 爬电距离 | ≥ 3mm | ≥ 3mm | ✅ |
| 电气间隙 | ≥ 3mm | ≥ 3mm | ✅ |
| 隔离电压 | 2500Vrms | IEC 60601-1 | ✅ |

### 7.2 安全距离

- 光耦两侧网络分离
- 隔离带无铜、无走线
- 患者侧独立接地

---

## 八、下一步建议

### 8.1 立即行动

1. **DRC检查**：运行KiCad DRC验证
2. **3D预览**：检查元件干涉
3. **生成Gerber**：输出制造文件

### 8.2 提交打样

```bash
# 华秋/嘉立创打样参数
板尺寸：100mm × 80mm
板厚：1.6mm
层数：2层
铜厚：1oz (35μm)
阻焊：绿色
丝印：白色
表面处理：HASL无铅喷锡
数量：5片
```

### 8.3 测试验证

1. 电源电压测试 (+3.3V)
2. 晶振起振测试 (24MHz)
3. PWM输出测试 (6路)
4. 电位器ADC测试 (5档)
5. 光耦隔离测试 (2500V)
6. 电流检测测试 (INA219)

---

## 九、文件清单

| 文件 | 大小 | 说明 |
|---|---|---|
| TLSR8269_PulseGenerator_v3.kicad_pcb | 40,984 bytes | PCB布局文件 |
| PCB_LAYOUT_GUIDE.md | 8,605 bytes | 布局指南文档 |
| task-summary_2026-05-14_v23.md | 本文件 | 任务总结 |

---

## 十、注意事项

### 10.1 安全警告

⚠️ **本设计为开源学习项目，未经医疗认证**  
⚠️ **使用前请咨询专业医生**  
⚠️ **禁止用于商业用途**

### 10.2 制造建议

1. 选择有资质的PCB厂
2. 要求检测隔离距离
3. 进行电气安全测试
4. 保留测试记录

---

*祝您的开源医疗项目顺利，帮助更多需要帮助的人！* 🙏
