scj009999/TLSR8269_SixChannel_Pulse_Generator/task-summary_2026-05-23_v26.md

# 任务总结：创建系统自检模块和寄存器定义

**日期**：2026-05-23  
**任务**：基于用户提供的官方C库，创建医疗级系统自检模块和TLSR8269寄存器定义

---

## 一、完成的工作

### 1.1 创建寄存器定义头文件

**文件**：`firmware/tlsr8269_reg.h` (10,494 bytes)

**包含内容**：
- 时钟控制寄存器（PLL、32K时钟）
- GPIO寄存器（PA/PB/PC端口，共24个GPIO）
- PWM寄存器（6通道）
- ADC寄存器（6通道+电池+温度）
- UART/SPI/I2C寄存器
- 中断寄存器（Timer/UART/SPI/I2C/ADC/PWM/GPIO/BLE）
- 电源管理寄存器
- Flash寄存器
- 看门狗寄存器
- 引脚复用功能定义
- 常用宏定义（GPIO操作、PWM使能等）

**关键宏定义**：
```c
// GPIO操作宏
GPIO_SET_OUTPUT(port, pin)   // 设置输出
GPIO_SET_INPUT(port, pin)    // 设置输入
GPIO_WRITE(port, pin, val)   // 写输出
GPIO_READ(port, pin)         // 读输入

// PWM使能
PWM_ENABLE_PIN(port, pin)

// ADC使能
ADC_ENABLE_PIN(pin)
```

### 1.2 创建系统自检模块

**文件**：
- `firmware/self_check.h` (2,368 bytes) — 头文件
- `firmware/self_check.c` (14,048 bytes) — 实现文件

**自检项目**（8项医疗级检测）：

| 序号 | 检测项目 | 函数 | 说明 |
|---|---|---|---|
| 1 | 时钟检测 | `check_system_clock()` | 32M PLL + 32K休眠时钟 |
| 2 | Flash检测 | `check_flash_memory()` | 读写测试 + CRC校验 |
| 3 | RAM检测 | `check_ram_memory()` | Walking bit + 地址线测试 |
| 4 | 电源检测 | `check_power_supply()` | 电池 + 3.3V稳压 |
| 5 | ADC检测 | `check_adc_circuit()` | 阻抗检测电路 |
| 6 | PWM检测 | `check_pwm_output()` | 六通道输出测试 |
| 7 | 急停检测 | `check_estop_button()` | 按钮状态 |
| 8 | BLE检测 | `check_ble_module()` | 蓝牙模块 |

**错误码定义**：
```c
CHECK_OK            0x00  // 正常
CHECK_FAIL_CLK      0x01  // 时钟异常
CHECK_FAIL_FLASH    0x02  // 存储异常
CHECK_FAIL_RAM      0x03  // 内存异常
CHECK_FAIL_BLE      0x04  // 蓝牙异常
CHECK_FAIL_ADC      0x05  // ADC异常
CHECK_FAIL_PARAM    0x06  // 参数损坏
CHECK_FAIL_POWER    0x07  // 电源异常
CHECK_FAIL_PWM      0x08  // PWM异常
CHECK_FAIL_ESTOP    0x09  // 急停异常
```

**关键特性**：
- 开机全链路检测
- 异常立即锁机
- LED闪烁报警
- UART输出错误信息
- 仅全部通过才允许操作

### 1.3 创建固件目录README

**文件**：`firmware/README.md` (2,789 bytes)

**包含内容**：
- 目录结构说明
- 文件功能说明
- 使用示例
- 编译说明
- 开发计划
- 安全说明

---

## 二、代码结构

### 2.1 自检模块流程

```
开机 → system_self_check()
  ├── [1/8] 检查系统时钟
  ├── [2/8] 检查Flash存储
  ├── [3/8] 检查RAM
  ├── [4/8] 检查电源
  ├── [5/8] 检查ADC
  ├── [6/8] 检查PWM
  ├── [7/8] 检查急停按钮
  ├── [8/8] 检查BLE
  └── 结果判断
      ├── 全部通过 → g_system_ready = true
      └── 任何失败 → handle_system_error() → 锁机死循环
```

### 2.2 错误处理

```c
void handle_system_error(uint8_t error_code) {
    // 1. 关闭所有PWM输出
    // 2. 关闭电源
    // 3. 闪烁LED报警
    // 4. 循环输出错误信息
    while(1) {
        led_blink();
        uart_send_error();
    }
}
```

---

## 三、与硬件的对应关系

### 3.1 引脚使用

| 功能 | 芯片引脚 | Arduino | 寄存器 |
|---|---|---|---|
| CH0 | PA0 | D0 | reg_pa_out BIT(0) |
| CH1 | PA1 | D1 | reg_pa_out BIT(1) |
| CH2 | PA2 | D2 | reg_pa_out BIT(2) |
| CH3 | PA3 | D3 | reg_pa_out BIT(3) |
| CH4 | PB0 | D8 | reg_pb_out BIT(0) |
| CH5 | PB1 | D9 | reg_pb_out BIT(1) |
| 电位器 | PB2 | A2 | ADC_CHANNEL_2 |
| 急停 | PC2 | D18 | reg_pc_in BIT(2) |
| LED | PC7 | D23 | reg_pc_out BIT(7) |
| I2C SDA | PB6 | D14 | reg_pb_out BIT(6) |
| I2C SCL | PB7 | D15 | reg_pb_out BIT(7) |
| UART RX | PC0 | D16 | reg_uart_data |
| UART TX | PC1 | D17 | reg_uart_data |

### 3.2 外设对应

| 外设 | 芯片引脚 | 说明 |
|---|---|---|
| INA219 | PB6/PB7 | I2C接口 |
| 光耦U4-U9 | PA0-PA3, PB0-PB1 | PWM输出 |
| 电位器 | PB2 | ADC输入 |
| 急停按钮 | PC2 | GPIO输入 |
| 状态LED | PC7 | GPIO输出 |

---

## 四、开发计划更新

### 已完成 ✅

- [x] 寄存器定义头文件 (`tlsr8269_reg.h`)
- [x] 系统自检模块 (`self_check.h/c`)
- [x] 固件目录README

### 待完成 ⏳

- [ ] PWM驱动模块 (`pwm_driver.c`)
- [ ] ADC驱动模块 (`adc_driver.c`)
- [ ] UART驱动模块 (`uart_driver.c`)
- [ ] I2C驱动模块 (`i2c_driver.c`)
- [ ] BLE服务模块 (`ble_service.c`)
- [ ] 主程序框架 (`main.c`)
- [ ] 编译脚本 (`Makefile`)

---

## 五、安全特性

### 5.1 医疗级保护

1. **开机自检**：8项检测，全部通过才能操作
2. **异常锁机**：任何故障立即关闭所有输出
3. **硬件急停**：独立于软件的硬件级保护
4. **电流限制**：软件2mA限制 + 硬件保险丝
5. **阻抗检测**：实时监测，异常自动切断
6. **看门狗**：程序跑飞自动复位

### 5.2 错误处理

- 错误码精确定位故障模块
- UART输出详细错误信息
- LED闪烁模式区分错误类型
- 死循环防止继续操作

---

## 六、参考文档

| 文档 | 说明 |
|---|---|
| `hardware/TLSR8251_Arduino_Pinout.md` | Arduino引脚映射 |
| `hardware/PINOUT_CORRECTION.md` | 引脚修正说明 |
| `docs/MEDICAL_SAFETY.md` | 医疗安全规范 |
| `firmware/README.md` | 固件开发指南 |

---

## 七、下一步建议

### 7.1 立即行动

1. **验证寄存器定义**：对照官方Datasheet检查
2. **完善自检模块**：添加实际硬件检测代码
3. **创建驱动模块**：PWM、ADC、UART、I2C

### 7.2 测试验证

1. 编译测试
2. 模拟器测试
3. 硬件调试

---

*固件开发进行中，持续更新...*
