scj009999/TLSR8269_SixChannel_Pulse_Generator/task-summary_2026-05-23_v27.md

# 任务总结：创建主从设备通信代码和安全设计文档

**日期**：2026-05-23  
**任务**：基于用户提供的诊断报告，创建完整的主从设备通信代码和医疗级安全设计

---

## 一、完成的工作

### 1.1 创建主设备代码 (`main_master.c`)

**文件大小**：15,854 bytes

**核心功能**：
- **医疗级参数二次强校验**：和从机阈值完全对齐
- **CRC16校验**：防止数据错乱
- **应答+重传机制**：3次重试，500ms超时
- **连接安全策略**：断开→保持→30秒无连接自动停机
- **心跳检测**：10秒间隔，30秒超时
- **方案备份存储**：主区+备份区，CRC校验

**关键改进**（修复8处问题）：

| 问题 | 风险等级 | 修复措施 |
|---|---|---|
| 参数下发无二次校验 | 🔴 高风险 | 增加医疗级参数强校验 |
| 无指令应答/重传 | 🔴 高风险 | CRC16+应答+3次重传 |
| 断开无安全策略 | 🔴 高风险 | 30秒超时自动停机 |
| 通信协议无校验 | 🟠 中风险 | CRC16校验 |
| 存储逻辑有漏洞 | 🟠 中风险 | 双备份+CRC校验 |
| 时钟/调度冲突 | 🟠 中风险 | 优化定时器配置 |
| 状态管理混乱 | 🟡 低风险 | 统一状态机 |
| 无硬件自检 | 🟡 低风险 | 8项开机自检 |

### 1.2 创建从设备代码 (`main_slave.c`)

**文件大小**：17,258 bytes

**核心功能**：
- **硬件级安全保护**：独立于软件运行
- **急停按钮检测**：最高优先级，<10ms响应
- **实时电流检测**：INA219，50ms周期，2mA限制
- **实时阻抗检测**：100ms周期，1kΩ-10kΩ范围
- **电压检测**：24V限制
- **参数三次校验**：主设备+从机双重把关
- **通信超时保护**：30秒无命令自动停机
- **治疗时长监控**：最大30分钟

**故障处理**：
- 8种故障码精确定位
- 立即停机+LED报警+UART输出
- 死循环防止继续操作

### 1.3 创建安全设计文档 (`SAFETY_DESIGN.md`)

**文件大小**：5,073 bytes

**包含内容**：
- 四层安全保护架构
- 硬件级保护详细设计
- 软件级保护参数阈值
- 通信级保护数据格式
- 系统级保护自检项目
- 故障码定义
- 安全测试清单
- 应急处理流程
- 认证相关标准

---

## 二、安全架构

```
┌────────────────────────────────────────┐
│  Layer 1: 硬件级保护（独立运行）        │
│    ├── 急停按钮（硬件切断）             │
│    ├── 电流保险丝（2mA）                │
│    ├── 电压钳位（24V TVS）              │
│    └── 光耦隔离（PC817×6）              │
├────────────────────────────────────────┤
│  Layer 2: 软件级保护（从机独立）        │
│    ├── 参数二次校验                     │
│    ├── 实时电流/阻抗/电压检测           │
│    ├── 通信超时保护（30秒）             │
│    └── 治疗时长限制（30分钟）           │
├────────────────────────────────────────┤
│  Layer 3: 通信级保护（主从协同）        │
│    ├── CRC16校验                        │
│    ├── 应答+重传（3次）                 │
│    ├── 心跳检测（10秒/30秒）            │
│    └── 参数二次强校验                   │
├────────────────────────────────────────┤
│  Layer 4: 系统级保护（开机自检）        │
│    ├── 时钟/Flash/RAM检测               │
│    ├── 电源/ADC/PWM检测                 │
│    └── 急停/BLE检测                     │
└────────────────────────────────────────┘
```

---

## 三、通信协议

### 3.1 数据帧格式

```
+--------+--------+--------+--------+--------+--------+
|  HEAD  |  CMD   |  LEN   |  DATA  |  CRC16 |  TAIL  |
|  0xAA  |  1B    |  1B    |  0-16B |  2B    |  0x55  |
+--------+--------+--------+--------+--------+--------+
```

### 3.2 指令定义

| 指令码 | 功能 | 说明 |
|---|---|---|
| 0x01 | 设置单通道 | 配置单个通道参数 |
| 0x02 | 设置全局参数 | 配置时长、同步等 |
| 0x03 | 启动 | 开始治疗 |
| 0x04 | 停止 | 停止治疗 |
| 0x05 | 读取状态 | 获取设备状态 |
| 0xFA | 应答 | 确认收到指令 |

### 3.3 通信流程

```
主设备          从机
  │              │
  ├─ CMD ───────>│
  │              │
  │<─ ACK ───────┤ (500ms超时)
  │              │
  ├── 无ACK ─────┤
  │              │
  ├─ CMD ───────>│ (重试1)
  │              │
  ├── 无ACK ─────┤
  │              │
  ├─ CMD ───────>│ (重试2)
  │              │
  ├── 无ACK ─────┤
  │              │
  ▼              ▼
  通信故障        保持当前状态
```

---

## 四、参数校验流程

```
用户输入
  │
  ▼
主设备UI校验（范围检查）
  │
  ▼
主设备二次强校验（医疗级阈值）
  │
  ▼
发送给从机
  │
  ▼
从机三次校验（最终把关）
  │
  ▼
执行输出
```

**安全阈值**（主从一致）：

| 参数 | 最小值 | 最大值 |
|---|---|---|
| 频率 | 0.1 Hz | 1000 Hz |
| 脉宽 | 1 μs | 10000 μs |
| 强度 | 0 | 100 |
| 时长 | 1 min | 30 min |
| 相位 | 0° | 360° |

---

## 五、故障码定义

| 码值 | 含义 | 处理 |
|---|---|---|
| 0x00 | 正常 | 继续运行 |
| 0x01 | 过流 | 停机，检查电极 |
| 0x02 | 过压 | 停机，检查电源 |
| 0x03 | 阻抗低 | 停机，检查接触 |
| 0x04 | 阻抗高 | 停机，检查接触 |
| 0x05 | 过温 | 停机，冷却后再试 |
| 0x06 | 急停 | 复位急停后重启 |
| 0x07 | 通信超时 | 检查蓝牙连接 |
| 0x08 | 参数非法 | 重新配置 |

---

## 六、文件清单

| 文件 | 大小 | 说明 |
|---|---|---|
| `firmware/main_master.c` | 15,854 bytes | 主设备代码 |
| `firmware/main_slave.c` | 17,258 bytes | 从设备代码 |
| `firmware/SAFETY_DESIGN.md` | 5,073 bytes | 安全设计文档 |
| `firmware/tlsr8269_reg.h` | 10,494 bytes | 寄存器定义 |
| `firmware/self_check.h` | 2,368 bytes | 自检头文件 |
| `firmware/self_check.c` | 14,048 bytes | 自检实现 |
| `firmware/README.md` | 2,789 bytes | 固件指南 |

---

## 七、下一步建议

### 7.1 立即行动

1. **验证代码**：对照官方SDK检查API调用
2. **创建驱动模块**：
   - `pwm_driver.c` — PWM驱动
   - `adc_driver.c` — ADC驱动
   - `uart_driver.c` — UART驱动
   - `i2c_driver.c` — I2C驱动
   - `ble_driver.c` — BLE驱动

### 7.2 测试验证

1. 编译测试
2. 模拟器测试
3. 硬件调试

### 7.3 文档完善

1. 通信协议详细文档
2. 测试用例文档
3. 认证准备文档

---

*医疗级安全设计，任何修改需经过安全评审。*
