scj009999/TLSR8269_SixChannel_Pulse_Generator/task-summary_2026-05-09_v4.md

# 任务总结：TLSR8269 开源经颅脉冲治疗仪 v4

## 更新内容（2026-05-09 早上）

### 1. 医生招募文案
- 创建 `docs/DOCTOR_RECRUITMENT.md`
- 添加到 README.md 显眼位置
- 包含：招募对象、参与方式、获得回报、申请流程

### 2. 药监局邮件草稿
- 创建 `docs/NMPA_EMAIL_DRAFT.md`
- 可直接复制使用的邮件模板
- 包含发送建议和附件清单

### 3. 手机APP设计文档
- 创建 `docs/MOBILE_APP_DESIGN.md`
- 完整医患交互系统方案
- 含UI原型、技术架构、开发计划

## 待办清单（按优先级）

### 第一步：发邮件给药监局（今天）
- [ ] 复制邮件草稿
- [ ] 填写个人信息
- [ ] 附件转为PDF
- [ ] 发送邮件
- [ ] 记录发送时间，准备跟进

### 第二步：完善GitHub仓库（今天）
- [ ] 上传所有新文件
- [ ] 更新 README.md
- [ ] 创建 Release v1.0

### 第三步：医生招募（本周）
- [ ] 在医学论坛发布招募信息
- [ ] 联系帕金森病友群，寻找推荐
- [ ] 准备面试问题清单

### 第四步：PCB制作（本周）
- [ ] 用嘉立创账号下单
- [ ] 准备BOM清单
- [ ] 等待打样

### 第五步：APP开发（本月）
- [ ] 确定技术栈（Flutter）
- [ ] 寻找志愿者开发者
- [ ] 制作UI原型

## 项目文件清单

```
TLSR8269_SixChannel_Pulse_Generator/
├── README.md                    # 已更新，含医生招募
├── LICENSE                      # 双重许可证
├── main.c                       # 核心代码
├── app_config.h                 # 芯片配置
├── Makefile                     # 编译脚本
├── hardware/
│   └── schematic.md             # 原理图和BOM
├── docs/
│   ├── MEDICAL_SAFETY.md        # 医疗安全规范
│   ├── TARGETING_SYSTEM.md      # 靶点定位系统
│   ├── OPEN_SOURCE_LETTER.md    # 致药监局信
│   ├── COST_ANALYSIS.md         # 成本分析
│   ├── DOCTOR_RECRUITMENT.md    # ⭐ 医生招募
│   ├── NMPA_EMAIL_DRAFT.md      # ⭐ 邮件草稿
│   └── MOBILE_APP_DESIGN.md     # ⭐ APP设计
├── examples/
│   └── uart_control.c           # 串口控制示例
└── PulseTherapy/                # Arduino库
    ├── PulseTherapy.h
    ├── PulseTherapy.cpp
    ├── keywords.txt
    └── examples/
        └── ParkinsonTherapy/
            └── ParkinsonTherapy.ino
```

## 下一步行动

用户确认后，继续：
1. 写正式邮件（替换个人信息）
2. 制作APP原型图
3. 准备医生面试问题

**每一个行动，都是向希望迈进的一步。**
