scj009999/TLSR8269_SixChannel_Pulse_Generator/task-summary_2026-05-09_v5.md

# 任务总结：TLSR8269 开源经颅脉冲治疗仪 v5

## 更新内容（2026-05-09 早上7点）

### 1. 搜索收集关键证据
通过联网搜索获取到以下核心证据：

#### 刘河生教授研究（核心证据）
- **发表期刊**：《自然》(Nature) 2026年2月5日
- **核心发现**：世界首次揭示帕金森病"躯体认知环路"
- **临床效果**：有效率55.5%（传统方法22.2%）
- **产业化**：已获批3项医疗器械注册证
- **应用规模**：60+医院，3000+病例，有效率70%
- **媒体报道**：新华社、央视等央媒报道

#### 安全性证据
- **tACS研究**（福建医科大学，Cell子刊）：安全可行，无不良事件
- **tDCS研究**（Nature Medicine）：0.5-2mA，安全性耐受性良好
- **DBS参考**：微创手术，并发症<1%

### 2. 更新邮件草稿
- 在NMPA_EMAIL_DRAFT.md中补充了刘河生教授研究的具体数据
- 增加了证据附件清单

### 3. 创建证据收集文档
- `docs/EVIDENCE_COLLECTION.md` - 完整的证据汇总
- 包含有效性、安全性、经济性三方面证据
- 可直接作为邮件附件

## 待办清单（更新）

### 今天必须完成：
1. ✅ 搜索收集证据
2. ✅ 更新邮件草稿
3. ⏳ 发送邮件给药监局（用户操作）
   - 复制邮件内容
   - 添加附件（PDF）
   - 用QQ邮箱发送

### 等待药监局回复期间：
4. ⏳ 上传GitHub仓库
5. ⏳ 医生招募（发布到医学论坛）
6. ⏳ PCB制作（嘉立创下单）
7. ⏳ APP设计细化

## 关键文件清单

```
docs/
├── NMPA_EMAIL_DRAFT.md       # 邮件草稿（已更新证据）
├── EVIDENCE_COLLECTION.md    # ⭐ 证据收集汇总
├── OPEN_SOURCE_LETTER.md     # 致药监局信
├── DOCTOR_RECRUITMENT.md     # 医生招募
├── MOBILE_APP_DESIGN.md      # APP设计
├── MEDICAL_SAFETY.md         # 安全规范
├── COST_ANALYSIS.md          # 成本分析
└── TARGETING_SYSTEM.md       # 靶点定位
```

## 下一步行动

用户现在需要：
1. 打开QQ邮箱
2. 新建邮件
3. 复制NMPA_EMAIL_DRAFT.md内容
4. 添加附件（将相关md文件转为PDF）
5. 发送！

**邮件发送后，记录时间，1周后跟进。**

---

*每一个行动，都是向希望迈进的一步。*
