scj009999/TLSR8269_SixChannel_Pulse_Generator/task-summary_2026-05-09_v6.md

# 任务总结：TLSR8269 开源经颅脉冲治疗仪 v6

## 更新内容（2026-05-09 早上7:20）

### 1. 强调公益性质和免责声明

#### 更新 README.md
- 添加"重要声明"章节，明确：
  - 本项目为纯公益项目，不收取任何费用
  - 禁止商业用途
  - 禁止向患者收费
  - 医生参与纯属自愿，以志愿者形式
  - 本项目不是医疗机构，不提供医疗服务

#### 更新 LICENSE
- 添加"NON-COMMERCIAL & VOLUNTEER TERMS"章节：
  - 第6条：非商业使用条款
  - 第7条：志愿者参与条款
  - 第8条：不提供医疗服务声明

#### 更新 DOCTOR_RECRUITMENT.md
- 顶部添加重要声明
- 添加项目性质说明
- 修改"实际收益"部分，删除"顾问费"，强调无报酬

#### 新建 DISCLAIMER.md
- 完整的免责声明文档
- 包含项目性质、医疗免责、医生参与、知识产权、隐私数据等9个章节
- 用户必须阅读并同意

### 2. 更新项目结构
README.md中的项目结构已更新，包含所有新文件：
- DISCLAIMER.md
- EVIDENCE_COLLECTION.md
- NMPA_EMAIL_DRAFT.md
- DOCTOR_RECRUITMENT.md
- MOBILE_APP_DESIGN.md

## 关键文件清单（更新）

```
TLSR8269_SixChannel_Pulse_Generator/
├── README.md                 # 已更新（含公益声明）
├── LICENSE                   # 已更新（含非商业条款）
├── DISCLAIMER.md             # ⭐ 新建（完整免责声明）
├── main.c
├── app_config.h
├── Makefile
├── hardware/
│   └── schematic.md
├── docs/
│   ├── MEDICAL_SAFETY.md
│   ├── TARGETING_SYSTEM.md
│   ├── OPEN_SOURCE_LETTER.md
│   ├── COST_ANALYSIS.md
│   ├── EVIDENCE_COLLECTION.md    # 证据汇总
│   ├── NMPA_EMAIL_DRAFT.md       # 邮件草稿
│   ├── DOCTOR_RECRUITMENT.md     # 医生招募（已更新）
│   └── MOBILE_APP_DESIGN.md      # APP设计
├── examples/
│   └── uart_control.c
└── PulseTherapy/
    ├── PulseTherapy.h
    ├── PulseTherapy.cpp
    └── examples/
        └── ParkinsonTherapy/
            └── ParkinsonTherapy.ino
```

## 待办清单（更新）

### 今天必须完成：
1. ✅ 搜索收集证据
2. ✅ 更新邮件草稿
3. ✅ 添加强制性免责声明
4. ✅ 强调公益性质
5. ⏳ 上传GitHub仓库
6. ⏳ 发送邮件给药监局

### 等待药监局回复期间：
7. ⏳ 医生招募（发布到医学论坛）
8. ⏳ PCB制作（嘉立创下单）
9. ⏳ APP设计细化

## 下一步行动

用户现在需要：
1. 上传GitHub仓库（所有文件已准备好）
2. 发送邮件给药监局（证据已收集）

**GitHub上传命令**：
```bash
cd TLSR8269_SixChannel_Pulse_Generator
git add .
git commit -m "v1.0 完整版本：添加证据、免责声明、公益声明"
git push origin main
```

---

*每一个行动，都是向希望迈进的一步。*
*安全、透明、公益，是我们的底线。*
