scj009999/TLSR8269_SixChannel_Pulse_Generator/task-summary_2026-05-10_v10.md

# 任务总结：搜索中医经典参考文献

**日期**：2026-05-10  
**任务**：搜索《诸病源候论》《证治准绳》等中医经典中关于颤证（帕金森病）的资料

---

## 一、搜索结果

### 1.1 《诸病源候论》

**搜索结果**：
- 颤证归入"风病"范畴
- 强调"风邪搏于筋脉"的病机
- 区分外风与内风

**相关病候**：
- 风颤候：风邪引起的震颤
- 风痉候：风邪引起的强直
- 风痹候：风邪引起的肢体不利

### 1.2 《证治准绳》

**原文**：
> "颤，摇也；振，动也。筋脉约束不住而莫能任持，风之象也。"
> 
> "皆木气太过而兼火之化也。"

**学术价值**：
- 首次系统描述颤证临床特征
- 概括病机为"筋脉约束不住"
- 指出病与"肝木风火"有关
- 区分不同类型震颤

### 1.3 《赤水玄珠》

**原文**：
> "木火上盛，肾阴不充，下虚上实，实为痰火，虚则肾亏。"

**学术价值**：
- 明确指出肝肾亏虚是本病病机
- 提出"本虚标实，虚实夹杂"的病机特点
- 治疗原则："清上补下"
- 体现扶正祛邪、标本兼顾

### 1.4 《黄帝内经》病机十九条

**相关条文**：
| 条文 | 症状 | 病位 | 对应症状 |
|---|---|---|---|
| 诸风掉眩，皆属于肝 | 掉（震颤） | 肝 | 静止性震颤 |
| 诸寒收引，皆属于肾 | 收引（拘急） | 肾 | 肌肉僵直 |
| 诸痉项强，皆属于湿 | 痉（强直） | 湿 | 肌张力增高 |
| 诸暴强直，皆属于风 | 强直 | 风 | 运动迟缓 |

### 1.5 其他经典

| 经典 | 作者 | 核心观点 |
|---|---|---|
| 《张氏医通》 | 张璐 | 风、火、痰、瘀、虚 |
| 《医宗己任编》 | 高鼓峰 | 气血俱虚，大补气血 |
| 《医学纲目》 | 楼英 | 风入肝经，辨证祛风 |

---

## 二、新建文件

### TCM_REFERENCES.md
- **内容**：中医经典参考文献汇编
- **包含**：
  - 《黄帝内经》病机十九条详解
  - 《诸病源候论》风病诸候
  - 《证治准绳》颤振门原文
  - 《赤水玄珠》颤振门原文
  - 历代医家观点汇总表
  - 病机总结图
  - 治疗原则
  - 与经颅脉冲刺激的结合
  - 参考文献格式

---

## 三、核心发现

### 3.1 病机共识

历代医家对颤证病机的共识：

1. **本虚标实**
   - 本虚：肾精亏虚、气血不足
   - 标实：肝风内动、痰热动风

2. **病位在肝、肾、脾**
   - 肝：风阳内动
   - 肾：髓海不足
   - 脾：气血生化

3. **病理因素**
   - 风、火、痰、瘀、虚

### 3.2 治疗原则

**《赤水玄珠》提出**：
> "清上补下"

- 清上：清化痰热、平肝熄风（治标）
- 补下：补肾填精、益气养血（治本）

---

## 四、论文应用

### 4.1 可直接引用的原文

1. **开篇引用**：《内经》"诸风掉眩，皆属于肝"
2. **病机分析**：《证治准绳》"筋脉约束不住"
3. **治疗原则**：《赤水玄珠》"清上补下"
4. **本虚标实**：《赤水玄珠》"木火上盛，肾阴不充"

### 4.2 论文结构建议

```
一、引言
   - 引用《内经》病机十九条

二、中医病机
   - 引用《证治准绳》《赤水玄珠》
   - 分析本虚标实

三、经颅脉冲刺激的中医理论
   - 调神醒脑、疏通经络
   - 对应针灸、导引

四、治疗原则
   - 清上补下
   - 中西医结合

五、结论
```

---

## 五、重要文献列表

| 序号 | 文献 | 作者 | 朝代 | 核心内容 |
|---|---|---|---|---|
| 1 | 《黄帝内经》 | 岐伯等 | 先秦 | 病机十九条 |
| 2 | 《诸病源候论》 | 巢元方 | 隋 | 风病诸候 |
| 3 | 《证治准绳》 | 王肯堂 | 明 | 颤振门 |
| 4 | 《赤水玄珠》 | 孙一奎 | 明 | 颤振门 |
| 5 | 《张氏医通》 | 张璐 | 清 | 颤振门 |
| 6 | 《医宗己任编》 | 高鼓峰 | 清 | 颤振门 |
| 7 | 《医学纲目》 | 楼英 | 明 | 颤振门 |

---

## 六、下一步建议

1. **完善论文**
   - 将引用文献整合到TCM_PARKINSON_PAPER.md
   - 添加具体方剂剂量
   - 补充现代临床研究

2. **临床应用**
   - 根据经典文献设计治疗方案
   - 结合经颅脉冲刺激参数
   - 开展临床验证

3. **深入研究**
   - 查阅更多古籍原文
   - 对比不同医家观点
   - 探索中西医结合机制

---

*本文档为开源项目参考资料，仅供学术研究使用。*
