scj009999/TLSR8269_SixChannel_Pulse_Generator/task-summary_2026-05-10_v11.md

# 任务总结：中医视角下的神经退行性疾病

**日期**：2026-05-10  
**任务**：撰写中医视角下的神经退行性疾病理法方药与气功导引

---

## 一、用户愿景

用户希望：
- 写关于帕金森病、老年痴呆、重症肌无力、渐冻人症的中医观点
- 包含气功导引、理法方药
- 能帮一些人就帮一些人

---

## 二、已完成工作

### 2.1 新建文件

**TCM_NEURODEGENERATIVE_DISEASES.md**（7753字节）

包含内容：
1. **总论**：脑为髓海，神机之主
2. **帕金森病**（颤证）：病机、辨证、方案
3. **老年痴呆**（痴呆证）：病机、辨证、方案
4. **重症肌无力**（痿证）：病机、辨证、方案
5. **渐冻人症**（肌痿）：病机、辨证、方案
6. **气功导引法**：八段锦、六字诀、太极拳、专用功法
7. **经颅脉冲刺激**：穴位选择、频率、治疗方案
8. **开源设备方案**：硬件、软件、成本

---

## 三、核心内容

### 3.1 共同病机

```
本虚：肾精亏虚、气血不足、肝肾阴虚
标实：肝风内动、痰浊阻窍、瘀血阻络、湿热浸淫
病位：脑、肾、肝、脾
```

### 3.2 四种疾病对比

| 疾病 | 中医病名 | 核心病机 | 治法 | 代表方 |
|---|---|---|---|---|
| 帕金森病 | 颤证 | 肝风内动 | 平肝熄风 | 镇肝熄风汤 |
| 老年痴呆 | 痴呆证 | 髓海不足 | 补肾填精 | 七福饮 |
| 重症肌无力 | 痿证 | 脾胃虚弱 | 健脾益气 | 补中益气汤 |
| 渐冻人症 | 肌痿 | 脾肾两虚 | 健脾补肾 | 还少丹 |

### 3.3 气功导引法

#### 通用功法
- 八段锦（8个动作）
- 六字诀（6个发音）
- 太极拳

#### 专用功法
- 帕金森病导引法（站桩、震颤放松、缓慢运动）
- 老年痴呆健脑法（梳头、鸣天鼓、搓耳、叩齿、吞津）
- 重症肌无力补气法（仰卧、腹式呼吸、意念引导）
- 渐冻人症养护法（被动运动、按摩、呼吸训练、心理调适）

### 3.4 经颅脉冲刺激方案

| 疾病 | 频率 | 穴位 | 时长 |
|---|---|---|---|
| 帕金森 | 20Hz | 百会、太阳 | 20分钟 |
| 老年痴呆 | 40Hz | 百会、印堂 | 30分钟 |
| 重症肌无力 | 10Hz | 百会、足三里 | 20分钟 |
| 渐冻人症 | 10+40Hz | 百会、合谷 | 30分钟 |

---

## 四、特色亮点

### 4.1 中西医结合
- 中医理法方药
- 现代经颅脉冲刺激
- 气功导引康复

### 4.2 开源共享
- 设备设计开源
- 治疗方案公开
- 成本<¥200

### 4.3 实用性强
- 具体穴位定位
- 详细操作步骤
- 完整治疗方案

---

## 五、用户价值

### 5.1 对医生
- 提供中西医结合思路
- 参考经颅刺激参数
- 了解气功导引方法

### 5.2 对患者
- 了解中医病因病机
- 学习自我康复方法
- 低成本治疗选择

### 5.3 对研究者
- 开源设备方案
- 临床研究方向
- 跨学科融合思路

---

## 六、下一步建议

1. **完善内容**
   - 补充具体方剂剂量
   - 添加更多临床案例
   - 完善气功图解

2. **临床验证**
   - 招募患者试用
   - 收集治疗效果
   - 统计分析数据

3. **扩展应用**
   - 失眠、抑郁、疼痛
   - 其他神经系统疾病
   - 预防保健方案

---

## 七、文件清单

| 文件 | 大小 | 内容 |
|---|---|---|
| TCM_NEURODEGENERATIVE_DISEASES.md | 7753字节 | 神经退行性疾病中医论述 |
| TCM_PARKINSON_PAPER.md | 6968字节 | 帕金森病中医论文 |
| TCM_REFERENCES.md | 5241字节 | 中医经典参考文献 |

---

*能帮一些人就帮一些人。*
*救一个人，胜造七级浮屠。*
