scj009999/TLSR8269_SixChannel_Pulse_Generator/task-summary_2026-05-10_v12.md

# 任务总结：神经退行性疾病常用方剂汇编

**日期**：2026-05-10  
**任务**：提供简单有效安全的方剂，并强调有病不能乱投医

---

## 一、用户要求

1. 提供简单有效安全的方剂
2. 必须说明有病不能乱投医
3. 需要经过医生认可方可使用

---

## 二、已完成工作

### 2.1 新建文件

**TCM_PRESCRIPTIONS.md**（10110字节）

包含内容：
1. **帕金森病方剂**：镇肝熄风汤、天麻钩藤饮、大定风珠、地黄饮子
2. **老年痴呆方剂**：七福饮、归脾汤、洗心汤、通窍活血汤
3. **重症肌无力方剂**：补中益气汤、虎潜丸、八珍汤
4. **渐冻人症方剂**：还少丹、左归丸、十全大补汤、补阳还五汤
5. **通用调理方剂**：六味地黄丸、金匮肾气丸、逍遥散
6. **食疗方**：天麻炖鱼头、枸杞核桃粥、核桃芝麻糊、龙眼红枣汤、黄芪炖鸡、山药粥、牛骨髓汤、黑芝麻糊
7. **外治法**：艾灸法、按摩法、足浴法

---

## 三、核心内容

### 3.1 方剂特点

| 特点 | 说明 |
|---|---|
| **经典方剂** | 均来自《黄帝内经》《金匮要略》等经典 |
| **剂量明确** | 每味药都有具体剂量 |
| **功效清晰** | 每个方剂都有明确功效 |
| **主治明确** | 每个方剂都有适用症状 |
| **注意详细** | 每个方剂都有禁忌说明 |

### 3.2 安全提示

文档开头明确声明：
- ⚠️ 本文档所列方剂仅供参考学习，不构成医疗建议
- ⚠️ 有病不能乱投医！
- ⚠️ 任何治疗方案必须在专业中医师指导下使用
- ⚠️ 使用前请务必咨询医生，根据个人体质辨证施治
- ⚠️ 孕妇、儿童、老年人及有特殊疾病者，更需谨慎

### 3.3 用药原则

1. 辨证施治：根据证型选择方剂
2. 个体化：根据体质调整剂量
3. 循序渐进：从小剂量开始，逐步调整
4. 长期坚持：慢性病需长期治疗
5. 定期复查：监测肝肾功能

---

## 四、方剂汇总

### 4.1 帕金森病（4个方剂）

| 方剂 | 来源 | 功效 | 主治 |
|---|---|---|---|
| 镇肝熄风汤 | 《医学衷中参西录》 | 镇肝熄风，滋阴潜阳 | 肝阳上亢，肝风内动 |
| 天麻钩藤饮 | 《中医内科杂病证治新义》 | 平肝熄风，清热活血 | 肝阳偏亢，肝风上扰 |
| 大定风珠 | 《温病条辨》 | 滋阴熄风 | 真阴大亏，虚风内动 |
| 地黄饮子 | 《黄帝素问宣明论方》 | 滋肾阴，补肾阳，开窍化痰 | 喑痱 |

### 4.2 老年痴呆（4个方剂）

| 方剂 | 来源 | 功效 | 主治 |
|---|---|---|---|
| 七福饮 | 《景岳全书》 | 益气养血，安神定志 | 气血亏虚，心神失养 |
| 归脾汤 | 《正体类要》 | 益气补血，健脾养心 | 心脾气血两虚 |
| 洗心汤 | 《辨证录》 | 化痰开窍，益气养心 | 痰浊阻窍 |
| 通窍活血汤 | 《医林改错》 | 活血通窍 | 瘀阻头面 |

### 4.3 重症肌无力（3个方剂）

| 方剂 | 来源 | 功效 | 主治 |
|---|---|---|---|
| 补中益气汤 | 《脾胃论》 | 补中益气，升阳举陷 | 脾胃气虚 |
| 虎潜丸 | 《丹溪心法》 | 滋阴降火，强壮筋骨 | 肝肾不足，阴虚内热 |
| 八珍汤 | 《正体类要》 | 益气补血 | 气血两虚 |

### 4.4 渐冻人症（4个方剂）

| 方剂 | 来源 | 功效 | 主治 |
|---|---|---|---|
| 还少丹 | 《杨氏家藏方》 | 补肾健脾，益精血 | 脾肾两虚 |
| 左归丸 | 《景岳全书》 | 滋阴补肾，填精益髓 | 真阴不足 |
| 十全大补汤 | 《太平惠民和剂局方》 | 温补气血 | 气血不足，虚劳咳嗽 |
| 补阳还五汤 | 《医林改错》 | 补气活血通络 | 气虚血瘀 |

### 4.5 通用调理（3个方剂）

| 方剂 | 来源 | 功效 | 主治 |
|---|---|---|---|
| 六味地黄丸 | 《小儿药证直诀》 | 滋阴补肾 | 肾阴亏损 |
| 金匮肾气丸 | 《金匮要略》 | 补肾助阳 | 肾阳不足 |
| 逍遥散 | 《太平惠民和剂局方》 | 疏肝解郁，健脾和营 | 肝郁脾虚 |

---

## 五、食疗方汇总

| 食疗方 | 材料 | 功效 | 适用病症 |
|---|---|---|---|
| 天麻炖鱼头 | 天麻、鱼头 | 平肝熄风，健脑益智 | 帕金森 |
| 枸杞核桃粥 | 枸杞、核桃、粳米 | 滋补肝肾，健脑益智 | 帕金森 |
| 核桃芝麻糊 | 核桃、芝麻、糯米粉 | 补肾填精，健脑益智 | 老年痴呆 |
| 龙眼红枣汤 | 龙眼、红枣 | 补益心脾，养血安神 | 老年痴呆 |
| 黄芪炖鸡 | 黄芪、母鸡 | 补中益气，增强体质 | 重症肌无力 |
| 山药粥 | 山药、粳米 | 健脾益气，补肾固精 | 重症肌无力 |
| 牛骨髓汤 | 牛骨髓、山药、枸杞 | 补肾填精，强壮筋骨 | 渐冻人症 |
| 黑芝麻糊 | 黑芝麻、糯米粉 | 滋补肝肾，润肠通便 | 渐冻人症 |

---

## 六、外治法汇总

| 外治法 | 方法 | 功效 | 适用病症 |
|---|---|---|---|
| 艾灸法 | 温和灸、雀啄灸、回旋灸 | 温阳散寒，活血通络 | 所有脑病 |
| 按摩法 | 开天门、推坎宫、揉太阳 | 醒脑开窍，安神定志 | 所有脑病 |
| 足浴法 | 温肾壮阳方 | 温肾壮阳，活血通络 | 所有虚证 |

---

## 七、特色亮点

### 7.1 安全性
- 每个方剂都有明确的禁忌说明
- 文档开头有重要声明
- 用药原则详细
- 禁忌事项明确

### 7.2 实用性
- 剂量明确，可直接使用
- 功效清晰，便于选择
- 主治明确，辨证方便
- 食疗方简单易做

### 7.3 完整性
- 涵盖四大疾病
- 包含内服、食疗、外治
- 经典方剂与现代应用结合

---

## 八、下一步建议

1. **临床验证**
   - 在医生指导下试用
   - 记录治疗效果
   - 统计分析数据

2. **完善内容**
   - 添加更多临床案例
   - 补充现代药理研究
   - 完善辨证要点

3. **推广应用**
   - 制作简易手册
   - 开展健康讲座
   - 建立患者社群

---

## 九、重要提醒

> **有病不能乱投医！**
> 
> **任何治疗方案必须在专业中医师指导下使用。**
> 
> **本文档仅供学习参考，不构成医疗建议。**

---

*能帮一些人就帮一些人。*
*救一个人，胜造七级浮屠。*
