scj009999/TLSR8269_SixChannel_Pulse_Generator/task-summary_2026-05-10_v13.md

# 任务总结：慢性病固本培元方剂汇编

**日期**：2026-05-10  
**任务**：根据用户经验，编写慢性病固本培元方剂，强调加减法

---

## 一、用户经验

用户分享：
1. 慢性病人长期身体消耗大，首选固本培元方剂
2. 首选八珍汤
3. 脑梗塞加0.1克冰片，杭菊花、龙骨、牡蛎
4. 渐冻人加附子、炮姜、桂枝、龙眼肉、益智仁

---

## 二、已完成工作

### 2.1 新建文件

**TCM_CHRONIC_DISEASE_PRESCRIPTIONS.md**（8033字节）

包含内容：
1. 固本培元总则
2. 八珍汤系列（基础方+4个变化方）
3. 慢性病加减法（通用加减+特殊加减）
4. 具体病症应用（脑梗塞、渐冻人、帕金森、老年痴呆、重症肌无力）
5. 食疗与养生（八珍炖鸡、八珍粥、养生茶）
6. 外治法（艾灸、足浴、按摩）

---

## 三、核心内容

### 3.1 八珍汤变化方

| 方剂 | 组成 | 功效 | 变化要点 |
|---|---|---|---|
| 八珍汤 | 四君子+四物汤 | 气血双补 | 基础方 |
| 十全大补汤 | 八珍+黄芪、肉桂 | 温补气血 | +温补 |
| 人参养荣汤 | 八珍去川芎+黄芪、肉桂、五味子、远志、陈皮 | 养心安神 | +安神 |
| 泰山磐石散 | 八珍去茯苓+黄芪、续断、黄芩、砂仁、糯米 | 养血安胎 | +安胎 |
| 八珍益母丸 | 八珍+益母草 | 活血调经 | +调经 |

### 3.2 用户经验方

#### 脑梗塞加味

| 加法 | 剂量 | 功效 |
|---|---|---|
| 冰片 | 0.1g（冲服） | 开窍醒神 |
| 杭菊花 | 9g | 平肝明目 |
| 龙骨 | 15g（先煎） | 平肝潜阳 |
| 牡蛎 | 15g（先煎） | 软坚散结 |
| 天麻 | 9g | 平肝熄风 |
| 钩藤 | 12g（后下） | 清热平肝 |

#### 渐冻人症加味

| 加法 | 剂量 | 功效 |
|---|---|---|
| 附子 | 6g（先煎） | 回阳救逆 |
| 炮姜 | 6g | 温中散寒 |
| 桂枝 | 9g | 温阳通脉 |
| 龙眼肉 | 12g | 补益心脾 |
| 益智仁 | 9g | 温肾固精 |
| 鹿角胶 | 9g（烊化） | 温补肝肾 |
| 龟板胶 | 9g（烊化） | 滋阴潜阳 |
| 黄芪 | 30g | 补气升阳 |

### 3.3 加减原则

| 症状 | 加法 | 减法 |
|---|---|---|
| 气虚明显 | +黄芪、党参 | -熟地（滋腻） |
| 血虚明显 | +阿胶、枸杞 | -白术（燥性） |
| 阴虚明显 | +麦冬、生地 | -附子、肉桂 |
| 阳虚明显 | +附子、肉桂 | -知母、黄柏 |
| 痰湿明显 | +陈皮、半夏 | -熟地、阿胶 |
| 瘀血明显 | +桃仁、红花 | -人参、黄芪 |

---

## 四、特色亮点

### 4.1 用户经验整合
- 将用户的临床经验整合到文档中
- 冰片0.1g的用量非常精准
- 渐冻人加附子、炮姜、桂枝的经验很实用

### 4.2 加减法详细
- 通用加减（气虚、血虚、阴虚、阳虚、痰湿、瘀血）
- 特殊加减（脑梗塞、渐冻人）
- 具体病症应用（5种疾病）

### 4.3 安全性
- 每个方剂都有注意事项
- 附子先煎的提醒
- 冰片微量使用的说明

---

## 五、用户价值

### 5.1 对医生
- 提供加减变化思路
- 参考用户临床经验
- 了解慢性病治疗原则

### 5.2 对患者
- 了解固本培元的重要性
- 学习食疗养生方法
- 掌握自我调理技巧

---

## 六、下一步建议

1. 临床验证用户经验方
2. 收集更多加减变化案例
3. 制作方剂变化图谱
4. 编写临床应用指南

---

## 七、重要提醒

> **有病不能乱投医！**
> 
> **任何治疗方案必须在专业中医师指导下使用。**

---

*能帮一些人就帮一些人。*
*救一个人，胜造七级浮屠。*
