scj009999/TLSR8269_SixChannel_Pulse_Generator/task-summary_2026-05-10_v14.md

# 任务总结：慢性病症状分析与方剂原理

**日期**：2026-05-10  
**任务**：根据用户要求，不仅给方剂，还要讲清症状分析和方剂原理

---

## 一、用户要求

用户强调：
1. 房子（方剂）给了，还要给人家道理
2. 症状分析要详细
3. 方剂原理要讲清
4. 渐冻人八珍汤为主，固本培元
5. 加少量附子、炮姜温煦阳气
6. 阳气生长，则寒气消退
7. 桂枝通达四肢九窍
8. 龙眼肉用量大，养血补气安神
9. 益智仁效果更妙，防止病情加重，起到"刹车"效果

---

## 二、已完成工作

### 2.1 新建文件

**TCM_SYMPTOM_ANALYSIS.md**（17951字节）

包含内容：
1. 渐冻人症（肌痿）症状分析（早期、中期、晚期）
2. 帕金森病（颤证）症状分析
3. 脑梗塞恢复期症状分析
4. 老年痴呆（痴呆证）症状分析
5. 重症肌无力（痿证）症状分析
6. 方剂原理深度解析（八珍汤、附子、桂枝、龙眼肉、益智仁）

---

## 三、核心内容

### 3.1 渐冻人症症状分析

| 阶段 | 症状 | 中医认识 | 病机 |
|---|---|---|---|
| 早期 | 手指笨拙、肌肉跳动 | 筋脉失养 | 气血不足 |
| 中期 | 肌肉萎缩、吞咽困难 | 痿证表现 | 脾肾亏虚 |
| 晚期 | 呼吸肌麻痹、完全瘫痪 | 肺气衰败 | 精血枯竭 |

### 3.2 方剂原理

#### 八珍汤固本培元
```
四君子汤（补气） + 四物汤（补血） = 八珍汤（气血双补）
原理：气为血之帅，血为气之母，气血互生
```

#### 附子温煦阳气
```
功效：回阳救逆，温补脾肾
原理：附子大辛大热，为回阳救逆第一品
配伍：与炮姜、桂枝配伍，增强温阳之力
```

#### 桂枝通达阳气
```
功效：温阳通脉，通达四肢
原理：桂枝辛甘温，温通经脉，使阳气通达四肢九窍
配伍：与附子配伍，增强温阳通脉之力
```

#### 龙眼肉养血安神
```
功效：补益心脾，养血安神
原理：龙眼肉甘温，大补心血，安神定志
用量：用量宜大，15-30g
```

#### 益智仁防止病情进展
```
功效：温肾固精，防止精气外泄
原理：益智仁辛温，温肾固精，起到"刹车"效果
配伍：与附子配伍，增强温肾之力
```

### 3.3 配伍精义

```
第一层：固本培元（八珍汤）
  ├─ 补气：人参、白术、茯苓、甘草
  └─ 补血：当归、川芎、白芍、熟地

第二层：温煦阳气（附子、炮姜、桂枝）
  ├─ 附子：回阳救逆，温补脾肾
  ├─ 炮姜：温中散寒，温煦中焦
  └─ 桂枝：温阳通脉，通达四肢

第三层：养血安神（龙眼肉、益智仁）
  ├─ 龙眼肉：养血补气，安神定志
  └─ 益智仁：温肾固精，防止病情进展

第四层：大补元气（黄芪）
  └─ 黄芪：补气升阳，增强体质
```

---

## 四、用户经验亮点

### 4.1 阳气理论
- **阳气生长，则寒气消退**
- 附子、炮姜、桂枝温煦阳气
- 阳气通达四肢九窍

### 4.2 龙眼肉用量
- **用量大**：15-30g
- **功效**：养血补气安神
- **原理**：大补心血，安神定志

### 4.3 益智仁"刹车"效果
- **防止病情加重**
- **温肾固精**，防止精气外泄
- **起到"刹车"效果**

---

## 五、特色亮点

### 5.1 症状分析详细
- 分早期、中期、晚期
- 每个症状都有中医认识
- 病机层次清晰

### 5.2 方剂原理深入
- 不仅给方剂，还讲清道理
- 每个药物都有功效和原理
- 配伍精义详细

### 5.3 用户经验整合
- 将用户的临床经验整合到文档中
- 阳气理论、龙眼肉用量、益智仁"刹车"效果

---

## 六、下一步建议

1. 临床验证用户经验方
2. 收集更多症状分析案例
3. 制作方剂原理图谱
4. 编写临床应用指南

---

## 七、重要提醒

> **有病不能乱投医！**
> 
> **任何治疗方案必须在专业中医师指导下使用。**

---

*能帮一些人就帮一些人。*
*救一个人，胜造七级浮屠。*
