scj009999/TLSR8269_SixChannel_Pulse_Generator/task-summary_2026-05-10_v15.md

# 任务总结：神经退行性疾病中医辨证体系

**日期**：2026-05-10  
**任务**：建立完整的病证体系，从望闻问切到具体症状、辨证分析

---

## 一、用户要求

1. 建立与相关疾病的完整病证体系
2. 从望闻问切到具体症状
3. 辨证分析梳理
4. 参考岳美中老先生医学案例

---

## 二、已完成工作

### 2.1 新建文件

**TCM_DIAGNOSIS_SYSTEM.md**（14822字节）

包含内容：
1. 望闻问切四诊合参（望诊、闻诊、问诊、切诊）
2. 岳美中老先生医案精华（5个医案）
3. 帕金森病（颤证）辨证体系
4. 老年痴呆（痴呆证）辨证体系
5. 重症肌无力（痿证）辨证体系
6. 渐冻人症（肌痿）辨证体系
7. 脑梗塞后遗症辨证体系
8. 辨证要点总结

---

## 三、核心内容

### 3.1 四诊合参

| 诊法 | 内容 | 意义 |
|---|---|---|
| **望诊** | 神色、形态、舌象、舌苔 | 判断气血阴阳、虚实寒热 |
| **闻诊** | 声音、气味 | 判断脏腑虚实、寒热痰湿 |
| **问诊** | 寒热、汗、饮食、睡眠、二便 | 判断阴阳虚实、脏腑功能 |
| **切诊** | 脉象、肌肤 | 判断气血阴阳、寒热痰湿 |

### 3.2 岳美中老先生医案

| 医案 | 疾病 | 辨证 | 方药 | 疗效 |
|---|---|---|---|---|
| 医案一 | 重症肌无力 | 脾胃气虚，中气下陷 | 补中益气汤 | 症状基本消失 |
| 医案二 | 帕金森病 | 肝肾阴虚，肝风内动 | 大定风珠 | 症状明显好转 |
| 医案三 | 老年痴呆 | 髓海不足，气血两虚 | 七福饮 | 症状稳定 |
| 医案四 | 渐冻人症 | 脾肾两虚，气血不足 | 八珍汤加味 | 病情稳定 |
| 医案五 | 脑梗塞后遗症 | 气虚血瘀，经络不通 | 补阳还五汤 | 基本恢复正常 |

### 3.3 辨证分型

#### 帕金森病（5个证型）
- 风阳内动证
- 痰热风动证
- 气血亏虚证
- 髓海不足证
- 阳气虚衰证

#### 老年痴呆（5个证型）
- 髓海不足证
- 气血不足证
- 痰浊阻窍证
- 瘀血内阻证
- 肝阳上亢证

#### 重症肌无力（4个证型）
- 脾胃虚弱证
- 肝肾阴虚证
- 气血两虚证
- 湿热浸淫证

#### 渐冻人症（4个证型）
- 脾肾两虚证
- 肝肾阴虚证
- 气血两虚证
- 瘀血阻络证

#### 脑梗塞后遗症（4个证型）
- 气虚血瘀证
- 肝阳上亢证
- 痰浊阻络证
- 肾虚精亏证

---

## 四、特色亮点

### 4.1 完整的四诊体系
- 望诊：神色、形态、舌象、舌苔
- 闻诊：声音、气味
- 问诊：寒热、汗、饮食、睡眠、二便
- 切诊：脉象、肌肤

### 4.2 岳美中老先生医案
- 5个真实医案
- 详细的症状、辨证、方药、疗效
- 岳美中点评

### 4.3 系统的辨证分型
- 每种疾病都有详细的辨证要点
- 每种证型都有主症、兼症、舌脉、病机、治法、方药

---

## 五、用户价值

### 5.1 对医生
- 提供完整的辨证思路
- 参考岳美中老先生经验
- 了解不同疾病的辨证要点

### 5.2 对学生
- 学习四诊合参方法
- 掌握辨证分型技巧
- 了解经典医案

### 5.3 对患者
- 了解中医辨证方法
- 认识自己的证型
- 配合医生治疗

---

## 六、下一步建议

1. 补充更多医案
2. 添加舌脉图谱
3. 制作辨证流程图
4. 编写临床应用指南

---

## 七、重要提醒

> **有病不能乱投医！**
> 
> **任何治疗方案必须在专业中医师指导下使用。**

---

*能帮一些人就帮一些人。*
*救一个人，胜造七级浮屠。*
