scj009999/TLSR8269_SixChannel_Pulse_Generator/task-summary_2026-05-10_v7.md

# 任务总结：GitHub仓库推广与影响力追踪

**日期**：2026-05-10  
**任务**：查看仓库状态，提供推广指南

---

## 一、仓库状态

### 1.1 基本信息

```json
{
  "name": "TLSR8269_SixChannel_Pulse_Generator",
  "full_name": "scj009999/TLSR8269_SixChannel_Pulse_Generator",
  "private": false,
  "owner": {
    "login": "scj009999",
    "id": 118176020
  }
}
```

**状态**：✅ 公开仓库，可正常访问

### 1.2 访问数据

由于GitHub API需要认证，无法直接获取访问数据。

**查看方法**：
1. 登录GitHub
2. 访问仓库
3. 点击 Insights → Traffic
4. 查看 Views、Clones、Referrals

---

## 二、用户心愿

用户希望：
- 哪怕只有一个人下载
- 能帮一个就帮一个
- "救一个人，胜造七级浮屠"

---

## 三、推广策略

### 3.1 优化仓库

- 完善README（使命声明、快速开始、成本分析）
- 添加标签（parkinsons, tms, open-source-hardware等）
- 添加Shields.io徽章（Stars、Forks、License）

### 3.2 技术社区

| 平台 | 方式 |
|---|---|
| 知乎 | 专栏文章 |
| CSDN | 技术博客 |
| V2EX | 分享帖子 |
| 掘金 | 技术文章 |

### 3.3 患者社区

| 平台 | 方式 |
|---|---|
| 帕金森病友群 | 分享项目 |
| 好大夫在线 | 咨询医生 |
| 丁香园 | 医生社区 |
| 小红书 | 患者分享 |

### 3.4 开源社区

| 平台 | 方式 |
|---|---|
| GitHub Trending | 争取上榜 |
| Hacker News | 分享项目 |
| Reddit | r/Parkinsons |
| Hackaday | 投稿项目 |

---

## 四、影响力追踪

### 4.1 GitHub统计

- Stars、Forks、Issues
- Traffic（Views、Clones）
- Referring sites

### 4.2 第三方工具

- Star History：https://star-history.com/
- Shields.io徽章
- GitHub Actions自动统计

### 4.3 手动记录

创建STATS.md记录：
- 每日Stars/Forks
- 月度汇总
- 里程碑（100/500/1000 Stars）

---

## 五、用户反馈

### 5.1 GitHub Issues模板

创建反馈模板，收集：
- 使用体验
- 治疗效果
- 改进建议

### 5.2 在线问卷

使用腾讯问卷收集：
- 制作难度
- 使用效果
- 推荐意愿

---

## 六、成功案例

### 6.1 记录模板

```markdown
## 案例 #001
- 日期：2026-05-XX
- 地区：XX省XX市
- 病情：帕金森病5年
- 效果：手抖减轻30%
- 评价：满意
```

### 6.2 效果统计

| 效果 | 人数 | 占比 |
|---|---|---|
| 明显改善 | X | X% |
| 略有改善 | X | X% |
| 无明显效果 | X | X% |

---

## 七、新建文件

### GITHUB_PROMOTION_GUIDE.md
- **内容**：GitHub仓库推广与影响力追踪指南
- **包含**：
  - 查看仓库访问数据方法
  - 优化仓库信息
  - 社交媒体推广策略
  - 推广文章模板
  - 影响力追踪工具
  - 用户反馈收集
  - 推广时间线
  - 成功案例追踪
  - 法律合规提醒

---

## 八、下一步行动

1. **完善仓库**
   - 优化README
   - 添加标签
   - 添加徽章

2. **撰写文章**
   - 知乎技术文章
   - CSDN教程
   - 项目介绍

3. **社区推广**
   - 帕金森病友群
   - 医生社区
   - 开源社区

4. **追踪效果**
   - 每日查看Stars
   - 收集用户反馈
   - 记录成功案例

---

## 九、重要提醒

⚠️ **必须遵守**：
- 明确标注"实验性项目"
- 强调"需在医生指导下使用"
- 禁止商业用途
- 用户风险自负

⚠️ **必须做到**：
- 保护患者隐私
- 不夸大疗效
- 不替代正规治疗
- 及时报告不良事件

---

*每一个下载、每一次使用、每一条反馈，都是对这个项目最大的支持。*
*救一个人，胜造七级浮屠。*
