scj009999/TLSR8269_SixChannel_Pulse_Generator/task-summary_2026-05-10_v8.md

# 任务总结：整合README与项目文档

**日期**：2026-05-10  
**任务**：将分散在docs文件夹的项目介绍整合到README.md

---

## 一、问题发现

用户反馈：
- README.md显示的是"16路脉冲仪"的简介（早期版本）
- 项目真正的介绍分散在docs文件夹中
- 访问者无法一眼看到项目的完整信息

---

## 二、解决方案

### 2.1 整合内容到README.md

将以下分散的内容整合到README：

#### 新增内容
1. **项目使命声明**
   - "救一个人，胜造七级浮屠"
   - 公益性质强调

2. **临床证据**
   - 刘河生教授团队Nature论文
   - 有效率55.5%-70%
   - 产业化进展

3. **核心特性**
   - 低成本（<¥200）
   - 医疗安全（8重保护）
   - 技术参数

4. **制作指南**
   - 快速开始步骤
   - 下载代码
   - 制作硬件
   - 制作电极
   - 编译烧录
   - 下载APP

5. **文档索引**
   - 完整的文档表格
   - 快速链接到各文档

6. **推广与影响力**
   - 查看访问量方法
   - 推广渠道

7. **致谢**
   - 感谢使用者
   - "能帮一个是一个"

### 2.2 更新项目结构

更新项目结构树，包含所有新建文件：
- hardware/ 文件夹内容
- docs/ 文件夹所有文档
- mixly_blocks/ 图形化积木

---

## 三、README.md更新内容

### 更新前后对比

#### 更新前
- 只有基础技术参数
- 缺少临床证据
- 缺少制作指南
- 缺少文档索引

#### 更新后
- ✅ 完整的项目使命
- ✅ 临床证据（Nature论文）
- ✅ 核心特性（低成本+安全）
- ✅ 制作指南（5步快速开始）
- ✅ 文档索引（表格形式）
- ✅ 推广指南
- ✅ 致谢语

---

## 四、关键改进点

### 4.1 开头吸引

```markdown
> 🙏 **"救一个人，胜造七级浮屠"**
> 
> 本项目完全开源，不收取任何形式的费用。能帮一个是一个。
```

### 4.2 临床证据

```markdown
### 核心研究 - 刘河生教授团队
**2026年2月《自然》(Nature) 发表**
- 发现：帕金森病核心病变环路
- 效果：有效率55.5%-70%
- 应用：60+医院，3000+例
```

### 4.3 制作指南

```markdown
### 快速开始
1. 下载代码
2. 制作硬件
3. 制作电极
4. 编译烧录
5. 下载APP
```

### 4.4 文档索引

```markdown
| 主题 | 文档 |
|------|------|
| 医疗安全 | docs/MEDICAL_SAFETY.md |
| 电极制作 | docs/ELECTRODE_DESIGN.md |
| 生产指南 | docs/HUAQIU_PRODUCTION_GUIDE.md |
```

---

## 五、文件变更

### 修改的文件
- **README.md**：全面重写，整合所有关键信息

### 未修改的文件
- docs/ 文件夹内所有文档保持不变
- hardware/ 文件夹保持不变
- 代码文件保持不变

---

## 六、下一步建议

1. **提交到GitHub**
   ```bash
   git add README.md
   git commit -m "docs: 整合项目介绍到README，添加临床证据和制作指南"
   git push
   ```

2. **验证显示效果**
   - 访问GitHub仓库
   - 检查README显示是否正常
   - 确认所有链接可点击

3. **继续完善**
   - 根据反馈继续优化
   - 添加更多临床证据
   - 完善制作视频

---

## 七、用户价值

### 对访问者
- 一眼了解项目使命
- 快速找到所需文档
- 明确制作步骤

### 对患者
- 看到临床证据，增加信心
- 了解成本优势
- 知道如何制作

### 对贡献者
- 清晰的文档结构
- 明确的参与方式
- 完整的项目信息

---

*README是项目的门面，现在它真正反映了项目的价值和使命。*
