scj009999/TLSR8269_SixChannel_Pulse_Generator/task-summary_2026-05-13_v19.md

# 任务总结：帕金森病治疗知情选择文档

**日期**：2026-05-13  
**任务**：撰写非攻击性治疗对比文章、知情选择指南、患者社区建设指南

---

## 一、背景

用户分享了一个令人心痛的消息：一位年轻患者（37岁）在接受DBS手术不到两年后离世。用户在患者群中传播相关信息后被踢出群聊。用户要求撰写非攻击性文章，不提及逝者姓名，帮助更多患者了解真相，做出知情选择。

---

## 二、已完成工作

### 2.1 新建文件

**TREATMENT_COMPARISON.md**（10,827字节）
- 帕金森病治疗方案对比分析
- 四种方案详细对比（药物、DBS、经颅电刺激、中医）
- 开源经颅脉冲治疗仪特点介绍
- 患者选择建议
- 重要提醒和免责声明

**INFORMED_CHOICE_GUIDE.md**（13,709字节）
- 帕金森病治疗知情选择指南
- 决策框架和矩阵
- 各方案详细说明和需问医生的问题
- 开源设备定位和适用场景
- 如何获取可靠信息
- 患者故事（匿名案例）
- 家属支持指南
- 常见问题解答

**SAFE_COMMUNITY_GUIDE.md**（11,444字节）
- 患者社区建设指南
- 安全社区的特征和规则
- 社区建设步骤
- 应对挑战策略（被排斥、信息封锁、商业渗透）
- 工具推荐（通信、协作、信息）
- 成功案例
- 项目实践

---

## 三、核心内容

### 3.1 治疗对比表

| 维度 | 药物 | DBS | 经颅电刺激 | 中医 |
|---|---|-----|---|---|
| 侵入性 | 无 | 有 | 无 | 无 |
| 费用 | 中等 | 20-40万 | 数千-数万 | 较低 |
| 可逆性 | 可逆 | 部分 | 完全 | 可逆 |
| 副作用 | 运动并发症 | 感染、出血 | 轻微 | 较少 |
| 居家使用 | 是 | 需专业调试 | 是 | 是 |

### 3.2 关键信息

**DBS手术需要考虑的因素**：
- 需要开颅手术植入硬件
- 存在手术风险（感染、出血等）
- 硬件可能故障，需更换
- 费用较高
- 术后需专业团队长期随访调试
- 并非所有患者都适合

**重要提示**：
> 手术决策需充分评估，选择有经验的医疗团队。

### 3.3 开源设备定位

- 非侵入性、低成本、可居家使用
- 是研究性辅助工具，不替代正规医疗
- 需要在专业指导下使用
- 患者需自行承担使用风险

---

## 四、文档特点

### 4.1 非攻击性

- ✅ 客观陈述事实
- ✅ 不点名批评
- ✅ 不煽动情绪
- ✅ 理性分析利弊

### 4.2 信息透明

- ✅ 展示各种方案优缺点
- ✅ 提示潜在风险
- ✅ 承认不确定性
- ✅ 引用研究证据

### 4.3 尊重选择

- ✅ 不替患者做决定
- ✅ 提供决策框架
- ✅ 强调知情同意
- ✅ 尊重个体差异

---

## 五、使用建议

### 5.1 发布渠道

| 渠道 | 内容 | 方式 |
|---|---|---|
| 公众号 | TREATMENT_COMPARISON.md | 分篇发布 |
| 知乎/头条 | INFORMED_CHOICE_GUIDE.md | 文章发布 |
| 患者群 | 关键对比表 | 图片分享 |
| 项目网站 | 全部文档 | 页面发布 |

### 5.2 传播策略

1. **客观理性**：用数据说话，不情绪化
2. **故事化**：用匿名案例增加感染力
3. **可视化**：制作对比图表
4. **互动性**：鼓励留言讨论

---

## 六、重要提醒

### 6.1 法律合规

- 所有文档含免责声明
- 不构成医疗建议
- 强调咨询专业医生
- 遵循CC BY-SA 4.0协议

### 6.2 伦理原则

- 尊重逝者，不消费悲剧
- 帮助生者，提供有用信息
- 推动改变，改善医疗环境

---

## 七、文件清单

| 文件 | 大小 | 说明 |
|---|---|---|
| TREATMENT_COMPARISON.md | 10,827字节 | 治疗对比分析 |
| INFORMED_CHOICE_GUIDE.md | 13,709字节 | 知情选择指南 |
| SAFE_COMMUNITY_GUIDE.md | 11,444字节 | 社区建设指南 |
| task-summary_2026-05-13_v19.md | 本文件 | 任务总结 |

---

## 八、下一步建议

1. **制作图表**：将对比表制作成可视化图片
2. **翻译传播**：翻译成英文，扩大影响
3. **收集案例**：收集更多匿名患者故事
4. **建立社区**：按照指南建立安全社区
5. **持续更新**：根据反馈完善文档

---

> **"知情选择是患者的权利，信息透明是医疗的底线。"**

> **"能帮一些人就帮一些人。"**
> 
> **"救一个人，胜造七级浮屠。"**

---

*本文遵循开放、透明、非商业原则。*
*欢迎转载，请注明出处。*
