scj009999/TLSR8269_SixChannel_Pulse_Generator/firmware/main_master_v3.c

/**
 * @file main_master_v3.c
 * @brief TLSR8269 六通道脉冲治疗仪 - 整合主程序
 * @details 整合I2C/PWM/ADC/LCD/按键驱动，完整治疗流程
 * @author 束长江
 * @version 3.0.0
 * @date 2026-05-24
 */

#include <stdint.h>
#include <stdbool.h>
#include <string.h>
#include <stdio.h>
#include "tlsr8269_reg.h"
#include "i2c_driver.h"
#include "pwm_driver.h"
#include "adc_driver.h"
#include "lcd_driver.h"
#include "button_driver.h"
#include "button_defs.h"
#include "irq_wrapper.h"
#include "stubs.h"
#include "ui_manager.h"
#include "timer_driver.h"

/* ============================================================
 * 版本信息
 * ============================================================ */
#define FIRMWARE_VERSION    "3.0.0"
#define FIRMWARE_DATE       "2026-05-24"
#define HARDWARE_VERSION    "v3.0"

/* ============================================================
 * 系统配置
 * ============================================================ */
#define SYSTEM_TICK_MS      1       // 系统tick周期 1ms
#define BUTTON_SCAN_MS      10      // 按键扫描间隔
#define ADC_SCAN_MS         100     // ADC扫描间隔
#define UI_REFRESH_MS       100     // UI刷新间隔
#define SAFETY_CHECK_MS     50      // 安全检查间隔
#define WATCHDOG_TIMEOUT_MS 1000    // 看门狗超时

/* ============================================================
 * 治疗参数默认值
 * ============================================================ */
#define THERAPY_FREQ_DEFAULT_HZ     10.0f   // 默认频率 10Hz
#define THERAPY_DUTY_DEFAULT        5000    // 默认占空比 50.00%
#define THERAPY_DURATION_DEFAULT_S  1200    // 默认时长 20分钟
#define THERAPY_CURRENT_LIMIT_MA    20      // 电流限制 20mA

/* ============================================================
 * 系统状态
 * ============================================================ */
typedef enum {
    SYS_STATE_INIT = 0,         // 初始化
    SYS_STATE_SELF_TEST,        // 自检
    SYS_STATE_STANDBY,          // 待机
    SYS_STATE_CONFIG,           // 配置
    SYS_STATE_READY,            // 就绪
    SYS_STATE_THERAPY,          // 治疗中
    SYS_STATE_PAUSED,           // 暂停
    SYS_STATE_FAULT,            // 故障
    SYS_STATE_EMERGENCY         // 急停
} System_StateTypeDef;

/* ============================================================
 * 治疗配置
 * ============================================================ */
typedef struct {
    float frequency_hz;         // 频率(Hz)
    uint16_t duty;              // 占空比(0-10000)
    uint16_t duration_s;        // 时长(秒)
    uint8_t active_channels;    // 活动通道位图
    bool impedance_check;       // 是否启用阻抗检测
} Therapy_ConfigTypeDef;

/* ============================================================
 * 治疗状态
 * ============================================================ */
typedef struct {
    uint32_t elapsed_ms;        // 已运行时间(ms)
    uint32_t remaining_ms;      // 剩余时间(ms)
    uint32_t pulse_count;       // 脉冲计数
    float current_ma[6];        // 各通道电流
    uint16_t impedance_ohm[6];  // 各通道阻抗
    bool electrode_ok[6];       // 电极状态
} Therapy_StatusTypeDef;

/* ============================================================
 * 全局变量
 * ============================================================ */
static System_StateTypeDef system_state = SYS_STATE_INIT;
static Therapy_ConfigTypeDef therapy_config;
static Therapy_StatusTypeDef therapy_status;
static uint32_t system_tick_ms = 0;
static uint32_t last_button_scan = 0;
static uint32_t last_adc_scan = 0;
static uint32_t last_ui_refresh = 0;
static uint32_t last_safety_check = 0;
static bool emergency_triggered = false;

/* ============================================================
 * 函数声明
 * ============================================================ */
static void system_init(void);
static void system_self_test(void);
static void system_tick_handler(void);
static void button_event_handler(uint8_t id, Button_EventTypeDef event);
static void pwm_fault_handler(uint8_t ch, PWM_FaultTypeDef fault);
static void adc_safety_handler(uint8_t ch, uint8_t type, float value);
static void therapy_start(void);
static void therapy_stop(void);
static void therapy_pause(void);
static void therapy_resume(void);
static void safety_check(void);
static void update_therapy_status(void);
static void enter_emergency_state(void);
static void exit_emergency_state(void);

/* ============================================================
 * 系统初始化
 * ============================================================ */
static void system_init(void)
{
    // 关闭中断
    irq_disable();
    
    // 初始化系统时钟（48MHz）
    // TODO: 配置时钟树
    
    // 初始化I2C（400kHz，用于OLED和INA219）
    if (!i2c_init(I2C_FREQ_400K, 100)) {
        // I2C初始化失败，记录错误
        system_state = SYS_STATE_FAULT;
        return;
    }
    
    // 初始化LCD
    if (!lcd_init()) {
        // LCD初始化失败，尝试继续（非关键）
    }
    
    // 显示启动画面
    lcd_clear();
    lcd_draw_string(0, 0, "Pulse Therapy", true);
    lcd_draw_string(0, 16, "Initializing...", true);
    lcd_refresh();
    
    // 初始化PWM（6通道）
    if (!pwm_init()) {
        lcd_draw_string(0, 32, "PWM Init Failed!", true);
        lcd_refresh();
        system_state = SYS_STATE_FAULT;
        return;
    }
    
    // 设置PWM故障回调
    pwm_set_fault_callback(pwm_fault_handler);
    
    // 初始化ADC
    if (!adc_init()) {
        lcd_draw_string(0, 32, "ADC Init Failed!", true);
        lcd_refresh();
        system_state = SYS_STATE_FAULT;
        return;
    }
    
    // 配置ADC通道
    // CH0-CH1: 电流检测（INA219通过I2C，这里预留ADC）
    // CH2: 电位器输入
    // CH3-CH5: 阻抗检测
    adc_setup_potentiometer(2);  // PB2 = 电位器
    
    // 设置ADC安全回调
    adc_set_safety_callback(adc_safety_handler);
    
    // 初始化按键
    button_init();
    button_init_default_layout();
    button_set_callback(button_event_handler);
    
    // 初始化UI
    ui_init();
    
    // 初始化治疗配置（默认值）
    therapy_config.frequency_hz = THERAPY_FREQ_DEFAULT_HZ;
    therapy_config.duty = THERAPY_DUTY_DEFAULT;
    therapy_config.duration_s = THERAPY_DURATION_DEFAULT_S;
    therapy_config.active_channels = 0x3F;  // 6通道全启用
    therapy_config.impedance_check = true;
    
    // 清除治疗状态
    memset(&therapy_status, 0, sizeof(therapy_status));
    
    // 显示版本信息
    lcd_clear();
    lcd_draw_string(0, 0, "Pulse Therapy", true);
    lcd_draw_string(0, 16, "Version 3.0.0", true);
    lcd_draw_string(0, 32, "HW: v3.0", true);
    lcd_draw_string(0, 48, "Press OK to start", true);
    lcd_refresh();
    
    // 进入待机状态
    system_state = SYS_STATE_STANDBY;
    
    // 启用中断
    irq_enable();
}

/* ============================================================
 * 系统自检
 * ============================================================ */
static void system_self_test(void)
{
    system_state = SYS_STATE_SELF_TEST;
    
    lcd_clear();
    lcd_draw_string(0, 0, "Self Test...", true);
    lcd_refresh();
    
    bool test_pass = true;
    
    // 测试1: I2C总线扫描
    lcd_draw_string(0, 16, "I2C Scan...", true);
    lcd_refresh();
    
    uint8_t i2c_devices[16];
    uint8_t dev_count = i2c_scan(i2c_devices);
    if (dev_count == 0) {
        lcd_draw_string(80, 16, "FAIL", true);
        test_pass = false;
    } else {
        lcd_draw_string(80, 16, "PASS", true);
    }
    lcd_refresh();
    
    // 测试2: PWM输出测试（低占空比，不产生实际刺激）
    lcd_draw_string(0, 24, "PWM Test...", true);
    lcd_refresh();
    
    // 配置所有通道为1Hz，1%占空比（安全）
    for (uint8_t ch = 0; ch < 6; ch++) {
        pwm_setup(ch, 1.0f, 100, false);  // 1Hz, 1%, 不启动
    }
    lcd_draw_string(80, 24, "PASS", true);
    lcd_refresh();
    
    // 测试3: ADC采样测试
    lcd_draw_string(0, 32, "ADC Test...", true);
    lcd_refresh();
    
    ADC_SampleTypeDef sample = adc_sample(2);  // 电位器通道
    if (sample.valid) {
        lcd_draw_string(80, 32, "PASS", true);
    } else {
        lcd_draw_string(80, 32, "FAIL", true);
        test_pass = false;
    }
    lcd_refresh();
    
    // 测试4: 按键测试（提示用户按键）
    lcd_draw_string(0, 40, "Button Test", true);
    lcd_draw_string(0, 48, "Press any key...", true);
    lcd_refresh();
    
    // 等待按键（简化：直接通过）
    lcd_draw_string(80, 40, "PASS", true);
    lcd_refresh();
    
    // 显示结果
    delay_ms(500);
    lcd_clear();
    if (test_pass) {
        lcd_draw_string(0, 0, "Self Test PASSED", true);
        system_state = SYS_STATE_STANDBY;
    } else {
        lcd_draw_string(0, 0, "Self Test FAILED", true);
        lcd_draw_string(0, 16, "Check hardware!", true);
        system_state = SYS_STATE_FAULT;
    }
    lcd_draw_string(0, 48, "Press OK", true);
    lcd_refresh();
}

/* ============================================================
 * 系统Tick处理（1ms中断）
 * ============================================================ */
static void system_tick_handler(void)
{
    system_tick_ms++;
    
    // 按键扫描（每10ms）
    if (system_tick_ms - last_button_scan >= BUTTON_SCAN_MS) {
        last_button_scan = system_tick_ms;
        button_scan();
    }
    
    // ADC扫描（每100ms）
    if (system_tick_ms - last_adc_scan >= ADC_SCAN_MS) {
        last_adc_scan = system_tick_ms;
        adc_scan_handler();
        
        // 如果在治疗中，更新状态
        if (system_state == SYS_STATE_THERAPY) {
            update_therapy_status();
        }
    }
    
    // UI刷新（每100ms）
    if (system_tick_ms - last_ui_refresh >= UI_REFRESH_MS) {
        last_ui_refresh = system_tick_ms;
        ui_process();
    }
    
    // 安全检查（每50ms）
    if (system_tick_ms - last_safety_check >= SAFETY_CHECK_MS) {
        last_safety_check = system_tick_ms;
        if (system_state == SYS_STATE_THERAPY) {
            safety_check();
        }
    }
    
    // 看门狗喂狗
    // TODO: 实现看门狗
}

/* ============================================================
 * 按键事件处理
 * ============================================================ */
static void button_event_handler(uint8_t id, Button_EventTypeDef event)
{
    switch (system_state) {
        case SYS_STATE_STANDBY:
            if (id == BTN_OK && event == BUTTON_EVENT_SHORT_PRESS) {
                // 进入配置界面
                system_state = SYS_STATE_CONFIG;
                ui_set_mode(UI_MODE_MENU);
            } else if (id == BTN_START && event == BUTTON_EVENT_SHORT_PRESS) {
                // 快速开始（使用默认参数）
                therapy_start();
            }
            break;
            
        case SYS_STATE_CONFIG:
            // 配置界面的按键处理由UI管理器处理
            ui_handle_button(id, event);
            
            if (ui_get_mode() == UI_MODE_RUNNING) {
                // 用户确认开始治疗
                therapy_start();
            }
            break;
            
        case SYS_STATE_READY:
            if (id == BTN_START && event == BUTTON_EVENT_SHORT_PRESS) {
                therapy_start();
            } else if (id == BTN_CANCEL && event == BUTTON_EVENT_SHORT_PRESS) {
                system_state = SYS_STATE_STANDBY;
                ui_set_mode(UI_MODE_MAIN);
            }
            break;
            
        case SYS_STATE_THERAPY:
            if (id == BTN_STOP || (id == BTN_START && event == BUTTON_EVENT_LONG_PRESS)) {
                // 停止或长按START = 急停
                enter_emergency_state();
            } else if (id == BTN_CANCEL && event == BUTTON_EVENT_SHORT_PRESS) {
                therapy_pause();
            }
            break;
            
        case SYS_STATE_PAUSED:
            if (id == BTN_START && event == BUTTON_EVENT_SHORT_PRESS) {
                therapy_resume();
            } else if (id == BTN_STOP) {
                therapy_stop();
            }
            break;
            
        case SYS_STATE_FAULT:
            if (id == BTN_OK && event == BUTTON_EVENT_SHORT_PRESS) {
                // 尝试恢复
                system_self_test();
            }
            break;
            
        case SYS_STATE_EMERGENCY:
            if (id == BTN_OK && event == BUTTON_EVENT_LONG_PRESS) {
                // 长按OK解除急停
                exit_emergency_state();
            }
            break;
            
        default:
            break;
    }
}

/* ============================================================
 * PWM故障处理
 * ============================================================ */
static void pwm_fault_handler(uint8_t ch, PWM_FaultTypeDef fault)
{
    // 记录故障
    therapy_status.electrode_ok[ch] = false;
    
    // 显示故障信息
    lcd_clear();
    lcd_draw_string(0, 0, "PWM FAULT!", true);
    
    char buf[32];
    snprintf(buf, sizeof(buf), "CH%d: ", ch);
    switch (fault) {
        case PWM_FAULT_OVERCURRENT:
            strcat(buf, "Overcurrent");
            break;
        case PWM_FAULT_OPEN circuit:
            strcat(buf, "Open Circuit");
            break;
        case PWM_FAULT_SHORT:
            strcat(buf, "Short");
            break;
        case PWM_FAULT_OVERVOLTAGE:
            strcat(buf, "Overvoltage");
            break;
        default:
            strcat(buf, "Unknown");
            break;
    }
    lcd_draw_string(0, 16, buf, true);
    lcd_refresh();
    
    // 进入故障状态
    if (system_state == SYS_STATE_THERAPY) {
        therapy_pause();
        system_state = SYS_STATE_FAULT;
    }
}

/* ============================================================
 * ADC安全处理
 * ============================================================ */
static void adc_safety_handler(uint8_t ch, uint8_t type, float value)
{
    char buf[32];
    
    switch (type) {
        case 1:  // 过流
            snprintf(buf, sizeof(buf), "CH%d Overcurrent: %.1fmA", ch, value);
            lcd_draw_string(0, 32, buf, true);
            enter_emergency_state();
            break;
            
        case 2:  // 开路
            snprintf(buf, sizeof(buf), "CH%d Open Circuit", ch);
            lcd_draw_string(0, 32, buf, true);
            therapy_status.electrode_ok[ch] = false;
            break;
            
        case 3:  // 短路
            snprintf(buf, sizeof(buf), "CH%d Short Circuit", ch);
            lcd_draw_string(0, 32, buf, true);
            enter_emergency_state();
            break;
    }
    
    lcd_refresh();
}

/* ============================================================
 * 治疗控制
 * ============================================================ */
static void therapy_start(void)
{
    // 检查电极接触
    if (therapy_config.impedance_check) {
        bool all_ok = true;
        for (uint8_t ch = 0; ch < 6; ch++) {
            if (therapy_config.active_channels & (1 << ch)) {
                if (!adc_check_electrode(ch)) {
                    therapy_status.electrode_ok[ch] = false;
                    all_ok = false;
                } else {
                    therapy_status.electrode_ok[ch] = true;
                }
            }
        }
        
        if (!all_ok) {
            lcd_clear();
            lcd_draw_string(0, 0, "Electrode Error!", true);
            lcd_draw_string(0, 16, "Check connections", true);
            lcd_refresh();
            system_state = SYS_STATE_FAULT;
            return;
        }
    }
    
    // 配置PWM通道
    for (uint8_t ch = 0; ch < 6; ch++) {
        if (therapy_config.active_channels & (1 << ch)) {
            pwm_setup(ch, therapy_config.frequency_hz, therapy_config.duty, true);
        }
    }
    
    // 初始化治疗状态
    therapy_status.elapsed_ms = 0;
    therapy_status.remaining_ms = therapy_config.duration_s * 1000;
    therapy_status.pulse_count = 0;
    
    // 进入治疗状态
    system_state = SYS_STATE_THERAPY;
    ui_set_mode(UI_MODE_RUNNING);
    
    // 显示开始信息
    lcd_clear();
    lcd_draw_string(0, 0, "Therapy Started", true);
    char buf[32];
    snprintf(buf, sizeof(buf), "Freq: %.1fHz", therapy_config.frequency_hz);
    lcd_draw_string(0, 16, buf, true);
    snprintf(buf, sizeof(buf), "Duration: %ds", therapy_config.duration_s);
    lcd_draw_string(0, 24, buf, true);
    lcd_refresh();
}

static void therapy_stop(void)
{
    // 停止所有PWM
    pwm_stop_all();
    
    // 清除状态
    memset(&therapy_status, 0, sizeof(therapy_status));
    
    // 进入待机
    system_state = SYS_STATE_STANDBY;
    ui_set_mode(UI_MODE_MAIN);
    
    lcd_clear();
    lcd_draw_string(0, 0, "Therapy Stopped", true);
    lcd_refresh();
}

static void therapy_pause(void)
{
    // 暂停PWM
    pwm_pause_all();
    
    system_state = SYS_STATE_PAUSED;
    ui_set_mode(UI_MODE_MAIN);
    
    lcd_clear();
    lcd_draw_string(0, 0, "Therapy Paused", true);
    lcd_draw_string(0, 16, "Press START to resume", true);
    lcd_refresh();
}

static void therapy_resume(void)
{
    // 恢复PWM
    pwm_resume_all();
    
    system_state = SYS_STATE_THERAPY;
    ui_set_mode(UI_MODE_RUNNING);
    
    lcd_clear();
    lcd_draw_string(0, 0, "Therapy Resumed", true);
    lcd_refresh();
}

/* ============================================================
 * 安全检查
 * ============================================================ */
static void safety_check(void)
{
    // 检查各通道电流
    for (uint8_t ch = 0; ch < 6; ch++) {
        if (therapy_config.active_channels & (1 << ch)) {
            float current = pwm_read_current(ch);
            
            if (current > THERAPY_CURRENT_LIMIT_MA) {
                // 过流，急停
                enter_emergency_state();
                return;
            }
            
            therapy_status.current_ma[ch] = current;
        }
    }
    
    // 检查电极阻抗
    if (therapy_config.impedance_check) {
        for (uint8_t ch = 0; ch < 6; ch++) {
            if (therapy_config.active_channels & (1 << ch)) {
                uint16_t impedance = pwm_read_impedance(ch);
                therapy_status.impedance_ohm[ch] = impedance;
                
                if (impedance > ADC_IMPEDANCE_MAX_OHM || 
                    (impedance > 0 && impedance < ADC_IMPEDANCE_MIN_OHM)) {
                    // 电极接触不良
                    therapy_status.electrode_ok[ch] = false;
                    
                    // 暂停该通道
                    pwm_stop_channel(ch);
                    
                    // 如果所有通道都故障，暂停治疗
                    bool any_active = false;
                    for (uint8_t i = 0; i < 6; i++) {
                        if (therapy_config.active_channels & (1 << i)) {
                            const PWM_ChannelStatusTypeDef *status = pwm_get_channel_status(i);
                            if (status && status->state == PWM_STATE_RUNNING) {
                                any_active = true;
                                break;
                            }
                        }
                    }
                    
                    if (!any_active) {
                        therapy_pause();
                        lcd_draw_string(0, 40, "Electrode off!", true);
                        lcd_refresh();
                    }
                }
            }
        }
    }
    
    // 检查治疗时间
    if (therapy_status.remaining_ms <= 0) {
        // 治疗完成
        therapy_stop();
        lcd_clear();
        lcd_draw_string(0, 0, "Therapy Complete!", true);
        lcd_refresh();
    }
}

/* ============================================================
 * 更新治疗状态
 * ============================================================ */
static void update_therapy_status(void)
{
    therapy_status.elapsed_ms += ADC_SCAN_MS;
    if (therapy_status.remaining_ms >= ADC_SCAN_MS) {
        therapy_status.remaining_ms -= ADC_SCAN_MS;
    } else {
        therapy_status.remaining_ms = 0;
    }
    
    // 更新脉冲计数
    uint32_t total_pulses = 0;
    for (uint8_t ch = 0; ch < 6; ch++) {
        const PWM_ChannelStatusTypeDef *status = pwm_get_channel_status(ch);
        if (status) {
            total_pulses += status->pulse_count;
        }
    }
    therapy_status.pulse_count = total_pulses;
    
    // 更新UI
    ui_update_therapy_progress(
        therapy_status.elapsed_ms / 1000,
        therapy_config.duration_s,
        therapy_status.remaining_ms / 1000
    );
}

/* ============================================================
 * 急停处理
 * ============================================================ */
static void enter_emergency_state(void)
{
    // 立即执行硬件急停
    pwm_emergency_stop();
    
    // 设置状态
    system_state = SYS_STATE_EMERGENCY;
    emergency_triggered = true;
    
    // 显示急停信息
    lcd_clear();
    lcd_draw_string(0, 0, "!!! EMERGENCY !!!", true);
    lcd_draw_string(0, 16, "All outputs OFF", true);
    lcd_draw_string(0, 32, "Long press OK", true);
    lcd_draw_string(0, 40, "to reset", true);
    lcd_refresh();
    
    // 记录急停事件（用于医疗记录）
    // TODO: 记录到Flash或发送日志
}

static void exit_emergency_state(void)
{
    // 清除急停
    pwm_clear_emergency();
    emergency_triggered = false;
    
    // 返回待机
    system_state = SYS_STATE_STANDBY;
    ui_set_mode(UI_MODE_MAIN);
    
    lcd_clear();
    lcd_draw_string(0, 0, "Emergency Cleared", true);
    lcd_draw_string(0, 16, "Press START", true);
    lcd_refresh();
}

/* ============================================================
 * 主函数
 * ============================================================ */
int main(void)
{
    // 系统初始化
    system_init();
    
    // 如果初始化失败，进入故障状态
    if (system_state == SYS_STATE_FAULT) {
        while (1) {
            // 故障状态，等待复位
            button_scan();
            delay_ms(10);
        }
    }
    
    // 执行自检
    system_self_test();
    
    // 主循环
    while (1) {
        // 系统tick处理（实际应由定时器中断触发）
        system_tick_handler();
        
        // 主循环延时（1ms）
        delay_ms(1);
        
        // 看门狗喂狗
        // TODO: 喂狗
    }
    
    return 0;
}

/* ============================================================
 * 中断服务程序
 * ============================================================ */

// 定时器中断（1ms）
void timer_irq_handler(void)
{
    // 清除中断标志
    // TODO: 清除定时器中断标志
    
    // 调用tick处理
    system_tick_handler();
}

// PWM中断
void pwm_isr_handler(void)
{
    pwm_irq_handler();
}
