scj009999/TLSR8269_SixChannel_Pulse_Generator/firmware/button_defs.h

/**
 * @file button_defs.h
 * @brief 按键别名定义（兼容main_master_v3.c）
 */

#ifndef __BUTTON_DEFS_H__
#define __BUTTON_DEFS_H__

#include "button_driver.h"

// 按键别名（用于main_master_v3.c）
#define BTN_OK          BUTTON_OK_PIN
#define BTN_START       BUTTON_START_PIN
#define BTN_CANCEL      BUTTON_CANCEL_PIN
#define BTN_STOP        BUTTON_STOP_PIN
#define BTN_UP          BUTTON_UP_PIN
#define BTN_DOWN        BUTTON_DOWN_PIN

#endif /* __BUTTON_DEFS_H__ */
